ciaa/Ponchos/Osciloscopio/doc/PonchoOsciloscopio_CESE_NicolasDassieuBlanchet.odt

Curso de Diseño de PCBs - CESE

Hoja de presentación de proyecto

Nombre corto del proyecto:

Poncho Osciloscopio para la EDU-CIAA

Autor:

Nicolás Dassieu Blanchet

Licencia:

BSD

Repositorio de trabajo:

https://github.com/brengi/Ponchos.git

Rama de trabajo:

ponchoOsciloscopio

Descripción:

Este circuito implementa un poncho para la EDU-CIAA que le agrega la posibilidad de adquirir un canal de osciloscopio, con escala seleccionable, opción acoplamiento en AC y DC y con cierto nivel de protección sobre las entradas analogicas de la EDU-CIAA.

Requisitos del profesor:

Colocar los requisitos acordados con el profesor. Por ejemplo funciones mínimas, número de capas, tipo de fabricación, tipo de componentes y tecnología de montaje, circuitos de referencia charlados en clase, etc.

Requisitos comunes a todos:

- Utilizar Kicad 4.0.x.
- Consolidar toda la documentación en forma organizada dentro del directorio de proyecto de KiCad.
- Aplicar una licencia o aclarar el Copyright.
- Considerar en cada caso, los aspectos vistos referente a documentación.
- Realizar diseño jerárquico salvo en circuitos muy pequeños.
- Siempre que sea posible, considerar para los diseños componentes que se consigan en el mercado local.
- Se utilizará como proveedor de referencia a Mayer.
- Indicar que tipo/calidad de placa se considera para el diseño, intentando siempre que sea posible, seleccionar la de menor costo.
- Componentes through hole o SMD??? Si se pueden conseguir aca SMD sino Trough Hole
- Dos Layers??? 2
- Dispay??? Serie I2C o SPI
- Boton selección de escala??? Si por serigrafia que diga escala.
- Tamaño Vias, minimas pistas??? Ver especificaiones Mayer

Tareas y Alcance:

Indicar hasta donde se pretende llegar con el diseño y que tareas involucra. Por ejemplo:

- Búsqueda de esquemáticos de referencia. (Obligatorio)
- Adaptaciones de esquemático.
- Ingreso de esquemático a Kicad. (Obligatorio)
- Revisión del esquemático por un tercero. (Obligatorio)
- Cálculo de presupuesto y proveedores de componentes. (Obligatorio)
- Selección de footprints. (Obligatorio)
- Ubicación de componentes.
- Ruteo.
- Generación de Gerbers. (Depende lo acordado)
- Fabricación de prototipo. (Depende lo acordado)
- Validación funcional. (Depende lo acordado)

Enlaces:

Enlace original del que parte la idea de realizar el osciloscopio:

https://github.com/marvin-sinister/small-scope-electronics

Enlaces con circuitos más completos

http://tomeko.net/miniscope_v2b/

http://www.osciprime.com/index.php?p=source

Imágenes:

Colocar imágenes ilustrativas, por ejemplo diseño o estado actual, producto similar o a copiar, etc.
