ciaa/Ponchos/Expansor_puertos/Docs/Revisiones/Revisiones(DB).odt

Segunda Revisión (Revisor: Diego Brengi)

| Orlante Mariano
| mariano.orlante@gmail.com
| Expansor puertos
| https://marianoo2001@gitlab.com/marianoo2001/EduCiaaPE.git
| Segunda 25/7/17
Docente | Diego Brengi
Archivo hoja de proyecto en /doc | OK
Archivos de revisiones en /doc | OK
Revisor designado | OK
Bibliotecas | OK
Rótulo | OK
Jerarquía | OK
Campos KiCost | OK
Prolijidad conexiones | OK
Referencias de tensión | OK
Comentarios
ERC | OK
Configuración bibliotecas huellas | ok
Notas en PCB: Grila pos, ruteo. Pista min, Vía min, aguj. min, capas, terminación superficial. | OK
Rótulo | OK
Encapsulados | OK
Borde del PCB | OK
Ancho de pistas | OK
Tamaño de vía | OK
DRC | OK
Ruteo | Prolijo
| Bien aprovechadas las simetrías de los buses.
Fiduciales | OK
Placement | Muy bien
Serigrafía | Se podrían poner textos adicionales que ayuden a identificar los textos de las borneras, por ejemplo J3.1 J3.2 y así.
Textos en cobre o en serigrafía, logos | Sería bueno agregarle INDUSTRIA ARGENTINA en el cobre.
Dimensiones | OK
Fijación | OK
Belleza/Alineación | OK
Vista 3D | OK
Areas de cobre | Bien. Se podrían delimitar las áreas por fuera del borde para que no se superpongan al borde y entre sí. Es solamente una cuestión visual y de facilidad para el diseñador y el programa de CAD. Ver como ejemplo https://raw.githubusercontent.com/OLIMEX/OLINUXINO/master/HARDWARE/A64-OLinuXino/A64-OLinuXino_Rev_C/A64-OlinuXino_Rev_C.kicad_pcb Y habilitar la visualización de todas las capas para ilustrar el concepto de zonas de relleno por fuera del PCB.

Acciones Correctivas:

| Acción Correctiva
Serigrafía | - Se agregaron textos identificatorios de las borneras. Ademas de las respectivas J1, J2, J3, etc., se identificaron las entradas (INxx) y las salidas (OUTxx) en la capa F. Silk.
Textos en cobre o en serigrafía, logos | - Se agregó en la capa Bottom la leyenda INDUSTRIA ARGENTINA.
Areas de cobre | Se extendieron las areas de cobre por fuera del borde de la placa.

Primera Revision (Revisor: Diego Brengi)

NOMBRE | | Orlante Mariano
EMAIL | | mariano.orlante@gmail.com
PROYECTO | | Expansor puertos
REPO | | https://marianoo2001@gitlab.com/marianoo2001/EduCiaaPE.git
CORRECCION (Fecha) | | Primera 30/06/17
Curso CESE - PCB | Docente | Diego Brengi
Documentación | Archivo hoja de proyecto en /doc | FALTA
| Archivos de revisiones en /doc | Colocar esta revisión en el directorio doc.
| Revisor designado | OK
Esquematico | Bibliotecas | OK
| Rótulo | OK
| Jerarquía | OK
| Campos KiCost | OK
| Prolijidad conexiones | Estan muy prolijas. En las hojas de entrada y salidas se podría quitar las etiquetas locales, ya que unos pocos cruces no molestan a la claridad del circuito. Esta muy bien de todas formas como fue resuelto.
| Referencias | OK
| Comentarios
| ERC | OK
Asociación | Configuración bibliotecas huellas | ok
PCB | Notas en PCB: Grila pos, ruteo. Pista min, Vía min, aguj. min, capas, terminación superficial. | Faltan
| Rótulo | Debe ser similar al del esquemático.
| Encapsulados | OK
| Borde del PCB | OK
| Ancho de pistas
| DRC
| Ruteo
| Fiduciales | Si hay espacio se recomiendan por lo menos 3 fiduciales.
| Placement | Se recomienda trabajar un poco más la ubicación antes de rutear, para evitarse complicaciones luego. Ver la guía para posicionamiento. Se nota que ya hay trabajo hecho.
| Serigrafía
| Textos en cobre o en serigrafía, logos
| Dimensiones
| Fijación
| Belleza/Alineación
| Vista 3D | OK
| Areas de cobre

Acciones Correctivas:

| | Acción Correctiva
Documentación | Archivo hoja de proyecto en /doc | - Se agregó el archivo "ProyectoPCB_CESE_ORLANTE.odt" a la carpeta /Docs del proyecto.
| Archivos de revisiones en /doc | - Se agregó el documento "Revisiones(DB).odt" a la carpeta /Docs del proyecto.
Esquematico | Prolijidad conexiones | En el esquemático de entradas digitales: - Se quitaron las etiquetas locales CLK_INH, S//L, CLK reemplazandolas por cables. En el esquemático de salidas digitales: - Se quitó la etiqueta /CS en el esquematico de salidas digitales. - Se decidió dejar las etiquetas OUTxx y la COMUN porque aportan claridad al esquematico, identificando las borneras.
PCB | Notas en PCB: Grila pos, ruteo. Pista min, Vía min, aguj. min, capas, terminación superficial. | Se agregó esto en el PCB.
| Rótulo | Se cargó el rótulo similar al esquemático.
| Fiduciales | Se agregó un tercer fiducial.
| Placement | Se itero varias veces hasta obtener un posicionamiento que requeria poco uso de vias.
