ciaa/Ponchos/WifiBT_CESE_ESPWROOM32/doc/Primera_Revision_Esquematico.pdf

### Primera Revisión

Revisor: Diego Brengi

Fecha: 30/06/2017

NOMBRE | | Coccé Gastón
EMAIL | | gastoncocce@hotmail.com
PROYECTO | | Poncho Wifi y Bluetooth
REPO | | https://github.com/gcocce/poncho_EDU-CIAA_wifi_blth
CORRECCION
(Fecha)
Curso CESE - PCB | Docente | Diego Brengi

Documentación

Archivo hoja de proyecto en

Archivos de revisiones en

/doc | FALTA
/doc | Colocar esta revisión en el direcotrio doc.
Revisor
| QUITAR TODAS una vez que se han agregado todos los componentes.
designado | Debe figurar en el rótulo.
Esquematico | Bibliotecas
Rótulo | Mencionar la asignatura. Mencionar al revisor.

Jerarquía
Campos
KiCost | OK.

Prolijidad
conexiones

Mejorar. Por ejemplo en el extremo de R6 falta una unión y la conexión esta sobre el pin del componente SW2. La GND de D2/D3 tiene una unión sobre el mismo pin de conexión.

Referencias | OK.
Comentarios | El power flag colocarlo en el conector.
ERC | OK

Asociación

Configuración
bibliotecas
huellas

Quitar la biblioteca Buttons. Dejar solo la que esta dentro del proyecto, que debería contener todos los footpints utilizados. Ver la opción de Archivar footprints en el pcbnew.

PCB

Notas en PCB:
Grila pos,
ruteo. Pista Falta

min, Vía min,
aguj. min,
capas,
terminación
superficial.
Rótulo | Falta. Debe estar similar al de esquemático.

Encapsulados

Los resistores1206 se usan cada vez menos y puede costar conseguirlos. Los 0402 son demasiado pequeños para manejo manual. Se recomienda unificar en 0805 que se usan mucho y se pueden soldar manualmente de ser
necesario. https://es.wikipedia.org/wiki/Tecnolog%C3%ADa_de_montaje_superficial. (https://es.wikipedia.org/wiki/Tecnolog%C3%ADa_de_montaje_superficial) Esto requerirá cambiar los códigos en el esquemático.

Borde del PCB
Ancho de
pistas

DRC

Ruteo

Fiduciales

Placement

Serigrafía

Textos en
cobre o en
serigrafía,
logos

Dimensiones

Fijación
Belleza/Alinea
ción
Vista 3D | OK
Areas de
cobre
