ciaa/Ponchos/Osciloscopio/hdatos/Display info 2.pdf

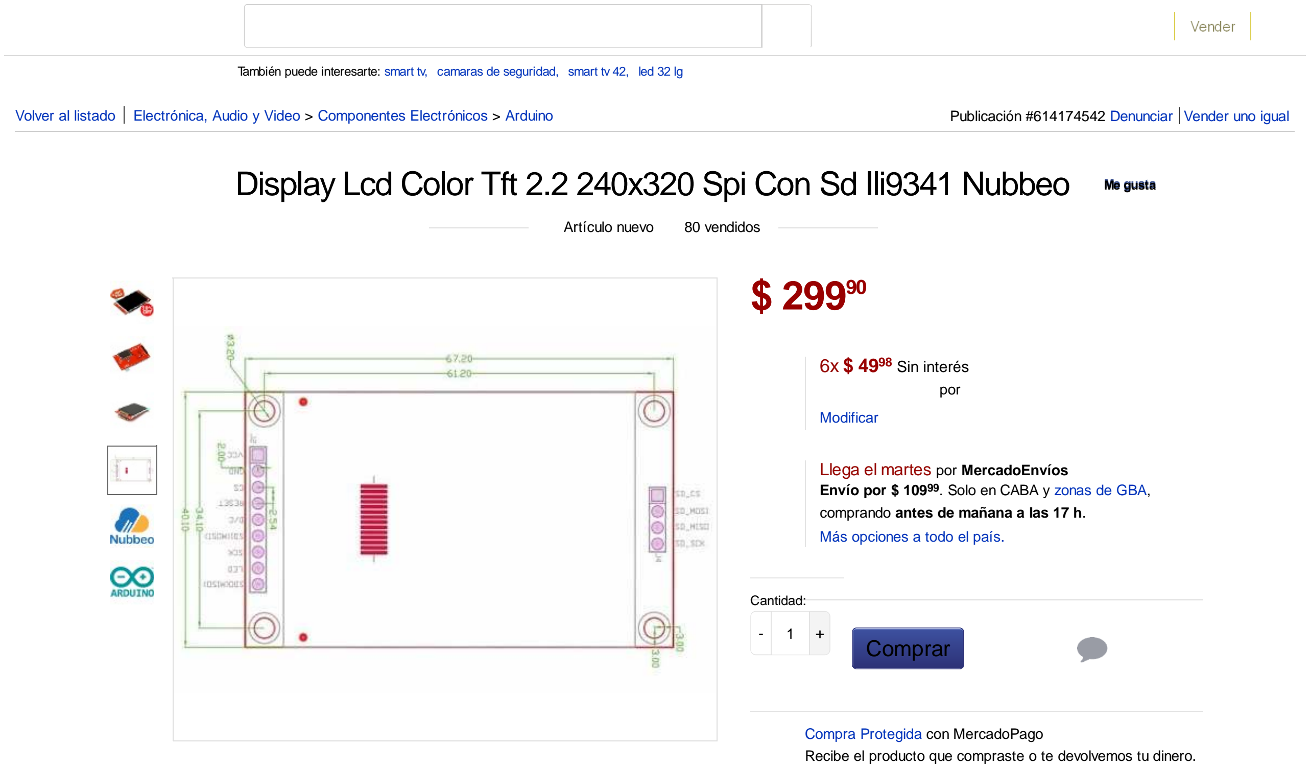
[picture p29: figure]
Cantidad:; Comprar; Compra Protegida con MercadoPago; Me gusta; Artículo nuevo; 80 vendidos; 6x $ 49⁹⁸ Sin interés; por; Modificar; Más opciones a todo el país.; Llega el martes por MercadoEnvíos; comprando antes de mañana a las 17 h.

También puede interesarte: smart tv, camaras de seguridad, smart tv 42, led 32 lg

# Display Lcd Color Tft 2.2 240x320 Spi Con Sd Ili9341 Nubbeo

Recibe el producto que compraste o te devolvemos tu dinero.

# Información sobre el vendedor

## Reputación

100% de sus compradores; lo recomiendan; 34789 ventas; concretadas; Excelente vendedor ¡Es uno de los mejores del sitio!; 3 AÑOS vendiendo en MercadoLibre; Este vendedor es MercadoLíder Platinum

Ver más datos de este vendedor

## Calificaciones 53 compradores lo recomendaron por este producto JMONF... - 08 de julio

MAIANUS201... - 22 de junio

PELIKAN... - 15 de junio

CLA... - 15 de junio

BELWA... - 11 de junio

Ver más calificaciones

# Garantía

Volver al listado | Electrónica, Audio y Video > Componentes Electrónicos > Arduino | Publicación #614174542 Denunciar | Vender uno igual

Envío por $ 109⁹⁹. Solo en CABA y zonas de GBA,

Ubicado en Villa Luro (Capital Federal)

- "Recomendado”
- "Excelente vendedor”
- "Todo perfecto. Recomendable.”
- "Si. Todo bien. Gracias!!!!!”
- "Excelente vendedor! Recomendable”

Tu compra en MercadoLibre, siempre protegida

Display Lcd Color Tft 2.2 240x320 Spi Con Sd Ili9341 Nubbeo - $ 299... http://articulo.mercadolibre.com.ar/MLA-614174542-display-lcd-color-...

1 of 6 | 10/07/2016 10:50 a.m.

## De compra

con MercadoPago

# Descripción de la publicación

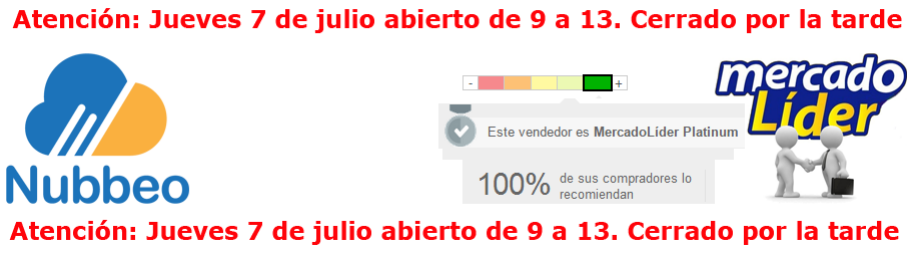
[picture p30: figure]

## Display LCD TFT de 240x320 pixels con interface SPI Incluye slot para memoria SD

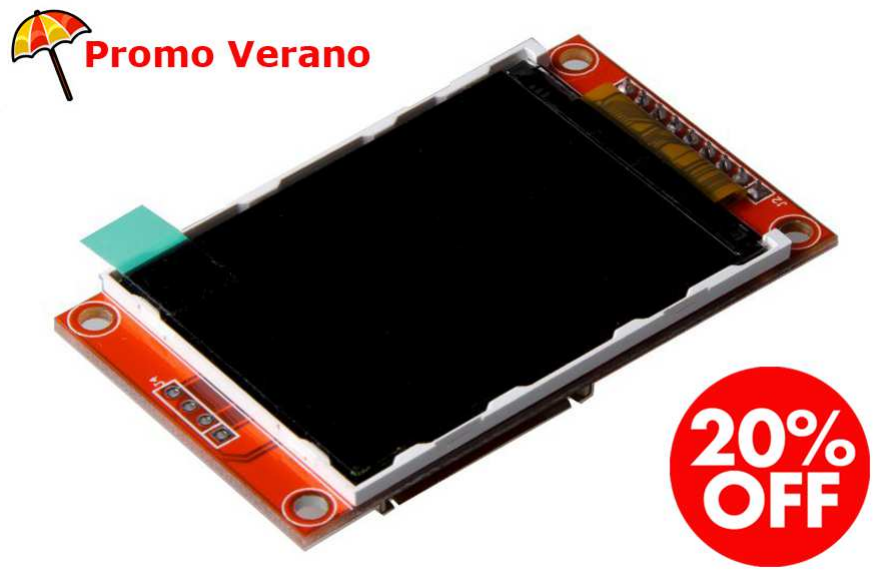
[picture p31: figure]

### Descripción General

Pantalla LCD TFT de 2.2 pulgadas con interface SPI. Excelente calidad de imagen con resolución QVGA (240 x 320 pixels). El controlador ILI9341 junto con la interface SPI (solo 4 pines) hacen que sea muy facil de usar. Adicionalmente dispone de un slot SD (independiente del LCD). Este articulo usa lógica de 3V3

## Características

### - Tamaño: 2,2 pulgadas - Alimentación: 5V - Lógica: 3V3

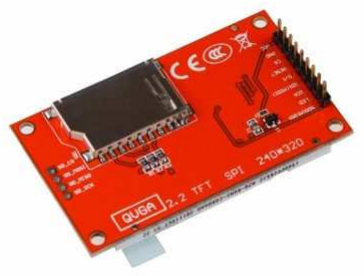
[picture p32: figure]

### - Matriz de puntos: QVGA 240 * 320 puntos - Interfaz de 4 hilos SPI - Profundidad de color: 262K/65K - Tamaño del módulo: 67 mm (longitud) * 40mm (ancho) * 4 mm (grosor)

### Compra Protegida con MercadoPago

Si surge algún problema o no recibes el producto tal como se describe en esta publicación, te devolvemos tu dinero.

Conoce más sobre Compra Protegida

### - Área activa: 47.5mm (longitud) x36.5mm (Ancho) - Driver IC: ILI9341

# Visita nuestro e-shop

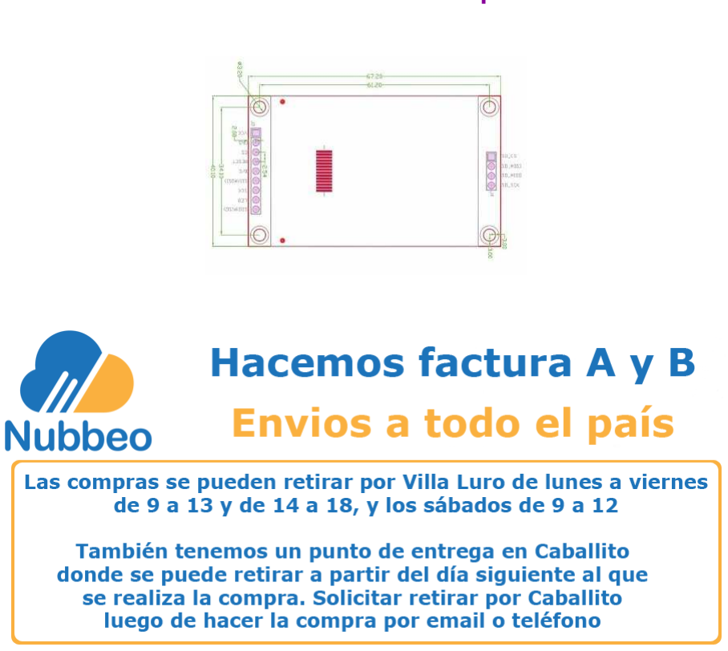
[picture p33: figure]

# Medios de pago

Formas de pago ofrecidas por el vendedor
