ciaa/Ponchos/Expansor_puertos/Docs/Notas de Ingenieria/Calculos y Estimaciones.pdf

Cálculos y estimaciones para las entradas digitales

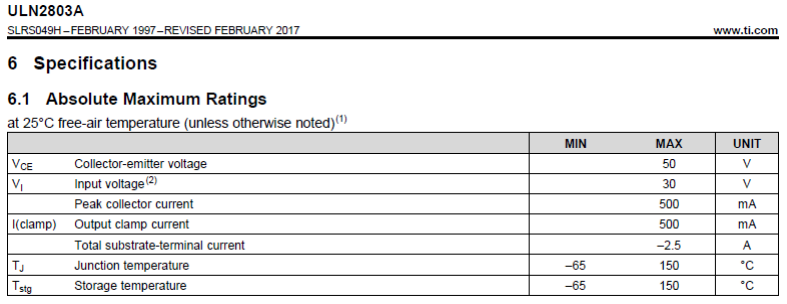
[picture p51: figure]

Según la hoja de datos del ULN2803 la máxima tensión de entrada es 30V.

Aplicando cierto margen de seguridad, se especifica para el producto como máximo una tensión de fuente de 28V DC.

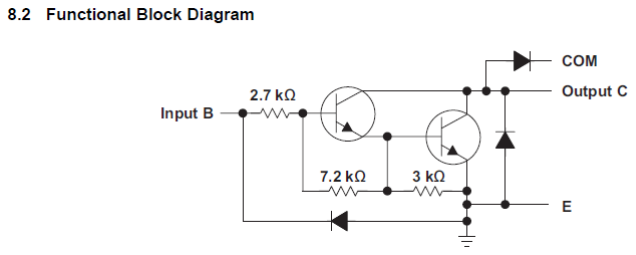
[picture p52: figure]

Ient(max) =

(28V−0.6V−0.6V)
2700Ω

→ Ient(max) ≅ 10mA

Ient(min) =

(3.5V−0.6V−0.6V)
2700Ω

→ Ient(max) ≅ 1mA

ESPECIFICACION ENTRADAS DIGITALES

Tipo de Entradas | NPN Sinking.
Rango de tensión admitida | 3.5 a 28 Volts DC (entrada activada).
Corriente que insume | 1 mA a 10 mA máximo.

Cálculos y estimaciones para las salidas digitales

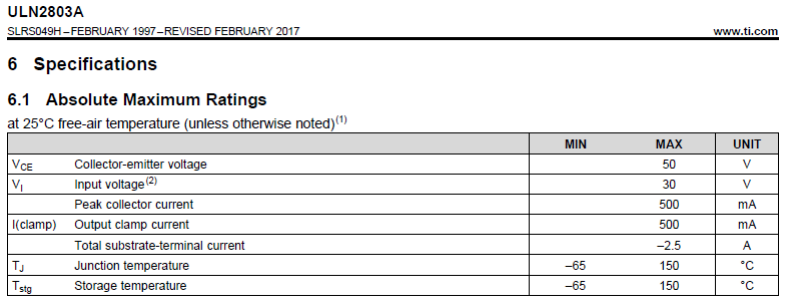
[picture p53: figure]

Según la hoja de datos del ULN2803 la máxima tensión colector-Emisor (VCE) soportada por los transistores es 50V.

Aplicando cierto margen de seguridad, se especifica para el producto como máximo una tensión de fuente externa de 45V DC.

Según la hoja de datos del ULN2803 la corriente de salida de pico máxima de un canal es 500mA. Por otro lado ESPECIFICA la “Total substrate-terminal current” = 2.5 A.

Si se activarán las 8 salidas a la vez, tendríamos:

Isalidaporcanal(max) = 2,5A/8 = 312mA

Aplicando cierto margen de seguridad, se especifica para el producto 150mA por cada salida.

ESPECIFICACION SALIDAS DIGITALES

Tipo de Salidas | NPN Sinking (colector abierto)
Tensión en la Carga | 3 a 45 Volts DC máximo
Corriente drenada | 150 mA máximo por cada salida.
