ciaa/Ponchos/Pico_WiFi/CONSIDERACIONES_INICIALES/AMADORES/Recomendaciones_assisi.pdf

# Entrega de Materiales

Recomendaciones para la entrega de materiales

Sr. Visitante, a continuación lo invitamos a conocer las necesidades de información y las recomendaciones más importantes a tener en cuenta para la conservación y entrega de los materiales.

Una vez recepcionados los mismos, podremos dar inicio al proceso interno de control, y validamiento del kit enviado para la planificación de la Orden de Trabajo.

Al planificar un lote de producción, sugerimos tener en cuenta la cantidad de placas del panelizado, ya que la cantidad del lote debería ser múltiplo de ese número.

Es imprescindible el envío de toda la información necesaria para el correcto armado del producto, la muestra física (en caso de no ser enviada anteriormente para su análisis o presupuesto), debe ser entregada acompañando a los materiales. Se recomienda enviar la demás información en formato digital vía E-mail a nuestra empresa.

- Una muestra de placa a producir armada, actualizada, preferiblemente probada y funcionando.
- Una orden de compra o producción, que indique el nombre de placa a producir, la cantidad y los datos de contacto del cliente.
Home | La Empresa | Servicios | Equipamiento
Assisi S.R.L. Armado y Soldado industrial de pl... | http://www.assisi.com.ar/presupuestos/entrega-...
1 de 5 | 11/11/16 14:01

Assisi S.R.L.
Independencia 4281 C.A.B.A. - Tel: 011-4958-5656 / 011-4983-2510 / 011-3750-1389 E-mail: info@assisi.com.ar - www.assisi.com.ar o acceda a nuestro formulario de contacto haciendo
