ciaa/Ponchos/modelos/Muestrario/doc/LEEME.txt

Autor: Diego Javier Brengi (INTI/UNLaM).

Proyecto simple para colocar todos los símbolos y huellas y visualizarlas
de un solo vistazo.
