ciaa/Ponchos/Audio_amp_mic/doc/AmpAudio.jpg

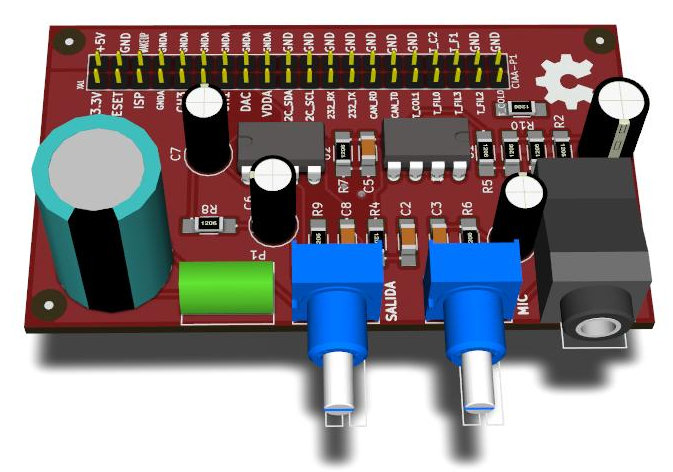
Audio_amp_mic/doc/AmpAudio.jpg
