ciaa/Ponchos/Audio_amp_mic/doc/Poncho EDU CIAA Amp Audio2.jpg

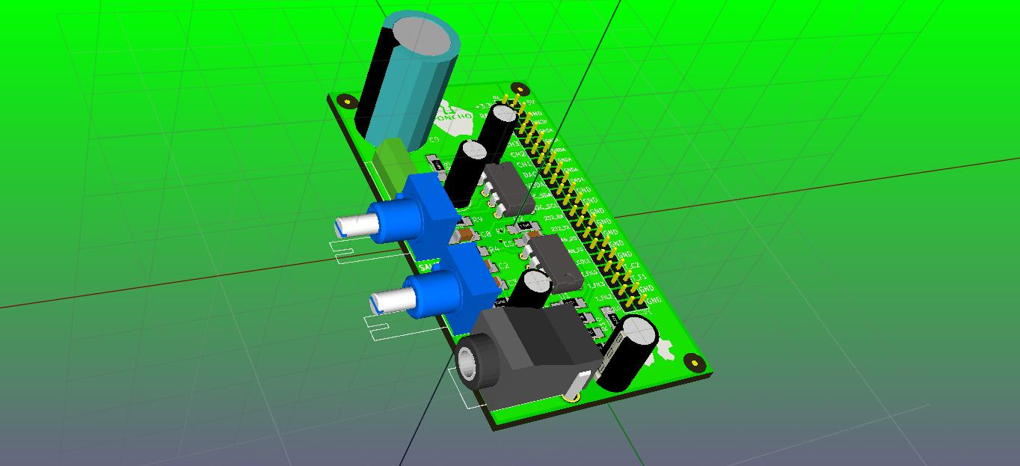
Audio_amp_mic/doc/Poncho EDU CIAA Amp Audio2.jpg
