ciaa/Ponchos/Audio_amp_mic/doc/Poncho EDU CIAA Amp Audio.jpg

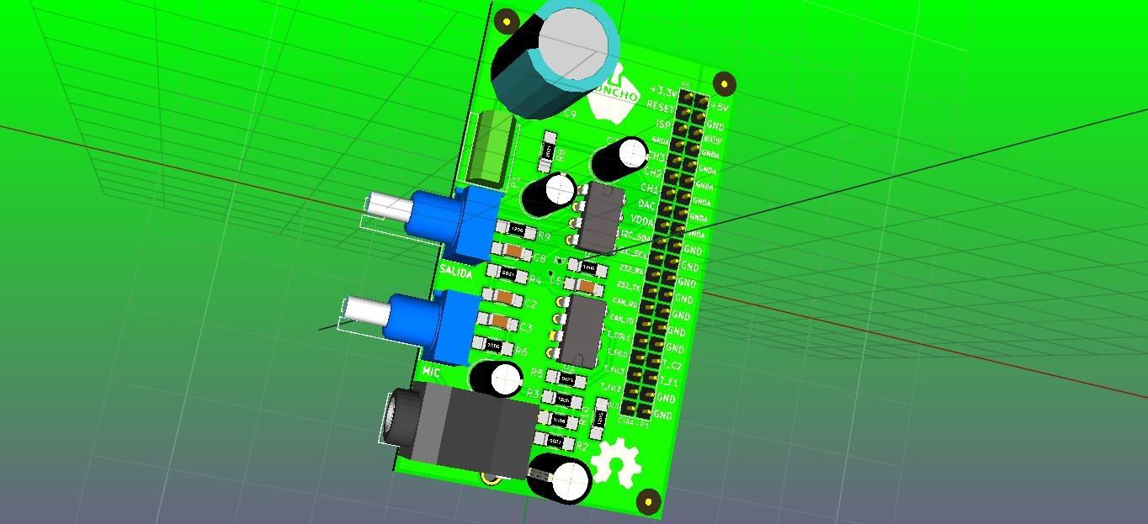
Audio_amp_mic/doc/Poncho EDU CIAA Amp Audio.jpg
