ciaa/Ponchos/Celda_de_carga/doc/poncho_celda.jpg

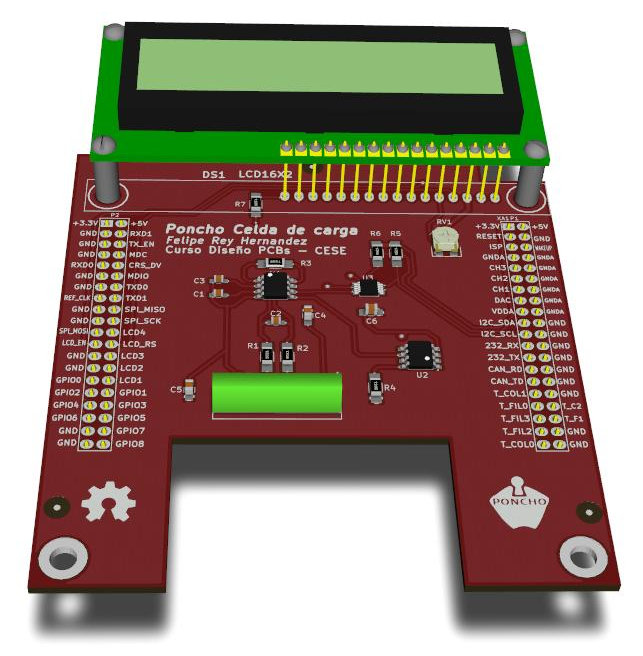
Celda_de_carga/doc/poncho_celda.jpg
