ciaa/Ponchos/Control_Temperatura/Docs/PonchoTermocuplayRele.jpg

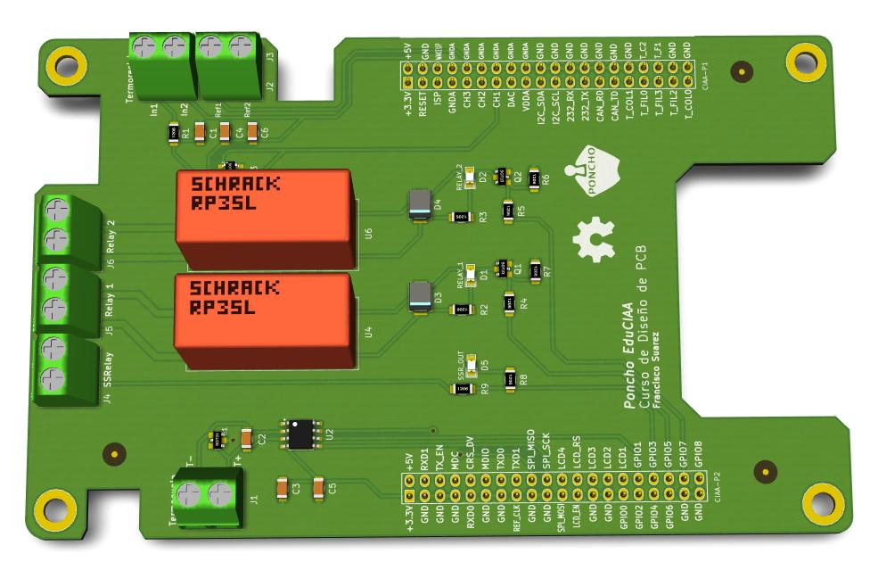
Control_Temperatura/Docs/PonchoTermocuplayRele.jpg
