ciaa/Ponchos/Control_Temperatura/Docs/tempRelayPoncho_BOTTOM.png

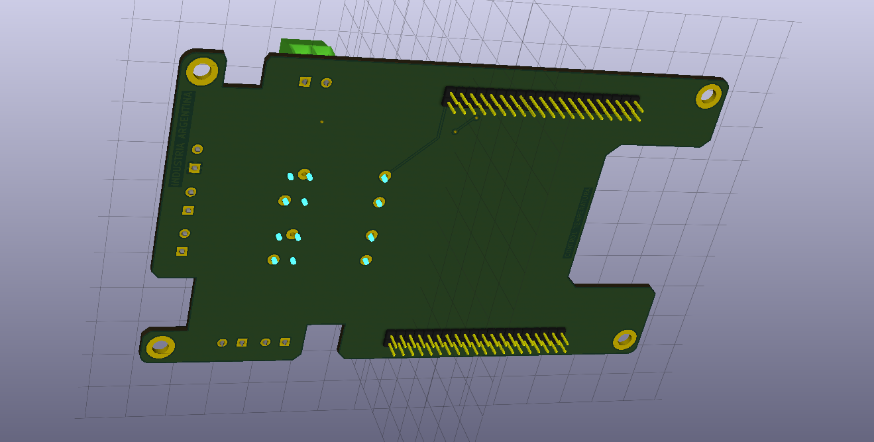
Control_Temperatura/Docs/tempRelayPoncho_BOTTOM.png
