ciaa/Ponchos/Control_Temperatura/Docs/tempRelayPoncho_TOP.png

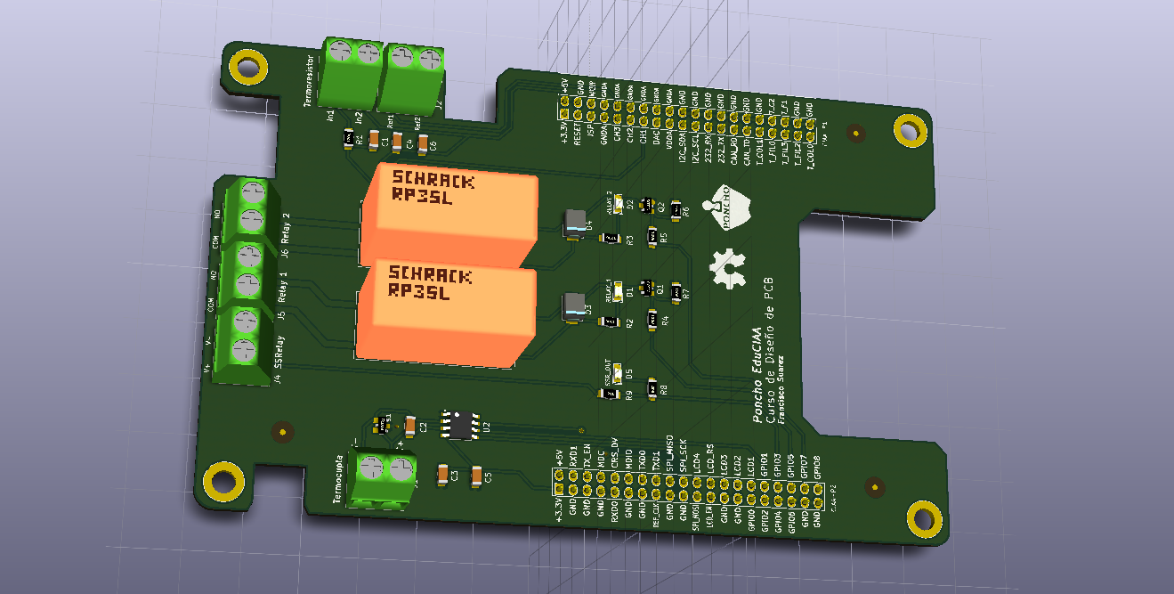
Control_Temperatura/Docs/tempRelayPoncho_TOP.png
