ciaa/Ponchos/Detector_de_caidas/doc/fall_detector.jpg

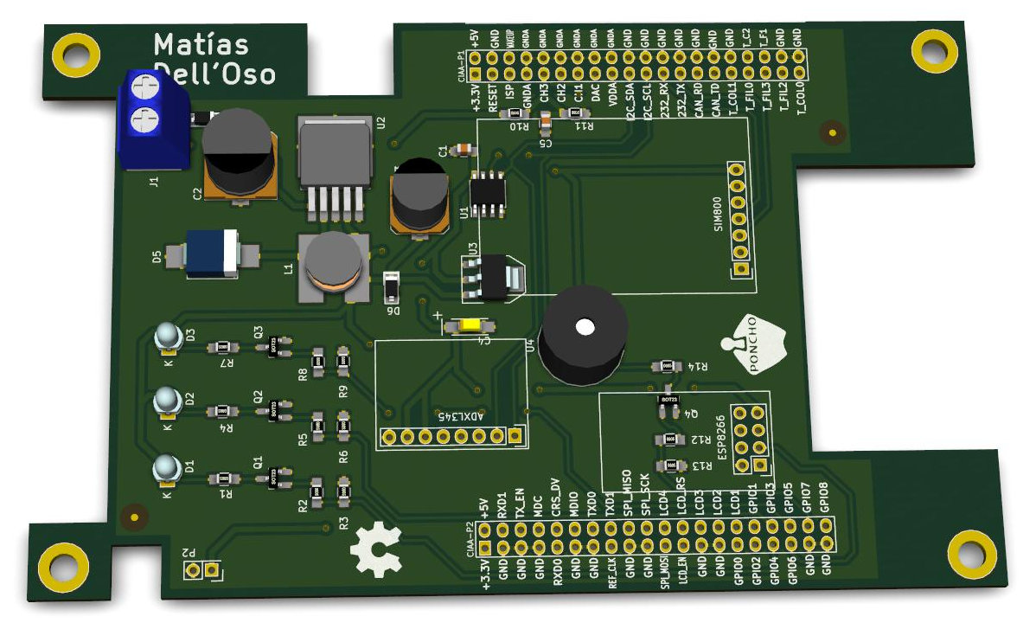
Detector_de_caidas/doc/fall_detector.jpg
