ciaa/Ponchos/doc/collage/collage_800x.jpg

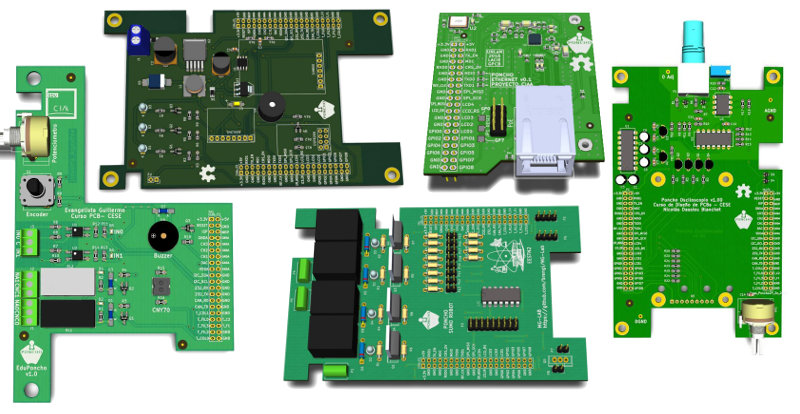
doc/collage/collage_800x.jpg
