ciaa/Ponchos/doc/collage/collageh1000x.jpg

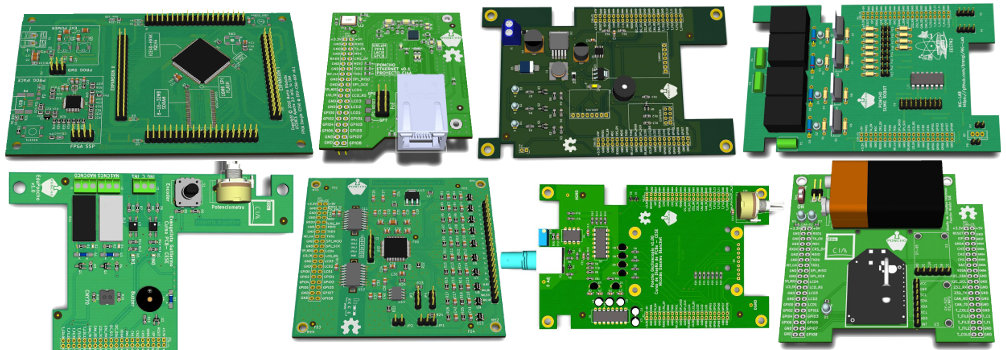
doc/collage/collageh1000x.jpg
