ciaa/Ponchos/ECG/doc/ecg.jpg

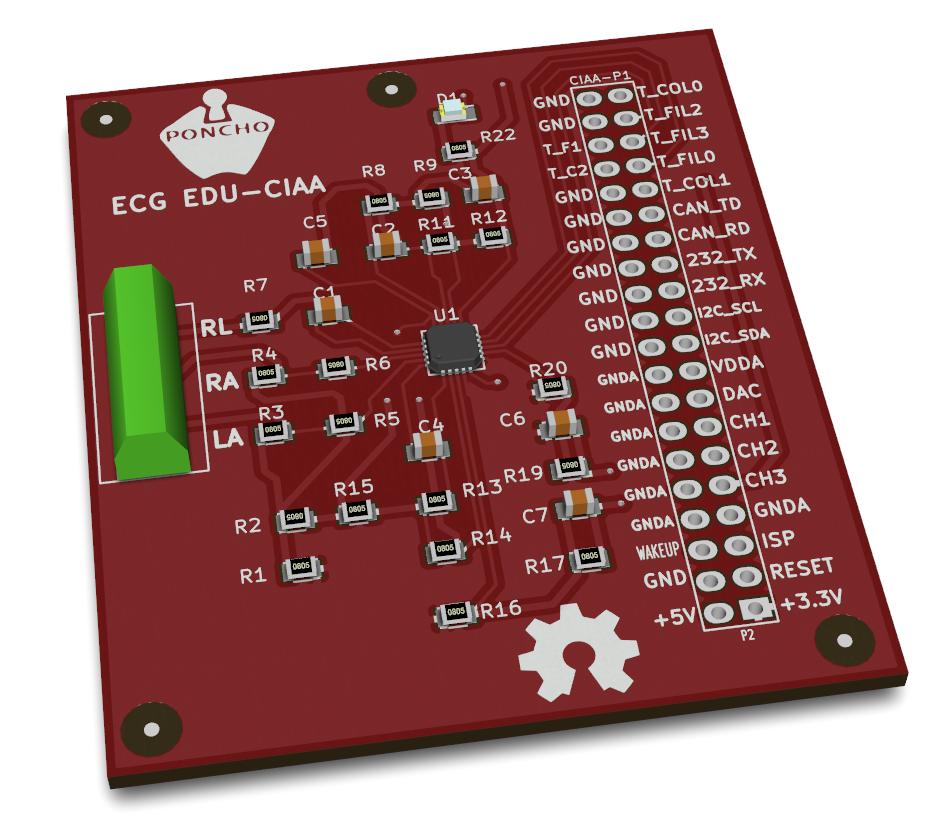
ECG/doc/ecg.jpg
