ciaa/Ponchos/ECG/ECG_CIAA.jpg

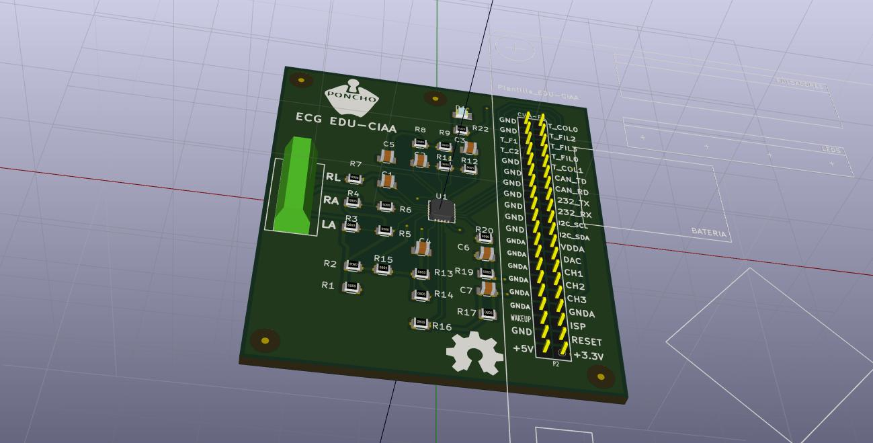
ECG/ECG_CIAA.jpg
