ciaa/Ponchos/Educativo1/doc/ponchoeducativo.jpg

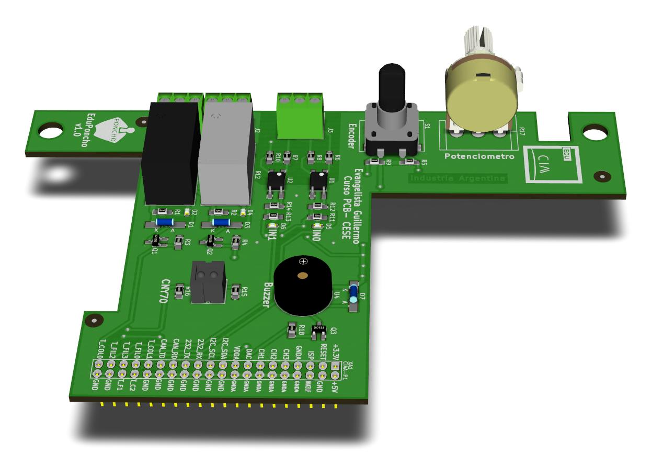
Educativo1/doc/ponchoeducativo.jpg
