ciaa/Ponchos/Educativo1/EduPoncho.png

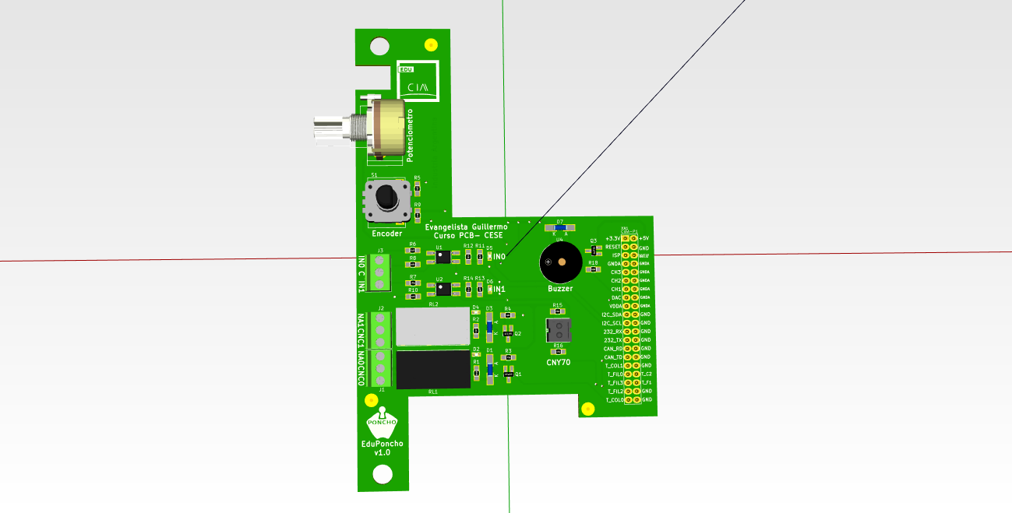
Educativo1/EduPoncho.png
