ciaa/Ponchos/Educativo_UNSJ/doc/EducativoUNSJ.jpg

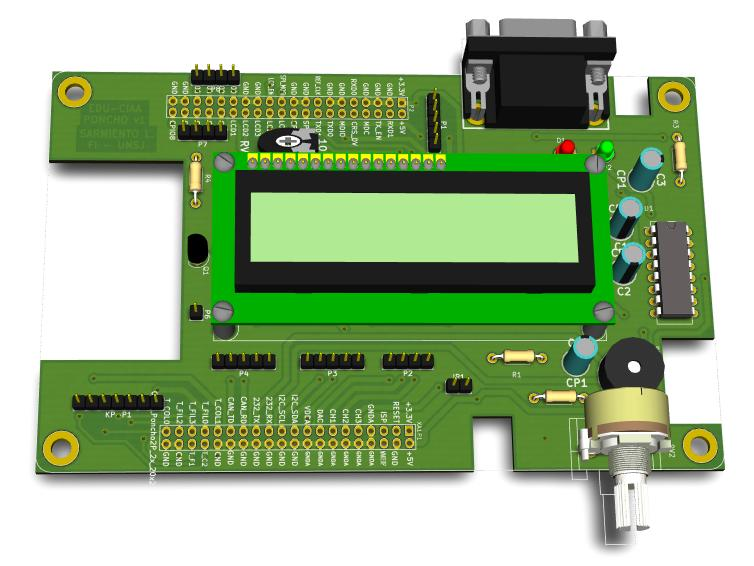
Educativo_UNSJ/doc/EducativoUNSJ.jpg
