ciaa/Ponchos/Educativo_UNSJ/doc/foto_b.jpg

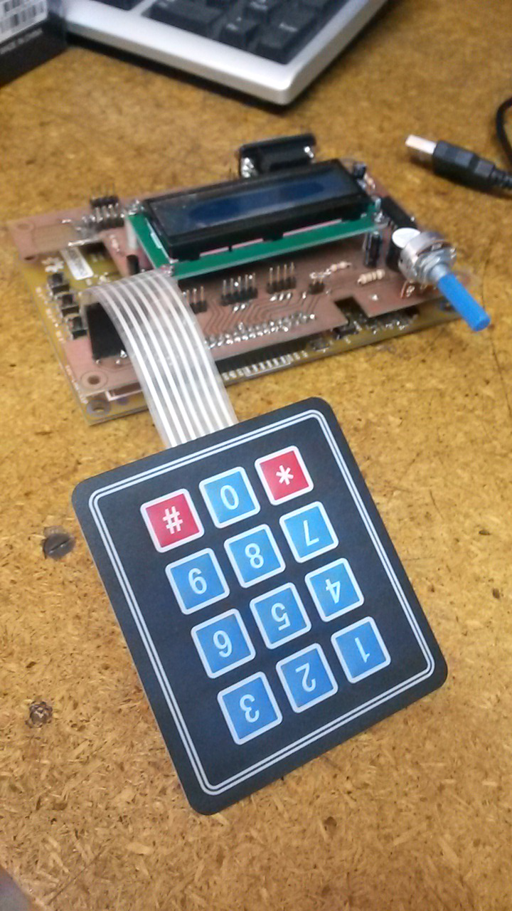
Educativo_UNSJ/doc/foto_b.jpg
