ciaa/Ponchos/ethernet_LAN8720A_v2/doc/CalculoDIF.png

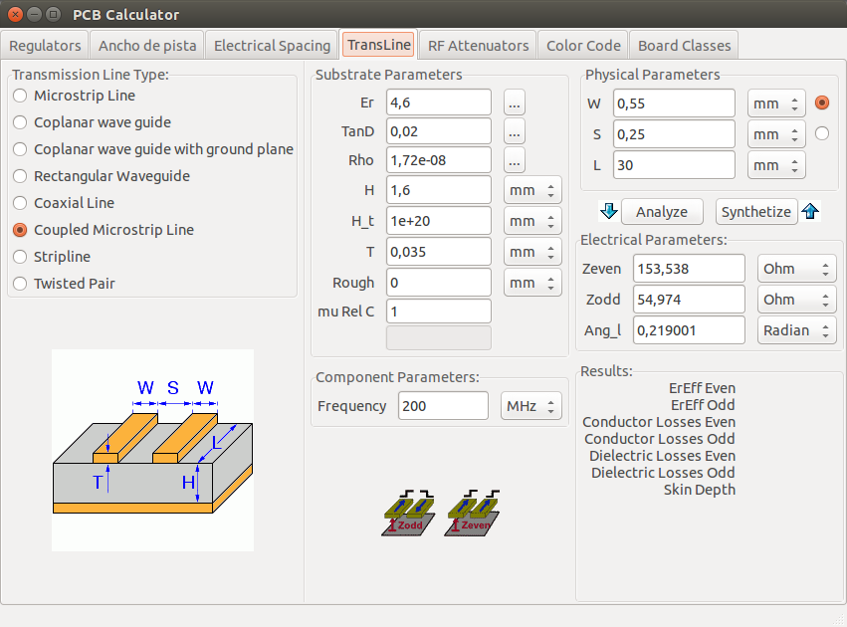
ethernet_LAN8720A_v2/doc/CalculoDIF.png
