ciaa/Ponchos/ethernet_LAN8720A_v2/doc/PonchoEthernet.jpg

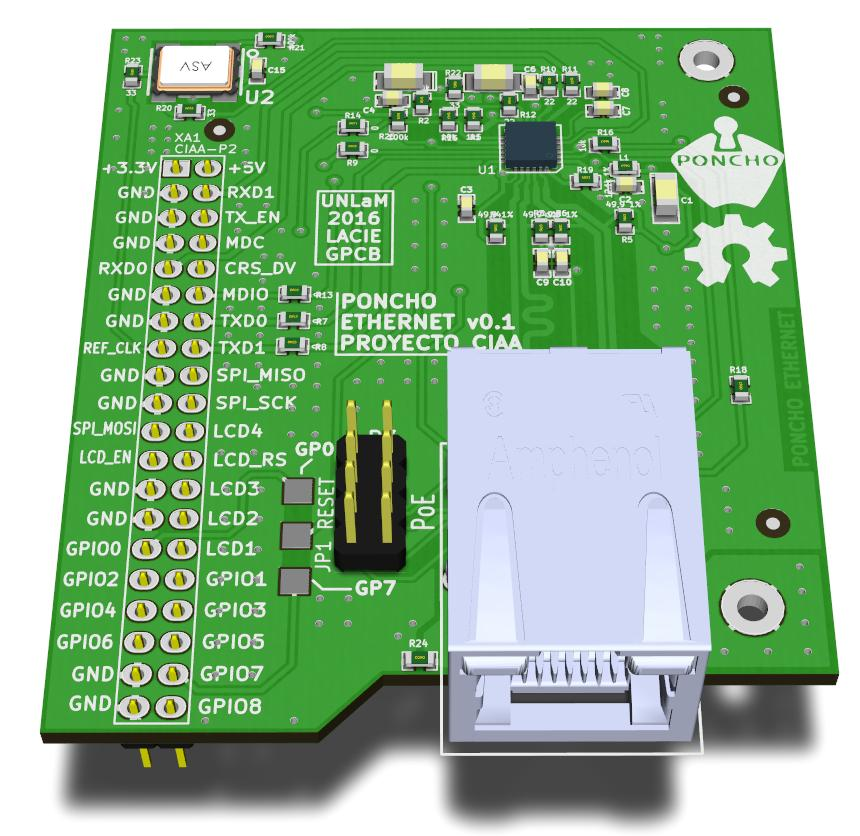
ethernet_LAN8720A_v2/doc/PonchoEthernet.jpg
