ciaa/Ponchos/Expansor_puertos/Docs/PonchoExpansorPuertos.jpg

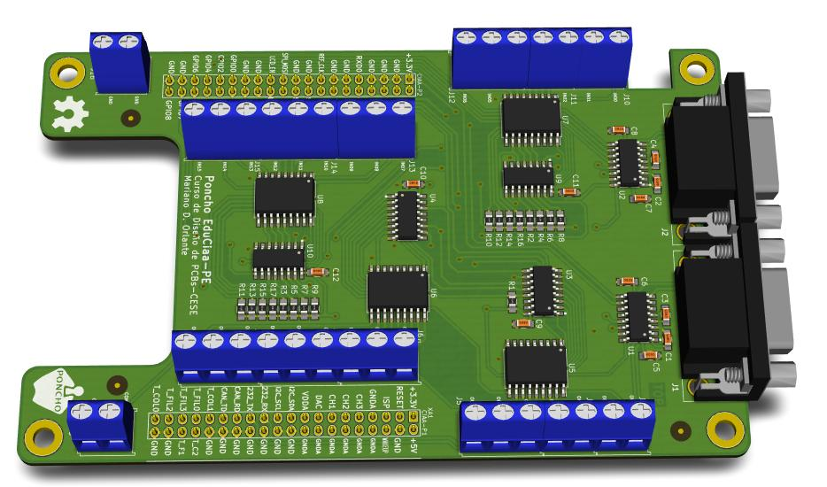
Expansor_puertos/Docs/PonchoExpansorPuertos.jpg
