ciaa/Ponchos/Expansor_puertos/Docs/Vistas 3D/EduCiaa_PE (3D Bottom View).png

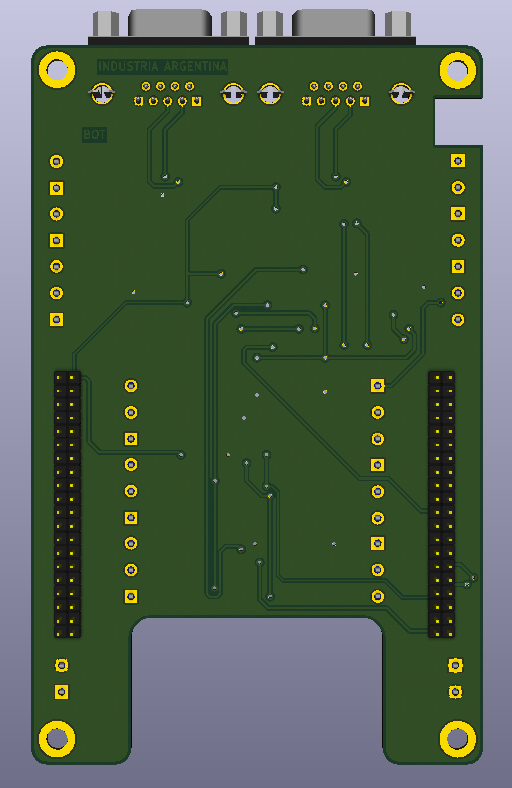
Expansor_puertos/Docs/Vistas 3D/EduCiaa_PE (3D Bottom View).png
