ciaa/Ponchos/expansores_ciaa/3x2.PNG

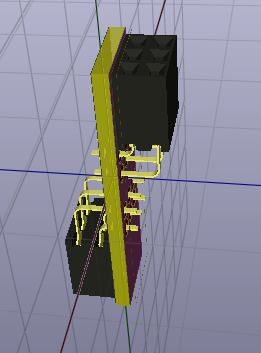
expansores_ciaa/3x2.PNG
