ciaa/Ponchos/expansores_ciaa/3x3_pcb.PNG

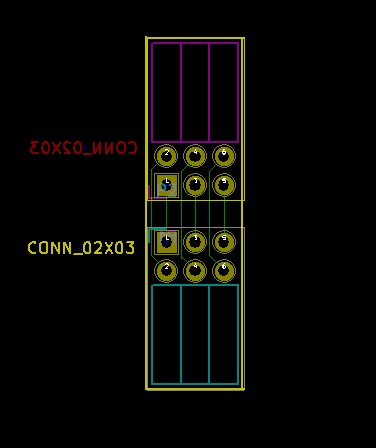
expansores_ciaa/3x3_pcb.PNG
