ciaa/Ponchos/expansores_ciaa/4x2.PNG

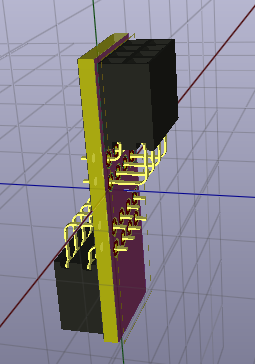
expansores_ciaa/4x2.PNG
