ciaa/Ponchos/expansores_ciaa/10x2.PNG

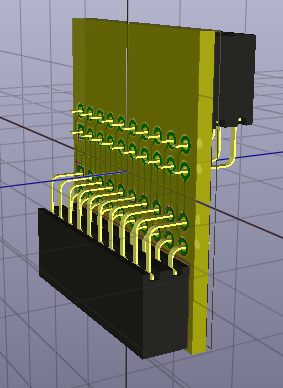
expansores_ciaa/10x2.PNG
