ciaa/Ponchos/expansores_ciaa/10x2_2.PNG

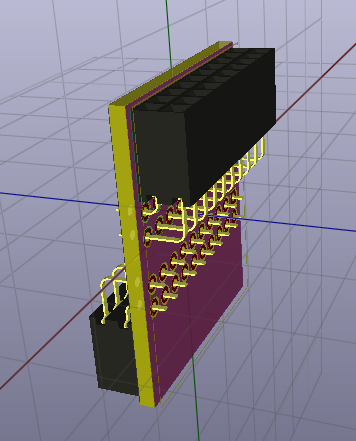
expansores_ciaa/10x2_2.PNG
