ciaa/Ponchos/expansores_ciaa/10x2_pcb.PNG

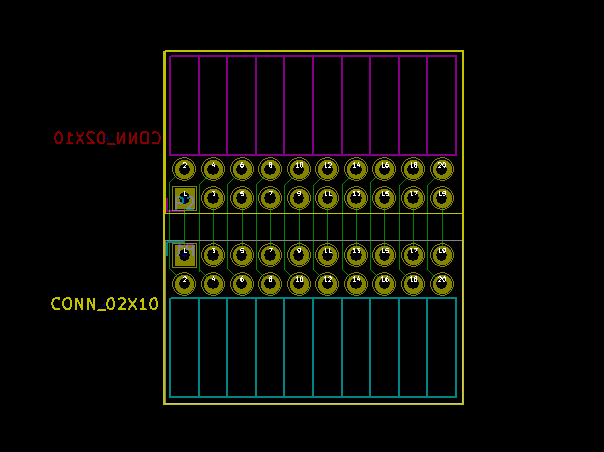
expansores_ciaa/10x2_pcb.PNG
