ciaa/Ponchos/expansores_ciaa/expansores.jpg

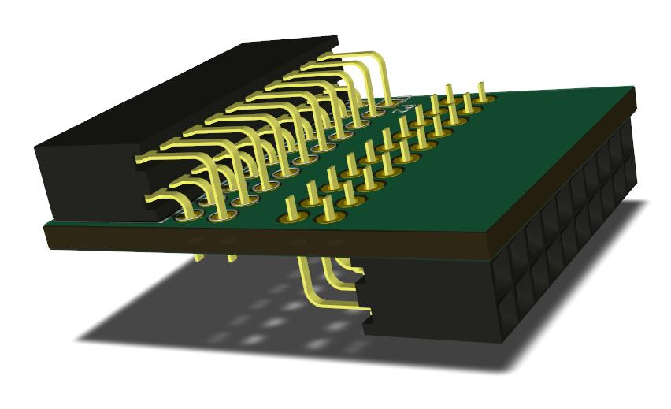
expansores_ciaa/expansores.jpg
