ciaa/Ponchos/GPS_L86/Img/GPSL86.jpg

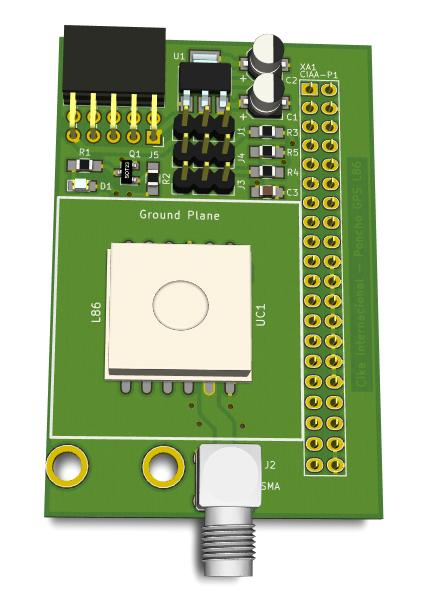
GPS_L86/Img/GPSL86.jpg
