ciaa/Ponchos/GPS_L86/Img/Poncho_L86_3.png

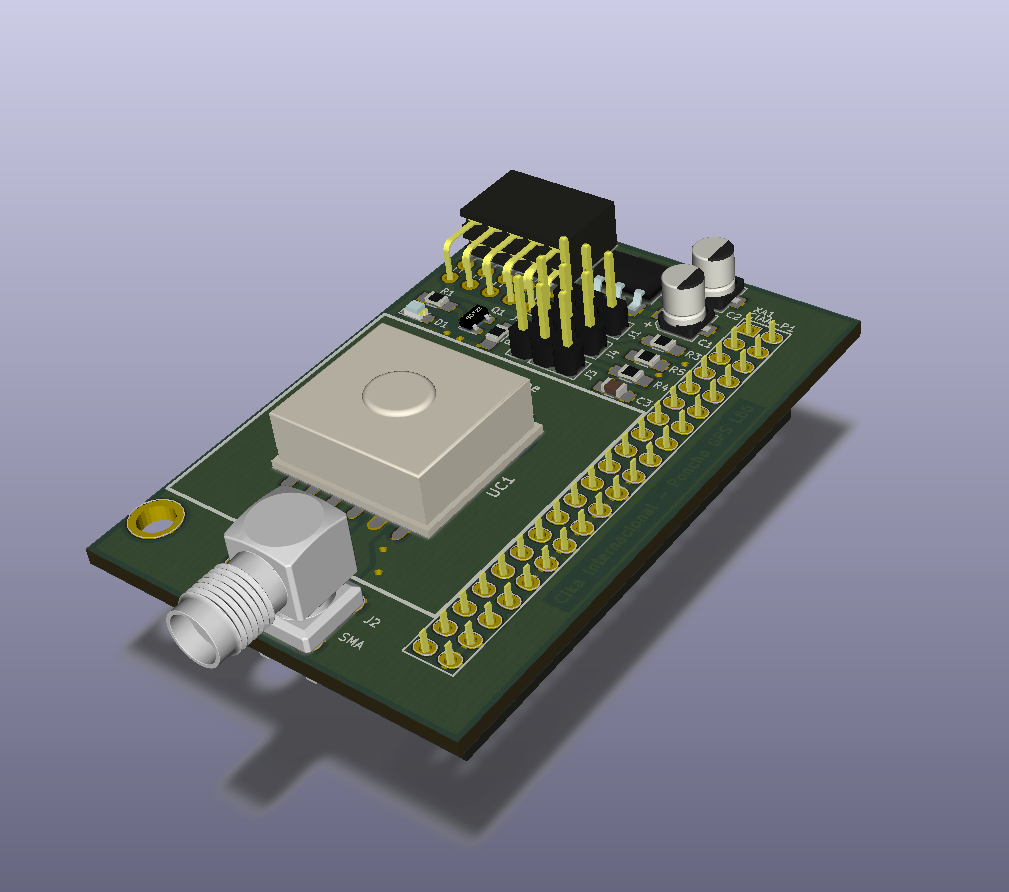
GPS_L86/Img/Poncho_L86_3.png
