ciaa/Ponchos/IoT/doc/Poncho_IoT.jpg

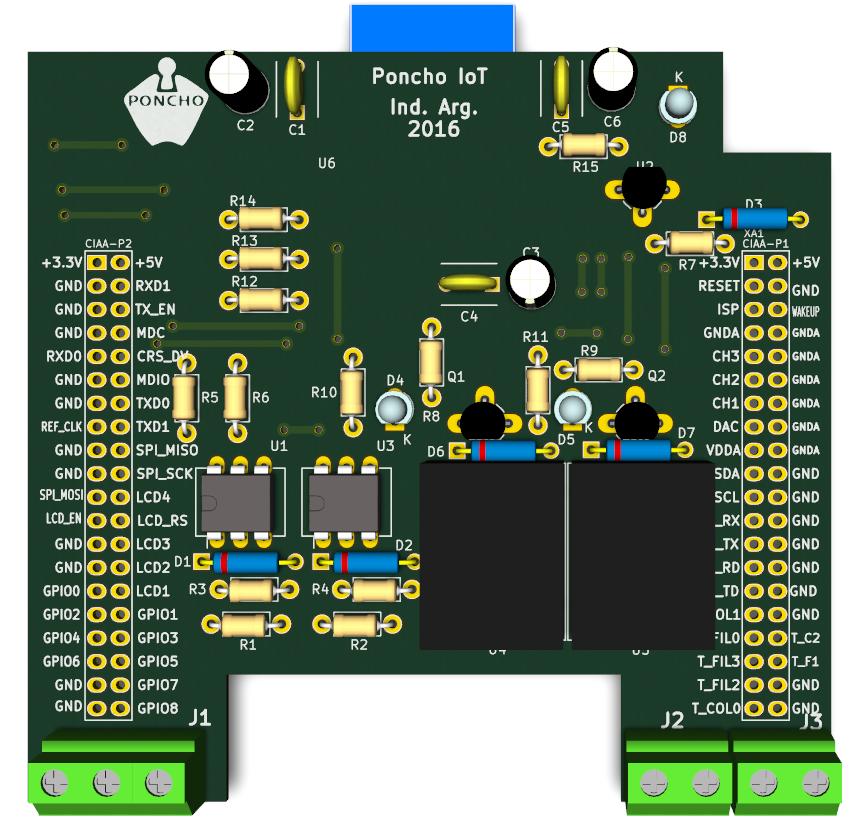
IoT/doc/Poncho_IoT.jpg
