ciaa/Ponchos/IoT/doc/ponchoeduciaaiot.png

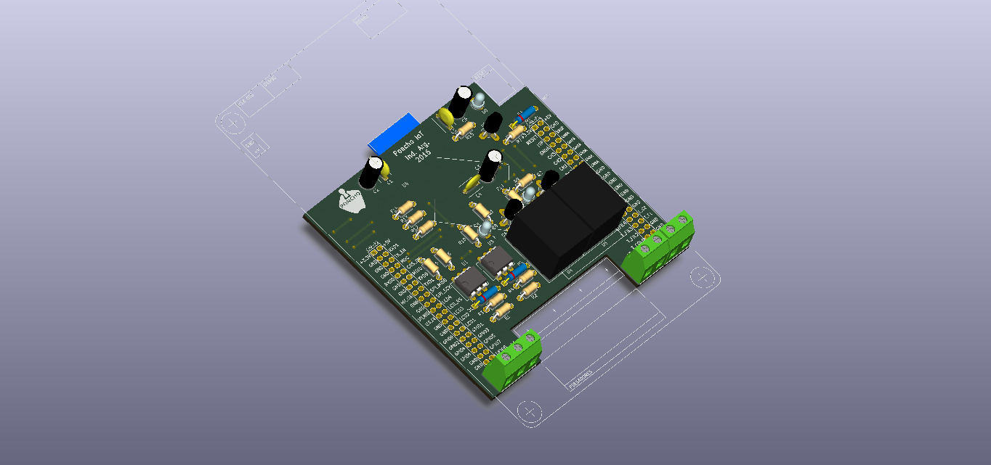
IoT/doc/ponchoeduciaaiot.png
