ciaa/Ponchos/Joystick/doc/Poncho_Joystick_dorso.png

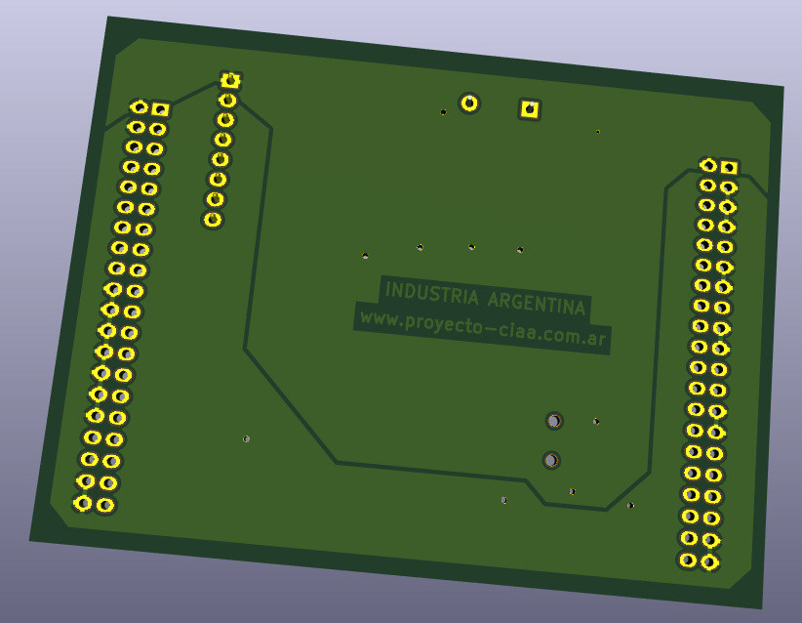
Joystick/doc/Poncho_Joystick_dorso.png
