ciaa/Ponchos/Joystick/doc/Poncho_Joystick_frente.png

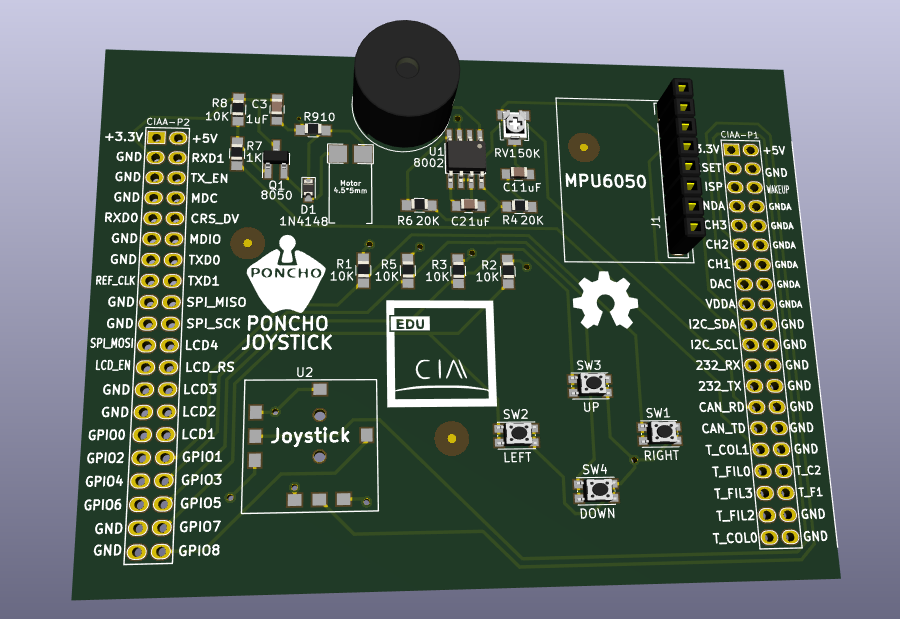
Joystick/doc/Poncho_Joystick_frente.png
