ciaa/Ponchos/Joystick/doc/PonchoJoystick.jpg

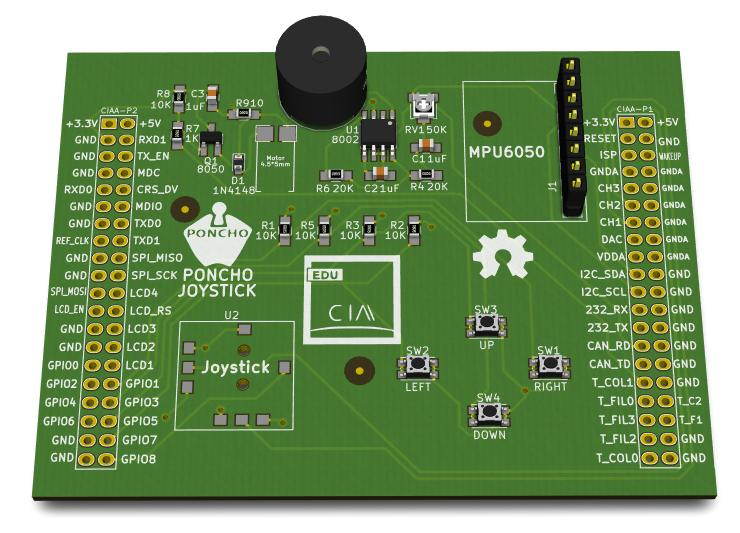
Joystick/doc/PonchoJoystick.jpg
