ciaa/Ponchos/L298/doc/poncho_L298.jpg

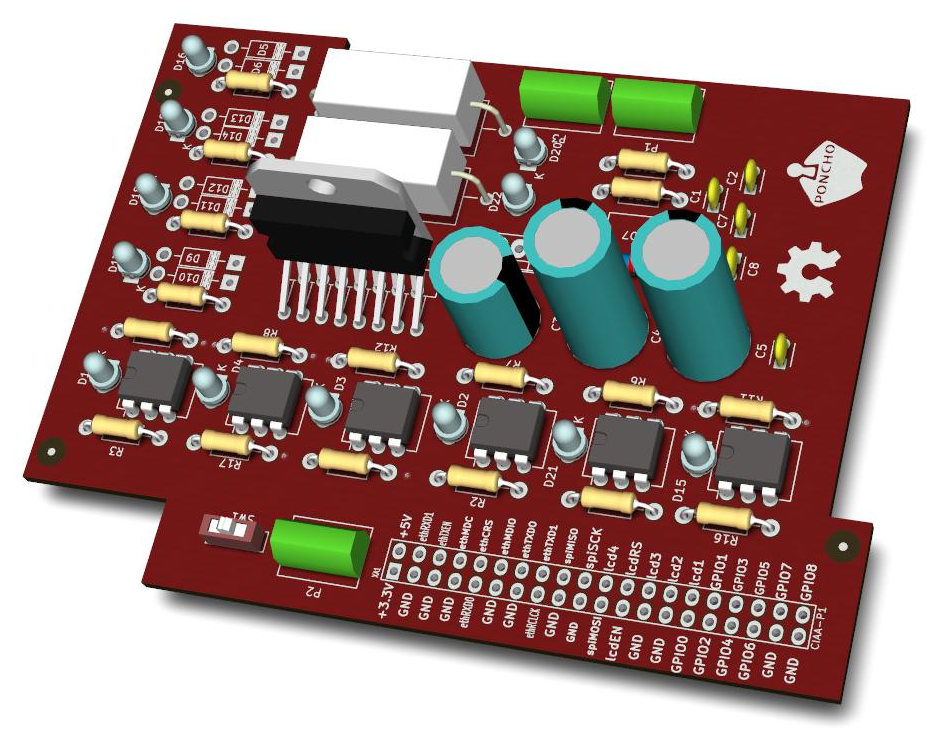
L298/doc/poncho_L298.jpg
