ciaa/Ponchos/L298/info/HTB1WpTHIpXXXXbRXXXXq6xXFXXXs.jpg

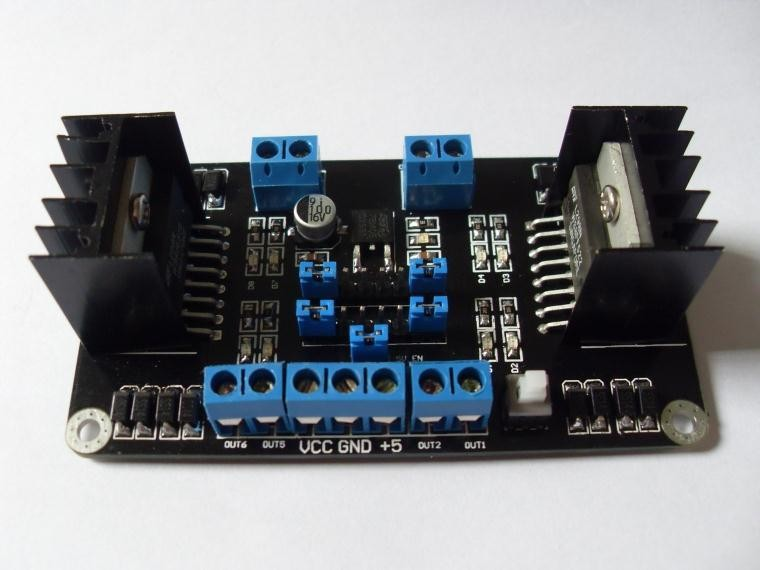
L298/info/HTB1WpTHIpXXXXbRXXXXq6xXFXXXs.jpg
