ciaa/Ponchos/L298/info/L298n-stepper-motor-drive-dc-tarjeta-de-control-del-motor-drive-módulo-de-aislamiento-de-optoacoplador.jpg_640x640.jpg

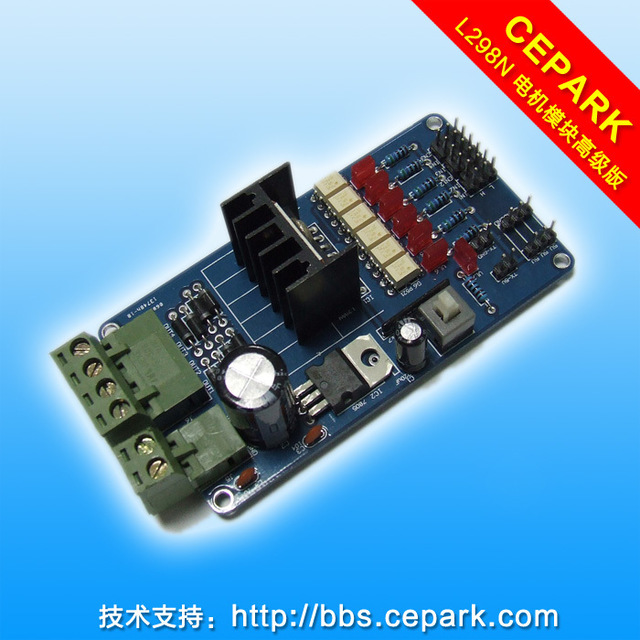
L298/info/L298n-stepper-motor-drive-dc-tarjeta-de-control-del-motor-drive-módulo-de-aislamiento-de-optoacoplador.jpg_640x640.jpg
