ciaa/Ponchos/L298/info/T2ksl.XaJaXXXXXXXX_!!20414607.jpg

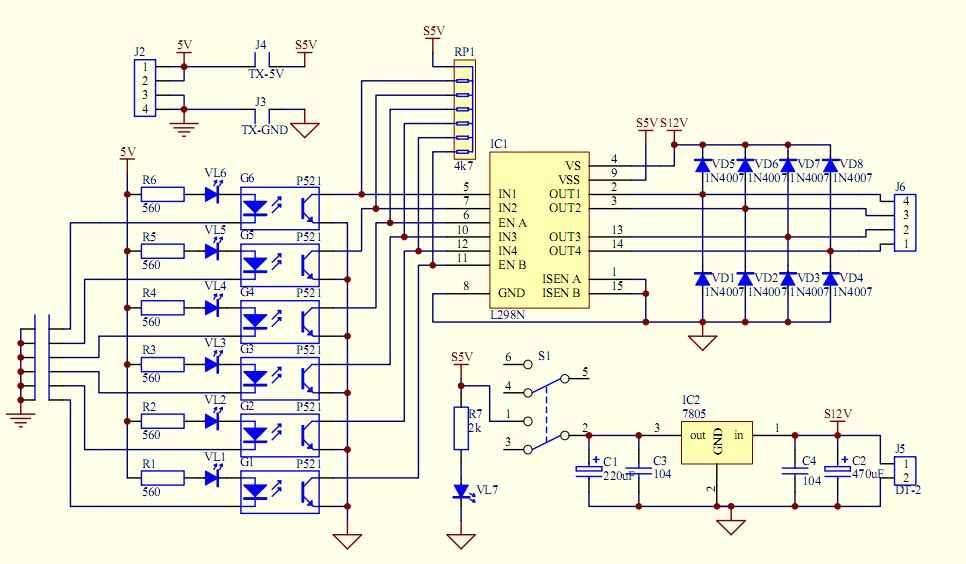
L298/info/T2ksl.XaJaXXXXXXXX_!!20414607.jpg
