ciaa/Ponchos/L298/info/T23b4.XhtaXXXXXXXX_!!20414607.jpg

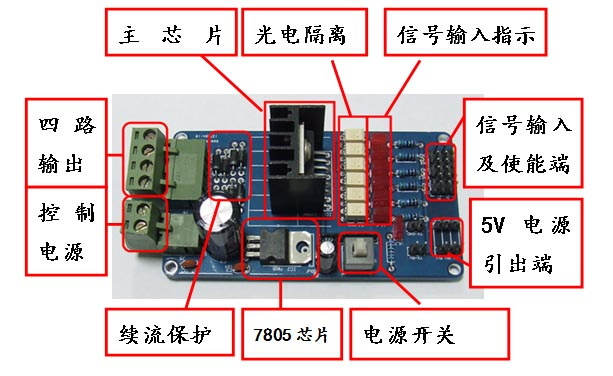
L298/info/T23b4.XhtaXXXXXXXX_!!20414607.jpg
