ciaa/Ponchos/L298/info/thumbnail_99933_3.jpg

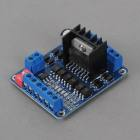
L298/info/thumbnail_99933_3.jpg
