ciaa/Ponchos/MIDI/Doc/Figuras/PonchoMIDI.jpg

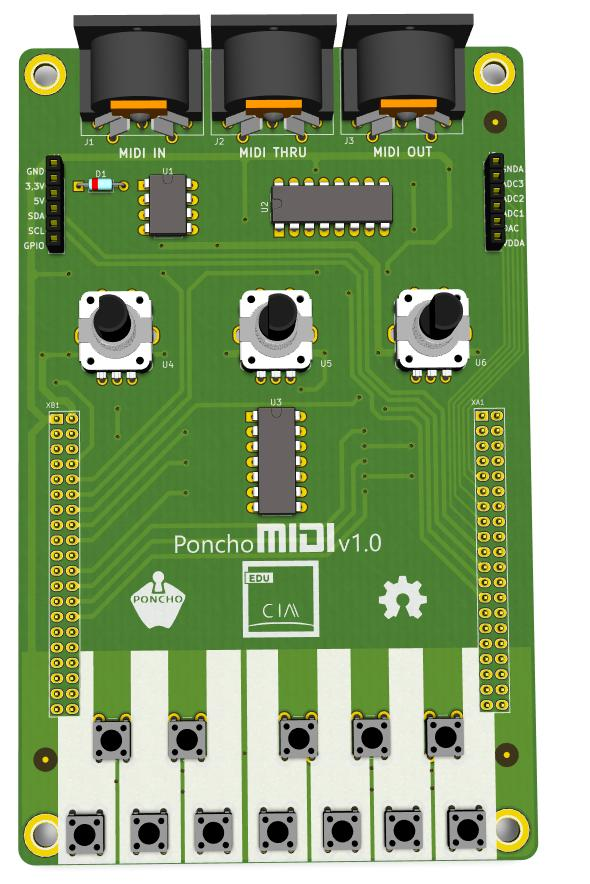
MIDI/Doc/Figuras/PonchoMIDI.jpg
