ciaa/Ponchos/Mision_SAE/doc/BMP085-MOD-2.jpg

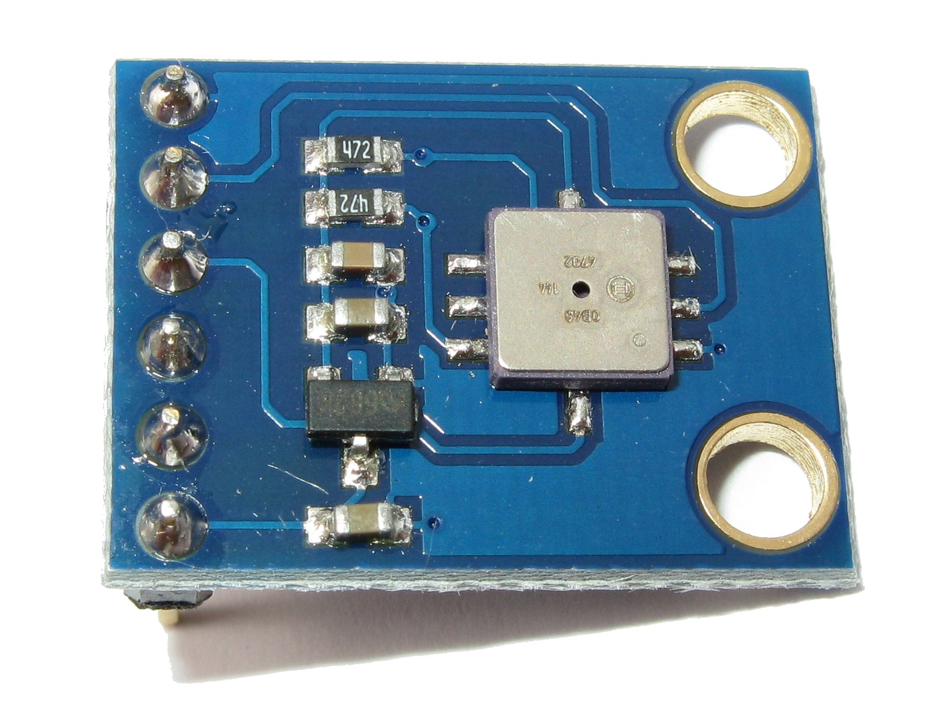
Mision_SAE/doc/BMP085-MOD-2.jpg
