ciaa/Ponchos/Mision_SAE/doc/BMP085-MOD-3.jpg

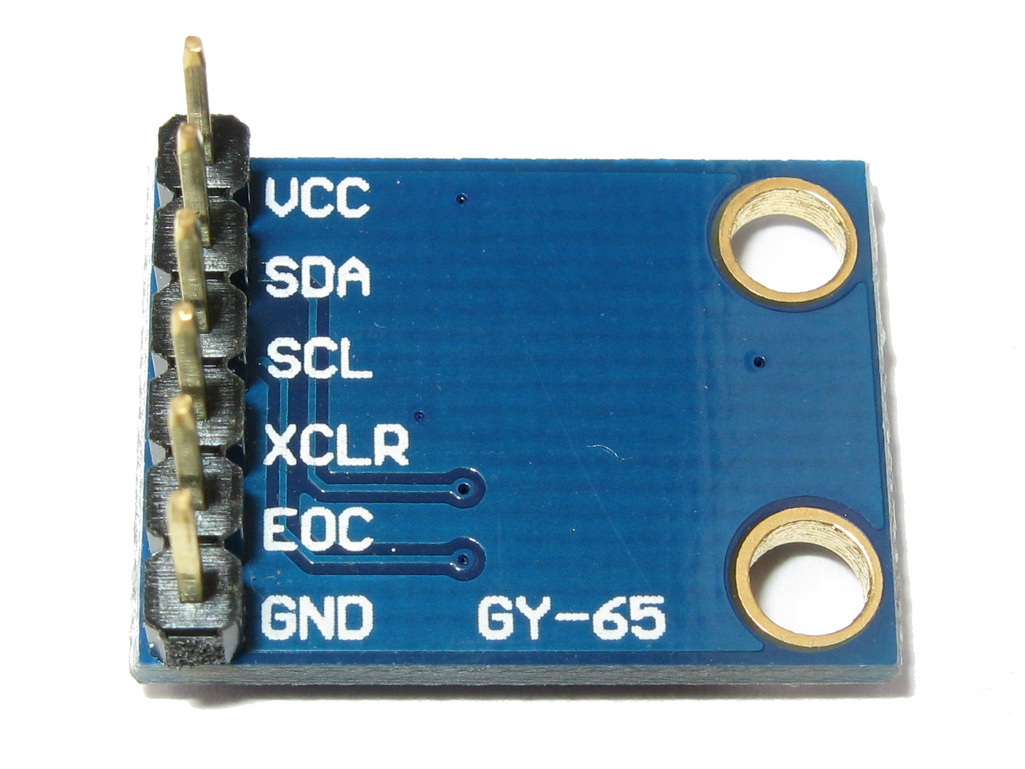
Mision_SAE/doc/BMP085-MOD-3.jpg
