ciaa/Ponchos/Mision_SAE/doc/GY-65-SCH.jpg

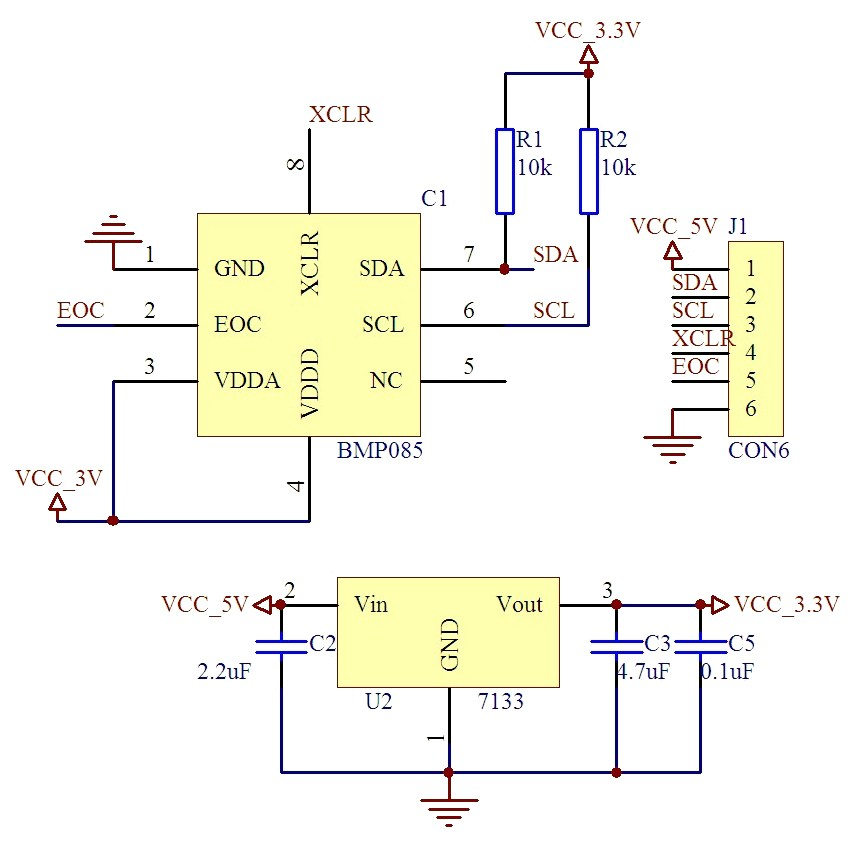
Mision_SAE/doc/GY-65-SCH.jpg
