ciaa/Ponchos/Mision_SAE/doc/GY-521-SCH.jpg

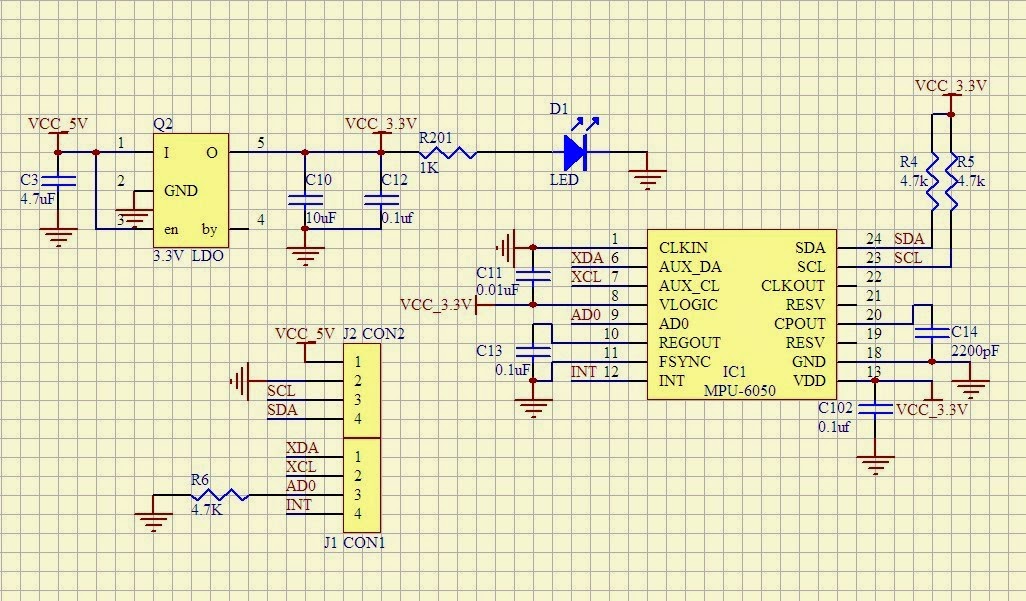
Mision_SAE/doc/GY-521-SCH.jpg
