ciaa/Ponchos/Mision_SAE/doc/GY-521_2.jpg

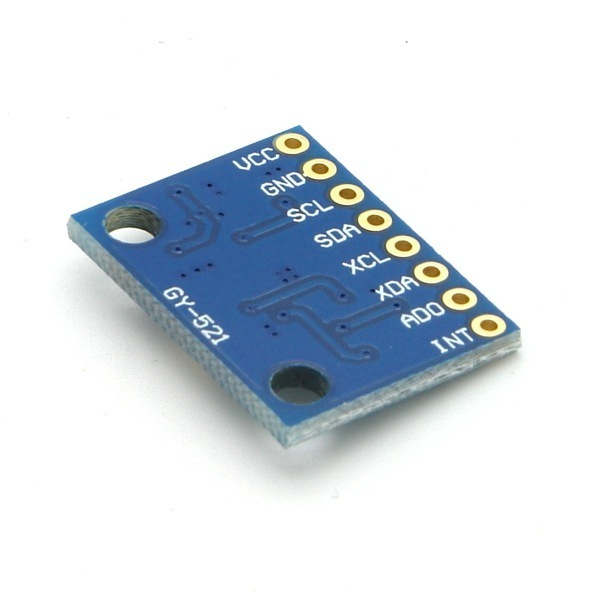
Mision_SAE/doc/GY-521_2.jpg
