ciaa/Ponchos/Mision_SAE/doc/Mision_SAE.png

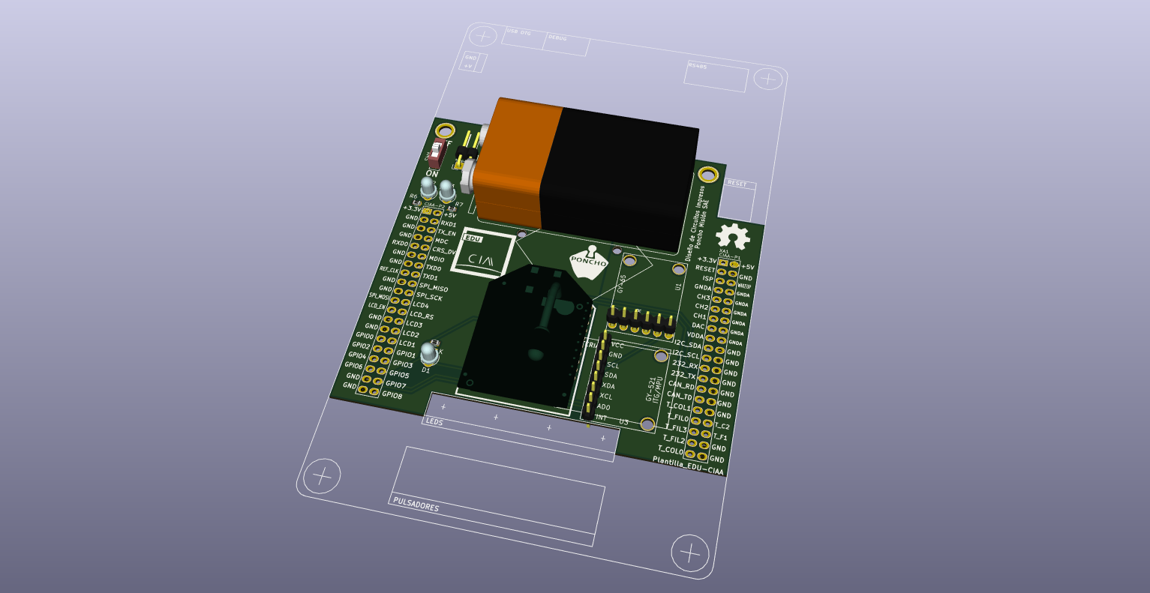
Mision_SAE/doc/Mision_SAE.png
