ciaa/Ponchos/Mision_SAE/doc/modulo-mpu6050-acelerometro-giroscopio-i2c.jpg

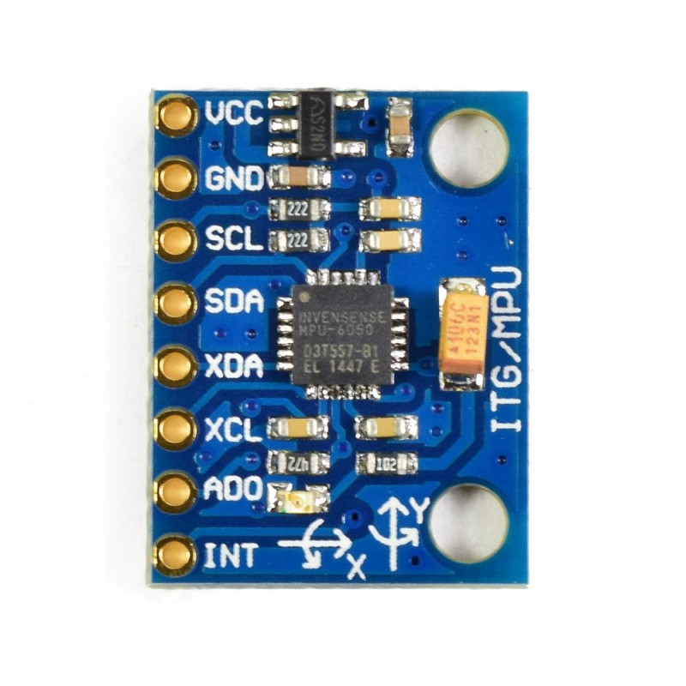
Mision_SAE/doc/modulo-mpu6050-acelerometro-giroscopio-i2c.jpg
