ciaa/Ponchos/Mision_SAE/doc/ponchosae.jpg

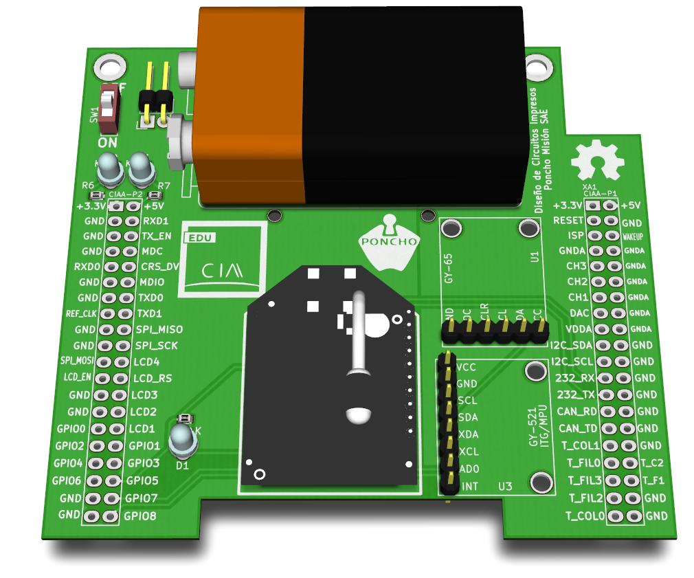
Mision_SAE/doc/ponchosae.jpg
