ciaa/Ponchos/modelos/doc/screen1.jpg

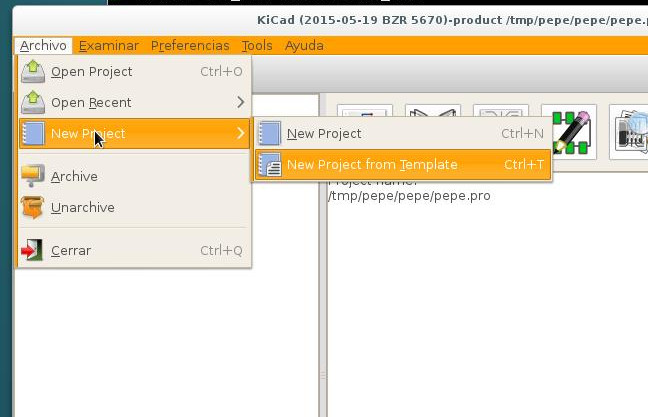
modelos/doc/screen1.jpg
