ciaa/Ponchos/modelos/doc/screen2.jpg

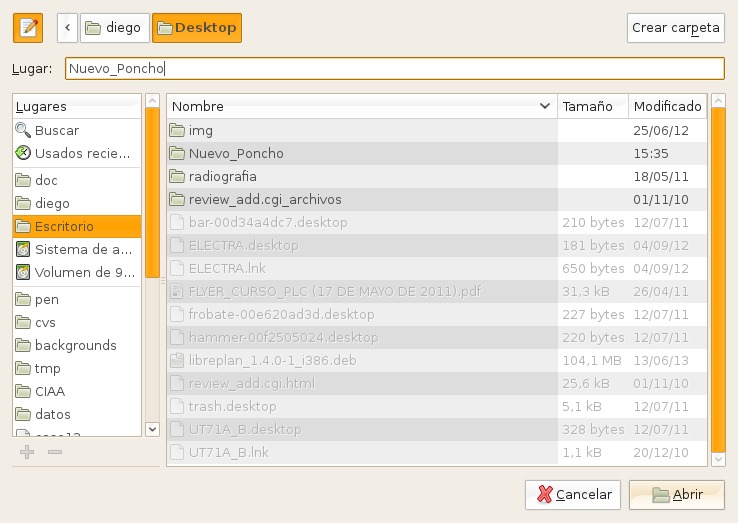
modelos/doc/screen2.jpg
