ciaa/Ponchos/modelos/doc/screen3.jpg

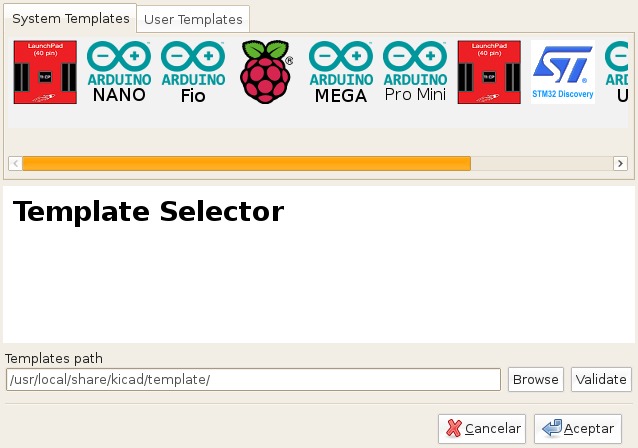
modelos/doc/screen3.jpg
