ciaa/Ponchos/modelos/doc/screen4.jpg

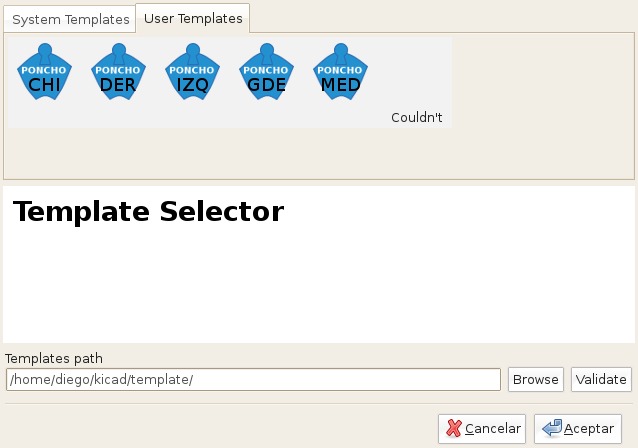
modelos/doc/screen4.jpg
