ciaa/Ponchos/modelos/doc/screen5.jpg

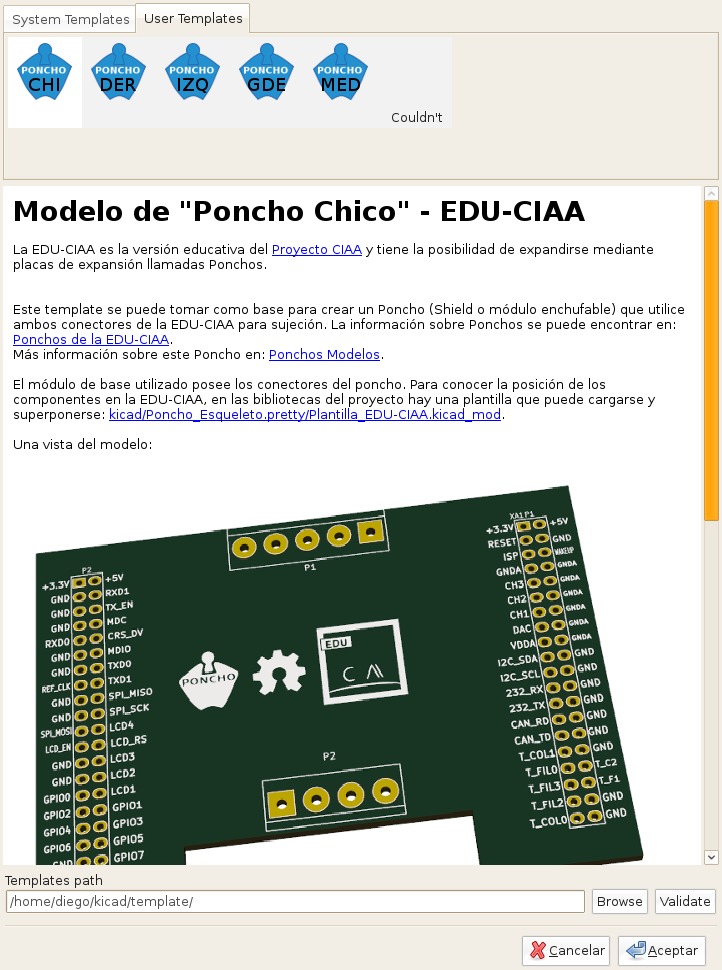
modelos/doc/screen5.jpg
