ciaa/Ponchos/modelos/Poncho_Chico/meta/ponchoB.png

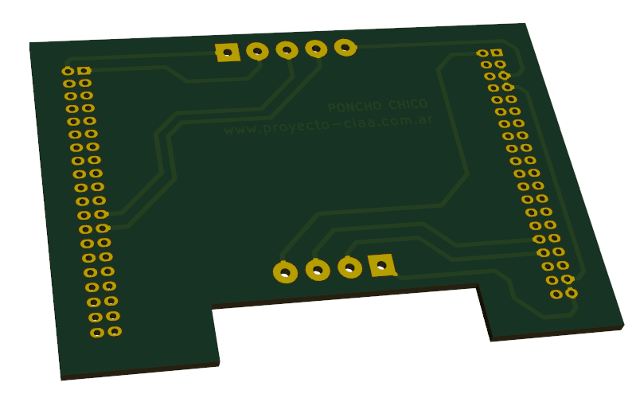
modelos/Poncho_Chico/meta/ponchoB.png
