ciaa/Ponchos/modelos/Poncho_Derecho/meta/ponchoF.png

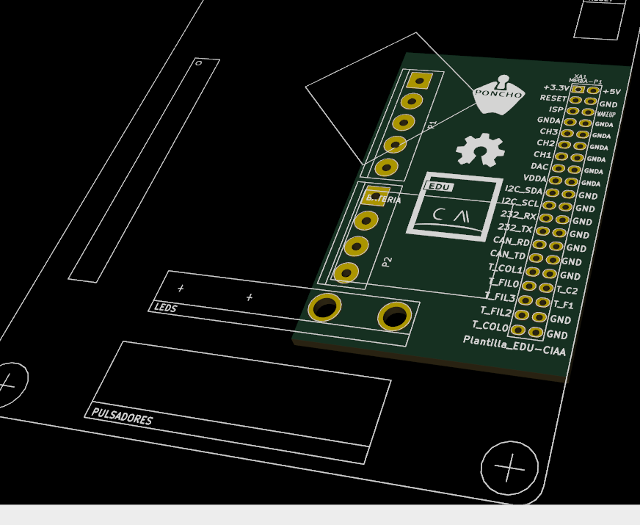
modelos/Poncho_Derecho/meta/ponchoF.png
