ciaa/Ponchos/modelos/Poncho_Derecho/meta/ponchoFb.png

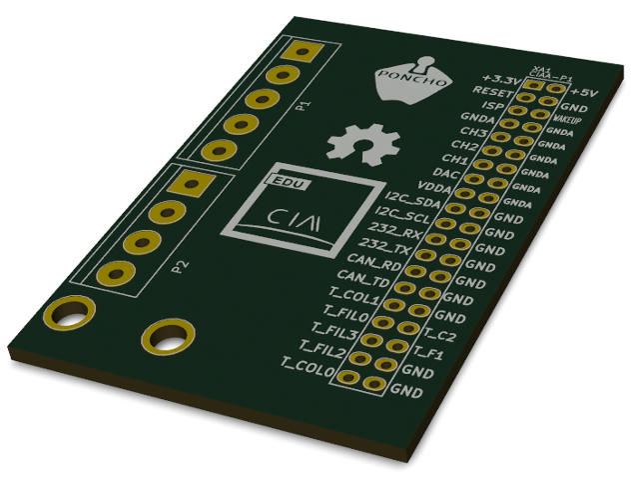
modelos/Poncho_Derecho/meta/ponchoFb.png
