ciaa/Ponchos/modelos/Poncho_Grande/meta/poncho_grande.png

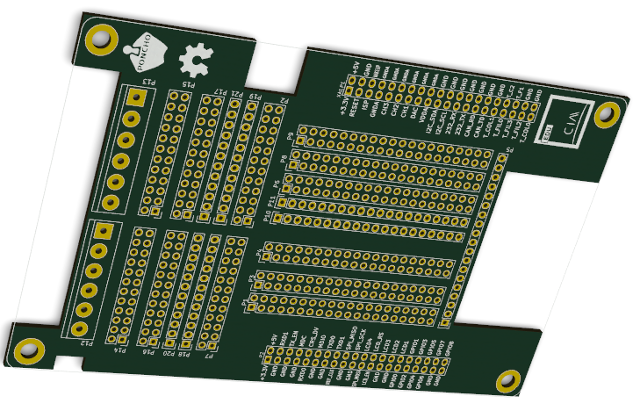
modelos/Poncho_Grande/meta/poncho_grande.png
