ciaa/Ponchos/modelos/Poncho_Izquierdo/meta/ponchoF.png

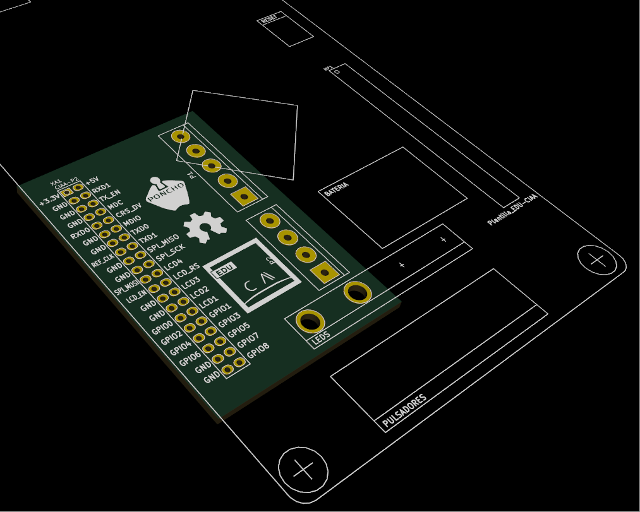
modelos/Poncho_Izquierdo/meta/ponchoF.png
