ciaa/Ponchos/modelos/Poncho_Izquierdo/meta/ponchoFb.png

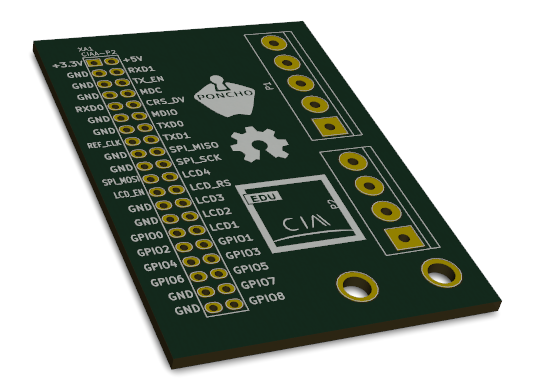
modelos/Poncho_Izquierdo/meta/ponchoFb.png
