ciaa/Ponchos/modelos/Poncho_Mediano/meta/ponchoF.png

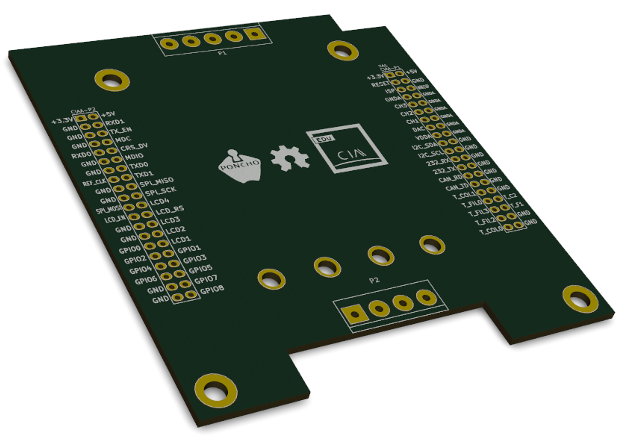
modelos/Poncho_Mediano/meta/ponchoF.png
