ciaa/Ponchos/modelos/Poncho_Superior_PicoCIAA/meta/Template_PicoCIAA.png

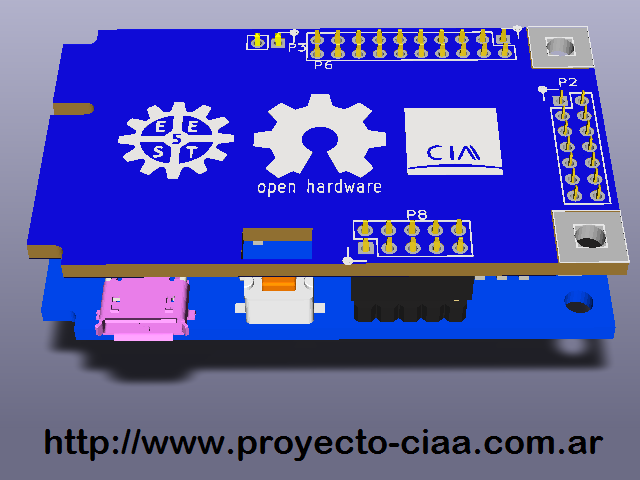
modelos/Poncho_Superior_PicoCIAA/meta/Template_PicoCIAA.png
