ciaa/Ponchos/NivelTanque/doc/fotos/LR_20180206_214929.jpg

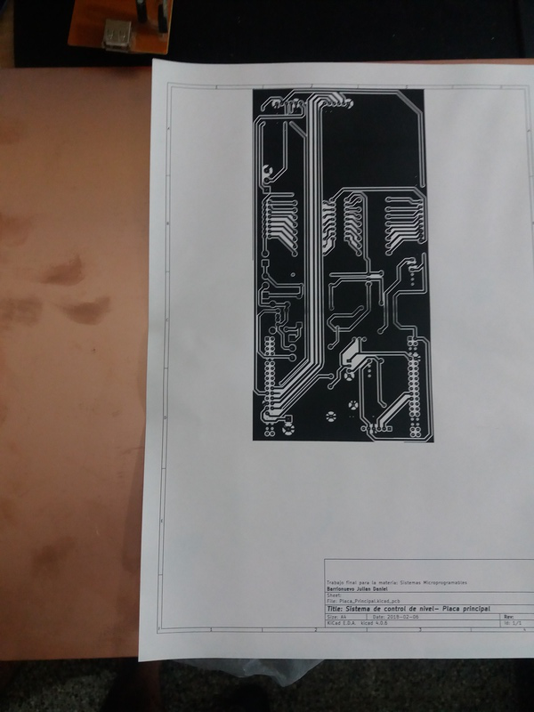
NivelTanque/doc/fotos/LR_20180206_214929.jpg
