ciaa/Ponchos/NivelTanque/doc/fotos/LR_20180206_221056.jpg

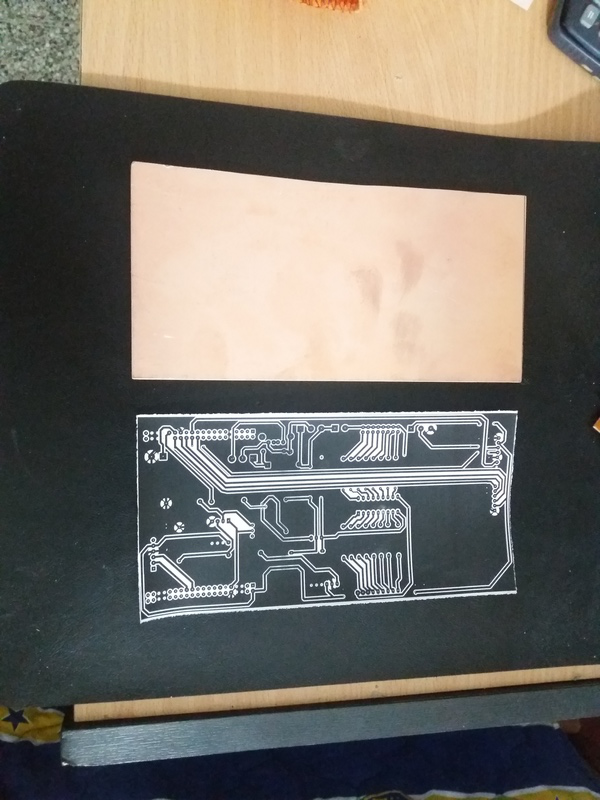
NivelTanque/doc/fotos/LR_20180206_221056.jpg
