ciaa/Ponchos/NivelTanque/doc/fotos/LR_20180206_224821.jpg

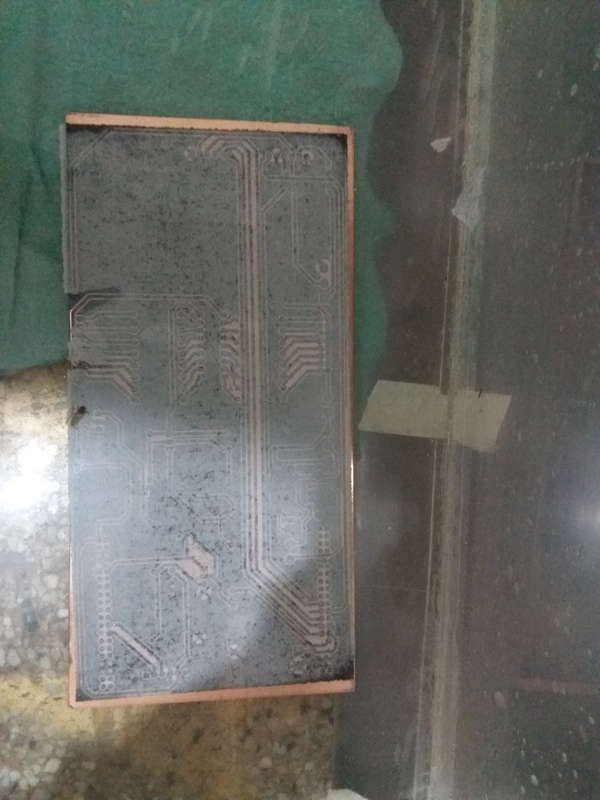
NivelTanque/doc/fotos/LR_20180206_224821.jpg
