ciaa/Ponchos/NivelTanque/doc/fotos/LR_20180207_053223.jpg

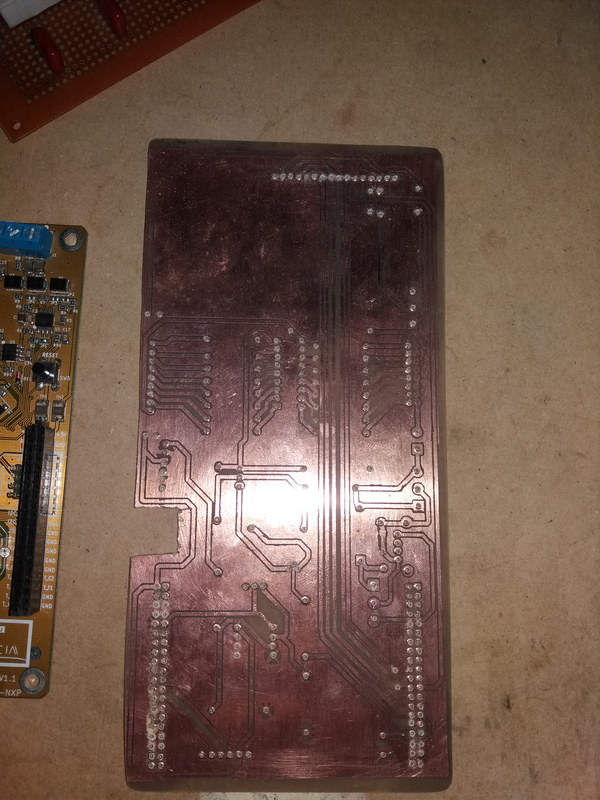
NivelTanque/doc/fotos/LR_20180207_053223.jpg
