ciaa/Ponchos/NivelTanque/doc/fotos/LR_20180208_050006.jpg

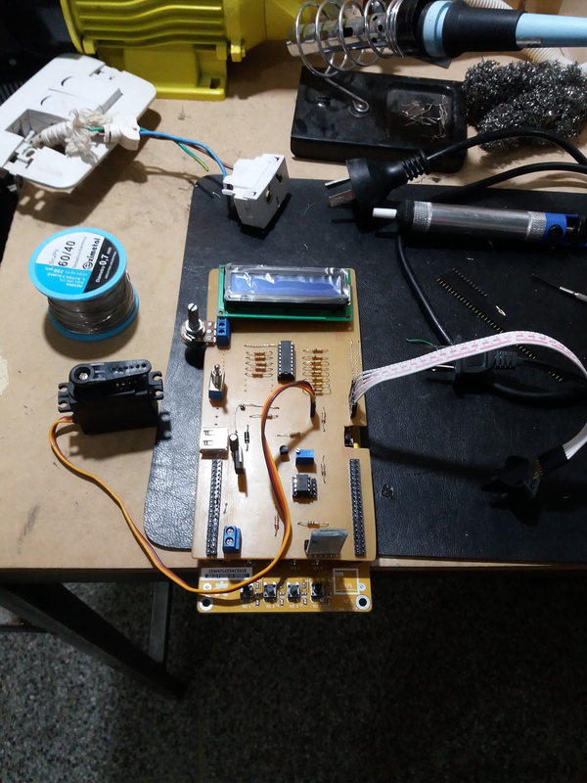
NivelTanque/doc/fotos/LR_20180208_050006.jpg
