ciaa/Ponchos/NivelTanque/doc/fotos/LR_20180213_183755.jpg

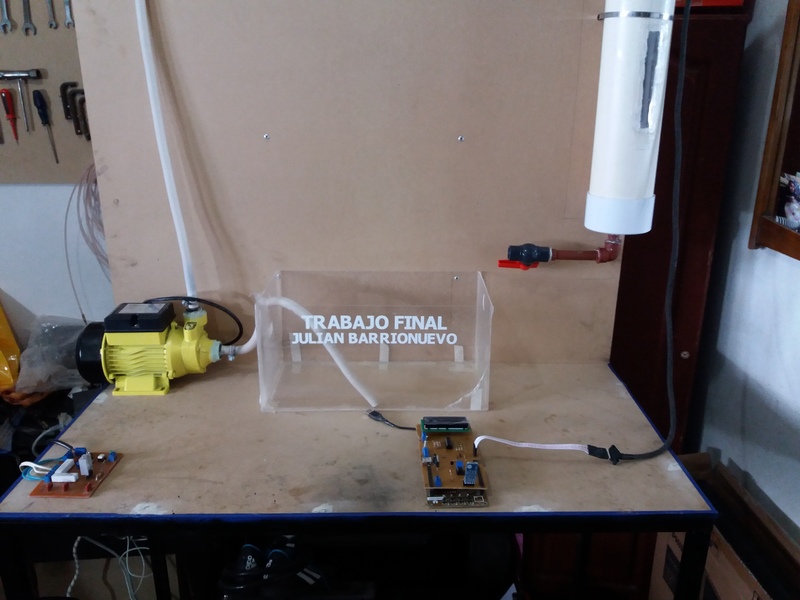
NivelTanque/doc/fotos/LR_20180213_183755.jpg
