ciaa/Ponchos/NivelTanque/doc/fotos/LR_20180213_183830.jpg

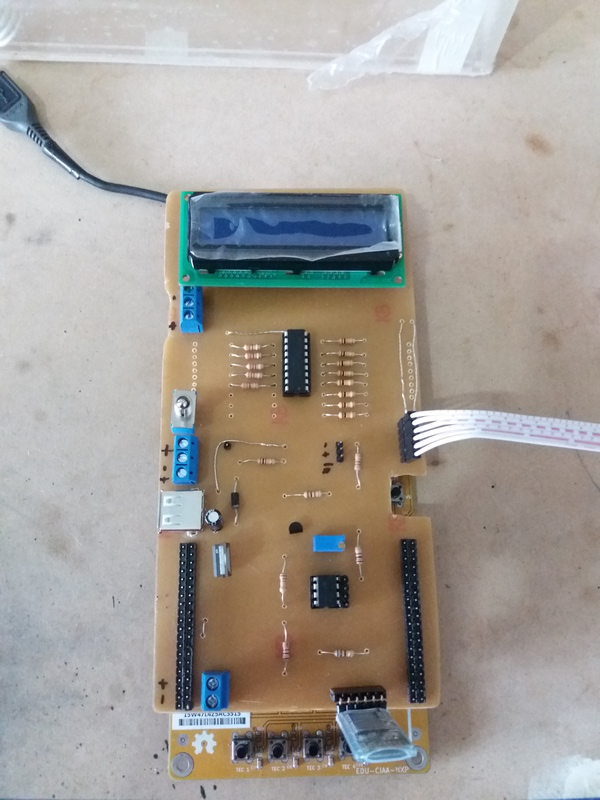
NivelTanque/doc/fotos/LR_20180213_183830.jpg
