ciaa/Ponchos/NivelTanque/doc/fotos/LR_20180225_112121.jpg

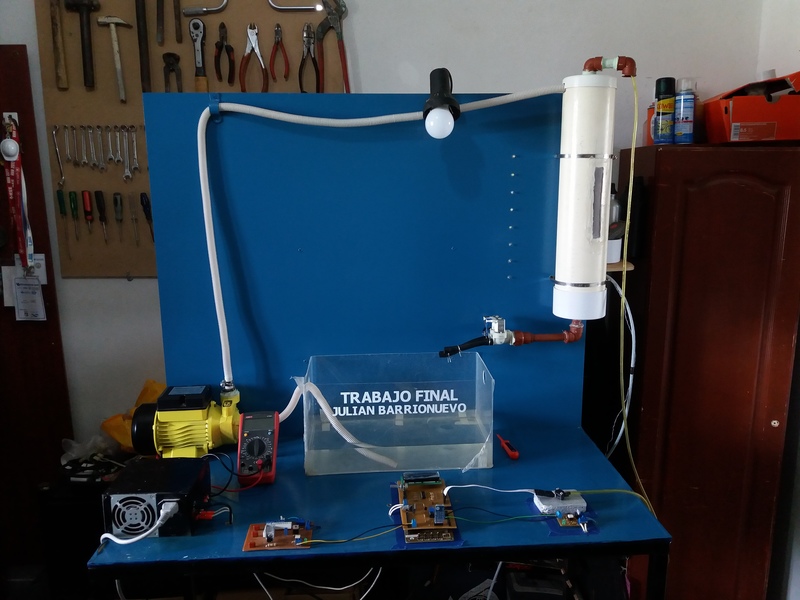
NivelTanque/doc/fotos/LR_20180225_112121.jpg
