ciaa/Ponchos/Osciloscopio/doc/Oscilloscopio.jpg

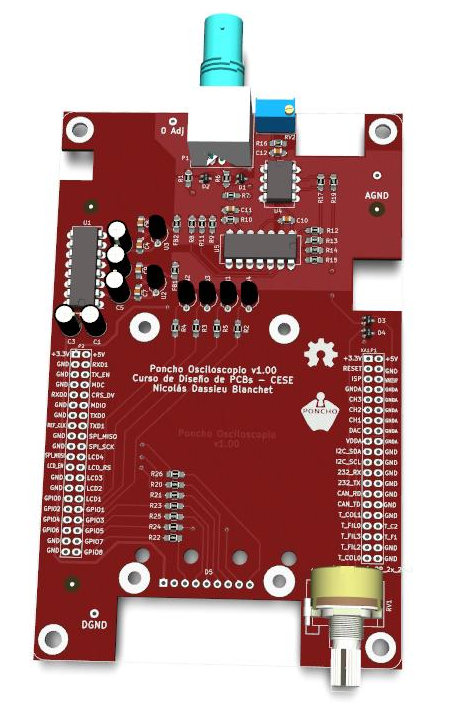
Osciloscopio/doc/Oscilloscopio.jpg
