ciaa/Ponchos/Oximetro/doc/ponchooximetro.jpg

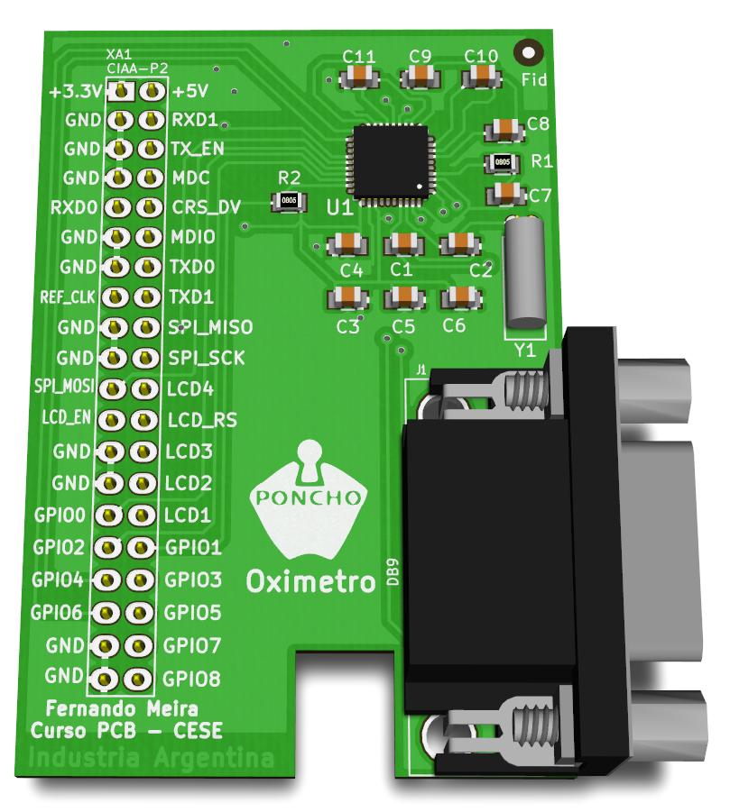
Oximetro/doc/ponchooximetro.jpg
