ciaa/Ponchos/Pico_WiFi/doc/ponchowifi.jpg

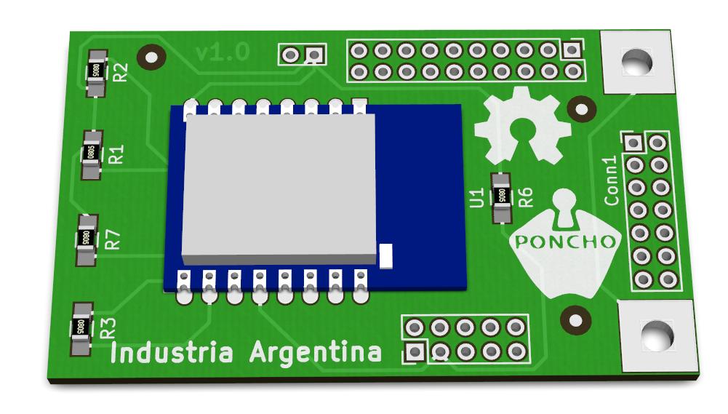
Pico_WiFi/doc/ponchowifi.jpg
