ciaa/Ponchos/Poncho PLC/doc/PCB_Poncho_PLC_Rev1.0.jpeg

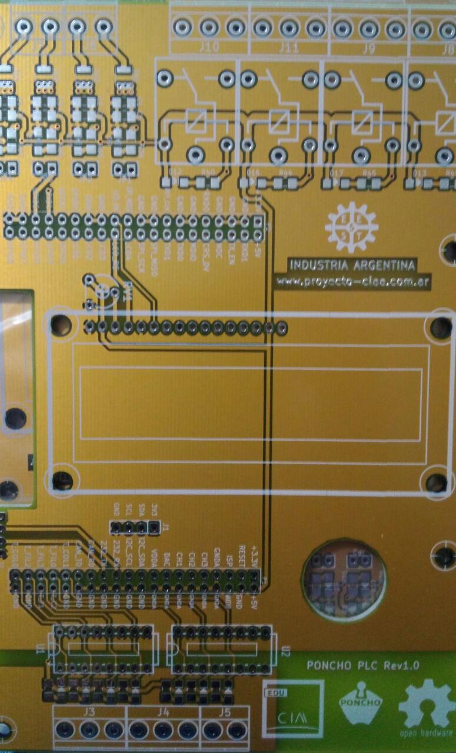
Poncho PLC/doc/PCB_Poncho_PLC_Rev1.0.jpeg
