ciaa/Ponchos/Poncho PLC/doc/plc.jpg

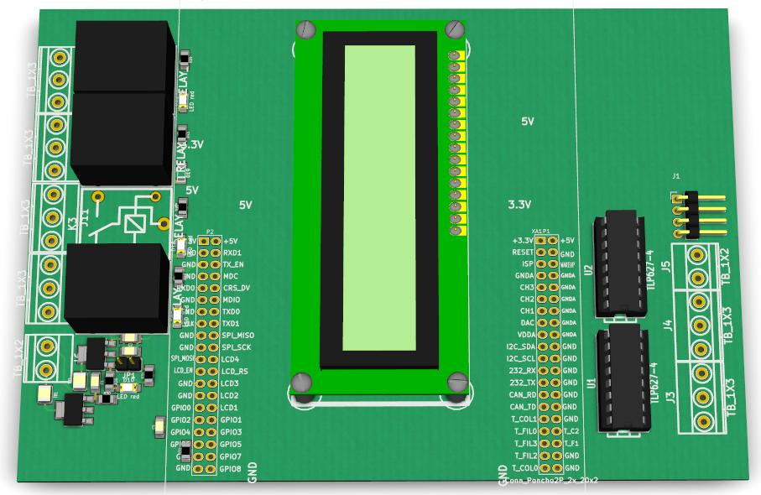
Poncho PLC/doc/plc.jpg
