ciaa/Ponchos/Poncho PLC/doc/Poncho_PLC_3D_View.jpg

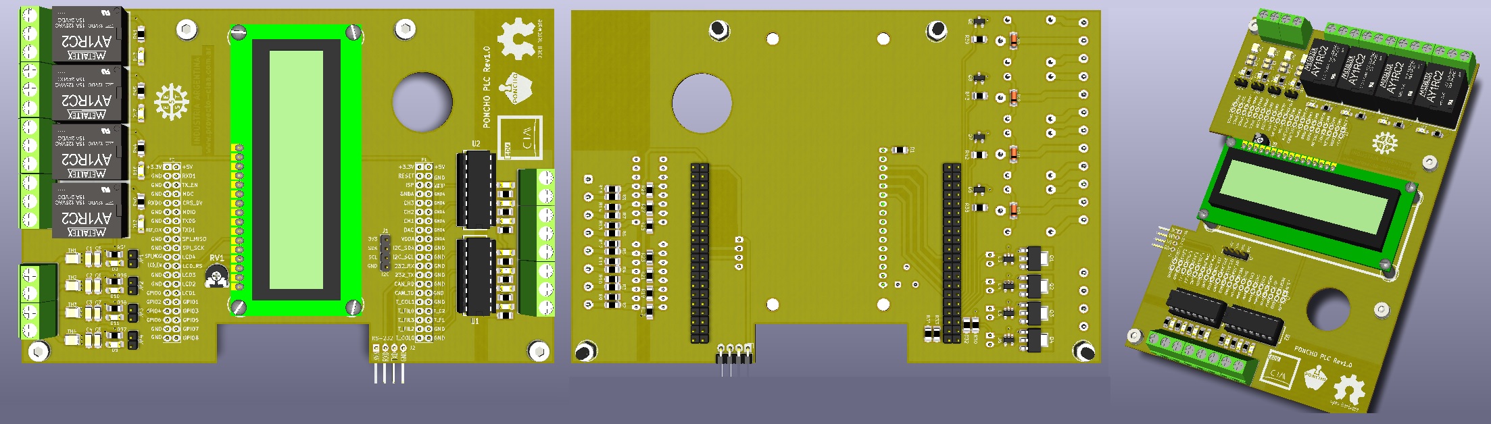
Poncho PLC/doc/Poncho_PLC_3D_View.jpg
