ciaa/Ponchos/Poncho_ESP-WROOM-32/Img/PonchoWifiESPWROOM32.jpg

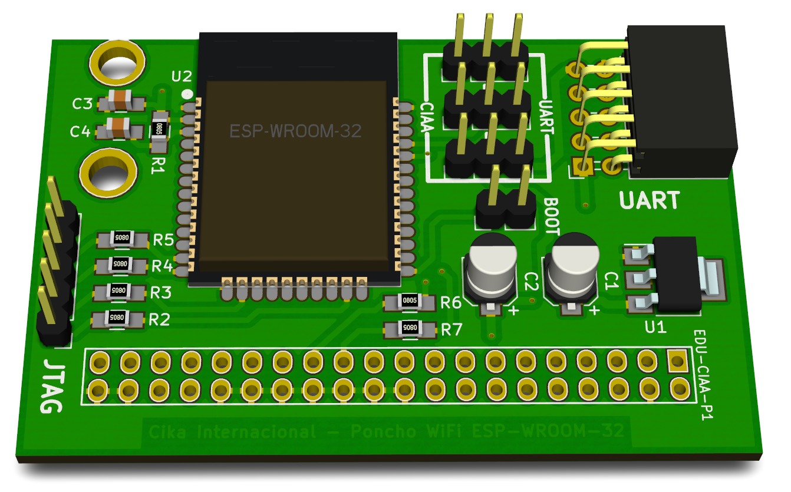
Poncho_ESP-WROOM-32/Img/PonchoWifiESPWROOM32.jpg
