ciaa/Ponchos/PuenteHxI2C/doc/ponchomotores.png

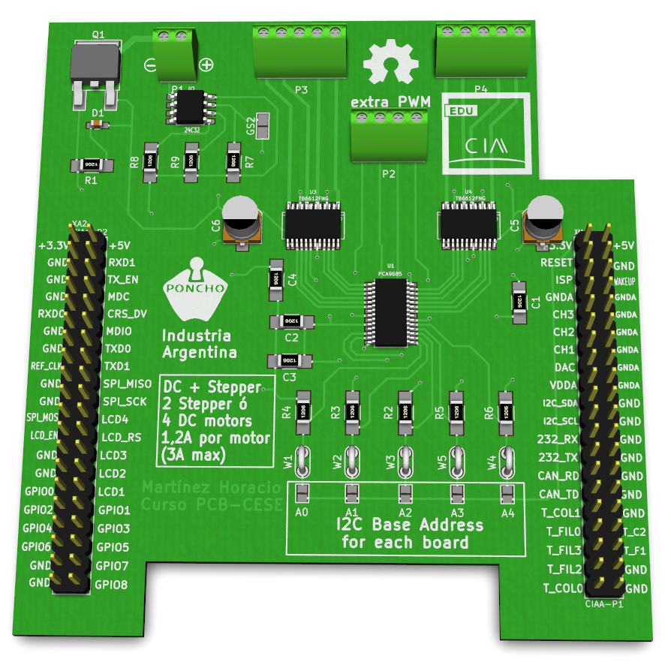
PuenteHxI2C/doc/ponchomotores.png
