ciaa/Ponchos/PuenteHxI2C/driver_motores_EDU_CIAA.png

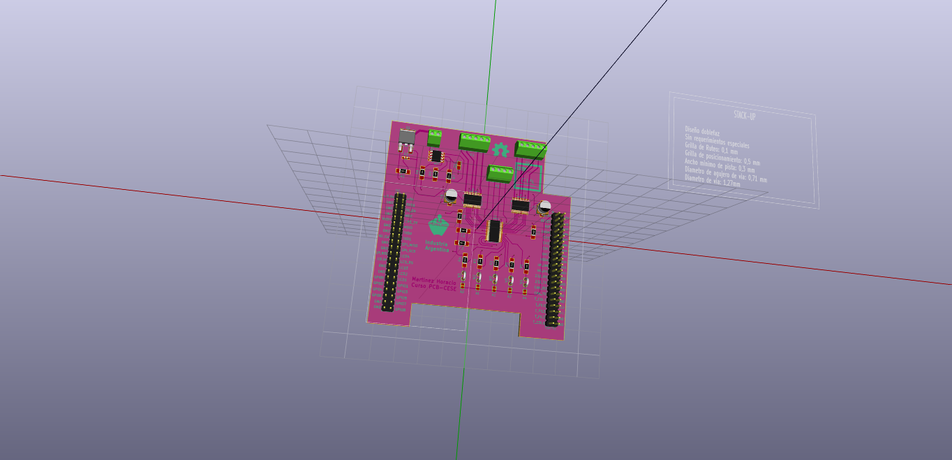
PuenteHxI2C/driver_motores_EDU_CIAA.png
