ciaa/Ponchos/Simon/doc/pcbRoute.png

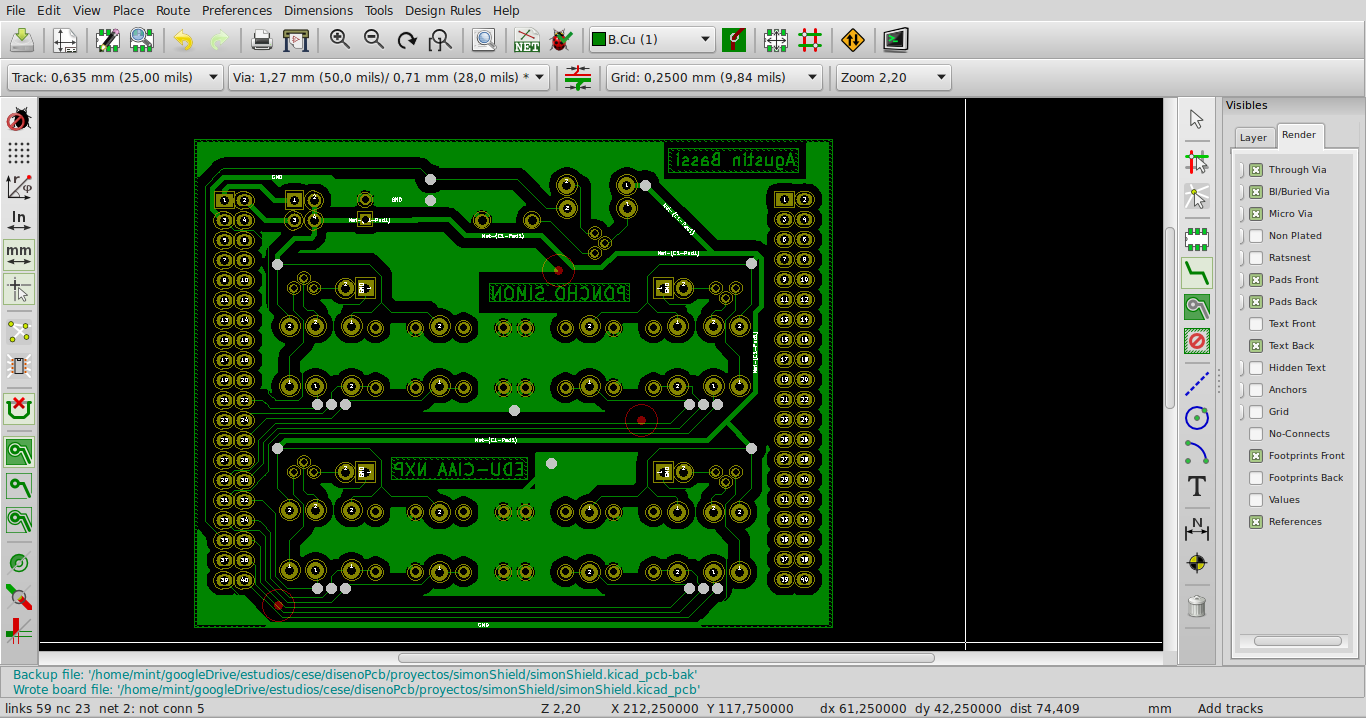
Simon/doc/pcbRoute.png
