ciaa/Ponchos/Simon/doc/simonShield.jpg

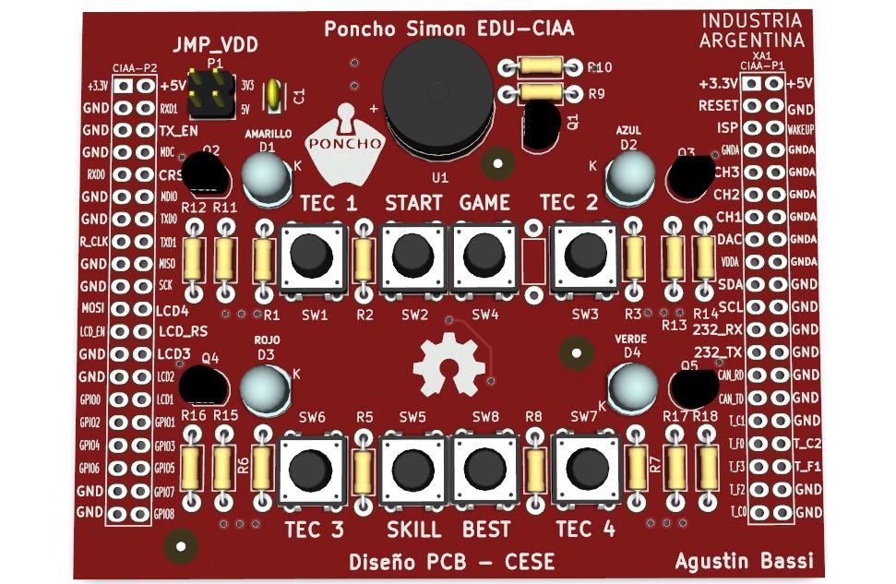
Simon/doc/simonShield.jpg
