ciaa/Ponchos/Simon/doc/simonShieldBottom.png

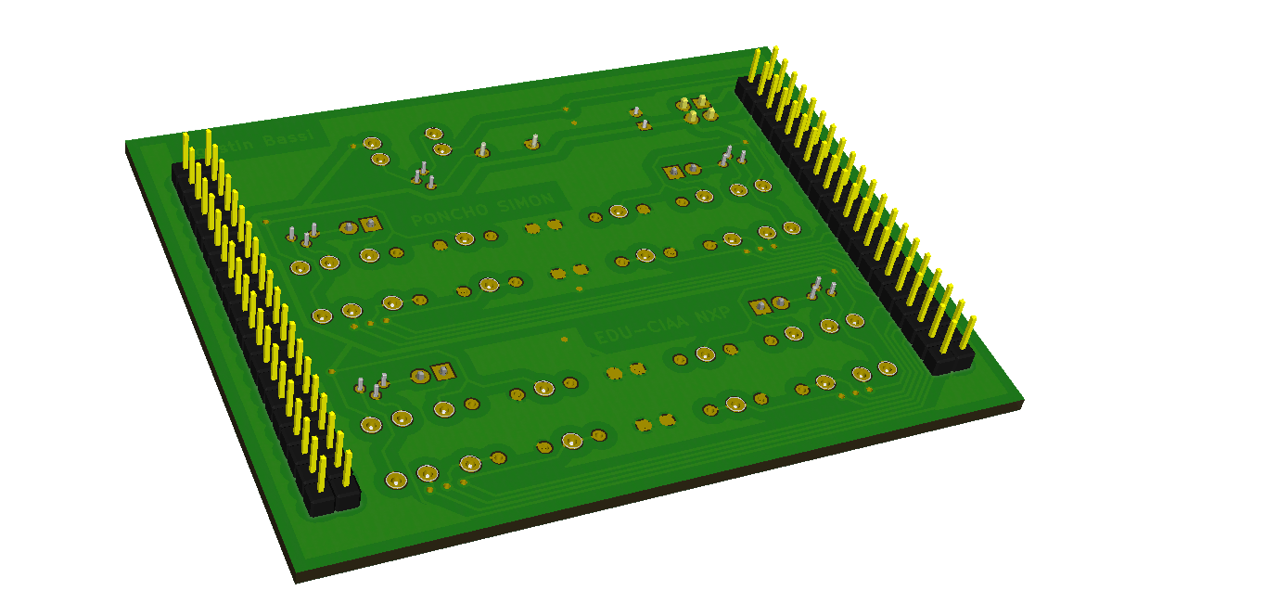
Simon/doc/simonShieldBottom.png
