ciaa/Ponchos/Simon/doc/simonShieldTop.png

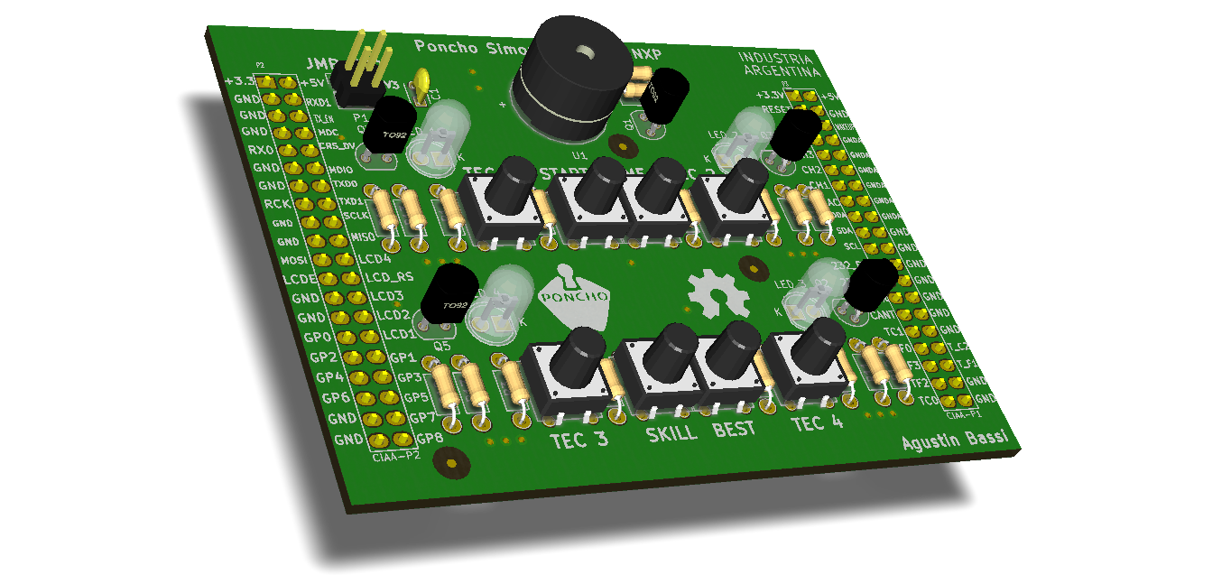
Simon/doc/simonShieldTop.png
