ciaa/Ponchos/Sumo_Robot/doc/fotos/LG_20170701_152622.jpg

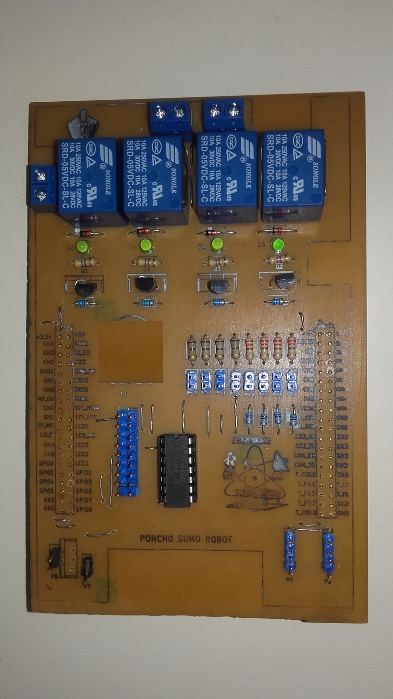
Sumo_Robot/doc/fotos/LG_20170701_152622.jpg
