ciaa/Ponchos/Sumo_Robot/doc/fotos/LG_20170701_152644.jpg

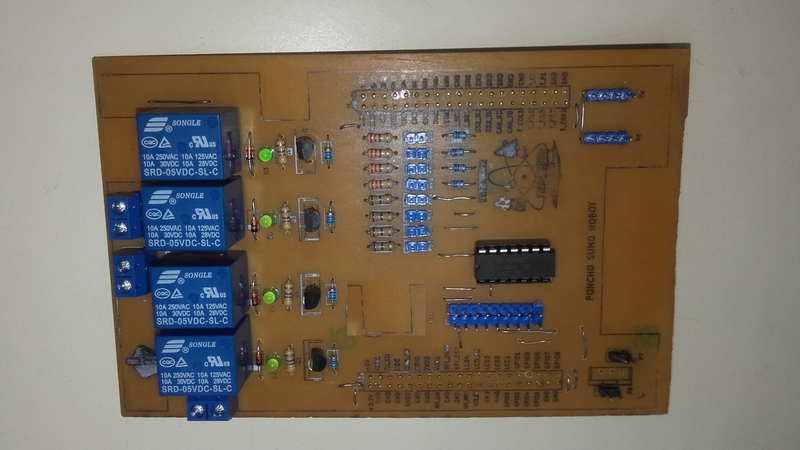
Sumo_Robot/doc/fotos/LG_20170701_152644.jpg
