ciaa/Ponchos/Sumo_Robot/doc/fotos/LG_20170701_154523.jpg

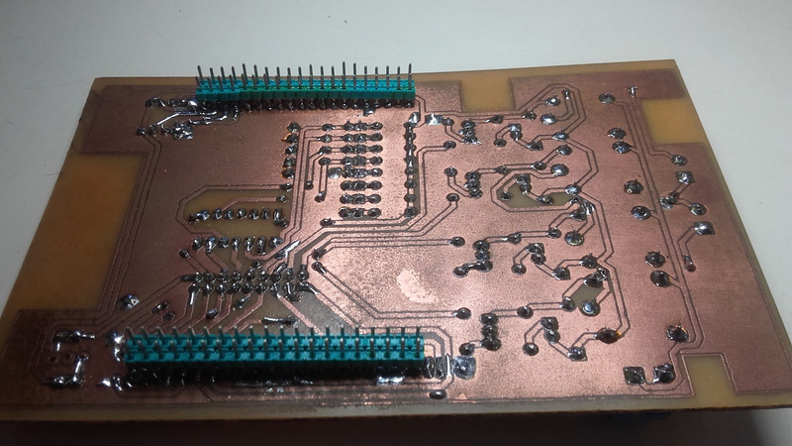
Sumo_Robot/doc/fotos/LG_20170701_154523.jpg
