ciaa/Ponchos/Sumo_Robot/doc/sumorobot.jpg

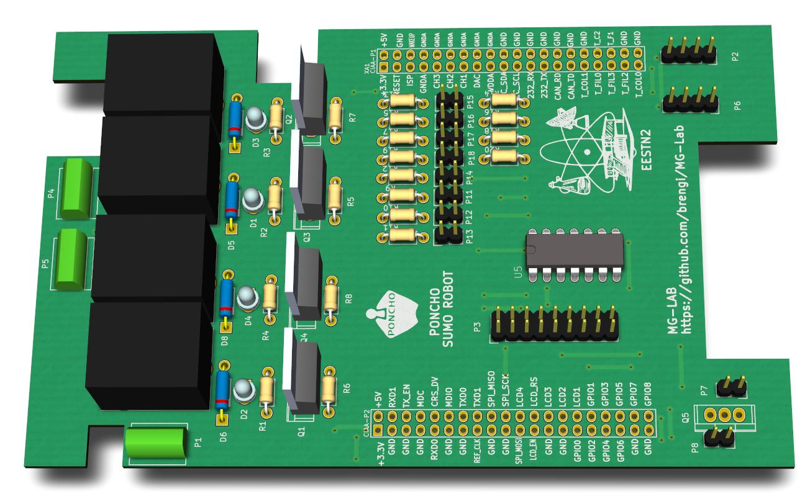
Sumo_Robot/doc/sumorobot.jpg
