ciaa/Ponchos/WifiBT_CESE_ESPWROOM32/doc/PonchoEDUCIAA_WIFI_BLT1.2.png

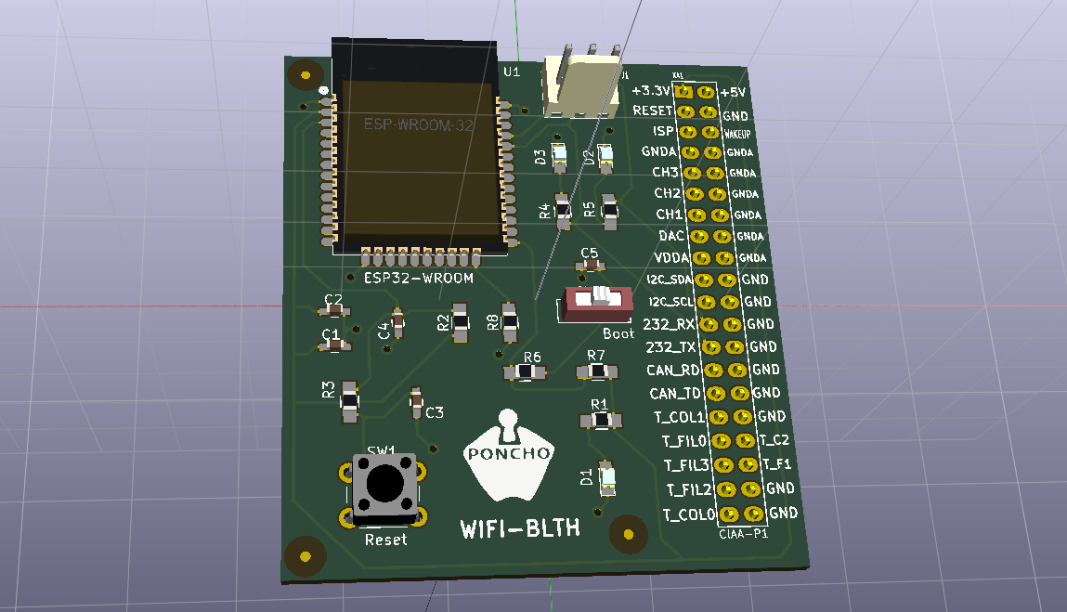
WifiBT_CESE_ESPWROOM32/doc/PonchoEDUCIAA_WIFI_BLT1.2.png
