ciaa/Ponchos/WifiBT_CESE_ESPWROOM32/doc/PonchoEDUCIAA_WIFI_BLT2.png

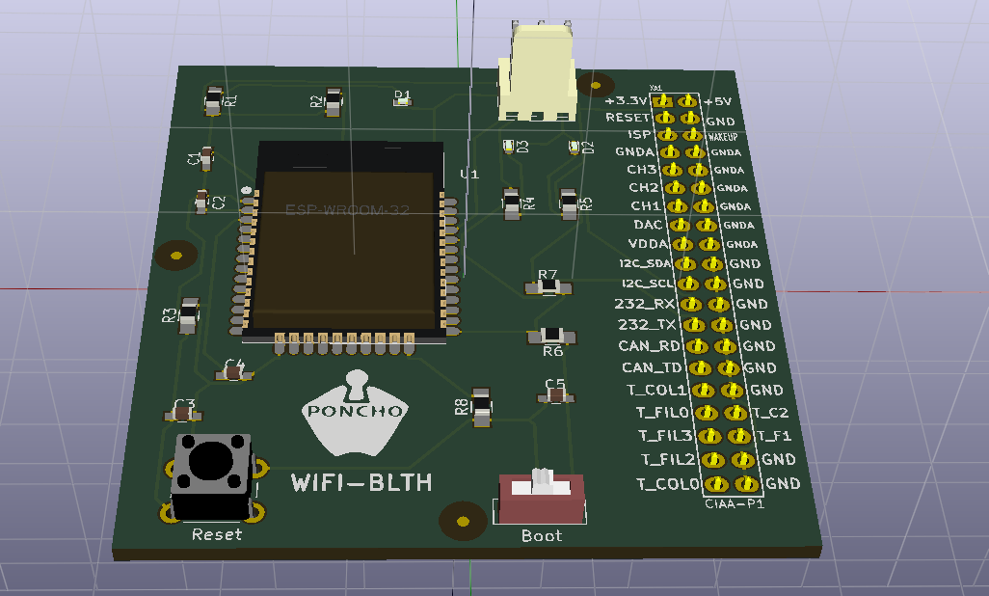
WifiBT_CESE_ESPWROOM32/doc/PonchoEDUCIAA_WIFI_BLT2.png
