ciaa/Ponchos/WifiBT_CESE_ESPWROOM32/doc/PonchoEDUCIAA_WIFI_BLT3.png

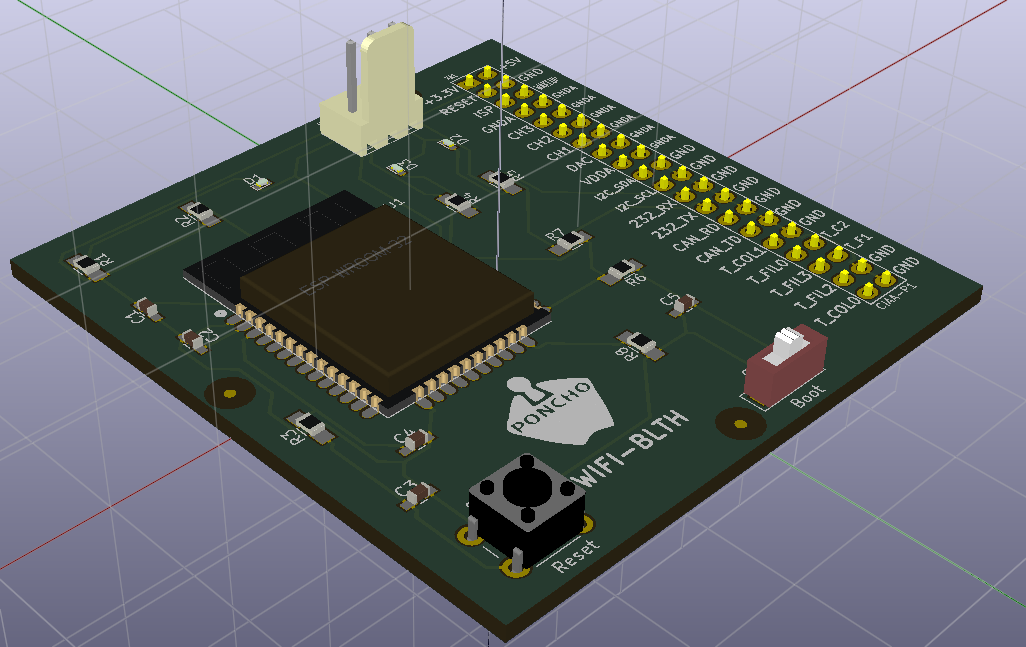
WifiBT_CESE_ESPWROOM32/doc/PonchoEDUCIAA_WIFI_BLT3.png
