ciaa/Ponchos/WifiBT_CESE_ESPWROOM32/doc/PonchoWifi-BLT.jpg

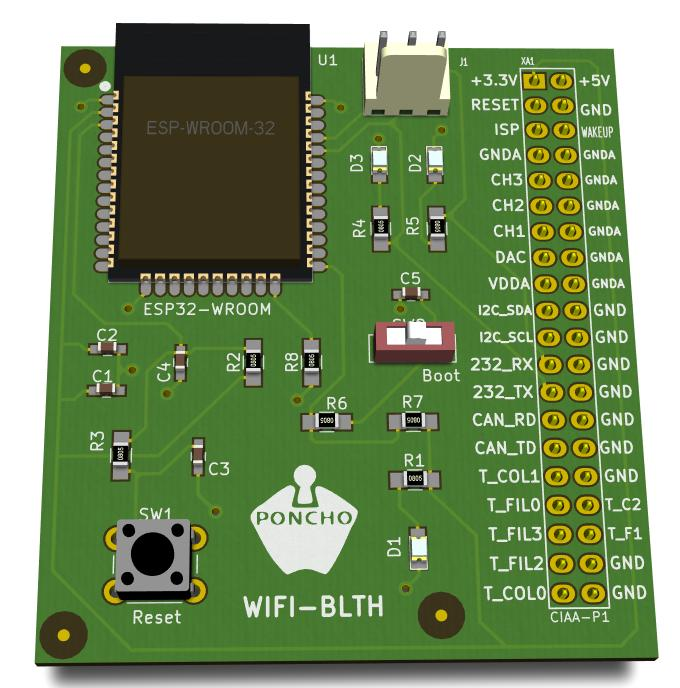
WifiBT_CESE_ESPWROOM32/doc/PonchoWifi-BLT.jpg
