ciaa/Ponchos/Simon/tools/kicost-0.1.25/tests/TestParts.xlsx

 |  |  |  |  |  |  | Board Qty: | 100
 |  |  |  |  |  |  | Total Cost: | $0.00 |  |  |  | $0.00 |  |  |  |  |  | $0.00 |  |  |  |  |  | $0.00
 |  |  |  |  |  |  | Unit Cost: | $0.00
Global Part Info |  |  |  |  |  |  |  |  | Digi-Key |  |  |  |  |  | Mouser |  |  |  |  |  | Newark
Refs | Value | Desc | Footprint | Manf | Manf# | Qty | Unit$ | Ext$ | Avail | Purch | Unit$ | Ext$ | Cat# | Doc | Avail | Purch | Unit$ | Ext$ | Cat# | Doc | Avail | Purch | Unit$ | Ext$ | Cat# | Doc
Y2 | 000005V1RA | CRYSTAL 32.768KHZ 7PF SMD | ABS07 | Abracon | ABS07-32.768KHZ-7-T | 0 | $0.00 | $0.00 | 0 |  | $0.00 | $0.00 | 535-9543-1-ND | Link (http://www.digikey.com/product-detail/en/abracon-llc/ABS07-32.768KHZ-7-T/535-9543-1-ND/1237010) | 688 |  | $0.00 | $0.00 | 815-ABS07-32.768K7T | Link (http://www.mouser.com/Search/Refine.aspx?Keyword=ABS07-32.768KHZ-7-T%20Abracon) | 1220 |  | $0.00 | $0.00 | 14N8750 | Link (http://www.newark.com/abracon/abs07-32-768khz-7-t/crystal-32-768khz-7pf-3-2-x-1/dp/14N8750)
R1,R2 | 000001V1RA | RES SMD 1K OHM 1% 1/20W 0201 | R_0201 | Vishay Dale | CRCW02011K00FKED | 0 | $0.00 | $0.00 | 96315 |  | $0.00 | $0.00 | 541-1.00KAABCT-ND | Link (http://www.digikey.com/product-detail/en/vishay-dale/CRCW02011K00FKED/541-1.00KAABCT-ND/1968163) | 25295 |  | $0.00 | $0.00 | 71-CRCW02011K00FKED | Link (http://www.mouser.com/Search/Refine.aspx?Keyword=CRCW02011K00FKED%20Vishay%20Dale) | 17706 |  | $0.00 | $0.00 | 89M6577 | Link (http://www.newark.com/vishay-dale/crcw02011k00fned/res-thick-film-1k-1-0-05w-0201/dp/89M6577)
C1,C2 | 000004V1RA | CAP CER 27PF 50V NP0 0402 | C_0402 | Kemet | C0402C270J5GACTU | 0 | $0.00 | $0.00 | 187655 |  | $0.00 | $0.00 | 399-1016-1-ND | Link (http://www.digikey.com/product-detail/en/kemet/C0402C270J5GACTU/399-1016-1-ND/411291) | 82571 |  | $0.00 | $0.00 | 80-C0402C270J5G | Link (http://www.mouser.com/Search/../ProductDetail/Kemet/C0402C270J5GACTU/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) | 10980 |  | $0.00 | $0.00 | 01J3306 | Link (http://www.newark.com/kemet/c0402c270j5gactu/ceramic-capacitor-27pf-50v-c0g/dp/01J3306)
Y1 | 000003V1RA | CRYSTAL 8.0000MHZ 20PF SMD | FQ7050 | Fox Electronics | FQ7050B-8.000 | 0 | $0.00 | $0.00 | 5515 |  | $0.00 | $0.00 | 631-1029-1-ND | Link (http://www.digikey.com/product-detail/en/fox-electronics/FQ7050B-8.000/631-1029-1-ND/1024734) |  |  |  |  |  |  | 990 |  | $0.00 | $0.00 | 61T5363 | Link (http://www.newark.com/fox-electronics/fq7050b-8-000/crystal-8mhz-20pf-7-x-5mm/dp/61T5363)
U1 | 000002V1RA | MCU ARM 1024KB FLASH 144LQFP | LQFP_144 | STMicroelectronics | STM32F205ZGT6 | 0 | $0.00 | $0.00 | 339 |  | $0.00 | $0.00 | 497-11166-ND | Link (http://www.digikey.com/product-detail/en/stmicroelectronics/STM32F205ZGT6/497-11166-ND/2640812) | 333 |  | $0.00 | $0.00 | 511-STM32F205ZGT6 | Link (http://www.mouser.com/Search/../ProductDetail/STMicroelectronics/STM32F205ZGT6/) | 28 |  | $0.00 | $0.00 | 82T9688 | Link (http://www.newark.com/stmicroelectronics/stm32f205zgt6/32-bit-microcontroller-advanced/dp/82T9688)
C3,C4 | 000006V1RA | CAP CER 6PF 50V C0G 0402 | C_0402 | TDK Corporation | C1005C0G1H060D050BA | 0 | $0.00 | $0.00 | 294884 |  | $0.00 | $0.00 | 445-4885-1-ND | Link (http://www.digikey.com/product-detail/en/tdk-corporation/C1005C0G1H060D050BA/445-4885-1-ND/2093499) |  |  |  |  |  |  | 12497 |  | $0.00 | $0.00 | 04X3200 | Link (http://www.newark.com/tdk/c1005c0g1h060d050ba/ceramic-capacitor-6pf-50v-c0g/dp/04X3200)
J1 | 000007V1RA | CONN HEADER 20POS DUAL .05" SMD | FTSH-110-01-L-DV | Samtec | FTSH-110-01-L-DV | 0 | $0.00 | $0.00 | 0 |  | $0.00 | $0.00 | SAM1161-10-ND | Link (http://www.digikey.com/product-detail/en/samtec-inc/FTSH-110-01-L-DV/SAM1161-10-ND/1110217)
 |  |  |  |  |  |  |  |  |  | 0 | 0 | 0 |  |  |  | 0 | 0 | 0 |  |  |  | 0 | 0 | 0
 |  |  |  |  |  |  |  |  |  | 0 | 0 | 0 |  |  |  | 0 | 0 | 0 |  |  |  | 0 | 0 | 0
 |  |  |  |  |  |  |  |  |  | 0 | 0 | 0 |  |  |  | 0 | 0 | 0 |  |  |  | 0 | 0 | 0
 |  |  |  |  |  |  |  |  |  | 0 | 0 | 0 |  |  |  | 0 | 0 | 0 |  |  |  | 0 | 0 | 0
 |  |  |  |  |  |  |  |  |  | 0 | 0 | 0 |  |  |  | 0 | 0 | 0 |  |  |  | 0 | 0 | 0
 |  |  |  |  |  |  |  |  |  | 0 | 0 | 0 |  |  |  | 0 | 0 | 0 |  |  |  | 0 | 0 | 0
 |  |  |  |  |  |  |  |  |  | 0 | 0 | 0 |  |  |  | 0 | 0 | 0 |  |  |  | 0 | 0 | 0
