ciaa/Ponchos/ethernet_LAN8720A_v2/fabricacion1/ethernet_LAN8720A_v2.xlsx

 |  |  |  |  |  |  | Board Qty: | 5
 |  |  |  |  |  |  | Total Cost: | $62.37 |  |  |  | $63.32 |  |  |  |  |  | $58.12 |  |  |  |  |  | $0.00
 |  |  |  |  |  |  | Unit Cost: | $12.47
Global Part Info |  |  |  |  |  |  |  |  | Digi-Key |  |  |  |  |  | Mouser |  |  |  |  |  | Newark
Refs | Value | Desc | Footprint | Manf | Manf# | Qty | Unit$ | Ext$ | Avail | Purch | Unit$ | Ext$ | Cat# | Doc | Avail | Purch | Unit$ | Ext$ | Cat# | Doc | Avail | Purch | Unit$ | Ext$ | Cat# | Doc
U2 | 50MHZ | 50MHz HCMOS XO Standard Oscillator SMD 3.3V 30mA En/Dis | eth:Oscillator_7.0x5.0mm | Abracon LLC | ASV-50.000MHZ-E-T | 5 | $1.06 | $5.30 | 0 |  | $1.06 | $5.30 | 535-10087-1-ND | Link (http://www.digikey.com/scripts/DkSearch/dksus.dll?WT.z_header=search_go&lang=en) |  |  |  |  |  |  |  |  |  |  |  | Link (http://www.newark.com/webapp/wcs/stores/servlet/Search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)
P1 | SI-52003-F | RJ45 Magjack Connector TH 10/100 Base-T, AutoMDIX, PoE | eth:RJ45_SI-52003-F_PoE_ETH | Stewart Connector | SI-52003-F | 5 | $5.31 | $26.55 | 0 |  | $5.33 | $26.65 | 380-1119-ND | Link (http://www.digikey.com/scripts/DkSearch/dksus.dll?WT.z_header=search_go&lang=en) | 1336 |  | $5.31 | $26.55 | 530-SI-52003-F | Link (http://www.mouser.com/Search/Refine.aspx?Keyword=SI-52003-F%20Stewart%20Connector)
L1 | FBEAD 22 | FERRITE BEAD 22 OHM 0603 1LN | eth:SM0603 | Taiyo Yuden | BK1608HS220-T | 5 | $0.10 | $0.49 | 0 |  | $0.10 | $0.50 | 587-1869-1-ND | Link (http://www.digikey.com/scripts/DkSearch/dksus.dll?WT.z_header=search_go&lang=en) | 9709 |  | $0.10 | $0.49 | 963-BK1608HS220-T | Link (http://www.mouser.com/ProductDetail/Taiyo-Yuden/BK1608HS220-T/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) |  |  |  |  |  | Link (http://www.newark.com/taiyo-yuden/bk1608hs220-t/ferrite-bead-0-05ohm-1-5a-0603/dp/86H5390)
C4,C9,C10,C15 | 100nF | CAP CER 0,1UF 16V 10% X7R 0603 | eth:c_0603 | Kemet | C0603C104K4RACTU | 20 | $0.01 | $0.22 | 0 |  | $0.02 | $0.44 | 399-1096-1-ND | Link (http://www.digikey.com/scripts/DkSearch/dksus.dll?WT.z_header=search_go&lang=en) | 773538 |  | $0.01 | $0.22 | 80-C0603C104K4R | Link (http://www.mouser.com/ProductDetail/Kemet/C0603C104K4RACTU/) |  |  |  |  |  | Link (http://www.newark.com/kemet/c0603c104k4ractu/ceramic-capacitor-0-1uf-16v-x7r/dp/19C6005)
U1 | LAN8720A-CP | 4/4 Transceiver Full RMII 24-QFN (4x4) | eth:QFN24 | Microchip Technology | LAN8720A-CP-TR | 5 | $1.16 | $5.80 | 0 |  | $1.16 | $5.80 | LAN8720A-CP-DKR-ND | Link (http://www.digikey.com/scripts/DkSearch/dksus.dll?WT.z_header=search_go&lang=en) | 18619 |  | $1.37 | $6.85 | 886-LAN8720A-CP-TR | Link (http://www.mouser.com/ProductDetail/Microchip-Technology/LAN8720A-CP-TR/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)
XA1 | Conn_Poncho2P_2x_20x2 | 40P Header BTB Conn Gold 50mils 1.27mmTHole | eth:Conn_Poncho_Izquierdo | Harwin | M50-3502042 | 5 | $3.30 | $16.50 | 0 |  | $3.82 | $19.10 | 952-1387-ND | Link (http://www.digikey.com/scripts/DkSearch/dksus.dll?WT.z_header=search_go&lang=en) | 224 |  | $3.30 | $16.50 | 855-M50-3502042 | Link (http://www.mouser.com/Search/Refine.aspx?Keyword=M50-3502042%20Harwin) |  |  |  |  |  | Link (http://www.newark.com/webapp/wcs/stores/servlet/Search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)
R10-R12 | 22 | RES 22 OHM 1/10W 5% | eth:SM0603_Resistor | Yageo | RC0603JR-0722RL | 15 | $0.01 | $0.12 | 0 |  | $0.01 | $0.17 | 311-22GRCT-ND | Link (http://www.digikey.com/scripts/DkSearch/dksus.dll?WT.z_header=search_go&lang=en) | 53758 |  | $0.01 | $0.12 | 603-RC0603JR-0722RL | Link (http://www.mouser.com/Search/Refine.aspx?Keyword=RC0603JR-0722RL%20Yageo) |  |  |  |  |  | Link (http://www.newark.com/yageo/rc0603jr-0722rl/res-thick-film-22r-5-0-1w-0603/dp/68R0168)
MH1,MH2 | MOUNTING-HOLE |  | eth:MountingHole_2.2mm_M2_Pad |  |  | 10 | $0.00 | $0.00
C11-C14 | 18pF | CAP CER 18PF 50V 5% NP0 0603 | eth:c_0603 | Kemet | C0603C180J5GACTU | 20 | $0.02 | $0.42 | 0 |  | $0.03 | $0.68 | 399-1052-1-ND | Link (http://www.digikey.com/scripts/DkSearch/dksus.dll?WT.z_header=search_go&lang=en) | 106719 |  | $0.02 | $0.42 | 80-C0603C180J5G | Link (http://www.mouser.com/ProductDetail/Kemet/C0603C180J5GACTU/?qs=sGAEpiMZZMs0AnBnWHyRQJIiGvDVk92VyAyEaQH0tQM%3D) |  |  |  |  |  | Link (http://www.newark.com/kemet/c0603c180j5gactu/ceramic-capacitor-18pf-50v-c0g/dp/64K2845)
R3-R6 | 49,9 1% | RES 49,9 OHM 1/10W 1% 0603 SMD | eth:SM0603_Resistor | Yageo | RC0603FR-0749R9L | 20 | $0.01 | $0.20 | 0 |  | $0.01 | $0.28 | 311-49.9HRCT-ND | Link (http://www.digikey.com/scripts/DkSearch/dksus.dll?WT.z_header=search_go&lang=en) | 441325 |  | $0.01 | $0.20 | 603-RC0603FR-0749R9L | Link (http://www.mouser.com/Search/Refine.aspx?Keyword=RC0603FR-0749R9L%20Yageo) |  |  |  |  |  | Link (http://www.newark.com/yageo/rc0603fr-0749r9l/res-thick-film-49r9-1-0-1w-0603/dp/68R0100)
R7-R9,R13,R14,R24 | 0 | RES SMD 0.0OHM JUMPER 1/10W 0603 | eth:SM0603_Resistor | Bourns | CR0603-J/-000ELF | 30 | $0.02 | $0.48 | 0 |  | $0.02 | $0.62 | CR0603-J/-000ELFCT-ND | Link (http://www.digikey.com/scripts/DkSearch/dksus.dll?WT.z_header=search_go&lang=en) | 28611 |  | $0.02 | $0.48 | 652-CR0603-J/-000ELF | Link (http://www.mouser.com/Search/Refine.aspx?Keyword=CR0603-J%2F-000ELF%20Bourns) |  |  |  |  |  | Link (http://www.newark.com/bourns/cr0603-j-000elf/res-thick-film-0r-5-0-1w-0603/dp/02J2264)
R17,R18 | 270 | RES 270 OHM 1/10W 5% 0603 SMD | eth:SM0603_Resistor | Yageo | RC0603JR-07270RL | 10 | $0.01 | $0.08 | 0 |  | $0.01 | $0.11 | 311-270GRCT-ND | Link (http://www.digikey.com/scripts/DkSearch/dksus.dll?WT.z_header=search_go&lang=en) | 128118 |  | $0.01 | $0.08 | 603-RC0603JR-07270RL | Link (http://www.mouser.com/Search/Refine.aspx?Keyword=RC0603JR-07270RL%20Yageo) |  |  |  |  |  | Link (http://www.newark.com/yageo/rc0603jr-07270rl/res-thick-film-270r-5-0-1w-0603/dp/68R0174)
C2,C3,C6 | 10nF | CAP CER 10000PF 50V 10% X7R 0603 | eth:c_0603 | Kemet | C0603C103K5RACTU | 15 | $0.01 | $0.18 | 0 |  | $0.02 | $0.28 | 399-1091-1-ND | Link (http://www.digikey.com/scripts/DkSearch/dksus.dll?WT.z_header=search_go&lang=en) | 492244 |  | $0.01 | $0.18 | 80-C0603C103K5R | Link (http://www.mouser.com/ProductDetail/Kemet/C0603C103K5RACTU/) |  |  |  |  |  | Link (http://www.newark.com/kemet/c0603c103k5ractu/ceramic-capacitor-0-01uf-50v-x7r/dp/30C5334)
R2,R15,R16 | 10k | RES 10K OHM 1/10W 5% 0603 SMD | eth:SM0603_Resistor | Yageo | RC0603JR-0710KL | 15 | $0.01 | $0.12 | 0 |  | $0.01 | $0.17 | 311-10KGRCT-ND | Link (http://www.digikey.com/scripts/DkSearch/dksus.dll?WT.z_header=search_go&lang=en) | 580450 |  | $0.01 | $0.12 | 603-RC0603JR-0710KL | Link (http://www.mouser.com/Search/Refine.aspx?Keyword=RC0603JR-0710KL%20Yageo) |  |  |  |  |  | Link (http://www.newark.com/yageo/rc0603jr-0710kl/res-thick-film-10k-5-0-1w-0603/dp/68R0144)
FID1-FID3 | FIDUCIAL |  | eth:Fiducial_1mm_Dia_2.54mm_Outer_CopperTop |  |  | 15 | $0.00 | $0.00
R20,R22,R23 | 33 | RES 33 OHM 1/10W 5% 0603 SMD | eth:SM0603_Resistor | Bourns | CR0603-JW-330GLF | 15 | $0.02 | $0.24 | 0 |  | $0.03 | $0.43 | CR0603-JW-330GLFCT-ND | Link (http://www.digikey.com/scripts/DkSearch/dksus.dll?WT.z_header=search_go&lang=en) | 24290 |  | $0.02 | $0.24 | 652-CR0603-JW-330GLF | Link (http://www.mouser.com/Search/Refine.aspx?Keyword=CR0603-JW-330GLF%20Bourns) |  |  |  |  |  | Link (http://www.newark.com/webapp/wcs/stores/servlet/Search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)
C8 | 1uF | CAP CER 1UF 16V 10% X7R 0603 | eth:c_0603 | Kemet | C0603C105K4RACTU | 5 | $0.20 | $0.98 | 0 |  | $0.20 | $1.00 | 399-7847-1-ND | Link (http://www.digikey.com/scripts/DkSearch/dksus.dll?WT.z_header=search_go&lang=en) | 113232 |  | $0.20 | $0.98 | 80-C0603C105K4R | Link (http://www.mouser.com/ProductDetail/Kemet/C0603C105K4RACTU/) |  |  |  |  |  | Link (http://www.newark.com/kemet/c0603c105k4ractu/ceramic-capacitor-1uf-16v-x7r/dp/93K5997)
P3 | PoE | 8 Pin Header Conn Gold 50 mils 1.27mm THole | eth:PIN_ARRAY_4X2 |  |  | 5 | $0.00 | $0.00
C1,C5,C16 | 10uF | CAP TANT 10UF 6.3V 10% 1206 | eth:c_1206_tantalio_1 | Kemet | T491A106K006AT7280 | 15 | $0.20 | $3.03 |  |  |  |  |  |  | 15041 |  | $0.20 | $3.03 | 80-T491A106K0067280 | Link (http://www.mouser.com/Search/Refine.aspx?Keyword=T491A106K006AT7280%20Kemet) |  |  |  |  |  | Link (http://www.newark.com/webapp/wcs/stores/servlet/Search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)
JP1 | JUMPER3 |  | Oddities:NetTie-II_SMD |  |  | 5 | $0.00 | $0.00
R21,R25 | 100k | RES SMD 100K OHM 5% 1/10W 0603 | eth:SM0603_Resistor | Bourns | CR0603-JW-104ELF | 10 | $0.02 | $0.16 | 0 |  | $0.03 | $0.29 | CR0603-JW-104ELFCT-ND | Link (http://www.digikey.com/scripts/DkSearch/dksus.dll?WT.z_header=search_go&lang=en) | 74309 |  | $0.02 | $0.16 | 652-CR0603-JW-104ELF | Link (http://www.mouser.com/Search/Refine.aspx?Keyword=CR0603-JW-104ELF%20Bourns) |  |  |  |  |  | Link (http://www.newark.com/bourns/cr0603-jw-104elf/res-thick-film-100k-5-0-1w-0603/dp/02J2288)
C7 | 470pF | CAP CER 470PF 50V 10% X7R 0603 | eth:c_0603 | Kemet | C0603C471K5RACTU | 5 | $0.10 | $0.49 | 0 |  | $0.10 | $0.50 | 399-1075-1-ND | Link (http://www.digikey.com/scripts/DkSearch/dksus.dll?WT.z_header=search_go&lang=en) | 39756 |  | $0.10 | $0.49 | 80-C0603C471K5R | Link (http://www.mouser.com/ProductDetail/Kemet/C0603C471K5RACTU/) |  |  |  |  |  | Link (http://www.newark.com/kemet/c0603c471k5ractu/ceramic-capacitor-470pf-50v-x7r/dp/30C5318)
R1 | 1k5 | RES 1.5K OHM 1/10W 5% 0603 SMD | eth:SM0603_Resistor | Yageo | RC0603JR-071K5L | 5 | $0.10 | $0.49 | 0 |  | $0.10 | $0.50 | 311-1.5KGRCT-ND | Link (http://www.digikey.com/scripts/DkSearch/dksus.dll?WT.z_header=search_go&lang=en) | 54734 |  | $0.10 | $0.49 | 603-RC0603JR-071K5L | Link (http://www.mouser.com/Search/Refine.aspx?Keyword=RC0603JR-071K5L%20Yageo) |  |  |  |  |  | Link (http://www.newark.com/yageo/rc0603jr-071k5l/res-thick-film-1k5-5-0-1w-0603/dp/68R0139)
R19 | 12.1k 1% | RES SMD 12.1K OHM 1% 1/10W 0603 | eth:SM0603_Resistor | Yageo | RC0603FR-0712K1L | 5 | $0.10 | $0.49 | 0 |  | $0.10 | $0.50 | 311-12.1KHRCT-ND | Link (http://www.digikey.com/scripts/DkSearch/dksus.dll?WT.z_header=search_go&lang=en) | 115896 |  | $0.10 | $0.49 | 603-RC0603FR-0712K1L | Link (http://www.mouser.com/Search/Refine.aspx?Keyword=RC0603FR-0712K1L%20Yageo) |  |  |  |  |  | Link (http://www.newark.com/yageo/rc0603fr-0712k1l/res-thick-film-12k1-1-0-1w-0603/dp/68R0055)
