ciaa/Ponchos/Simon/tools/kicost-0.1.25/tests/Indium_X2.xlsx

 |  |  |  |  |  |  | Board Qty: | 100
 |  |  |  |  |  |  | Total Cost: | $0.00 |  |  |  | $0.00 |  |  |  |  |  | $0.00 |  |  |  |  |  | $0.00
 |  |  |  |  |  |  | Unit Cost: | $0.00
Global Part Info |  |  |  |  |  |  |  |  | Digi-Key |  |  |  |  |  | Mouser |  |  |  |  |  | Newark
Refs | Value | Desc | Footprint | Manf | Manf# | Qty | Unit$ | Ext$ | Avail | Purch | Unit$ | Ext$ | Cat# | Doc | Avail | Purch | Unit$ | Ext$ | Cat# | Doc | Avail | Purch | Unit$ | Ext$ | Cat# | Doc
R1,R26,R60,R61 | 0 |  | Footprints:SM0402_r_YDF | Yageo | RC0402JR-070RL | 0 | $0.00 | $0.00 | 8962 |  | $0.00 | $0.00 | 311-0.0JRCT-ND | Link (http://www.digikey.com/product-detail/en/RC0402JR-070RL/311-0.0JRCT-ND/729353) |  |  |  |  |  |  | 4259 |  | $0.00 | $0.00 | 67R9963 | Link (http://www.newark.com/yageo/rc0402jr-070rl/res-thick-film-0r-0-0625w-0402/dp/67R9963)
J5 | MOLEX_TH_USB |  | Footprints:MOLEX-MINIB-USB-TH | Molex | 500075-1517 | 0 | $0.00 | $0.00 | 5256 |  | $0.00 | $0.00 | WM2072-ND | Link (http://www.digikey.com/scripts/DkSearch/dksus.dll?WT.z_header=search_go&lang=en&keywords=500075-1517) |  |  |  |  |  |  | 673 |  | $0.00 | $0.00 | 93K4120 | Link (http://www.newark.com/webapp/wcs/stores/servlet/Search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)
R2,R25 | 4.7k |  | Footprints:SM0402_r_YDF | Panasonic | ERJ-2RKF4701X | 0 | $0.00 | $0.00 | 3654012 |  | $0.00 | $0.00 | P4.70KLCT-ND | Link (http://www.digikey.com/product-detail/en/ERJ-2RKF4701X/P4.70KLCT-ND/1746692) |  |  |  |  |  |  | 9015 |  | $0.00 | $0.00 | 64R5288 | Link (http://www.newark.com/panasonic-electronic-components/erj-2rkf4701x/res-thick-film-4k7-1-0-1w-0402/dp/64R5288)
R69 | 1M | NO-INSTALL | Footprints:SM0805_YDF_Sunnee |  |  | 0 | $0.00 | $0.00
C35,C37 | 0.1 uF |  | Footprints:SM0402_c_YDF_Sunnee | TDK | C1005X7R1E104K050BB | 0 | $0.00 | $0.00 | 661941 |  | $0.00 | $0.00 | 445-7348-1-ND | Link (http://www.digikey.com/product-detail/en/C1005X7R1E104K050BB/445-7348-1-ND/2733420) |  |  |  |  |  |  | 59214 |  | $0.00 | $0.00 | 04X3227 | Link (http://www.newark.com/tdk/c1005x7r1e104k050bb/ceramic-capacitor-0-1uf-25v-x7r/dp/04X3227)
R27,R53-R55 | 0 | NO-INSTALL | Footprints:SM0402_r_YDF |  |  | 0 | $0.00 | $0.00
R8 | 100k | NO-INSTALL | Footprints:SM0402_r_YDF |  |  | 0 | $0.00 | $0.00
U6 | LP3982IMMX-3.3 |  | Footprints:LP3982-VSSOP8 | TI | LP3982IMM-3.3/NOPB | 0 | $0.00 | $0.00 | 4186 |  | $0.00 | $0.00 | LP3982IMM-3.3/NOPBCT-ND | Link (http://www.digikey.com/product-detail/en/LP3982IMM-3.3%2FNOPB/LP3982IMM-3.3%2FNOPBCT-ND/570192) |  |  |  |  |  |  | 809 |  | $0.00 | $0.00 | 41K7927 | Link (http://www.newark.com/texas-instruments/lp3982imm-3-3-nopb/ldo-voltage-regulator-3-3v-0-3a/dp/41K7927)
C10,C16,C18,C20,C21 | 10 uF |  | Footprints:SM0603_Capa_ydf_sunnee | Samsung | CL10A106MQ8NNNC | 0 | $0.00 | $0.00 | 527190 |  | $0.00 | $0.00 | 1276-1119-1-ND | Link (http://www.digikey.com/product-detail/en/CL10A106MQ8NNNC/1276-1119-1-ND/3889205) |  |  |  |  |  |  | 7294 |  | $0.00 | $0.00 | 30K5476 | Link (http://www.newark.com/taiyo-yuden/jmk107bj106ma-t/ceramic-capacitor-10uf-6-3v-x5r/dp/30K5476)
R22,R70 | 1M |  | Footprints:SM0805_YDF_Sunnee |  |  | 0 | $0.00 | $0.00
R28 | 330 |  | Footprints:SM0402_r_YDF | Yageo | RC0402FR-07330RL | 0 | $0.00 | $0.00 | 584902 |  | $0.00 | $0.00 | 311-330LRCT-ND | Link (http://www.digikey.com/product-detail/en/RC0402FR-07330RL/311-330LRCT-ND/729541) |  |  |  |  |  |  | 18162 |  | $0.00 | $0.00 | 67R9927 | Link (http://www.newark.com/yageo/rc0402fr-07330rl/res-thick-film-330r-1-0-0625w/dp/67R9927)
R3 | 0.05 |  | Footprints:SM0805_YDF_Sunnee | Vishay Dale | CRCW08050000Z0EAHP | 0 | $0.00 | $0.00 | 131833 |  | $0.00 | $0.00 | 541-0.0TBCT-ND | Link (http://www.digikey.com/product-detail/en/CRCW08050000Z0EAHP/541-0.0TBCT-ND/2222831) |  |  |  |  |  |  | 4271 |  | $0.00 | $0.00 | 68R2993 | Link (http://www.newark.com/vishay-dale/crcw08050000z0eahp/res-thick-film-0r-0-33w-0805/dp/68R2993)
C13 | 0.1 uF |  | Footprints:SM0603_Capa_ydf_sunnee | Taiyo-Yuden | TMK107BJ104KA-T | 0 | $0.00 | $0.00 | 552319 |  | $0.00 | $0.00 | 587-1245-1-ND | Link (http://www.digikey.com/product-detail/en/TMK107BJ104KA-T/587-1245-1-ND/931022) |  |  |  |  |  |  | 2283 |  | $0.00 | $0.00 | 86H5300 | Link (http://www.newark.com/taiyo-yuden/tmk107bj104ka-t/ceramic-capacitor-0-1uf-25v-x5r/dp/86H5300)
J6 | CONN_4 |  | Footprints:HIROSE_FH19C_YDF_Sunnee | Hirose | FH19C-4S-0.5SH(05) | 0 | $0.00 | $0.00 | 18103 |  | $0.00 | $0.00 | HFN404CT-ND | Link (http://www.digikey.com/product-detail/en/FH19C-4S-0.5SH(05)/HFN404CT-ND/1124164) |  |  |  |  |  |  | 740 |  | $0.00 | $0.00 | 68X2657 | Link (http://www.newark.com/webapp/wcs/stores/servlet/Search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)
R6,R9,R21 | 100k |  | Footprints:SM0402_r_YDF | Yageo | RC0402FR-07100KL | 0 | $0.00 | $0.00 | 2726770 |  | $0.00 | $0.00 | 311-100KLRCT-ND | Link (http://www.digikey.com/product-detail/en/RC0402FR-07100KL/311-100KLRCT-ND/729473) |  |  |  |  |  |  | 8084 |  | $0.00 | $0.00 | 67R9887 | Link (http://www.newark.com/yageo/rc0402fr-07100kl/res-thick-film-100k-1-0-0625w/dp/67R9887)
R62,R64 | 330 | NO-INSTALL | Footprints:SM0402_r_YDF |  |  | 0 | $0.00 | $0.00
U7 | MCP98243-BE/ST |  | Footprints:SOIC8_MICROCHIP_YDF | Microchip | MCP98243-BE/ST | 0 | $0.00 | $0.00 | 5454 |  | $0.00 | $0.00 | MCP98243-BE/ST-ND | Link (http://www.digikey.com/scripts/DkSearch/dksus.dll?WT.z_header=search_go&lang=en) |  |  |  |  |  |  | 0 |  | $0.00 | $0.00 | 14R8886 | Link (http://www.newark.com/webapp/wcs/stores/servlet/Search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)
C12 | 22 pF |  | Footprints:SM0402_c_YDF_Sunnee | Yaego | CC0402JRNPO9BN220 | 0 | $0.00 | $0.00 | 1195324 |  | $0.00 | $0.00 | 311-1018-1-ND | Link (http://www.digikey.com/product-detail/en/CC0402JRNPO9BN220/311-1018-1-ND/302935) |  |  |  |  |  |  | 27677 |  | $0.00 | $0.00 | 68R4606 | Link (http://www.newark.com/yageo/cc0402jrnpo9bn220/ceramic-capacitor-22pf-50v-c0g/dp/68R4606)
D2 | RED |  | Footprints:LED-0603_YDF_Sunnee | Lumex Opto | SML-LX0603SRW-TR | 0 | $0.00 | $0.00 | 116455 |  | $0.00 | $0.00 | 67-1551-1-ND | Link (http://www.digikey.com/product-detail/en/SML-LX0603SRW-TR/67-1551-1-ND/304364) |  |  |  |  |  |  | 2218 |  | $0.00 | $0.00 | 09J9551 | Link (http://www.newark.com/lumex/sml-lx0603srw-tr/led-red-0-8mm-x-1mm-45mcd-660nm/dp/09J9551)
R30,R32,R52 | 10k | NO-INSTALL | Footprints:SM0402_r_YDF |  |  | 0 | $0.00 | $0.00
C19 | 0.033 uF |  | Footprints:SM0402_c_YDF_Sunnee | Kemet | C0402C333K4RACTU | 0 | $0.00 | $0.00 | 8812 |  | $0.00 | $0.00 | 399-4891-1-ND | Link (http://www.digikey.com/product-detail/en/C0402C333K4RACTU/399-4891-1-ND/1090886) |  |  |  |  |  |  | 8529 |  | $0.00 | $0.00 | 53M7167 | Link (http://www.newark.com/webapp/wcs/stores/servlet/Search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)
U9 | 24AA128ISN |  | Footprints:SO8_YDF | Microchip | 24AA128ISN | 0 | $0.00 | $0.00 | 2132 |  | $0.00 | $0.00 | 24AA128-I/SN-ND | Link (http://www.digikey.com/product-detail/en/24AA128-I%2FSN/24AA128-I%2FSN-ND/442845) |  |  |  |  |  |  | 0 |  | $0.00 | $0.00 | 92C6842 | Link (http://www.newark.com/webapp/wcs/stores/servlet/Search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)
C5,C7 | 8 pF |  | Footprints:SM0402_c_YDF_Sunnee | TDK | C1005C0G1H040B050BA | 0 | $0.00 | $0.00 | 32770 |  | $0.00 | $0.00 | 445-4876-1-ND | Link (http://www.digikey.com/product-detail/en/C1005C0G1H040B050BA/445-4876-1-ND/2093490) |  |  |  |  |  |  | 8538 |  | $0.00 | $0.00 | 91R0018 | Link (http://www.newark.com/webapp/wcs/stores/servlet/Search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)
R23,R24,R31,R33,R47 | 10k |  | Footprints:SM0402_r_YDF | Yageo | RC0402FR-0710KL | 0 | $0.00 | $0.00 | 4805602 |  | $0.00 | $0.00 | 311-10.0KLRCT-ND | Link (http://www.digikey.com/product-detail/en/RC0402FR-0710KL/311-10.0KLRCT-ND/729470) |  |  |  |  |  |  | 3711 |  | $0.00 | $0.00 | 67R9884 | Link (http://www.newark.com/yageo/rc0402fr-0710kl/res-thick-film-10k-1-0-0625w-0402/dp/67R9884)
DH1-DH4 | YDF_TAU_HOLE | NO-INSTALL | Footprints:YDF_TAU_HOLE |  |  | 0 | $0.00 | $0.00
R20 | 1M |  | Footprints:SM0402_r_YDF | Yageo | RC0402FR-071ML | 0 | $0.00 | $0.00 | 2977544 |  | $0.00 | $0.00 | 311-1.00MLRCT-ND | Link (http://www.digikey.com/product-detail/en/RC0402FR-071ML/311-1.00MLRCT-ND/729462) |  |  |  |  |  |  | 4241 |  | $0.00 | $0.00 | 67R9882 | Link (http://www.newark.com/yageo/rc0402fr-071ml/res-thick-film-1m-1-0-0625w-0402/dp/67R9882)
C4,C6,C14,C15,C26-C29,C32 | 0.1 uF |  | Footprints:SM0402_c_YDF_Sunnee | Taiyo-Yuden | LMK105BJ104KV-F | 0 | $0.00 | $0.00 | 31891785 |  | $0.00 | $0.00 | 587-1227-1-ND | Link (http://www.digikey.com/product-detail/en/LMK105BJ104KV-F/587-1227-1-ND/931004) |  |  |  |  |  |  | 10870 |  | $0.00 | $0.00 | 86H5618 | Link (http://www.newark.com/taiyo-yuden/lmk105bj104kv-f/ceramic-capacitor-0-1uf-10v-x5r/dp/86H5618)
C17 | 4700 pF |  | Footprints:SM1812 | Murata | GA343DR7GD472KW01L | 0 | $0.00 | $0.00 | 17748 |  | $0.00 | $0.00 | 490-3493-1-ND | Link (http://www.digikey.com/product-detail/en/GA343DR7GD472KW01L/490-3493-1-ND/789327) |  |  |  |  |  |  | 2198 |  | $0.00 | $0.00 | 31Y1700 | Link (http://www.newark.com/webapp/wcs/stores/servlet/Search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)
TP3,TP4 | TESTPOINT | NO-INSTALL | Footprints:TESTPOINT2 |  |  | 0 | $0.00 | $0.00
C1,C30,C31 | 2.2 uF |  | Footprints:SM0603_Capa_ydf_sunnee | Taiyo-Yuden | JMK107BJ225KA-T | 0 | $0.00 | $0.00 | 104518 |  | $0.00 | $0.00 | 587-1254-1-ND | Link (http://www.digikey.com/product-detail/en/JMK107BJ225KA-T/587-1254-1-ND/931031) |  |  |  |  |  |  | 2448 |  | $0.00 | $0.00 | 86H5268 | Link (http://www.newark.com/taiyo-yuden/jmk107bj225ka-t/ceramic-capacitor-2-2uf-6-3v-x5r/dp/86H5268)
 |  |  |  |  |  |  |  |  |  | 0 | 0 | 0 |  |  |  | 0 | 0 | 0 |  |  |  | 0 | 0 | 0
 |  |  |  |  |  |  |  |  |  | 0 | 0 | 0 |  |  |  | 0 | 0 | 0 |  |  |  | 0 | 0 | 0
 |  |  |  |  |  |  |  |  |  | 0 | 0 | 0 |  |  |  | 0 | 0 | 0 |  |  |  | 0 | 0 | 0
 |  |  |  |  |  |  |  |  |  | 0 | 0 | 0 |  |  |  | 0 | 0 | 0 |  |  |  | 0 | 0 | 0
 |  |  |  |  |  |  |  |  |  | 0 | 0 | 0 |  |  |  | 0 | 0 | 0 |  |  |  | 0 | 0 | 0
 |  |  |  |  |  |  |  |  |  | 0 | 0 | 0 |  |  |  | 0 | 0 | 0 |  |  |  | 0 | 0 | 0
 |  |  |  |  |  |  |  |  |  | 0 | 0 | 0 |  |  |  | 0 | 0 | 0 |  |  |  | 0 | 0 | 0
 |  |  |  |  |  |  |  |  |  | 0 | 0 | 0 |  |  |  | 0 | 0 | 0 |  |  |  | 0 | 0 | 0
 |  |  |  |  |  |  |  |  |  | 0 | 0 | 0 |  |  |  | 0 | 0 | 0 |  |  |  | 0 | 0 | 0
 |  |  |  |  |  |  |  |  |  | 0 | 0 | 0 |  |  |  | 0 | 0 | 0 |  |  |  | 0 | 0 | 0
 |  |  |  |  |  |  |  |  |  | 0 | 0 | 0 |  |  |  | 0 | 0 | 0 |  |  |  | 0 | 0 | 0
 |  |  |  |  |  |  |  |  |  | 0 | 0 | 0 |  |  |  | 0 | 0 | 0 |  |  |  | 0 | 0 | 0
 |  |  |  |  |  |  |  |  |  | 0 | 0 | 0 |  |  |  | 0 | 0 | 0 |  |  |  | 0 | 0 | 0
 |  |  |  |  |  |  |  |  |  | 0 | 0 | 0 |  |  |  | 0 | 0 | 0 |  |  |  | 0 | 0 | 0
 |  |  |  |  |  |  |  |  |  | 0 | 0 | 0 |  |  |  | 0 | 0 | 0 |  |  |  | 0 | 0 | 0
 |  |  |  |  |  |  |  |  |  | 0 | 0 | 0 |  |  |  | 0 | 0 | 0 |  |  |  | 0 | 0 | 0
 |  |  |  |  |  |  |  |  |  | 0 | 0 | 0 |  |  |  | 0 | 0 | 0 |  |  |  | 0 | 0 | 0
 |  |  |  |  |  |  |  |  |  | 0 | 0 | 0 |  |  |  | 0 | 0 | 0 |  |  |  | 0 | 0 | 0
 |  |  |  |  |  |  |  |  |  | 0 | 0 | 0 |  |  |  | 0 | 0 | 0 |  |  |  | 0 | 0 | 0
 |  |  |  |  |  |  |  |  |  | 0 | 0 | 0 |  |  |  | 0 | 0 | 0 |  |  |  | 0 | 0 | 0
 |  |  |  |  |  |  |  |  |  | 0 | 0 | 0 |  |  |  | 0 | 0 | 0 |  |  |  | 0 | 0 | 0
 |  |  |  |  |  |  |  |  |  | 0 | 0 | 0 |  |  |  | 0 | 0 | 0 |  |  |  | 0 | 0 | 0
 |  |  |  |  |  |  |  |  |  | 0 | 0 | 0 |  |  |  | 0 | 0 | 0 |  |  |  | 0 | 0 | 0
 |  |  |  |  |  |  |  |  |  | 0 | 0 | 0 |  |  |  | 0 | 0 | 0 |  |  |  | 0 | 0 | 0
 |  |  |  |  |  |  |  |  |  | 0 | 0 | 0 |  |  |  | 0 | 0 | 0 |  |  |  | 0 | 0 | 0
 |  |  |  |  |  |  |  |  |  | 0 | 0 | 0 |  |  |  | 0 | 0 | 0 |  |  |  | 0 | 0 | 0
 |  |  |  |  |  |  |  |  |  | 0 | 0 | 0 |  |  |  | 0 | 0 | 0 |  |  |  | 0 | 0 | 0
 |  |  |  |  |  |  |  |  |  | 0 | 0 | 0 |  |  |  | 0 | 0 | 0 |  |  |  | 0 | 0 | 0
 |  |  |  |  |  |  |  |  |  | 0 | 0 | 0 |  |  |  | 0 | 0 | 0 |  |  |  | 0 | 0 | 0
 |  |  |  |  |  |  |  |  |  | 0 | 0 | 0 |  |  |  | 0 | 0 | 0 |  |  |  | 0 | 0 | 0
