ciaa/Ponchos/WifiBT_CESE_ESPWROOM32/PonchoEDUCIAA_WIFI_BLT.xlsx

 |  |  |  |  |  |  | Board Qty: | 100
 |  |  |  |  |  |  | Total Cost: | $0.00 |  |  |  | $0.00 |  |  |  |  |  | $0.00 |  |  |  |  |  | $0.00 |  |  |  |  |  | $0.00 |  |  |  |  |  | $0.00
 |  |  |  |  |  |  | Unit Cost: | $0.00
Global Part Info |  |  |  |  |  |  |  |  | Digi-Key |  |  |  |  |  | Farnell |  |  |  |  |  | Mouser |  |  |  |  |  | Newark |  |  |  |  |  | Rs Components
Refs | Value | Desc | Footprint | Manf | Manf# | Qty | Unit$ | Ext$ | Avail | Purch | Unit$ | Ext$ | Cat# | Doc | Avail | Purch | Unit$ | Ext$ | Cat# | Doc | Avail | Purch | Unit$ | Ext$ | Cat# | Doc | Avail | Purch | Unit$ | Ext$ | Cat# | Doc | Avail | Purch | Unit$ | Ext$ | Cat# | Doc
U1 | ESP32-WROOM | TXRX MOD BLE WIFI ESP-WROOM-32 | PonchoEDUCIAA_WIFI_BLTH:ESP32-WROOM | Adafruit Industries LLC | 3320 | 0 | $0.00 | $0.00 | 5 |  | $0.00 | $0.00 | 1528-1801-ND | Link (http://www.digikey.com/scripts/DkSearch/dksus.dll?WT.z_header=search_go&lang=en) |  |  | $0.00 | $0.00 | 1654363 | Link (http://it.farnell.com/capital-advanced/33205/adattatore-ic-sot23-5-sc59-5/dp/1654363) | 39 |  | $0.00 | $0.00 | 485-3320 | Link (http://www.mouser.com/Search/Refine.aspx?Keyword=485-3320%20) |  |  |  |  | 92N3664 | Link (http://www.newark.com/aven/3320/scissor-kevlar-5in/dp/92N3664) | 60 |  |  |  | 463-151 | Link (http://it.rs-online.com/web/p/amplificatori-operazionali/0463151/)
XA1 | Conn_Poncho2P_2x_20x2 | CONN HDR 1.27MM VERT AU 20POS | PonchoEDUCIAA_WIFI_BLTH:Conn_Poncho_Derecha | Harwin Inc. | M50-3501042 | 0 | $0.00 | $0.00 | 2297 |  | $0.00 | $0.00 | 952-1386-ND | Link (http://www.digikey.com/scripts/DkSearch/dksus.dll?WT.z_header=search_go&lang=en) |  |  | $0.00 | $0.00 | 1022306 | Link (http://it.farnell.com/webapp/wcs/stores/servlet/Search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.) | 3483 |  | $0.00 | $0.00 | 855-M50-3501042 | Link (http://www.mouser.com/Search/Refine.aspx?Keyword=855-M50-3501042%20Harwin%20Inc.) |  |  | $0.00 | $0.00 | 74K2300 | Link (http://www.newark.com/webapp/wcs/stores/servlet/Search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.) | 57 |  | $0.00 | $0.00 | 681-1193 | Link (http://it.rs-online.com/web/p/file-di-contatti-da-pcb/6811193/)
R1,R4,R5 | 402 | RES SMD 402 OHM 1% 1/8W 0805 | Resistors_SMD:R_0805_HandSoldering | Yageo | RC0805FR-07402RL | 0 | $0.00 | $0.00 | 161830 |  | $0.00 | $0.00 | 311-402CRCT-ND | Link (http://www.digikey.com/scripts/DkSearch/dksus.dll?WT.z_header=search_go&lang=en) |  |  |  |  |  |  | 47264 |  | $0.00 | $0.00 | 603-RC0805FR-07402RL | Link (http://www.mouser.com/Search/Refine.aspx?Keyword=603-RC0805FR-07402RL%20) |  |  | $0.00 | $0.00 | 66R3296 | Link (http://www.newark.com/webapp/wcs/stores/servlet/Search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)
D2 | LED_Verde | LED GREEN DIFFUSED 0805 SMD | LEDs:LED_0805 | OSRAM Opto Semiconductors Inc. | LG R971-KN-1 | 0 | $0.00 | $0.00 | 561662 |  | $0.00 | $0.00 | 475-1410-1-ND | Link (http://www.digikey.com/scripts/DkSearch/dksus.dll?WT.z_header=search_go&lang=en) |  |  |  |  |  |  | 330836 |  | $0.00 | $0.00 | 720-LGR971-KN-1 | Link (http://www.mouser.com/Search/../ProductDetail/OSRAM-Opto-Semiconductors/LG-R971-KN-1/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) |  |  |  |  |  |  | 26300 |  | $0.00 | $0.00 | 418-044 | Link (http://it.rs-online.com/web/c/?searchTerm=LG%20R971-KN-1%20OSRAM%20Opto%20Semiconductors%20Inc.)
D3 | LED_Amarillo | LED YELLOW DIFFUSED 0805 SMD | LEDs:LED_0805 | OSRAM Opto Semiconductors Inc. | LY R976-PS-36 | 0 | $0.00 | $0.00 | 245886 |  | $0.00 | $0.00 | 475-2560-1-ND | Link (http://www.digikey.com/scripts/DkSearch/dksus.dll?WT.z_header=search_go&lang=en) |  |  |  |  |  |  | 66042 |  | $0.00 | $0.00 | 720-LYR976-PS-36 | Link (http://www.mouser.com/Search/Refine.aspx?Keyword=720-LYR976-PS-36%20)
D1 | LED_Rojo | LED RED DIFFUSED 0805 SMD | LEDs:LED_0805 | OSRAM Opto Semiconductors Inc. | LS R976-NR-1 | 0 | $0.00 | $0.00 | 283564 |  | $0.00 | $0.00 | 475-1278-1-ND | Link (http://www.digikey.com/scripts/DkSearch/dksus.dll?WT.z_header=search_go&lang=en) |  |  |  |  |  |  | 295516 |  | $0.00 | $0.00 | 720-LSR976-NR-1 | Link (http://www.mouser.com/Search/Refine.aspx?Keyword=720-LSR976-NR-1%20)
J1 | UART | CONN HEADER 3POS .100 VERT TIN | PonchoEDUCIAA_WIFI_BLTH:CON_PALETA_3 | Molex, LLC | 0022272031 | 0 | $0.00 | $0.00 | 42438 |  | $0.00 | $0.00 | WM4112-ND | Link (http://www.digikey.com/scripts/DkSearch/dksus.dll?WT.z_header=search_go&lang=en) |  |  | $0.00 | $0.00 | 9731156 | Link (http://it.farnell.com/webapp/wcs/stores/servlet/Search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) | 23619 |  | $0.00 | $0.00 | 538-22-27-2031 | Link (http://www.mouser.com/Search/Refine.aspx?Keyword=538-22-27-2031%20) |  |  | $0.00 | $0.00 | 13T6895 | Link (http://www.newark.com/webapp/wcs/stores/servlet/Search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)
C3 | 1nF | 100pF Â±5% 50V Ceramic Capacitor C0G, NP0 0402 (1005 Metric) | Capacitors_SMD:C_0603_HandSoldering | Murata Electronics North America | GRM1555C1H101JA01D | 0 | $0.00 | $0.00 | 3103986 |  | $0.00 | $0.00 | 490-5922-1-ND | Link (http://www.digikey.com/scripts/DkSearch/dksus.dll?WT.z_header=search_go&lang=en) |  |  | $0.00 | $0.00 | 2218836 | Link (http://it.farnell.com/murata/grm1555c1h101ja01d/conden-mlcc-c0g-np0-100pf-50v/dp/2218836) | 680207 |  | $0.00 | $0.00 | 81-GRM1555C1H101JA1D | Link (http://www.mouser.com/Search/../ProductDetail/Murata-Electronics/GRM1555C1H101JA01D/) |  |  | $0.00 | $0.00 | 48W5738 | Link (http://www.newark.com/murata/grm1555c1h101ja01d/cap-mlcc-c0g-np0-100pf-50v-0402/dp/48W5738) | 600 |  | $0.00 | $0.00 | 723-5363 | Link (http://it.rs-online.com/web/c/?searchTerm=GRM1555C1H101JA01D%20)
C2 | 10uF | 10ÂµF Â±10% 6.3V Ceramic Capacitor X5R 0805 (2012 Metric) | Capacitors_SMD:C_0603_HandSoldering | Murata Electronics North America | GRM219R60J106KE19D | 0 | $0.00 | $0.00 | 493075 |  | $0.00 | $0.00 | 490-3340-1-ND | Link (http://www.digikey.com/scripts/DkSearch/dksus.dll?WT.z_header=search_go&lang=en) |  |  | $0.00 | $0.00 | 1845738 | Link (http://it.farnell.com/murata/grm219r60j106ke19d/condensatore-mlcc-x5r-10uf-6-3v/dp/1845738) | 47930 |  | $0.00 | $0.00 | 81-GRM219R60J106KE9D | Link (http://www.mouser.com/Search/Refine.aspx?Keyword=81-GRM219R60J106KE9D%20) |  |  | $0.00 | $0.00 | 13T1205 | Link (http://www.newark.com/murata/grm219r60j106ke19d/multilayer-ceramic-capacitor-grm/dp/13T1205) | 275 |  | $0.00 | $0.00 | 723-6363 | Link (http://it.rs-online.com/web/c/?searchTerm=GRM219R60J106KE19D%20)
C1 | 0,1uF | 0.1ÂµF Â±10% 6.3V Ceramic Capacitor X5R 0201 (0603 Metric) | Capacitors_SMD:C_0603_HandSoldering | AVX Corporation | 02016D104KAT2A | 0 | $0.00 | $0.00 |  |  | $0.00 | $0.00 | 478-5266-1-ND | Link (http://www.digikey.com/scripts/DkSearch/dksus.dll?WT.z_header=search_go&lang=en) |  |  | $0.00 | $0.00 | 1657913 | Link (http://it.farnell.com/avx/02016d104kat2a/condens-mlcc-x5r-100nf-6-3v-0201/dp/1657913) | 724180 |  | $0.00 | $0.00 | 581-02016D104KAT2A | Link (http://www.mouser.com/Search/../ProductDetail/AVX/02016D104KAT2A/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) |  |  | $0.00 | $0.00 | 85K9474 | Link (http://www.newark.com/avx/02016d104kat2a/ceramic-capacitor-0-1uf-6-3v-x5r/dp/85K9474) | 26500 |  | $0.00 | $0.00 | 698-2995 | Link (http://it.rs-online.com/web/p/condensatori-ceramici-multistrato/6982995/)
R3,R6 | 470 | RES SMD 470 OHM 1% 1/8W 0805 | Resistors_SMD:R_0805_HandSoldering | Yageo | RC0805FR-07470RL | 0 | $0.00 | $0.00 | 1082937 |  | $0.00 | $0.00 | 311-470CRCT-ND | Link (http://www.digikey.com/scripts/DkSearch/dksus.dll?WT.z_header=search_go&lang=en) |  |  | $0.00 | $0.00 | 9237445 | Link (http://it.farnell.com/yageo-phycomp/rc0805fr-07470rl/res-film-spesso-470r-1-0-125w/dp/9237445) | 197970 |  | $0.00 | $0.00 | 603-RC0805FR-07470RL | Link (http://www.mouser.com/Search/Refine.aspx?Keyword=603-RC0805FR-07470RL%20) |  |  | $0.00 | $0.00 | 68X3202 | Link (http://www.newark.com/yageo-phycomp/rc0805fr-07470rl/surface-mount-thick-film-resistor/dp/68X3202) | 1 |  | $0.00 | $0.00 | 618-2546 | Link (http://it.rs-online.com/web/c/?searchTerm=RC0805FR-07470RL%20)
R2 | 10k | RES SMD 10K OHM 0.1% 1/8W 0805 | Resistors_SMD:R_0805_HandSoldering | Panasonic Electronic Components | ERA-6AEB103V | 0 | $0.00 | $0.00 | 461074 |  | $0.00 | $0.00 | P10KDACT-ND | Link (http://www.digikey.com/scripts/DkSearch/dksus.dll?WT.z_header=search_go&lang=en) |  |  | $0.00 | $0.00 | 1577673 | Link (http://it.farnell.com/panasonic-electronic-components/era6aeb103v/res-film-sott-10k-0-1-0-125w-0805/dp/1577673) | 62955 |  | $0.00 | $0.00 | 667-ERA-6AEB103V | Link (http://www.mouser.com/Search/Refine.aspx?Keyword=667-ERA-6AEB103V%20) |  |  | $0.00 | $0.00 | 08N2142 | Link (http://www.newark.com/panasonic-electronic-components/era-6aeb103v/res-thin-film-10k-0-1-0-125w-0805/dp/08N2142) | 740 |  | $0.00 | $0.00 | 565-948 | Link (http://it.rs-online.com/web/p/resistori-smd/0565948/)
C4 | 0,1nF | 10pF Â±5% 50V Ceramic Capacitor C0G, NP0 0402 (1005 Metric) | Capacitors_SMD:C_0603_HandSoldering | Murata Electronics North America | GRM1555C1H100JA01D | 0 | $0.00 | $0.00 | 26542 |  | $0.00 | $0.00 | 490-5921-1-ND | Link (http://www.digikey.com/scripts/DkSearch/dksus.dll?WT.z_header=search_go&lang=en) |  |  | $0.00 | $0.00 | 2218834 | Link (http://it.farnell.com/murata/grm1555c1h100ja01d/condens-mlcc-c0g-np0-10pf-50v/dp/2218834) | 368890 |  | $0.00 | $0.00 | 81-GRM1555C1H100JA1D | Link (http://www.mouser.com/Search/../ProductDetail/Murata-Electronics/GRM1555C1H100JA01D/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) |  |  | $0.00 | $0.00 | 48W5737 | Link (http://www.newark.com/murata/grm1555c1h100ja01d/cap-mlcc-c0g-np0-10pf-50v-0402/dp/48W5737) |  |  | $0.00 | $0.00 | 776-9194 | Link (http://it.rs-online.com/web/c/?searchTerm=GRM1555C1H100JA01D%20)
C5 | 1nF | 100pF Â±5% 10V Ceramic Capacitor C0G, NP0 0201 (0603 Metric) | Capacitors_SMD:C_0603_HandSoldering | AVX Corporation | 0201ZA101JAT2A | 0 | $0.00 | $0.00 | 25477 |  | $0.00 | $0.00 | 478-1026-1-ND | Link (http://www.digikey.com/scripts/DkSearch/dksus.dll?WT.z_header=search_go&lang=en) |  |  |  |  |  |  | 25053 |  | $0.00 | $0.00 | 581-0201ZA101JAT2A | Link (http://www.mouser.com/Search/Refine.aspx?Keyword=581-0201ZA101JAT2A%20) |  |  | $0.00 | $0.00 | 55J0850 | Link (http://www.newark.com/avx/0201za101jat2a/ceramic-capacitor-100pf-10v-c0g/dp/55J0850) |  |  |  |  | 136-4985 | Link (http://it.rs-online.com/web/c/?searchTerm=0201ZA101JAT2A%20)
R7,R8 | 5k | RES SMD 5K OHM 1% 1/8W 0805 | Resistors_SMD:R_0805_HandSoldering | Vishay Dale | CRCW08055K00FKTA | 0 | $0.00 | $0.00 |  |  | $0.00 | $0.00 | CRCW08055K00FKTA-ND | Link (http://www.digikey.com/scripts/DkSearch/dksus.dll?WT.z_header=search_go&lang=en) |  |  | $0.00 | $0.00 | 2616759 | Link (http://it.farnell.com/vishay/crcw08055k00fkta/res-aec-q200-pell-spessa-5k-0805/dp/2616759) | 48671 |  | $0.00 | $0.00 | 71-CRCW08055K60JNEB | Link (http://www.mouser.com/Search/../ProductDetail/Vishay/CRCW08055K60JNEB/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) |  |  | $0.00 | $0.00 | 49H8224 | Link (http://www.newark.com/vishay/crcw08055k00fkta/res-thick-film-5k-1-0-125w-0805/dp/49H8224)
SW1 | Reset | SWITCH PUSH SPST-NO 0.1A 32V | Buttons_Switches_THT:SW_PUSH_6mm | C&K | D6C90 F1 LFS | 0 | $0.00 | $0.00 | 6499 |  | $0.00 | $0.00 | 401-1969-ND | Link (http://www.digikey.com/scripts/DkSearch/dksus.dll?WT.z_header=search_go&lang=en) |  |  | $0.00 | $0.00 | 1201381 | Link (http://it.farnell.com/webapp/wcs/stores/servlet/Search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) | 4336 |  | $0.00 | $0.00 | 611-D6C90F1LFS | Link (http://www.mouser.com/Search/Refine.aspx?Keyword=611-D6C90F1LFS%20C%26K) |  |  | $0.00 | $0.00 | 99R3435 | Link (http://www.newark.com/webapp/wcs/stores/servlet/Search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) | 10 |  | $0.00 | $0.00 | 102-327 | Link (http://it.rs-online.com/web/c/?searchTerm=D6C90%20F1%20LFS%20C%26K)
SW2 | Boot | SWITCH SLIDE DPDT 300MA 6V | Buttons_Switches_THT:SW_Micro_SPST | C&K | JS202011CQN | 0 | $0.00 | $0.00 | 24934 |  | $0.00 | $0.00 | 401-2001-ND | Link (http://www.digikey.com/scripts/DkSearch/dksus.dll?WT.z_header=search_go&lang=en) |  |  | $0.00 | $0.00 | 2320018 | Link (http://it.farnell.com/webapp/wcs/stores/servlet/Search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) | 16619 |  | $0.00 | $0.00 | 611-JS202011CQN | Link (http://www.mouser.com/Search/Refine.aspx?Keyword=611-JS202011CQN%20) |  |  | $0.00 | $0.00 | 95W3255 | Link (http://www.newark.com/webapp/wcs/stores/servlet/Search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)
F1-F3 | FIDUCIAL |  | PonchoEDUCIAA_WIFI_BLTH:Fiducial_1mm |  |  | 0 | $0.00 | $0.00
 |  |  |  |  |  |  |  |  |  | 0 | 0 | 0 |  |  |  | 0 | 0 | 0 |  |  |  | 0 | 0 | 0 |  |  |  | 0 | 0 | 0 |  |  |  | 0 | 0 | 0
 |  |  |  |  |  |  |  |  |  | 0 | 0 | 0 |  |  |  | 0 | 0 | 0 |  |  |  | 0 | 0 | 0 |  |  |  | 0 | 0 | 0 |  |  |  | 0 | 0 | 0
 |  |  |  |  |  |  |  |  |  | 0 | 0 | 0 |  |  |  | 0 | 0 | 0 |  |  |  | 0 | 0 | 0 |  |  |  | 0 | 0 | 0 |  |  |  | 0 | 0 | 0
 |  |  |  |  |  |  |  |  |  | 0 | 0 | 0 |  |  |  | 0 | 0 | 0 |  |  |  | 0 | 0 | 0 |  |  |  | 0 | 0 | 0 |  |  |  | 0 | 0 | 0
 |  |  |  |  |  |  |  |  |  | 0 | 0 | 0 |  |  |  | 0 | 0 | 0 |  |  |  | 0 | 0 | 0 |  |  |  | 0 | 0 | 0 |  |  |  | 0 | 0 | 0
 |  |  |  |  |  |  |  |  |  | 0 | 0 | 0 |  |  |  | 0 | 0 | 0 |  |  |  | 0 | 0 | 0 |  |  |  | 0 | 0 | 0 |  |  |  | 0 | 0 | 0
 |  |  |  |  |  |  |  |  |  | 0 | 0 | 0 |  |  |  | 0 | 0 | 0 |  |  |  | 0 | 0 | 0 |  |  |  | 0 | 0 | 0 |  |  |  | 0 | 0 | 0
 |  |  |  |  |  |  |  |  |  | 0 | 0 | 0 |  |  |  | 0 | 0 | 0 |  |  |  | 0 | 0 | 0 |  |  |  | 0 | 0 | 0 |  |  |  | 0 | 0 | 0
 |  |  |  |  |  |  |  |  |  | 0 | 0 | 0 |  |  |  | 0 | 0 | 0 |  |  |  | 0 | 0 | 0 |  |  |  | 0 | 0 | 0 |  |  |  | 0 | 0 | 0
 |  |  |  |  |  |  |  |  |  | 0 | 0 | 0 |  |  |  | 0 | 0 | 0 |  |  |  | 0 | 0 | 0 |  |  |  | 0 | 0 | 0 |  |  |  | 0 | 0 | 0
 |  |  |  |  |  |  |  |  |  | 0 | 0 | 0 |  |  |  | 0 | 0 | 0 |  |  |  | 0 | 0 | 0 |  |  |  | 0 | 0 | 0 |  |  |  | 0 | 0 | 0
 |  |  |  |  |  |  |  |  |  | 0 | 0 | 0 |  |  |  | 0 | 0 | 0 |  |  |  | 0 | 0 | 0 |  |  |  | 0 | 0 | 0 |  |  |  | 0 | 0 | 0
 |  |  |  |  |  |  |  |  |  | 0 | 0 | 0 |  |  |  | 0 | 0 | 0 |  |  |  | 0 | 0 | 0 |  |  |  | 0 | 0 | 0 |  |  |  | 0 | 0 | 0
 |  |  |  |  |  |  |  |  |  | 0 | 0 | 0 |  |  |  | 0 | 0 | 0 |  |  |  | 0 | 0 | 0 |  |  |  | 0 | 0 | 0 |  |  |  | 0 | 0 | 0
 |  |  |  |  |  |  |  |  |  | 0 | 0 | 0 |  |  |  | 0 | 0 | 0 |  |  |  | 0 | 0 | 0 |  |  |  | 0 | 0 | 0 |  |  |  | 0 | 0 | 0
 |  |  |  |  |  |  |  |  |  | 0 | 0 | 0 |  |  |  | 0 | 0 | 0 |  |  |  | 0 | 0 | 0 |  |  |  | 0 | 0 | 0 |  |  |  | 0 | 0 | 0
 |  |  |  |  |  |  |  |  |  | 0 | 0 | 0 |  |  |  | 0 | 0 | 0 |  |  |  | 0 | 0 | 0 |  |  |  | 0 | 0 | 0 |  |  |  | 0 | 0 | 0
 |  |  |  |  |  |  |  |  |  | 0 | 0 | 0 |  |  |  | 0 | 0 | 0 |  |  |  | 0 | 0 | 0 |  |  |  | 0 | 0 | 0 |  |  |  | 0 | 0 | 0
