ciaa/Ponchos/Mision_SAE/doc/rev.ods

NOMBRE |  | Iglesias Julian | Status
EMAIL |  | julianmiglesias@gmail.com
PROYECTO |  | Módulo basado en SAE
REPO |  | https://gitlab.com/julianmiglesias/MisionSAE
CORRECCION (Fecha) |  | 01/12/16
Documentación | Archivo hoja de proyecto en /doc | Faltante | Si
 | Archivos de revisiones en /doc | Si.
 | Revisor designado | ??? | Matías
Esquematico | Bibliotecas | Quitar todas | Si
 | Rótulo | Falta mención al autor inicial. Falta licencia. Título descriptivo de cada hoja. | Si
 | Jerarquía | Ok.
 | Campos KiCost | NO. | x
 | Prolijidad conexiones | Prolijas
 | Referencias | OK.
 | Comentarios | Colocar detalles del módulo Xbee. | Si
 | ERC | NO. Editar uno de los dos conectores de Poncho para evitar el error de ERC. | Si
Asociación | Configuración bibliotecas | OK. Asociar solo componentes dentro de la biblioteca local de footprints. | Si
PCB | Notas en PCB: Grila pos, ruteo. Pista min, Vía min, aguj. min, capas, terminación superficial. | Faltante | Si
 | Rótulo | Vacío | Si
 | Encapsulados | Dibujar en forma más precisa el contorno de la batería de 9V. Colocar en el footprint 4 agujeros de sujeción para pasar dos precintos y sujetar la batería. | Si
 | Borde del PCB | OK
 | Ancho de pistas | Falta | Si
 | DRC | Falta | Si
 | Ruteo | Falta | Si
 | Fiduciales | Faltan pero no son necesarios.
 | Placement | Dejar libre el botón de reset. Los resistores SMD irían del lado cobre inferior. | Si
 | Serigrafía | Falta acomodar para dejar referencias visibles luego de soldar. D3, BT1 . Intentar dejar libre serigrafía del conector de Poncho. | Si
 | Dimensiones | OK
 | Fijación | Colocar uno o dos agujeros auxiliares en la parte superior de la placa (la más alejada a los conectores de Poncho). | Si
 | Belleza/Alineación | OK.
 | Vista 3D | Parcial. Faltan ajustes | Si
 | Areas de cobre | Falta | Si
