ciaa/Ponchos/Osciloscopio/doc/Revisiones/Poncho_osc_rev1_DJB.ods

 | NOMBRE | Nicolás Dassieu Blanchet
 | PROYECTO | Poncho osciloscopio.
 | REPO | https://github.com/ciaa/Ponchos
 | CORRECCION PRELIMINAR | Diego Brengi
Campo | Rubro | Descripción de la mejora o correción | Acción Tomada | Comentarios
Esquematico | Bicliotecas | Cuando lo arranco me pide convertir RV1. Dejar solo una biblioteca (copiar xx-cache.lib) o ninguna en la implementación final | Realizado
 | Rótulo | Colocar que se hizo para el curso de Diseño de PCB del la CESE. | Agregado
 | Jerarquía | A lo último si queda tiempo y no se rompe nada, probar quitar la hoja 2 y que su contenido quede en la hoja uno. Operaciones de guardar bloque y pegar bloque. | Realizado
 | Campos KiCost | Ok. Buscar código de pines de XA1. | Agregado | Se lo agrego pero al ser una pieza multiparte que necesita 2 conectores por equipo en el BOM va a figurar 1 solo. Se debería colocar además una segundo objeto solo en BOM con el mismo numero de parte que AX1. Dado que no se puede hacer esto en Kicad se deja una nota al respecto en esquematico.
 | Prolijidad conexiones | Ok. Creo que es mejor borrar las señales que no se usan del Poncho, el conector, entre jerarquías, etc. | Realizado
 | Referencias | OK.
 | Cometarios | Sería buenísmimo agregar en GPIO4 un transistor y un buzzer como tiene el proyecto del que se copió. | No hacerlo | No dispongo del tiempo suficiente para agregarlo
 |  | Dice que R8 debe ajustarse. No es R16? No conviene poner una R fija y un preset multivuelta del tipo 490-2874-ND | Se Quita la nota, se agrega el preset multivuelta 50Kohm y set cambia R16 por 150Kohm | La nota tenía sentido en el circuito original donde la tension de entrada era selecionable. Se agrega el preset para ajuste de cero del circuito.
 | ERC | OK.
Asociación | Configuración bibliotecas | Colocar todos los footprints del circuito en osc.pretty. (se exportan desde el pcbnew) y después se vuelve a hacer la asignación. | Realizado
PCB | Rótulo | Colocar que se hizo para el curso de Diseño de PCB del la CESE. | Agregado
 | Encapsulados
 | Borde del PCB | Si no complica liberar el botón de reset. | Se modificó la forma
 | Ancho de pistas
 | DRC
 | Ruteo
 | Fiduciales | No estan, pero creo que no hacen falta. | Se agregaron
 | Placement | OK. Se podría mejorar la "belleza", mejor alineados R16/C12 ; R17/19; C8/FB2; R7/R10/C11 por ejemplo. | Realizado
 | Serigrafía | Logo Open hardware. Nombre Autor. CESE - Diseño de PCBs. También pponer algo en cobre si hay lugar. | Realizado
 | Dimensiones | Usar esta plantilla. Si no complica colocar agujeros para ver los leds en caso que no se use el display. https://raw.githubusercontent.com/ciaa/Ponchos/ponchoOsciloscopio/kicad/Poncho_Esqueleto.pretty/Plantilla_EDU-CIAA.kicad_mod | Se agregaron los agujeros
 | Vista 3D | No funciona. | Funcionando | Salvo display sin modelo 3D disponible
