ciaa/Ponchos/Osciloscopio/fabricacion1/BOM.xlsx

 |  |  |  |  |  |  | Board Qty: | 100
 |  |  |  |  |  |  | Total Cost: | $0.00 |  |  |  | $0.00 |  |  |  |  |  | $0.00 |  |  |  |  |  | $0.00
 |  |  |  |  |  |  | Unit Cost: | $0.00
Global Part Info |  |  |  |  |  |  |  |  | Digi-Key |  |  |  |  |  | Mouser |  |  |  |  |  | Newark
Refs | Value | Desc | Footprint | Manf | Manf# | Qty | Unit$ | Ext$ | Avail | Purch | Unit$ | Ext$ | Cat# | Doc | Avail | Purch | Unit$ | Ext$ | Cat# | Doc | Avail | Purch | Unit$ | Ext$ | Cat# | Doc
Q1-Q4 | BC557 |  | osc:TO-92_Inline_Wide | Fairchild Semiconductor | BC557BTA | 0 | $0.00 | $0.00 | 5925 |  | $0.00 | $0.00 | BC557BTACT-ND | Link (http://www.digikey.com/scripts/DkSearch/dksus.dll?WT.z_header=search_go&lang=en) | 7163 |  | $0.00 | $0.00 | 512-BC557BTA | Link (http://www.mouser.com/Search/../ProductDetail/Fairchild-Semiconductor/BC557BTA/) | 2048 |  | $0.00 | $0.00 | 31Y0494 | Link (http://www.newark.com/webapp/wcs/stores/servlet/Search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)
F1-F3 | FIDUCIAL |  | osc:Fiducial_1mm |  |  | 0 | $0.00 | $0.00
D5 | Display |  | osc:Display | Sullins Connector Solutions | PPPC091LFBN-RC | 0 | $0.00 | $0.00 | 553 |  | $0.00 | $0.00 | S7042-ND | Link (http://www.digikey.com/scripts/DkSearch/dksus.dll?WT.z_header=search_go&lang=en) | 404 |  | $0.00 | $0.00 | 895-USB-RS485-PCBA | Link (http://www.mouser.com/Search/../ProductDetail/FTDI/USB-RS485-PCBA/?qs=sGAEpiMZZMsgSGrx0WqTbNPfcYRyEW%252bV) |  |  |  |  |  | Link (http://www.newark.com/webapp/wcs/stores/servlet/Search?catalogId=15003&langId=-1&storeId=10194&gs=true)
R16 | 150k |  | osc:R_0805_HandSoldering | Stackpole Electronics Inc. | RMCF0805JT150K | 0 | $0.00 | $0.00 | 19365 |  | $0.00 | $0.00 | RMCF0805JT150KCT-ND | Link (http://www.digikey.com/scripts/DkSearch/dksus.dll?WT.z_header=search_go&lang=en) | 3859 |  | $0.00 | $0.00 | 757-TPW1R005PLL1Q | Link (http://www.mouser.com/Search/../ProductDetail/Toshiba/TPW1R005PLL1Q/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)
D1,D2 | BAT54 |  | osc:SOT-323 | NXP Semiconductors | BAT54W,135 | 0 | $0.00 | $0.00 | 40480 |  | $0.00 | $0.00 | 568-11592-1-ND | Link (http://www.digikey.com/scripts/DkSearch/dksus.dll?WT.z_header=search_go&lang=en) | 4747 |  | $0.00 | $0.00 | 771-BAT54W135 | Link (http://www.mouser.com/Search/../ProductDetail/NXP-Semiconductors/BAT54W135/)
D3 | BAT54 |  | osc:SOT-323 | NXP Semiconductors | BAT54W,135 | 0 | $0.00 | $0.00 | 40480 |  | $0.00 | $0.00 | 568-11592-1-ND | Link (http://www.digikey.com/scripts/DkSearch/dksus.dll?WT.z_header=search_go&lang=en) | 4747 |  | $0.00 | $0.00 | 771-BAT54W135 | Link (http://www.mouser.com/Search/../ProductDetail/NXP-Semiconductors/BAT54W135/)
R2-R5,R7 | 100k |  | osc:R_0805_HandSoldering | Stackpole Electronics Inc. | RMCF0805JT100K | 0 | $0.00 | $0.00 | 397880 |  | $0.00 | $0.00 | RMCF0805JT100KCT-ND | Link (http://www.digikey.com/scripts/DkSearch/dksus.dll?WT.z_header=search_go&lang=en) | 3859 |  | $0.00 | $0.00 | 757-TPW1R005PLL1Q | Link (http://www.mouser.com/Search/../ProductDetail/Toshiba/TPW1R005PLL1Q/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)
FB2 | HZ0805E601R-10 |  | osc:R_0805_HandSoldering | Laird-Signal Integrity Products | HZ0805E601R-10 | 0 | $0.00 | $0.00 | 1125651 |  | $0.00 | $0.00 | 240-2399-1-ND | Link (http://www.digikey.com/scripts/DkSearch/dksus.dll?WT.z_header=search_go&lang=en) | 39 |  | $0.00 | $0.00 | 972-89HP0604SZBNRG | Link (http://www.mouser.com/Search/../ProductDetail/IDT/89HP0604SZBNRG/?qs=sGAEpiMZZMvocn3OtlEZq1GdqiHYrh28)
FB1 | HZ0805E601R-10 |  | osc:R_0805_HandSoldering | Laird-Signal Integrity Products | HZ0805E601R-10 | 0 | $0.00 | $0.00 | 1125651 |  | $0.00 | $0.00 | 240-2399-1-ND | Link (http://www.digikey.com/scripts/DkSearch/dksus.dll?WT.z_header=search_go&lang=en) | 39 |  | $0.00 | $0.00 | 972-89HP0604SZBNRG | Link (http://www.mouser.com/Search/../ProductDetail/IDT/89HP0604SZBNRG/?qs=sGAEpiMZZMvocn3OtlEZq1GdqiHYrh28)
R6 | 910k |  | osc:R_0805_HandSoldering | Stackpole Electronics Inc. | RMCF0805JT910K | 0 | $0.00 | $0.00 | 6940 |  | $0.00 | $0.00 | RMCF0805JT910KCT-ND | Link (http://www.digikey.com/scripts/DkSearch/dksus.dll?WT.z_header=search_go&lang=en) | 3859 |  | $0.00 | $0.00 | 757-TPW1R005PLL1Q | Link (http://www.mouser.com/Search/../ProductDetail/Toshiba/TPW1R005PLL1Q/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)
U5 | CD4066 |  | osc:DIP-14_W7.62mm_LongPads | Texas Instruments | CD4066BE | 0 | $0.00 | $0.00 | 7748 |  | $0.00 | $0.00 | 296-2061-5-ND | Link (http://www.digikey.com/scripts/DkSearch/dksus.dll?WT.z_header=search_go&lang=en) | 3511 |  | $0.00 | $0.00 | 595-CD4066BE | Link (http://www.mouser.com/Search/../ProductDetail/Texas-Instruments/CD4066BE/) | 3142 |  | $0.00 | $0.00 | 60K5124 | Link (http://www.newark.com/texas-instruments/cd4066be/analog-switch-quad-spst-dip-14/dp/60K5124)
U2 | 78L05 |  | osc:TO-92_Inline_Wide | Texas Instruments | UA78L05ACLPR | 0 | $0.00 | $0.00 | 7515 |  | $0.00 | $0.00 | 296-1365-1-ND | Link (http://www.digikey.com/scripts/DkSearch/dksus.dll?WT.z_header=search_go&lang=en) | 2747 |  | $0.00 | $0.00 | 595-UA78L05ACLPR | Link (http://www.mouser.com/Search/../ProductDetail/Texas-Instruments/UA78L05ACLPR/) | 670 |  | $0.00 | $0.00 | 52K5955 | Link (http://www.newark.com/texas-instruments/ua78l05aclpre3/linear-voltage-regulator-5v-to/dp/52K5955)
C6-C12,C14 | 100nF |  | osc:C_0805_HandSoldering | Samsung Electro-Mechanics America, Inc. | CL21B104KBFNNNG | 0 | $0.00 | $0.00 | 127822 |  | $0.00 | $0.00 | 1276-6468-1-ND | Link (http://www.digikey.com/scripts/DkSearch/dksus.dll?WT.z_header=search_go&lang=en)
R1 | 10k |  | osc:R_0805_HandSoldering | Stackpole Electronics Inc. | RMCF0805JG10K0 | 0 | $0.00 | $0.00 | 15000 |  | $0.00 | $0.00 | RMCF0805JG10K0CT-ND | Link (http://www.digikey.com/scripts/DkSearch/dksus.dll?WT.z_header=search_go&lang=en) | 3859 |  | $0.00 | $0.00 | 757-TPW1R005PLL1Q | Link (http://www.mouser.com/Search/../ProductDetail/Toshiba/TPW1R005PLL1Q/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)
R12,R17,R19 | 56k |  | osc:R_0805_HandSoldering | Stackpole Electronics Inc. | RMCF0805JT56K0 | 0 | $0.00 | $0.00 | 68510 |  | $0.00 | $0.00 | RMCF0805JT56K0CT-ND | Link (http://www.digikey.com/scripts/DkSearch/dksus.dll?WT.z_header=search_go&lang=en) | 3859 |  | $0.00 | $0.00 | 757-TPW1R005PLL1Q | Link (http://www.mouser.com/Search/../ProductDetail/Toshiba/TPW1R005PLL1Q/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)
P1 | BNC |  | osc:BNC_Socket_TYCO-AMP_LargePads | TE Connectivity AMP Connectors | 5227161-1 | 0 | $0.00 | $0.00 | 3604 |  | $0.00 | $0.00 | A32244-ND | Link (http://www.digikey.com/scripts/DkSearch/dksus.dll?WT.z_header=search_go&lang=en) | 4870 |  | $0.00 | $0.00 | 571-2213362-1 | Link (http://www.mouser.com/Search/../ProductDetail/TE-Connectivity-AMP/2213362-1/) | 3962 |  | $0.00 | $0.00 | 42K8695 | Link (http://www.newark.com/webapp/wcs/stores/servlet/Search?catalogId=15003&langId=-1&storeId=10194&gs=true)
R20-R26 | 33 |  | osc:R_0805_HandSoldering | Stackpole Electronics Inc. | RMCF0805JT33R0 | 0 | $0.00 | $0.00 | 15487 |  | $0.00 | $0.00 | RMCF0805JT33R0CT-ND | Link (http://www.digikey.com/scripts/DkSearch/dksus.dll?WT.z_header=search_go&lang=en) | 1995 |  | $0.00 | $0.00 | 757-TC35667FTG005EL | Link (http://www.mouser.com/Search/../ProductDetail/Toshiba/TC35667FTG-005EL/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)
RV2 | 150k |  | osc:Potentiometer_Bourns_3296W_3-8Zoll_Inline_ScrewUp | Bourns Inc. | PV36W503C01B00 | 0 | $0.00 | $0.00 | 8052 |  | $0.00 | $0.00 | 490-2889-ND | Link (http://www.digikey.com/scripts/DkSearch/dksus.dll?WT.z_header=search_go&lang=en)
R15 | 1k8 |  | osc:R_0805_HandSoldering | Stackpole Electronics Inc. | RMCF0805JT1K80 | 0 | $0.00 | $0.00 | 22023 |  | $0.00 | $0.00 | RMCF0805JT1K80CT-ND | Link (http://www.digikey.com/scripts/DkSearch/dksus.dll?WT.z_header=search_go&lang=en) | 3859 |  | $0.00 | $0.00 | 757-TPW1R005PLL1Q | Link (http://www.mouser.com/Search/../ProductDetail/Toshiba/TPW1R005PLL1Q/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)
XA1 | Conn_Poncho2P_2x_20x2 |  | osc:poncho_grande | Sullins Connector Solutions | PEC20DAAN | 0 | $0.00 | $0.00 | 637 |  | $0.00 | $0.00 | S2012E-20-ND | Link (http://www.digikey.com/scripts/DkSearch/dksus.dll?WT.z_header=search_go&lang=en) | 67 |  | $0.00 | $0.00 | 989-PL-ETH2-BLASTER | Link (http://www.mouser.com/Search/../ProductDetail/Altera/PL-ETH2-BLASTER/?qs=sGAEpiMZZMs24GWi4QakP59quv%2f1LikQ) |  |  |  |  |  | Link (http://www.newark.com/webapp/wcs/stores/servlet/Search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)
U3 | 79L05 |  | osc:TO-92_Inline_Wide | Texas Instruments | MC79L05ACLPR | 0 | $0.00 | $0.00 | 5636 |  | $0.00 | $0.00 | 296-31456-1-ND | Link (http://www.digikey.com/scripts/DkSearch/dksus.dll?WT.z_header=search_go&lang=en) | 2773 |  | $0.00 | $0.00 | 595-MC79L05ACLPR | Link (http://www.mouser.com/Search/../ProductDetail/Texas-Instruments/MC79L05ACLPR/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)
R8-R11 | 47k |  | osc:R_0805_HandSoldering | Stackpole Electronics Inc. | RMCF0805JT47K0 | 0 | $0.00 | $0.00 | 278158 |  | $0.00 | $0.00 | RMCF0805JT47K0CT-ND | Link (http://www.digikey.com/scripts/DkSearch/dksus.dll?WT.z_header=search_go&lang=en) | 1995 |  | $0.00 | $0.00 | 757-TC35667FTG005EL | Link (http://www.mouser.com/Search/../ProductDetail/Toshiba/TC35667FTG-005EL/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)
R13 | 18k |  | osc:R_0805_HandSoldering | Stackpole Electronics Inc. | RMCF0805JT18K0 | 0 | $0.00 | $0.00 | 41288 |  | $0.00 | $0.00 | RMCF0805JT18K0CT-ND | Link (http://www.digikey.com/scripts/DkSearch/dksus.dll?WT.z_header=search_go&lang=en) | 3859 |  | $0.00 | $0.00 | 757-TPW1R005PLL1Q | Link (http://www.mouser.com/Search/../ProductDetail/Toshiba/TPW1R005PLL1Q/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)
R14 | 5k6 |  | osc:R_0805_HandSoldering | Stackpole Electronics Inc. | RMCF0805JT5K60 | 0 | $0.00 | $0.00 | 130728 |  | $0.00 | $0.00 | RMCF0805JT5K60CT-ND | Link (http://www.digikey.com/scripts/DkSearch/dksus.dll?WT.z_header=search_go&lang=en) | 1995 |  | $0.00 | $0.00 | 757-TC35667FTG005EL | Link (http://www.mouser.com/Search/../ProductDetail/Toshiba/TC35667FTG-005EL/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)
D4 | BAT54 |  | osc:SOT-323 | NXP Semiconductors | BAT54W,135 | 0 | $0.00 | $0.00 | 40480 |  | $0.00 | $0.00 | 568-11592-1-ND | Link (http://www.digikey.com/scripts/DkSearch/dksus.dll?WT.z_header=search_go&lang=en) | 4747 |  | $0.00 | $0.00 | 771-BAT54W135 | Link (http://www.mouser.com/Search/../ProductDetail/NXP-Semiconductors/BAT54W135/)
C1-C5 | 1uF |  | osc:C_Radial_D5_L11_P2 | Wurth Electronics Inc | 860020672005 | 0 | $0.00 | $0.00 | 2327 |  | $0.00 | $0.00 | 732-8851-1-ND | Link (http://www.digikey.com/scripts/DkSearch/dksus.dll?WT.z_header=search_go&lang=en) | 7136 |  | $0.00 | $0.00 | 710-82400102 | Link (http://www.mouser.com/Search/../ProductDetail/Wurth-Electronics/82400102/)
U4 | TL082 |  | osc:DIP-8_W7.62mm_LongPads | Texas Instruments | TL082IP | 0 | $0.00 | $0.00 | 2304 |  | $0.00 | $0.00 | 296-1781-5-ND | Link (http://www.digikey.com/scripts/DkSearch/dksus.dll?WT.z_header=search_go&lang=en) | 0 |  | $0.00 | $0.00 | 595-TL082IP | Link (http://www.mouser.com/Search/../ProductDetail/Texas-Instruments/TL082IP/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) | 1083 |  | $0.00 | $0.00 | 60K6992 | Link (http://www.newark.com/texas-instruments/tl082ip/op-amp-3mhz-13v-us-dip-8/dp/60K6992)
U1 | MAX232 |  | osc:DIP-16_W7.62mm_LongPads | Texas Instruments | MAX232N | 0 | $0.00 | $0.00 | 11536 |  | $0.00 | $0.00 | 296-1402-5-ND | Link (http://www.digikey.com/scripts/DkSearch/dksus.dll?WT.z_header=search_go&lang=en) | 2767 |  | $0.00 | $0.00 | 595-MAX232N | Link (http://www.mouser.com/Search/../ProductDetail/Texas-Instruments/MAX232N/) | 3062 |  | $0.00 | $0.00 | 59K8220 | Link (http://www.newark.com/texas-instruments/max232n/driver-receiver-rs232-120kbps/dp/59K8220)
RV1 | 10k |  | osc:Potentiometer_Alps-RK16-single | ALPS | RK1631110TBK | 0 | $0.00 | $0.00 |  |  |  |  |  |  | 465 |  | $0.00 | $0.00 | 688-RK1631110TBK | Link (http://www.mouser.com/Search/Refine.aspx?Keyword=688-RK1631110TBK%20ALPS)
 |  |  |  |  |  |  |  |  |  | 0 | 0 | 0 |  |  |  | 0 | 0 | 0 |  |  |  | 0 | 0 | 0
 |  |  |  |  |  |  |  |  |  | 0 | 0 | 0 |  |  |  | 0 | 0 | 0 |  |  |  | 0 | 0 | 0
 |  |  |  |  |  |  |  |  |  | 0 | 0 | 0 |  |  |  | 0 | 0 | 0 |  |  |  | 0 | 0 | 0
 |  |  |  |  |  |  |  |  |  | 0 | 0 | 0 |  |  |  | 0 | 0 | 0 |  |  |  | 0 | 0 | 0
 |  |  |  |  |  |  |  |  |  | 0 | 0 | 0 |  |  |  | 0 | 0 | 0 |  |  |  | 0 | 0 | 0
 |  |  |  |  |  |  |  |  |  | 0 | 0 | 0 |  |  |  | 0 | 0 | 0 |  |  |  | 0 | 0 | 0
 |  |  |  |  |  |  |  |  |  | 0 | 0 | 0 |  |  |  | 0 | 0 | 0 |  |  |  | 0 | 0 | 0
 |  |  |  |  |  |  |  |  |  | 0 | 0 | 0 |  |  |  | 0 | 0 | 0 |  |  |  | 0 | 0 | 0
 |  |  |  |  |  |  |  |  |  | 0 | 0 | 0 |  |  |  | 0 | 0 | 0 |  |  |  | 0 | 0 | 0
 |  |  |  |  |  |  |  |  |  | 0 | 0 | 0 |  |  |  | 0 | 0 | 0 |  |  |  | 0 | 0 | 0
 |  |  |  |  |  |  |  |  |  | 0 | 0 | 0 |  |  |  | 0 | 0 | 0 |  |  |  | 0 | 0 | 0
 |  |  |  |  |  |  |  |  |  | 0 | 0 | 0 |  |  |  | 0 | 0 | 0 |  |  |  | 0 | 0 | 0
 |  |  |  |  |  |  |  |  |  | 0 | 0 | 0 |  |  |  | 0 | 0 | 0 |  |  |  | 0 | 0 | 0
 |  |  |  |  |  |  |  |  |  | 0 | 0 | 0 |  |  |  | 0 | 0 | 0 |  |  |  | 0 | 0 | 0
 |  |  |  |  |  |  |  |  |  | 0 | 0 | 0 |  |  |  | 0 | 0 | 0 |  |  |  | 0 | 0 | 0
 |  |  |  |  |  |  |  |  |  | 0 | 0 | 0 |  |  |  | 0 | 0 | 0 |  |  |  | 0 | 0 | 0
 |  |  |  |  |  |  |  |  |  | 0 | 0 | 0 |  |  |  | 0 | 0 | 0 |  |  |  | 0 | 0 | 0
 |  |  |  |  |  |  |  |  |  | 0 | 0 | 0 |  |  |  | 0 | 0 | 0 |  |  |  | 0 | 0 | 0
 |  |  |  |  |  |  |  |  |  | 0 | 0 | 0 |  |  |  | 0 | 0 | 0 |  |  |  | 0 | 0 | 0
 |  |  |  |  |  |  |  |  |  | 0 | 0 | 0 |  |  |  | 0 | 0 | 0 |  |  |  | 0 | 0 | 0
 |  |  |  |  |  |  |  |  |  | 0 | 0 | 0 |  |  |  | 0 | 0 | 0 |  |  |  | 0 | 0 | 0
 |  |  |  |  |  |  |  |  |  | 0 | 0 | 0 |  |  |  | 0 | 0 | 0 |  |  |  | 0 | 0 | 0
 |  |  |  |  |  |  |  |  |  | 0 | 0 | 0 |  |  |  | 0 | 0 | 0 |  |  |  | 0 | 0 | 0
 |  |  |  |  |  |  |  |  |  | 0 | 0 | 0 |  |  |  | 0 | 0 | 0 |  |  |  | 0 | 0 | 0
 |  |  |  |  |  |  |  |  |  | 0 | 0 | 0 |  |  |  | 0 | 0 | 0 |  |  |  | 0 | 0 | 0
 |  |  |  |  |  |  |  |  |  | 0 | 0 | 0 |  |  |  | 0 | 0 | 0 |  |  |  | 0 | 0 | 0
 |  |  |  |  |  |  |  |  |  | 0 | 0 | 0 |  |  |  | 0 | 0 | 0 |  |  |  | 0 | 0 | 0
 |  |  |  |  |  |  |  |  |  | 0 | 0 | 0 |  |  |  | 0 | 0 | 0 |  |  |  | 0 | 0 | 0
 |  |  |  |  |  |  |  |  |  | 0 | 0 | 0 |  |  |  | 0 | 0 | 0 |  |  |  | 0 | 0 | 0
