ciaa/Ponchos/MIDI/Doc/BOM/MIDI_KiCost.xlsx

 |  |  |  |  |  |  | Board Qty: | 1
 |  |  |  |  |  |  | Total Cost: | $18.73 |  |  |  | $24.10 |  |  |  |  |  | $21.22 |  |  |  |  |  | $22.93 |  |  |  |  |  | $20.67 |  |  |  |  |  | $1990.19
 |  |  |  |  |  |  | Unit Cost: | $18.73
Global Part Info |  |  |  |  |  |  |  |  | Digi-Key |  |  |  |  |  | Farnell |  |  |  |  |  | Mouser |  |  |  |  |  | Newark |  |  |  |  |  | Rs Components
Refs | Value | Desc | Footprint | Manf | Manf# | Qty | Unit$ | Ext$ | Avail | Purch | Unit$ | Ext$ | Cat# | Doc | Avail | Purch | Unit$ | Ext$ | Cat# | Doc | Avail | Purch | Unit$ | Ext$ | Cat# | Doc | Avail | Purch | Unit$ | Ext$ | Cat# | Doc | Avail | Purch | Unit$ | Ext$ | Cat# | Doc
C1-C4,C7,C8,C11,C12,C15-C28 | 100nF | CAP CER 0.1UF 50V X7R 0804 | MIDI:C_0805_HandSoldering | Yageo | CC0805KRX7R9BB104 | 22 | $0.02 | $0.54 | 1221123 |  | $0.06 | $1.28 | 311-1140-1-ND | Link (http://www.digikey.com/scripts/DkSearch/dksus.dll?WT.z_header=search_go&lang=en) |  |  | $0.02 | $0.54 | 3019949 | Link (http://it.farnell.com/yageo-phycomp/cc0805krx7r9bb104/condensatore-mlcc-x7r-100nf-50v/dp/3019949) | 437909 |  | $0.04 | $0.81 | 603-CC805KRX7R9BB104 | Link (http://www.mouser.com/Search/Refine.aspx?Keyword=603-CC805KRX7R9BB104%20Yageo) |  |  | $0.05 | $1.12 | 68R4910 | Link (http://www.newark.com/yageo/cc0805krx7r9bb104/ceramic-capacitor-0-1uf-50v-x7r/dp/68R4910) | 2 |  | $39.42 | $867.15 | 669-8842 | Link (http://it.rs-online.com/web/c/?searchTerm=CC0805KRX7R9BB104%20Yageo)
C5,C6,C9,C10,C13,C14 | 10nF | CAP CER 10000PF 50V X7R 0804 | MIDI:C_0805_HandSoldering | Yageo | CC0805KRX7R9BB103 | 6 | $0.05 | $0.31 | 845900 |  | $0.10 | $0.60 | 311-1136-1-ND | Link (http://www.digikey.com/scripts/DkSearch/dksus.dll?WT.z_header=search_go&lang=en) |  |  | $0.05 | $0.31 | 3019937 | Link (http://it.farnell.com/yageo-phycomp/cc0805krx7r9bb103/condensatore-mlcc-x7r-10nf-50v/dp/3019937) | 200458 |  | $0.10 | $0.61 | 603-CC805KRX7R9BB103 | Link (http://www.mouser.com/Search/Refine.aspx?Keyword=603-CC805KRX7R9BB103%20Yageo) |  |  | $0.07 | $0.44 | 68R4909 | Link (http://www.newark.com/yageo/cc0805krx7r9bb103/ceramic-capacitor-0-01uf-50v-x7r/dp/68R4909) | 2 |  | $39.42 | $236.50 | 669-8842 | Link (http://it.rs-online.com/web/c/?searchTerm=CC0805KRX7R9BB103%20Yageo)
D1 | 1N4148 | DIODE GEN PURP 100V 200MA DO34 | MIDI:D_DO-35_SOD27_P7.62mm_Horizontal | Fairchild/ON Semiconductor | 1N4148 | 1 | $0.10 | $0.10 | 920000 |  | $0.10 | $0.10 | 1N4148FS-ND | Link (http://www.digikey.com/scripts/DkSearch/dksus.dll?WT.z_header=search_go&lang=en) |  |  | $0.15 | $0.15 | 1612346 | Link (http://it.farnell.com/vishay/1n4148/diodo-piccolo-segnale-100v-do/dp/1612346) | 471528 |  | $0.10 | $0.10 | 512-1N4148 | Link (http://www.mouser.com/ProductDetail/ON-Semiconductor-Fairchild/1N4148/?qs=sGAEpiMZZMudZehw8RjeZWbu6z6oTQTL) |  |  | $0.10 | $0.10 | 58K9570 | Link (http://www.newark.com/fairchild-semiconductor/1n4148/small-signal-diode-100v-200ma/dp/58K9570) | 3000 |  | $0.13 | $0.13 | 652-7343 | Link (http://it.rs-online.com/web/p/diodi-switching/6527343/)
FB1-FB6 | 1k @100MHz | FERRITE BEAD 1 KOHM 0805 1LN | MIDI:FB_0805_HandSoldering | Taiyo Yuden | BK2125HS102-T | 6 | $0.06 | $0.35 | 608932 |  | $0.10 | $0.60 | 587-1904-1-ND | Link (http://www.digikey.com/scripts/DkSearch/dksus.dll?WT.z_header=search_go&lang=en) |  |  | $0.06 | $0.35 | 1463452 | Link (http://it.farnell.com/taiyo-yuden/bk2125hs102-t/grano-chip-0-4ohm-300ma-0805/dp/1463452) | 79235 |  | $0.10 | $0.61 | 963-BK2125HS102-T | Link (http://www.mouser.com/Search/Refine.aspx?Keyword=963-BK2125HS102-T%20) |  |  | $0.17 | $0.99 | 86H5425 | Link (http://www.newark.com/taiyo-yuden/bk2125hs102-t/ferrite-bead-0-4ohm-300ma-0805/dp/86H5425)
J1-J3 | DIN_5 | CONN DIN 5POS FEMALE SHIELDED | MIDI:DIN5_180 | CUI Inc. | SDF-50J | 3 | $1.15 | $3.45 |  |  | $1.15 | $3.45 | CP-7050-ND | Link (http://www.digikey.com/scripts/DkSearch/dksus.dll?WT.z_header=search_go&lang=en) |  |  |  |  |  |  | 1272 |  | $1.16 | $3.48 | 490-SDF-50J | Link (http://www.mouser.com/Search/Refine.aspx?Keyword=490-SDF-50J%20)
J4,J5 | CONN_01X06 | CONN RCPT 6POS .100" SGL PCB | MIDI:Pin_Header_Straight_1x06_Pitch2.54mm | Amphenol FCI | 75915-306LF | 2 | $0.86 | $1.73 | 3448 |  | $0.90 | $1.80 | 609-3558-ND | Link (http://www.digikey.com/scripts/DkSearch/dksus.dll?WT.z_header=search_go&lang=en) |  |  | $0.87 | $1.75 | 1278226 | Link (http://it.farnell.com/webapp/wcs/stores/servlet/Search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) | 1033 |  | $0.89 | $1.79 | 649-75915-306LF | Link (http://www.mouser.com/Search/Refine.aspx?Keyword=649-75915-306LF%20) |  |  | $0.86 | $1.73 | 62K8174 | Link (http://www.newark.com/webapp/wcs/stores/servlet/Search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) |  |  | $17.62 | $35.25 | 863-3257 | Link (http://it.rs-online.com/web/c/?searchTerm=75915-306LF%20)
R1 | 1K | RES SMD 1K OHM 1% 1/2W 0804 | MIDI:R_0805_HandSoldering | Panasonic Electronic Components | ERJ-P6WF1001V | 1 | $0.09 | $0.09 | 15662 |  | $0.61 | $0.61 | P16885CT-ND | Link (http://www.digikey.com/scripts/DkSearch/dksus.dll?WT.z_header=search_go&lang=en) |  |  | $0.25 | $0.25 | 2253910 | Link (http://it.farnell.com/panasonic-electronic-components/erjp6wf1001v/res-film-spesso-1k-1-0-5w-0805/dp/2253910) | 6644 |  | $0.59 | $0.59 | 667-ERJ-P6WF1001V | Link (http://www.mouser.com/Search/Refine.aspx?Keyword=667-ERJ-P6WF1001V%20) |  |  | $0.09 | $0.09 | 31X1858 | Link (http://www.newark.com/webapp/wcs/stores/servlet/Search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) | 2300 |  | $0.12 | $0.12 | 770-8540 | Link (http://it.rs-online.com/web/p/resistori-smd/7708540/)
R10,R20,R30 | 10K | RES SMD 10K OHM 5% 1/8W 0804 | MIDI:R_0805_HandSoldering | Yageo | RC0805JR-0710KL | 3 | $0.01 | $0.03 | 2539734 |  | $0.10 | $0.30 | 311-10KARCT-ND | Link (http://www.digikey.com/scripts/DkSearch/dksus.dll?WT.z_header=search_go&lang=en) |  |  | $0.01 | $0.03 | 9234136 | Link (http://it.farnell.com/yageo-phycomp/rc0805jr-0710kl/res-film-spesso-10k-5-0-125w-0805/dp/9234136) | 426702 |  | $0.10 | $0.30 | 603-RC0805JR-0710KL | Link (http://www.mouser.com/Search/Refine.aspx?Keyword=603-RC0805JR-0710KL%20Yageo) |  |  | $0.10 | $0.30 | 68R0258 | Link (http://www.newark.com/yageo/rc0805jr-0710kl/res-thick-film-10k-5-0-125w-0805/dp/68R0258) | 8 |  | $23.36 | $70.09 | 618-5163 | Link (http://it.rs-online.com/web/c/?searchTerm=RC0805JR-0710KL%20)
R11,R16,R21,R26,R31,R36 | 18k | RES SMD 18K OHM 5% 1/8W 0804 | MIDI:R_0805_HandSoldering | Yageo | RC0805JR-0718KL | 6 | $0.01 | $0.07 | 43813 |  | $0.10 | $0.60 | 311-18KARCT-ND | Link (http://www.digikey.com/scripts/DkSearch/dksus.dll?WT.z_header=search_go&lang=en) |  |  | $0.01 | $0.07 | 9234160 | Link (http://it.farnell.com/yageo-phycomp/rc0805jr-0718kl/res-film-spesso-18k-5-0-125w-0805/dp/9234160) | 79191 |  | $0.10 | $0.61 | 603-RC0805JR-0718KL | Link (http://www.mouser.com/Search/Refine.aspx?Keyword=603-RC0805JR-0718KL%20Yageo) |  |  | $0.02 | $0.10 | 98K7741 | Link (http://www.newark.com/webapp/wcs/stores/servlet/Search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)
R13,R17,R23,R27,R33,R37 | 33k | RES SMD 33K OHM 1% 1/8W 0804 | MIDI:R_0805_HandSoldering | Yageo | RC0805FR-0733KL | 6 | $0.01 | $0.08 | 449769 |  | $0.10 | $0.60 | 311-33.0KCRCT-ND | Link (http://www.digikey.com/scripts/DkSearch/dksus.dll?WT.z_header=search_go&lang=en) |  |  | $0.01 | $0.08 | 9237810 | Link (http://it.farnell.com/yageo-phycomp/rc0805fr-0733kl/res-film-spesso-33k-1-0-125w-0805/dp/9237810) | 105236 |  | $0.10 | $0.61 | 603-RC0805FR-0733KL | Link (http://www.mouser.com/Search/Refine.aspx?Keyword=603-RC0805FR-0733KL%20Yageo) |  |  | $0.09 | $0.56 | 68R0242 | Link (http://www.newark.com/yageo/rc0805fr-0733kl/res-thick-film-33k-1-0-125w-0805/dp/68R0242)
R14,R24,R34,R42-R45,R50-R53,R58-R61 | 1k | RES SMD 1K OHM 5% 1/8W 0804 | MIDI:R_0805_HandSoldering | Yageo | RC0805JR-071KL | 15 | $0.01 | $0.15 | 3131454 |  | $0.02 | $0.28 | 311-1.0KARCT-ND | Link (http://www.digikey.com/scripts/DkSearch/dksus.dll?WT.z_header=search_go&lang=en) |  |  | $0.01 | $0.15 | 9234004 | Link (http://it.farnell.com/yageo-phycomp/rc0805jr-071kl/res-film-spesso-1k-5-0-125w-0805/dp/9234004) | 160861 |  | $0.01 | $0.20 | 603-RC0805JR-071KL | Link (http://www.mouser.com/Search/Refine.aspx?Keyword=603-RC0805JR-071KL%20Yageo) |  |  | $0.02 | $0.27 | 68R0253 | Link (http://www.newark.com/yageo/rc0805jr-071kl/res-thick-film-1k-5-0-125w-0805/dp/68R0253) | 19 |  | $19.29 | $289.40 | 618-3583 | Link (http://it.rs-online.com/web/c/?searchTerm=RC0805JR-071KL%20)
R2,R6 | 33R 0,5W | RES SMD 33 OHM 5% 1/2W 0804 | MIDI:R_0805_HandSoldering | Panasonic Electronic Components | ERJ-P06J330V | 2 | $0.01 | $0.03 | 34337 |  | $0.12 | $0.24 | P33ADCT-ND | Link (http://www.digikey.com/scripts/DkSearch/dksus.dll?WT.z_header=search_go&lang=en) |  |  |  |  |  |  | 12597 |  | $0.12 | $0.24 | 667-ERJ-P06J330V | Link (http://www.mouser.com/Search/Refine.aspx?Keyword=667-ERJ-P06J330V%20) |  |  | $0.01 | $0.03 | 50W4670 | Link (http://www.newark.com/webapp/wcs/stores/servlet/Search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)
R3 | 220R | RES SMD 220 OHM 5% 1/2W 0804 | MIDI:R_0805_HandSoldering | Panasonic Electronic Components | ERJ-P06J221V | 1 | $0.02 | $0.02 | 500931 |  | $0.12 | $0.12 | P220ADCT-ND | Link (http://www.digikey.com/scripts/DkSearch/dksus.dll?WT.z_header=search_go&lang=en) |  |  | $0.11 | $0.11 | 2281428 | Link (http://it.farnell.com/webapp/wcs/stores/servlet/Search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) | 3632 |  | $0.12 | $0.12 | 667-ERJ-P06J221V | Link (http://www.mouser.com/Search/Refine.aspx?Keyword=667-ERJ-P06J221V%20) |  |  | $0.12 | $0.12 | 53W3982 | Link (http://www.newark.com/panasonic-electronic-components/erj-p06j221v/res-thick-film-220r-5-0-5w-0805/dp/53W3982) | 2800 |  | $0.02 | $0.02 | 895-2577 | Link (http://it.rs-online.com/web/p/resistori-smd/8952577P/)
R4 | 4K7 | RES SMD 4.7K OHM 5% 1/2W 0804 | MIDI:R_0805_HandSoldering | Panasonic Electronic Components | ERJ-P06J472V | 1 | $0.11 | $0.11 | 4669 |  | $0.12 | $0.12 | P4.7KADCT-ND | Link (http://www.digikey.com/scripts/DkSearch/dksus.dll?WT.z_header=search_go&lang=en) |  |  | $0.11 | $0.11 | 2281435 | Link (http://it.farnell.com/webapp/wcs/stores/servlet/Search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) | 12286 |  | $0.12 | $0.12 | 667-ERJ-P06J472V | Link (http://www.mouser.com/Search/Refine.aspx?Keyword=667-ERJ-P06J472V%20) |  |  | $0.12 | $0.12 | 53W3987 | Link (http://www.newark.com/panasonic-electronic-components/erj-p06j472v/res-thick-film-4k7-5-0-5w-0805/dp/53W3987) | 4 |  |  |  | 919-0587 | Link (http://it.rs-online.com/web/p/resistori-smd/9190587/)
R5,R7 | 10R | RES SMD 1K OHM 1% 1/4W 0804 | MIDI:R_0805_HandSoldering | Bourns Inc. | CRS0805-FX-1001ELF | 2 | $0.08 | $0.16 | 10595 |  | $0.35 | $0.70 | CRS0805-FX-1001ELFCT-ND | Link (http://www.digikey.com/scripts/DkSearch/dksus.dll?WT.z_header=search_go&lang=en) |  |  | $0.09 | $0.17 | 2470951 | Link (http://it.farnell.com/bourns/crs0805-fx-1001elf/res-film-spesso-1k-1-0-25w-0805/dp/2470951) | 11475 |  | $0.28 | $0.56 | 652-CRS0805FX1001ELF | Link (http://www.mouser.com/Search/Refine.aspx?Keyword=652-CRS0805FX1001ELF%20) |  |  | $0.28 | $0.56 | 42Y0189 | Link (http://www.newark.com/webapp/wcs/stores/servlet/Search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) | 1850 |  | $0.08 | $0.16 | 867-2925 | Link (http://it.rs-online.com/web/c/?searchTerm=CRS0805-FX-1001ELF%20)
R8,R9,R12,R15,R18,R19,R22,R25,R28,R29,R32,R35,R38-R41,R46-R49,R54-R57 | 10k | RES SMD 10K OHM 5% 1/8W 0804 | MIDI:R_0805_HandSoldering | Yageo | RC0805JR-0710KL | 24 | $0.01 | $0.27 | 2539734 |  | $0.02 | $0.46 | 311-10KARCT-ND | Link (http://www.digikey.com/scripts/DkSearch/dksus.dll?WT.z_header=search_go&lang=en) |  |  | $0.01 | $0.27 | 9234136 | Link (http://it.farnell.com/yageo-phycomp/rc0805jr-0710kl/res-film-spesso-10k-5-0-125w-0805/dp/9234136) | 426702 |  | $0.01 | $0.31 | 603-RC0805JR-0710KL | Link (http://www.mouser.com/Search/Refine.aspx?Keyword=603-RC0805JR-0710KL%20Yageo) |  |  | $0.02 | $0.43 | 68R0258 | Link (http://www.newark.com/yageo/rc0805jr-0710kl/res-thick-film-10k-5-0-125w-0805/dp/68R0258) | 8 |  | $19.29 | $463.04 | 618-5163 | Link (http://it.rs-online.com/web/c/?searchTerm=RC0805JR-0710KL%20)
SW1-SW12 | SW_PUSH | SWITCH TACTILE SPST-NO 0.05A 24V | MIDI:SW_PUSH_6mm | TE Connectivity ALCOSWITCH Switches | 1825910-6 | 12 | $0.09 | $1.06 | 108564 |  | $0.09 | $1.06 | 450-1650-ND | Link (http://www.digikey.com/scripts/DkSearch/dksus.dll?WT.z_header=search_go&lang=en) |  |  | $0.20 | $2.42 | 2456210 | Link (http://it.farnell.com/alcoswitch-te-connectivity/1825910-6/tact-switch-spst-0-05a-24vdc-solder/dp/2456210) | 40876 |  | $0.10 | $1.21 | 506-FSM4JH | Link (http://www.mouser.com/ProductDetail/TE-Connectivity-Alcoswitch/FSM4JH/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) |  |  | $0.20 | $2.40 | 60M5365 | Link (http://www.newark.com/webapp/wcs/stores/servlet/Search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)
U1 | 6N138 | OPTOISO 5KV DARL W/BASE 8DIP | MIDI:DIP-8_W7.62mm_LongPads | Lite-On Inc. | 6N138 | 1 | $0.49 | $0.49 | 1945 |  | $0.81 | $0.81 | 160-1795-ND | Link (http://www.digikey.com/scripts/DkSearch/dksus.dll?WT.z_header=search_go&lang=en) |  |  | $1.89 | $1.89 | 1225822 | Link (http://it.farnell.com/toshiba/6n138/optocoupler-darlington-o-p/dp/1225822) | 1865 |  | $0.49 | $0.49 | 859-6N138 | Link (http://www.mouser.com/ProductDetail/Lite-On/6N138/?qs=sGAEpiMZZMs6akeJfFiy2u%252bGITOuAtJh) |  |  | $1.63 | $1.63 | 35K5294 | Link (http://www.newark.com/vishay/6n138/optocoupler-darlington-5300vrms/dp/35K5294) | 20 |  | $0.81 | $0.81 | 691-2328 | Link (http://it.rs-online.com/web/c/?searchTerm=6N138%20Lite-On%20Inc.)
U2 | 4050 | IC BUFF/CONVERTER HEX 16DIP | MIDI:DIP-16_W7.62mm_LongPads | Texas Instruments | CD4050BE | 1 | $0.51 | $0.51 | 6063 |  | $0.52 | $0.52 | 296-2056-5-ND | Link (http://www.digikey.com/scripts/DkSearch/dksus.dll?WT.z_header=search_go&lang=en) |  |  | $0.57 | $0.57 | 1106108 | Link (http://it.farnell.com/texas-instruments/cd4050be/ic-buffer-non-inv-6ch-16dip/dp/1106108) | 2597 |  | $0.51 | $0.51 | 595-CD4050BE | Link (http://www.mouser.com/ProductDetail/Texas-Instruments/CD4050BE/) |  |  | $0.51 | $0.51 | 60K5118 | Link (http://www.newark.com/texas-instruments/cd4050be/non-inverting-buffer-converter/dp/60K5118) | 7 |  | $10.15 | $10.15 | 526-543 | Link (http://it.rs-online.com/web/c/?searchTerm=CD4050BE%20)
U3 | 40106 | IC INVERTER GATE HEX 14DIP | MIDI:DIP-14_W7.62mm_LongPads | Texas Instruments | CD40106BE | 1 | $0.47 | $0.47 | 37663 |  | $0.48 | $0.48 | 296-3503-5-ND | Link (http://www.digikey.com/scripts/DkSearch/dksus.dll?WT.z_header=search_go&lang=en) |  |  | $0.53 | $0.53 | 1106097 | Link (http://it.farnell.com/texas-instruments/cd40106be/ic-hex-inverter-4000-cmos-14dip/dp/1106097) | 8093 |  | $0.47 | $0.47 | 595-CD40106BE | Link (http://www.mouser.com/ProductDetail/Texas-Instruments/CD40106BE/) |  |  | $0.48 | $0.48 | 60K5093 | Link (http://www.newark.com/texas-instruments/cd40106be/hex-inverter-schmitt-trigger-1i/dp/60K5093) | 36 |  | $9.44 | $9.44 | 526-533 | Link (http://it.rs-online.com/web/c/?searchTerm=CD40106BE%20)
U4-U6 | ENCODER_w_SWITCH | ENCODER LO PROFILE 11MM W/SWITCH | MIDI:ENC_w_SW | Bourns Inc. | PEC11L-4220F-S0015 | 3 | $2.00 | $6.00 | 2086 |  | $2.06 | $6.18 | PEC11L-4220F-S0015-ND | Link (http://www.digikey.com/scripts/DkSearch/dksus.dll?WT.z_header=search_go&lang=en) |  |  | $2.01 | $6.03 | 1857556 | Link (http://it.farnell.com/webapp/wcs/stores/servlet/Search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) | 1467 |  | $2.00 | $6.00 | 652-PEC11L4220FS0015 | Link (http://www.mouser.com/Search/Refine.aspx?Keyword=652-PEC11L4220FS0015%20) |  |  | $2.00 | $6.00 | 20T1492 | Link (http://www.newark.com/webapp/wcs/stores/servlet/Search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)
XA1 | Conn_Poncho2P_20x2_A | BERGSTIK II 0.100" DUAL ST | MIDI:PIN_ARRAY_20X2 | Amphenol FCI | 68602-140HLF | 1 | $1.35 | $1.35 | 1773 |  | $1.60 | $1.60 | 609-4724-ND | Link (http://www.digikey.com/scripts/DkSearch/dksus.dll?WT.z_header=search_go&lang=en) |  |  | $2.71 | $2.71 | 2396214 | Link (http://it.farnell.com/webapp/wcs/stores/servlet/Search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) | 354 |  | $1.60 | $1.60 | 649-68602-140HLF | Link (http://www.mouser.com/Search/Refine.aspx?Keyword=649-68602-140HLF%20) |  |  | $1.35 | $1.35 | 20M2844 | Link (http://www.newark.com/webapp/wcs/stores/servlet/Search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) |  |  | $3.95 | $3.95 | 863-3052 | Link (http://it.rs-online.com/web/c/?searchTerm=68602-140HLF%20)
XB1 | Conn_Poncho2P_20x2_B | BERGSTIK II 0.100" DUAL ST | MIDI:PIN_ARRAY_20X2 | Amphenol FCI | 68602-140HLF | 1 | $1.35 | $1.35 | 1773 |  | $1.60 | $1.60 | 609-4724-ND | Link (http://www.digikey.com/scripts/DkSearch/dksus.dll?WT.z_header=search_go&lang=en) |  |  | $2.71 | $2.71 | 2396214 | Link (http://it.farnell.com/webapp/wcs/stores/servlet/Search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) | 354 |  | $1.60 | $1.60 | 649-68602-140HLF | Link (http://www.mouser.com/Search/Refine.aspx?Keyword=649-68602-140HLF%20) |  |  | $1.35 | $1.35 | 20M2844 | Link (http://www.newark.com/webapp/wcs/stores/servlet/Search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) |  |  | $3.95 | $3.95 | 863-3052 | Link (http://it.rs-online.com/web/c/?searchTerm=68602-140HLF%20)
