ciaa/Ponchos/Simon/tools/kicost-0.1.25/tests/BoulderCreekMotherBoard.xlsx

 |  |  |  |  |  |  | Board Qty: | 100
 |  |  |  |  |  |  | Total Cost: | $0.00 |  |  |  | $0.00 |  |  |  |  |  | $0.00 |  |  |  |  |  | $0.00
 |  |  |  |  |  |  | Unit Cost: | $0.00
Global Part Info |  |  |  |  |  |  |  |  | Digi-Key |  |  |  |  |  | Mouser |  |  |  |  |  | Newark
Refs | Value | Desc | Footprint | Manf | Manf# | Qty | Unit$ | Ext$ | Avail | Purch | Unit$ | Ext$ | Cat# | Doc | Avail | Purch | Unit$ | Ext$ | Cat# | Doc | Avail | Purch | Unit$ | Ext$ | Cat# | Doc
R111,R119 | 10M |  | MISC:SM0805 |  |  | 0 | $0.00 | $0.00
TP1-TP23 | TP-TH |  | MISC:TP_TH |  |  | 0 | $0.00 | $0.00
P4-P9 | PHX_2PIN |  | Connectors_TH:Phx_2pin |  |  | 0 | $0.00 | $0.00
R102 | 240 |  | MISC:R0402 |  |  | 0 | $0.00 | $0.00
K1,K10-K14,K16-K18,K23-K28 | ALQ305 |  | MISC:ALQ305 |  |  | 0 | $0.00 | $0.00
U17 | TEMPLATE-FTSH-120-02-F-DV-ES_40PIN_MALE |  | Connectors:TEMPLATE-FTSH-120-02-F-DV-ES_40PIN_MALE |  |  | 0 | $0.00 | $0.00
U14 | LM337 |  | MISC:LM337KC |  |  | 0 | $0.00 | $0.00
P2,P3 | DC_JACK |  | MISC:DC_JACK_3P_LOCAL |  |  | 0 | $0.00 | $0.00
Q5 | N-MOS(T2N7002AK) |  | MISC:2N7002_SOT-23 |  |  | 0 | $0.00 | $0.00
R1 | NC |  | MISC:R0402 |  |  | 0 | $0.00 | $0.00
R105,R108 | 350 |  | MISC:R0402 |  |  | 0 | $0.00 | $0.00
TP24,TP25 | TP-SMD |  | MISC:TP_SMD |  |  | 0 | $0.00 | $0.00
Q7 | P-MOS(DMP3056L) |  | MISC:DMP3056L-SOT23AB |  |  | 0 | $0.00 | $0.00
R106,R109 | 100 |  | MISC:R0402 |  |  | 0 | $0.00 | $0.00
U15,U16 | THS4041 |  | Analog:THS4041ID |  |  | 0 | $0.00 | $0.00
C53 | 1uF |  | MISC:CASEC_6032 |  |  | 0 | $0.00 | $0.00
J1 | NANOGraBIT |  | Connectors:NANO-GrabIT_DB_96P |  |  | 0 | $0.00 | $0.00
R110,R118 | 191M |  | MISC:SM0805 |  |  | 0 | $0.00 | $0.00
C54,C56,C58,C60,C66 | 10uF |  | MISC:SM0805 |  |  | 0 | $0.00 | $0.00
U10,U11 | 74LVCH8T245PW118 |  | Digital:74LVCH8T245PW118 |  |  | 0 | $0.00 | $0.00
U1 | OPA277UA-ND |  | Analog:OPA277UA-ND_8P_SOIC |  |  | 0 | $0.00 | $0.00
J2,J3,J6,J11,J12 | 3P_JMP_TH |  | Connectors_TH:3PINJUMP_TH |  |  | 0 | $0.00 | $0.00
U2-U5 | 74HC595 |  | Digital:74HC595_SO-16 |  |  | 0 | $0.00 | $0.00
R99,R101 | 27k |  | MISC:R0402 |  |  | 0 | $0.00 | $0.00
C18,C19 | 2.2uF |  | MISC:SM0805 |  |  | 0 | $0.00 | $0.00
R149 | 250 |  | MISC:R0603 |  |  | 0 | $0.00 | $0.00
R47-R63,R65-R67,R136-R139 | 100E |  | MISC:R0402 |  |  | 0 | $0.00 | $0.00
C2,C4,C6-C17,C20-C24,C26,C31-C34,C41,C42,C45,C46,C51,C52,C55,C57,C59,C61-C65 | 0.1uF |  | MISC:C0402 |  |  | 0 | $0.00 | $0.00
Q1-Q4 | IRF530A |  | MISC:IRF530 |  |  | 0 | $0.00 | $0.00
R98,R100,R124 | 45k |  | MISC:R0402 |  |  | 0 | $0.00 | $0.00
R7-R46,R68-R71,R73,R74,R82-R86,R88,R89,R97,R148 | 10k |  | MISC:R0402 |  |  | 0 | $0.00 | $0.00
J7-J10,J13 | 2P_JMP_TH |  | Connectors_TH:2PINJUMP_TH |  |  | 0 | $0.00 | $0.00
C5 | NC |  | MISC:SM0805 |  |  | 0 | $0.00 | $0.00
K19-K22 | RTE24005F |  | MISC:RTE24005F |  |  | 0 | $0.00 | $0.00
R103 | 750 |  | MISC:R0402 |  |  | 0 | $0.00 | $0.00
R116,R117 | 0E |  | MISC:SM0805 |  |  | 0 | $0.00 | $0.00
P12 | QSE-014-01-L-D-DP-A |  | Connectors:QSE-014-01-L-D-DP-A |  |  | 0 | $0.00 | $0.00
K2-K9,K15,K29-K32 | IMO3TS |  | MISC:IM03TS |  |  | 0 | $0.00 | $0.00
C67 | NC (1210) |  | MISC:SM1210 |  |  | 0 | $0.00 | $0.00
U12,U13 | TPS79601DGQG4 |  | MISC:TPS79601DCQG4 |  |  | 0 | $0.00 | $0.00
C1,C3,C43,C44 | 1uF |  | MISC:SM0805 |  |  | 0 | $0.00 | $0.00
R150 | 2.5k |  | MISC:R0402 |  |  | 0 | $0.00 | $0.00
P1 | PHX_3PIN |  | Connectors_TH:Phx_3pin |  |  | 0 | $0.00 | $0.00
C37,C38 | 33pF |  | MISC:C0402 |  |  | 0 | $0.00 | $0.00
R2-R6,R72,R75-R81,R87,R90-R96,R112-R114,R120-R123,R125-R135,R140-R147 | 0E |  | MISC:R0402 |  |  | 0 | $0.00 | $0.00
J4,J5 | SMA_TH |  | Connectors_TH:SMA_TH |  |  | 0 | $0.00 | $0.00
D1-D6 | LED |  | MISC:LED_0805 |  |  | 0 | $0.00 | $0.00
R104,R107 | 1k |  | MISC:R0402 |  |  | 0 | $0.00 | $0.00
U6-U9 | ULN2803A |  | MISC:ULN2803A_SOIC_18P_WIDE |  |  | 0 | $0.00 | $0.00
R115 | 0.1E_2.5W |  | MISC:R_2.5W_Local |  |  | 0 | $0.00 | $0.00
 |  |  |  |  |  |  |  |  |  | 0 | 0 | 0 |  |  |  | 0 | 0 | 0 |  |  |  | 0 | 0 | 0
 |  |  |  |  |  |  |  |  |  | 0 | 0 | 0 |  |  |  | 0 | 0 | 0 |  |  |  | 0 | 0 | 0
 |  |  |  |  |  |  |  |  |  | 0 | 0 | 0 |  |  |  | 0 | 0 | 0 |  |  |  | 0 | 0 | 0
 |  |  |  |  |  |  |  |  |  | 0 | 0 | 0 |  |  |  | 0 | 0 | 0 |  |  |  | 0 | 0 | 0
 |  |  |  |  |  |  |  |  |  | 0 | 0 | 0 |  |  |  | 0 | 0 | 0 |  |  |  | 0 | 0 | 0
 |  |  |  |  |  |  |  |  |  | 0 | 0 | 0 |  |  |  | 0 | 0 | 0 |  |  |  | 0 | 0 | 0
 |  |  |  |  |  |  |  |  |  | 0 | 0 | 0 |  |  |  | 0 | 0 | 0 |  |  |  | 0 | 0 | 0
 |  |  |  |  |  |  |  |  |  | 0 | 0 | 0 |  |  |  | 0 | 0 | 0 |  |  |  | 0 | 0 | 0
 |  |  |  |  |  |  |  |  |  | 0 | 0 | 0 |  |  |  | 0 | 0 | 0 |  |  |  | 0 | 0 | 0
 |  |  |  |  |  |  |  |  |  | 0 | 0 | 0 |  |  |  | 0 | 0 | 0 |  |  |  | 0 | 0 | 0
 |  |  |  |  |  |  |  |  |  | 0 | 0 | 0 |  |  |  | 0 | 0 | 0 |  |  |  | 0 | 0 | 0
 |  |  |  |  |  |  |  |  |  | 0 | 0 | 0 |  |  |  | 0 | 0 | 0 |  |  |  | 0 | 0 | 0
 |  |  |  |  |  |  |  |  |  | 0 | 0 | 0 |  |  |  | 0 | 0 | 0 |  |  |  | 0 | 0 | 0
 |  |  |  |  |  |  |  |  |  | 0 | 0 | 0 |  |  |  | 0 | 0 | 0 |  |  |  | 0 | 0 | 0
 |  |  |  |  |  |  |  |  |  | 0 | 0 | 0 |  |  |  | 0 | 0 | 0 |  |  |  | 0 | 0 | 0
 |  |  |  |  |  |  |  |  |  | 0 | 0 | 0 |  |  |  | 0 | 0 | 0 |  |  |  | 0 | 0 | 0
 |  |  |  |  |  |  |  |  |  | 0 | 0 | 0 |  |  |  | 0 | 0 | 0 |  |  |  | 0 | 0 | 0
 |  |  |  |  |  |  |  |  |  | 0 | 0 | 0 |  |  |  | 0 | 0 | 0 |  |  |  | 0 | 0 | 0
 |  |  |  |  |  |  |  |  |  | 0 | 0 | 0 |  |  |  | 0 | 0 | 0 |  |  |  | 0 | 0 | 0
 |  |  |  |  |  |  |  |  |  | 0 | 0 | 0 |  |  |  | 0 | 0 | 0 |  |  |  | 0 | 0 | 0
 |  |  |  |  |  |  |  |  |  | 0 | 0 | 0 |  |  |  | 0 | 0 | 0 |  |  |  | 0 | 0 | 0
 |  |  |  |  |  |  |  |  |  | 0 | 0 | 0 |  |  |  | 0 | 0 | 0 |  |  |  | 0 | 0 | 0
 |  |  |  |  |  |  |  |  |  | 0 | 0 | 0 |  |  |  | 0 | 0 | 0 |  |  |  | 0 | 0 | 0
 |  |  |  |  |  |  |  |  |  | 0 | 0 | 0 |  |  |  | 0 | 0 | 0 |  |  |  | 0 | 0 | 0
 |  |  |  |  |  |  |  |  |  | 0 | 0 | 0 |  |  |  | 0 | 0 | 0 |  |  |  | 0 | 0 | 0
 |  |  |  |  |  |  |  |  |  | 0 | 0 | 0 |  |  |  | 0 | 0 | 0 |  |  |  | 0 | 0 | 0
 |  |  |  |  |  |  |  |  |  | 0 | 0 | 0 |  |  |  | 0 | 0 | 0 |  |  |  | 0 | 0 | 0
 |  |  |  |  |  |  |  |  |  | 0 | 0 | 0 |  |  |  | 0 | 0 | 0 |  |  |  | 0 | 0 | 0
 |  |  |  |  |  |  |  |  |  | 0 | 0 | 0 |  |  |  | 0 | 0 | 0 |  |  |  | 0 | 0 | 0
 |  |  |  |  |  |  |  |  |  | 0 | 0 | 0 |  |  |  | 0 | 0 | 0 |  |  |  | 0 | 0 | 0
 |  |  |  |  |  |  |  |  |  | 0 | 0 | 0 |  |  |  | 0 | 0 | 0 |  |  |  | 0 | 0 | 0
 |  |  |  |  |  |  |  |  |  | 0 | 0 | 0 |  |  |  | 0 | 0 | 0 |  |  |  | 0 | 0 | 0
 |  |  |  |  |  |  |  |  |  | 0 | 0 | 0 |  |  |  | 0 | 0 | 0 |  |  |  | 0 | 0 | 0
 |  |  |  |  |  |  |  |  |  | 0 | 0 | 0 |  |  |  | 0 | 0 | 0 |  |  |  | 0 | 0 | 0
 |  |  |  |  |  |  |  |  |  | 0 | 0 | 0 |  |  |  | 0 | 0 | 0 |  |  |  | 0 | 0 | 0
 |  |  |  |  |  |  |  |  |  | 0 | 0 | 0 |  |  |  | 0 | 0 | 0 |  |  |  | 0 | 0 | 0
 |  |  |  |  |  |  |  |  |  | 0 | 0 | 0 |  |  |  | 0 | 0 | 0 |  |  |  | 0 | 0 | 0
 |  |  |  |  |  |  |  |  |  | 0 | 0 | 0 |  |  |  | 0 | 0 | 0 |  |  |  | 0 | 0 | 0
 |  |  |  |  |  |  |  |  |  | 0 | 0 | 0 |  |  |  | 0 | 0 | 0 |  |  |  | 0 | 0 | 0
 |  |  |  |  |  |  |  |  |  | 0 | 0 | 0 |  |  |  | 0 | 0 | 0 |  |  |  | 0 | 0 | 0
 |  |  |  |  |  |  |  |  |  | 0 | 0 | 0 |  |  |  | 0 | 0 | 0 |  |  |  | 0 | 0 | 0
 |  |  |  |  |  |  |  |  |  | 0 | 0 | 0 |  |  |  | 0 | 0 | 0 |  |  |  | 0 | 0 | 0
 |  |  |  |  |  |  |  |  |  | 0 | 0 | 0 |  |  |  | 0 | 0 | 0 |  |  |  | 0 | 0 | 0
 |  |  |  |  |  |  |  |  |  | 0 | 0 | 0 |  |  |  | 0 | 0 | 0 |  |  |  | 0 | 0 | 0
 |  |  |  |  |  |  |  |  |  | 0 | 0 | 0 |  |  |  | 0 | 0 | 0 |  |  |  | 0 | 0 | 0
 |  |  |  |  |  |  |  |  |  | 0 | 0 | 0 |  |  |  | 0 | 0 | 0 |  |  |  | 0 | 0 | 0
 |  |  |  |  |  |  |  |  |  | 0 | 0 | 0 |  |  |  | 0 | 0 | 0 |  |  |  | 0 | 0 | 0
 |  |  |  |  |  |  |  |  |  | 0 | 0 | 0 |  |  |  | 0 | 0 | 0 |  |  |  | 0 | 0 | 0
 |  |  |  |  |  |  |  |  |  | 0 | 0 | 0 |  |  |  | 0 | 0 | 0 |  |  |  | 0 | 0 | 0
 |  |  |  |  |  |  |  |  |  | 0 | 0 | 0 |  |  |  | 0 | 0 | 0 |  |  |  | 0 | 0 | 0
