ciaa/Ponchos/Simon/tools/kicost-0.1.25/tests/fitting_test.xlsx

 |  |  |  |  |  |  | Board Qty: | 100
 |  |  |  |  |  |  | Total Cost: | $0.00 |  |  |  | $0.00 |  |  |  |  |  | $0.00 |  |  |  |  |  | $0.00 |  |  |  |  |  | $0.00 |  |  |  |  |  | $0.00
 |  |  |  |  |  |  | Unit Cost: | $0.00
Global Part Info |  |  |  |  |  |  |  |  | Digi-Key |  |  |  |  |  | Mouser |  |  |  |  |  | Newark |  |  |  |  |  | Beyondcomponents |  |  |  |  |  | Local
Refs | Value | Desc | Footprint | Manf | Manf# | Qty | Unit$ | Ext$ | Avail | Purch | Unit$ | Ext$ | Cat# | Doc | Avail | Purch | Unit$ | Ext$ | Cat# | Doc | Avail | Purch | Unit$ | Ext$ | Cat# | Doc | Avail | Purch | Unit$ | Ext$ | Cat# | Doc | Avail | Purch | Unit$ | Ext$ | Cat# | Doc
SW1 | SW_PUSH |  | XESS:RS-282G05A3-SM_RT |  |  | 0 | $0.00 | $0.00
JP4-JP10,TP1 | JUMPER |  | XESS:HDR_1x2 |  |  | 0 | $0.00 | $0.00 |  |  |  |  |  |  |  |  |  |  |  |  |  |  |  |  |  |  |  |  |  |  |  |  |  |  | $0.00 | $0.00 | #324EA3AD
PM1,PM2 | PMOD_SCKT-12 |  | XESS:PMOD_SCKT-12 |  | 2553-2x6G | 0 | $0.00 | $0.00 |  |  |  |  |  |  |  |  |  |  |  |  |  |  |  |  |  |  |  |  | $0.00 | $0.00 | 2553-2x6G | Link (http:///www.beyondcomponents.com)
CON1 | BARREL_JACK |  | Connect:BARREL_JACK |  |  | 0 | $0.00 | $0.00
U2 | CAT24C32 |  | SMD_Packages:SOIC-8-N |  | CAT24C32WI-GT3 | 0 | $0.00 | $0.00 | 5768 |  | $0.00 | $0.00 | CAT24C32WI-GT3CT-ND | Link (http://www.digikey.com/product-detail/en/CAT24C32WI-GT3/CAT24C32WI-GT3CT-ND/1631159) |  |  |  |  |  |  | 5827 |  | $0.00 | $0.00 | 08R5414 | Link (http://www.newark.com/on-semiconductor/cat24c32wi-gt3/serial-eeprom-32kbit-400khz-soic/dp/08R5414)
GR1-GR3 | Grove |  | XESS:GROVE_MALE |  |  | 0 | $0.00 | $0.00
U1 | AZ1117EH-3.3 |  | XESS:SOT-223 |  | AZ1117EH-3.3TRG1 | 0 | $0.00 | $0.00 | 7671 |  | $0.00 | $0.00 | AZ1117EH-3.3TRG1DICT-ND | Link (http://www.digikey.com/product-detail/en/AZ1117EH-3.3TRG1/AZ1117EH-3.3TRG1DICT-ND/5001336) | 13883 |  | $0.00 | $0.00 | 621-AZ1117EH-3.3TRG1 | Link (http://www.mouser.com/Search/Refine.aspx?Keyword=AZ1117EH-3.3TRG1)
JP1-JP3 | JUMPER3 |  | XESS:HDR_1x3 |  |  | 0 | $0.00 | $0.00 |  |  |  |  |  |  |  |  |  |  |  |  |  |  |  |  |  |  |  |  |  |  |  |  |  |  | $0.00 | $0.00 | #66792985
R1 | 1K |  | Resistors_SMD:R_0805_HandSoldering |  | RC0805JR-071KL | 0 | $0.00 | $0.00 | 1026057 |  | $0.00 | $0.00 | 311-1.0KARCT-ND | Link (http://www.digikey.com/product-detail/en/RC0805JR-071KL/311-1.0KARCT-ND/731165) | 64938 |  | $0.00 | $0.00 | 603-RC0805JR-071KL | Link (http://www.mouser.com/Search/Refine.aspx?Keyword=RC0805JR-071KL) | 2950 |  | $0.00 | $0.00 | 68R0253 | Link (http://www.newark.com/yageo/rc0805jr-071kl/res-thick-film-1k-5-0-125w-0805/dp/68R0253)
C2,C4 | 4.7uF |  | Resistors_SMD:R_0805_HandSoldering |  | LMK212BJ475KD-T | 0 | $0.00 | $0.00 | 86066 |  | $0.00 | $0.00 | 587-1297-1-ND | Link (http://www.digikey.com/product-detail/en/LMK212BJ475KD-T/587-1297-1-ND/931074) |  |  |  |  |  |  | 1322 |  | $0.00 | $0.00 | 18J2726 | Link (http://www.newark.com/taiyo-yuden/lmk212bj475kd-t/ceramic-capacitor-4-7uf-10v-x5r/dp/18J2726)
RN1 | 3.9K |  | XESS:CTS_742C043 |  | 742C083392JP | 0 | $0.00 | $0.00 | 31931 |  | $0.00 | $0.00 | 742C083392JPCT-ND | Link (http://www.digikey.com/product-detail/en/742C083392JP/742C083392JPCT-ND/1124537)
C5 | 0.1uF |  | Resistors_SMD:R_0805_HandSoldering |  | 08055C104KAT2A | 0 | $0.00 | $0.00 | 10189790 |  | $0.00 | $0.00 | 478-1395-1-ND | Link (http://www.digikey.com/product-detail/en/08055C104KAT2A/478-1395-1-ND/564427) | 2475229 |  | $0.00 | $0.00 | 581-08055C104K | Link (http://www.mouser.com/Search/Refine.aspx?Keyword=08055C104KAT2A)
C1,C3 | 22uF |  | Capacitors_SMD:c_elec_5x5.3 |  | UWX1C220MCL1GB | 0 | $0.00 | $0.00 | 9573 |  | $0.00 | $0.00 | 493-2101-1-ND | Link (http://www.digikey.com/product-detail/en/UWX1C220MCL1GB/493-2101-1-ND/590076) |  |  |  |  |  |  | 2302 |  | $0.00 | $0.00 | 58R3621 | Link (http://www.newark.com/nichicon/uwx1c220mcl1gb/aluminum-electrolytic-capacitor/dp/58R3621)
PM3 | PMOD_SCKT-12 |  | XESS:PMOD_SCKT-12 |  |  | 0 | $0.00 | $0.00
J3-J5 | JSHORTNORMAL |  | XESS:xess-JSHORT |  |  | 0 | $0.00 | $0.00
GPIO1 | RPi_GPIO |  | RPi_Hat:Pin_Header_Straight_2x20 |  |  | 0 | $0.00 | $0.00
J1 | XuLA_IO_HDR |  | XESS:XuLA_IO_Hdr |  |  | 0 | $0.00 | $0.00
 |  |  |  |  |  |  |  |  |  | 0 | 0 | 0 |  |  |  | 0 | 0 | 0 |  |  |  | 0 | 0 | 0 |  |  |  | 0 | 0 | 0 |  |  |  | 0 | 0 | 0
 |  |  |  |  |  |  |  |  |  | 0 | 0 | 0 |  |  |  | 0 | 0 | 0 |  |  |  | 0 | 0 | 0 |  |  |  | 0 | 0 | 0 |  |  |  | 0 | 0 | 0
 |  |  |  |  |  |  |  |  |  | 0 | 0 | 0 |  |  |  | 0 | 0 | 0 |  |  |  | 0 | 0 | 0 |  |  |  | 0 | 0 | 0 |  |  |  | 0 | 0 | 0
 |  |  |  |  |  |  |  |  |  | 0 | 0 | 0 |  |  |  | 0 | 0 | 0 |  |  |  | 0 | 0 | 0 |  |  |  | 0 | 0 | 0 |  |  |  | 0 | 0 | 0
 |  |  |  |  |  |  |  |  |  | 0 | 0 | 0 |  |  |  | 0 | 0 | 0 |  |  |  | 0 | 0 | 0 |  |  |  | 0 | 0 | 0 |  |  |  | 0 | 0 | 0
 |  |  |  |  |  |  |  |  |  | 0 | 0 | 0 |  |  |  | 0 | 0 | 0 |  |  |  | 0 | 0 | 0 |  |  |  | 0 | 0 | 0 |  |  |  | 0 | 0 | 0
 |  |  |  |  |  |  |  |  |  | 0 | 0 | 0 |  |  |  | 0 | 0 | 0 |  |  |  | 0 | 0 | 0 |  |  |  | 0 | 0 | 0 |  |  |  | 0 | 0 | 0
 |  |  |  |  |  |  |  |  |  | 0 | 0 | 0 |  |  |  | 0 | 0 | 0 |  |  |  | 0 | 0 | 0 |  |  |  | 0 | 0 | 0 |  |  |  | 0 | 0 | 0
 |  |  |  |  |  |  |  |  |  | 0 | 0 | 0 |  |  |  | 0 | 0 | 0 |  |  |  | 0 | 0 | 0 |  |  |  | 0 | 0 | 0 |  |  |  | 0 | 0 | 0
 |  |  |  |  |  |  |  |  |  | 0 | 0 | 0 |  |  |  | 0 | 0 | 0 |  |  |  | 0 | 0 | 0 |  |  |  | 0 | 0 | 0 |  |  |  | 0 | 0 | 0
 |  |  |  |  |  |  |  |  |  | 0 | 0 | 0 |  |  |  | 0 | 0 | 0 |  |  |  | 0 | 0 | 0 |  |  |  | 0 | 0 | 0 |  |  |  | 0 | 0 | 0
 |  |  |  |  |  |  |  |  |  | 0 | 0 | 0 |  |  |  | 0 | 0 | 0 |  |  |  | 0 | 0 | 0 |  |  |  | 0 | 0 | 0 |  |  |  | 0 | 0 | 0
 |  |  |  |  |  |  |  |  |  | 0 | 0 | 0 |  |  |  | 0 | 0 | 0 |  |  |  | 0 | 0 | 0 |  |  |  | 0 | 0 | 0 |  |  |  | 0 | 0 | 0
 |  |  |  |  |  |  |  |  |  | 0 | 0 | 0 |  |  |  | 0 | 0 | 0 |  |  |  | 0 | 0 | 0 |  |  |  | 0 | 0 | 0 |  |  |  | 0 | 0 | 0
 |  |  |  |  |  |  |  |  |  | 0 | 0 | 0 |  |  |  | 0 | 0 | 0 |  |  |  | 0 | 0 | 0 |  |  |  | 0 | 0 | 0 |  |  |  | 0 | 0 | 0
 |  |  |  |  |  |  |  |  |  | 0 | 0 | 0 |  |  |  | 0 | 0 | 0 |  |  |  | 0 | 0 | 0 |  |  |  | 0 | 0 | 0 |  |  |  | 0 | 0 | 0
 |  |  |  |  |  |  |  |  |  | 0 | 0 | 0 |  |  |  | 0 | 0 | 0 |  |  |  | 0 | 0 | 0 |  |  |  | 0 | 0 | 0 |  |  |  | 0 | 0 | 0
