ciaa/Ponchos/Simon/tools/kicost-0.1.25/tests/StickIt-Hat.xlsx

 |  |  |  |  |  |  | Board Qty: | 100
 |  |  |  |  |  |  | Total Cost: | $0.00 |  |  |  | $0.00 |  |  |  |  |  | $0.00 |  |  |  |  |  | $0.00 |  |  |  |  |  | $0.00 |  |  |  |  |  | $0.00
 |  |  |  |  |  |  | Unit Cost: | $0.00
Global Part Info |  |  |  |  |  |  |  |  | Digi-Key |  |  |  |  |  | Mouser |  |  |  |  |  | Newark |  |  |  |  |  | Beyondcomponents |  |  |  |  |  | Local
Refs | Value | Desc | Footprint | Manf | Manf# | Qty | Unit$ | Ext$ | Avail | Purch | Unit$ | Ext$ | Cat# | Doc | Avail | Purch | Unit$ | Ext$ | Cat# | Doc | Avail | Purch | Unit$ | Ext$ | Cat# | Doc | Avail | Purch | Unit$ | Ext$ | Cat# | Doc | Avail | Purch | Unit$ | Ext$ | Cat# | Doc
JP5,JP6 | JUMPER |  | XESS:HDR_1x2 |  |  | 0 | $0.00 | $0.00
SW1 | SW_PUSH |  | XESS:RS-282G05A3-SM_RT |  | RS-282G05A3-SM RT | 0 | $0.00 | $0.00 | 6666 |  | $0.00 | $0.00 | CKN10384CT-ND | Link (http://www.digikey.com/product-detail/en/c-k-components/RS-282G05A3-SM-RT/CKN10384CT-ND/2747203) | 11941 |  | $0.00 | $0.00 | 611-RS-282G05A3-SMRT | Link (http://www.mouser.com/Search/../ProductDetail/CK-Components/RS-282G05A3-SM-RT/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)
JP4,JP7-JP10,TP1 | JUMPER |  | XESS:HDR_1x2 |  |  | 0 | $0.00 | $0.00 |  |  |  |  |  |  |  |  |  |  |  |  |  |  |  |  |  |  |  |  |  |  |  |  | 0 |  | $0.00 | $0.00 | #09A4CCBF
GPIO1 | RPi_GPIO |  | RPi_Hat:Pin_Header_Straight_2x20 |  |  | 0 | $0.00 | $0.00
J3-J5 | JSHORTNORMAL |  | XESS:xess-JSHORT |  |  | 0 | $0.00 | $0.00
U1 | AZ1117EH-3.3 |  | XESS:SOT-223 |  | AZ1117EH-3.3TRG1 | 0 | $0.00 | $0.00 | 9366 |  | $0.00 | $0.00 | AZ1117EH-3.3TRG1DICT-ND | Link (http://www.digikey.com/product-detail/en/diodes-incorporated/AZ1117EH-3.3TRG1/AZ1117EH-3.3TRG1DICT-ND/5001336) | 490 |  | $0.00 | $0.00 | 621-AZ1117EH-3.3TRG1 | Link (http://www.mouser.com/Search/Refine.aspx?Keyword=AZ1117EH-3.3TRG1%20)
C5 | 0.1uF |  | Resistors_SMD:R_0805_HandSoldering |  | 08055C104KAT2A | 0 | $0.00 | $0.00 | 6637140 |  | $0.00 | $0.00 | 478-1395-1-ND | Link (http://www.digikey.com/product-detail/en/avx-corporation/08055C104KAT2A/478-1395-1-ND/564427) | 1820740 |  | $0.00 | $0.00 | 581-08055C104K | Link (http://www.mouser.com/Search/Refine.aspx?Keyword=08055C104KAT2A%20)
C1,C3 | 22uF |  | Capacitors_SMD:c_elec_5x5.3 |  | UWX1C220MCL1GB | 0 | $0.00 | $0.00 | 12169 |  | $0.00 | $0.00 | 493-2101-1-ND | Link (http://www.digikey.com/product-detail/en/nichicon/UWX1C220MCL1GB/493-2101-1-ND/590076) | 6105 |  | $0.00 | $0.00 | 647-UWX1C220MCL1 | Link (http://www.mouser.com/Search/Refine.aspx?Keyword=UWX1C220MCL1GB%20) | 1302 |  | $0.00 | $0.00 | 58R3621 | Link (http://www.newark.com/nichicon/uwx1c220mcl1gb/aluminum-electrolytic-capacitor/dp/58R3621)
CON1 | BARREL_JACK |  | Connect:BARREL_JACK |  | PJ-002A | 0 | $0.00 | $0.00 | 71053 |  | $0.00 | $0.00 | CP-002A-ND | Link (http://www.digikey.com/product-detail/en/cui-inc/PJ-002A/CP-002A-ND/96962) | 11899 |  | $0.00 | $0.00 | 490-PJ-002A | Link (http://www.mouser.com/Search/../ProductDetail/CUI/PJ-002A/) |  |  |  |  |  | Link (http://www.newark.com/webapp/wcs/stores/servlet/Search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)
J1 | XuLA_IO_HDR |  | XESS:XuLA_IO_Hdr |  |  | 0 | $0.00 | $0.00
C2,C4 | 4.7uF |  | Resistors_SMD:R_0805_HandSoldering |  | LMK212BJ475KD-T | 0 | $0.00 | $0.00 | 131532 |  | $0.00 | $0.00 | 587-1297-1-ND | Link (http://www.digikey.com/product-detail/en/taiyo-yuden/LMK212BJ475KD-T/587-1297-1-ND/931074) | 12638 |  | $0.00 | $0.00 | 963-LMK212BJ475KD-T | Link (http://www.mouser.com/Search/Refine.aspx?Keyword=LMK212BJ475KD-T%20) | 427 |  | $0.00 | $0.00 | 18J2726 | Link (http://www.newark.com/webapp/wcs/stores/servlet/Search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)
U2 | CAT24C32 |  | SMD_Packages:SOIC-8-N |  | CAT24C32WI-GT3 | 0 | $0.00 | $0.00 | 2993 |  | $0.00 | $0.00 | CAT24C32WI-GT3CT-ND | Link (http://www.digikey.com/product-detail/en/on-semiconductor/CAT24C32WI-GT3/CAT24C32WI-GT3CT-ND/1631159) | 11027 |  | $0.00 | $0.00 | 698-CAT24C32WI-GT3 | Link (http://www.mouser.com/Search/../ProductDetail/ON-Semiconductor/CAT24C32WI-GT3/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) | 5272 |  | $0.00 | $0.00 | 08R5414 | Link (http://www.newark.com/on-semiconductor/cat24c32wi-gt3/serial-eeprom-32kbit-400khz-soic/dp/08R5414)
JP1-JP3 | JUMPER3 |  | XESS:HDR_1x3 |  |  | 0 | $0.00 | $0.00 |  |  |  |  |  |  |  |  |  |  |  |  |  |  |  |  |  |  |  |  |  |  |  |  | 0 |  | $0.00 | $0.00 | #3697ECFD
GR1-GR3 | Grove |  | XESS:GROVE_MALE |  |  | 0 | $0.00 | $0.00
R1 | 1K |  | Resistors_SMD:R_0805_HandSoldering |  | RC0805JR-071KL | 0 | $0.00 | $0.00 | 1519791 |  | $0.00 | $0.00 | 311-1.0KARCT-ND | Link (http://www.digikey.com/product-detail/en/yageo/RC0805JR-071KL/311-1.0KARCT-ND/731165) | 83998 |  | $0.00 | $0.00 | 603-RC0805JR-071KL | Link (http://www.mouser.com/Search/Refine.aspx?Keyword=RC0805JR-071KL%20) | 6592 |  | $0.00 | $0.00 | 98K7729 | Link (http://www.newark.com/yageo-phycomp/rc0805jr-071kl/surface-mount-thick-film-resistor/dp/98K7729)
RN1 | 3.9K |  | XESS:CTS_742C043 |  | 742C083392JP | 0 | $0.00 | $0.00 | 26778 |  | $0.00 | $0.00 | 742C083392JPCT-ND | Link (http://www.digikey.com/product-detail/en/cts-resistor-products/742C083392JP/742C083392JPCT-ND/1124537) | 16631 |  | $0.00 | $0.00 | 774-742C083392JP | Link (http://www.mouser.com/Search/Refine.aspx?Keyword=742C083392JP%20)
PM1-PM3 | PMOD_SCKT-12 |  | XESS:PMOD_SCKT-12 | Ho Chien | 2553-2x6G | 0 | $0.00 | $0.00 |  |  |  |  |  |  |  |  |  |  |  |  |  |  |  |  |  |  | 0 |  | $0.00 | $0.00 | 2553-2x6G | Link (http:///www.beyondcomponents.com)
 |  |  |  |  |  |  |  |  |  | 0 | 0 | 0 |  |  |  | 0 | 0 | 0 |  |  |  | 0 | 0 | 0 |  |  |  | 0 | 0 | 0 |  |  |  | 0 | 0 | 0
 |  |  |  |  |  |  |  |  |  | 0 | 0 | 0 |  |  |  | 0 | 0 | 0 |  |  |  | 0 | 0 | 0 |  |  |  | 0 | 0 | 0 |  |  |  | 0 | 0 | 0
 |  |  |  |  |  |  |  |  |  | 0 | 0 | 0 |  |  |  | 0 | 0 | 0 |  |  |  | 0 | 0 | 0 |  |  |  | 0 | 0 | 0 |  |  |  | 0 | 0 | 0
 |  |  |  |  |  |  |  |  |  | 0 | 0 | 0 |  |  |  | 0 | 0 | 0 |  |  |  | 0 | 0 | 0 |  |  |  | 0 | 0 | 0 |  |  |  | 0 | 0 | 0
 |  |  |  |  |  |  |  |  |  | 0 | 0 | 0 |  |  |  | 0 | 0 | 0 |  |  |  | 0 | 0 | 0 |  |  |  | 0 | 0 | 0 |  |  |  | 0 | 0 | 0
 |  |  |  |  |  |  |  |  |  | 0 | 0 | 0 |  |  |  | 0 | 0 | 0 |  |  |  | 0 | 0 | 0 |  |  |  | 0 | 0 | 0 |  |  |  | 0 | 0 | 0
 |  |  |  |  |  |  |  |  |  | 0 | 0 | 0 |  |  |  | 0 | 0 | 0 |  |  |  | 0 | 0 | 0 |  |  |  | 0 | 0 | 0 |  |  |  | 0 | 0 | 0
 |  |  |  |  |  |  |  |  |  | 0 | 0 | 0 |  |  |  | 0 | 0 | 0 |  |  |  | 0 | 0 | 0 |  |  |  | 0 | 0 | 0 |  |  |  | 0 | 0 | 0
 |  |  |  |  |  |  |  |  |  | 0 | 0 | 0 |  |  |  | 0 | 0 | 0 |  |  |  | 0 | 0 | 0 |  |  |  | 0 | 0 | 0 |  |  |  | 0 | 0 | 0
 |  |  |  |  |  |  |  |  |  | 0 | 0 | 0 |  |  |  | 0 | 0 | 0 |  |  |  | 0 | 0 | 0 |  |  |  | 0 | 0 | 0 |  |  |  | 0 | 0 | 0
 |  |  |  |  |  |  |  |  |  | 0 | 0 | 0 |  |  |  | 0 | 0 | 0 |  |  |  | 0 | 0 | 0 |  |  |  | 0 | 0 | 0 |  |  |  | 0 | 0 | 0
 |  |  |  |  |  |  |  |  |  | 0 | 0 | 0 |  |  |  | 0 | 0 | 0 |  |  |  | 0 | 0 | 0 |  |  |  | 0 | 0 | 0 |  |  |  | 0 | 0 | 0
 |  |  |  |  |  |  |  |  |  | 0 | 0 | 0 |  |  |  | 0 | 0 | 0 |  |  |  | 0 | 0 | 0 |  |  |  | 0 | 0 | 0 |  |  |  | 0 | 0 | 0
 |  |  |  |  |  |  |  |  |  | 0 | 0 | 0 |  |  |  | 0 | 0 | 0 |  |  |  | 0 | 0 | 0 |  |  |  | 0 | 0 | 0 |  |  |  | 0 | 0 | 0
 |  |  |  |  |  |  |  |  |  | 0 | 0 | 0 |  |  |  | 0 | 0 | 0 |  |  |  | 0 | 0 | 0 |  |  |  | 0 | 0 | 0 |  |  |  | 0 | 0 | 0
 |  |  |  |  |  |  |  |  |  | 0 | 0 | 0 |  |  |  | 0 | 0 | 0 |  |  |  | 0 | 0 | 0 |  |  |  | 0 | 0 | 0 |  |  |  | 0 | 0 | 0
 |  |  |  |  |  |  |  |  |  | 0 | 0 | 0 |  |  |  | 0 | 0 | 0 |  |  |  | 0 | 0 | 0 |  |  |  | 0 | 0 | 0 |  |  |  | 0 | 0 | 0
