ciaa/Ponchos/Simon/tools/kicost-0.1.25/tests/StickIt-QuadDAC.xlsx

 |  |  |  |  |  |  | Board Qty: | 100
 |  |  |  |  |  |  | Total Cost: | $0.00 |  |  |  | $0.00 |  |  |  |  |  | $0.00 |  |  |  |  |  | $0.00 |  |  |  |  |  | $0.00
 |  |  |  |  |  |  | Unit Cost: | $0.00
Global Part Info |  |  |  |  |  |  |  |  | Digi-Key |  |  |  |  |  | Mouser |  |  |  |  |  | Newark |  |  |  |  |  | Local
Refs | Value | Desc | Footprint | Manf | Manf# | Qty | Unit$ | Ext$ | Avail | Purch | Unit$ | Ext$ | Cat# | Doc | Avail | Purch | Unit$ | Ext$ | Cat# | Doc | Avail | Purch | Unit$ | Ext$ | Cat# | Doc | Avail | Purch | Unit$ | Ext$ | Cat# | Doc
JP1-JP10 | JUMPER |  | XESS:HDR_1x2 |  |  | 0 | $0.00 | $0.00 |  |  |  |  |  |  |  |  |  |  |  |  |  |  |  |  |  |  | 0 |  | $0.00 | $0.00 | #1EFCF00A
STK1 | STICKIT2_HDR |  | XESS:STICKIT2_HDR |  |  | 0 | $0.00 | $0.00 |  |  |  |  |  |  |  |  |  |  |  |  |  |  |  |  |  |  | 0 |  | $0.00 | $0.00 | #6AD83D72
RN1 | 4K7 |  | XESS:CTS_742C043 |  | 742c043472 | 0 | $0.00 | $0.00 | 24405 |  | $0.00 | $0.00 | 742C043472JPCT-ND | Link (http://www.digikey.com/product-detail/en/cts-resistor-products/742C043472JP/742C043472JPCT-ND/1124577) | 0 |  | $0.00 | $0.00 | 774-742C043472JP | Link (http://www.mouser.com/Search/Refine.aspx?Keyword=742c043472%20)
U2 | MCP48X2 |  | XESS:xess-MICROCHIP-8_MSOP | Microchip | MCP4802-E/MS | 0 | $0.00 | $0.00 | 0 |  | $0.00 | $0.00 | MCP4802-E/MS-ND | Link (http://www.digikey.com/scripts/DkSearch/dksus.dll?WT.z_header=search_go&lang=en) | 402 |  | $0.00 | $0.00 | 579-MCP4802-E/MS | Link (http://www.mouser.com/Search/../ProductDetail/Microchip-Technology/MCP4802-E-MS/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) |  |  |  |  |  | Link (http://www.newark.com/webapp/wcs/stores/servlet/Search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)
VoA2 | COAX_CONN |  | XESS:SMA_EDGE_AMP_132322 | amphenol | 132322 | 0 | $0.00 | $0.00 | 2903 |  | $0.00 | $0.00 | ACX1652-ND | Link (http://www.digikey.com/scripts/DkSearch/dksus.dll?WT.z_header=search_go&lang=en) | 637 |  | $0.00 | $0.00 | 523-132322 | Link (http://www.mouser.com/Search/Refine.aspx?Keyword=132322%20amphenol) | 112 |  | $0.00 | $0.00 | 99H5141 | Link (http://www.newark.com/webapp/wcs/stores/servlet/Search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) | 0 |  | $0.00 | $0.00 | 132322 | Link (http://www.aliexpress.com/item/10pcs-SMA-Female-Jack-Solder-Edge-PCB-Mount-Straight-RF-Connector/32429747943.html)
PM1 | PMOD_SCKT-12 |  | XESS:PMOD_SCKT-12 | Ho Chien | 2553-2x6G | 0 | $0.00 | $0.00 |  |  |  |  |  |  |  |  |  |  |  |  |  |  |  |  |  |  | 0 |  | $0.00 | $0.00 | 2553-2x6G | Link (http:///www.beyondcomponents.com)
C1-C7 | 1.0uF |  | Capacitors_SMD:C_0603_HandSoldering | Yageo | CC0201KRX5R7BB103 | 0 | $0.00 | $0.00 | 73962 |  | $0.00 | $0.00 | 311-1596-1-ND | Link (http://www.digikey.com/product-detail/en/yageo/CC0201KRX5R7BB103/311-1596-1-ND/5195498) | 28840 |  | $0.00 | $0.00 | 603-CC201KRX5R7BB103 | Link (http://www.mouser.com/Search/Refine.aspx?Keyword=CC0201KRX5R7BB103%20Yageo) |  |  |  |  |  | Link (http://www.newark.com/webapp/wcs/stores/servlet/Search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)
U3 | MCP43X1 | digital pot A | XESS:xess-MICROCHIP-20_TSSOP | Microchip | MCP4361-503E/ST | 0 | $0.00 | $0.00 | 955 |  | $0.00 | $0.00 | MCP4361-503E/ST-ND | Link (http://www.digikey.com/scripts/DkSearch/dksus.dll?WT.z_header=search_go&lang=en) |  |  |  |  |  | Link (http://www.mouser.com/Search/../ProductDetail/Microchip-Technology/MCP4361-503E-ST/) | 54 |  | $0.00 | $0.00 | 53R0046 | Link (http://www.newark.com/webapp/wcs/stores/servlet/Search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)
U1 | MCP48X2 | Dual DAC | XESS:xess-MICROCHIP-8_MSOP | Microchip | MCP4802-E/MS | 0 | $0.00 | $0.00 | 0 |  | $0.00 | $0.00 | MCP4802-E/MS-ND | Link (http://www.digikey.com/scripts/DkSearch/dksus.dll?WT.z_header=search_go&lang=en) | 402 |  | $0.00 | $0.00 | 579-MCP4802-E/MS | Link (http://www.mouser.com/Search/../ProductDetail/Microchip-Technology/MCP4802-E-MS/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) |  |  |  |  |  | Link (http://www.newark.com/webapp/wcs/stores/servlet/Search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)
PCB1 | PCB |  |  |  |  | 0 | $0.00 | $0.00 |  |  |  |  |  |  |  |  |  |  |  |  |  |  |  |  |  |  | 0 |  | $0.00 | $0.00 | #619B7DFC
 |  |  |  |  |  |  |  |  |  | 0 | 0 | 0 |  |  |  | 0 | 0 | 0 |  |  |  | 0 | 0 | 0 |  |  |  | 0 | 0 | 0
 |  |  |  |  |  |  |  |  |  | 0 | 0 | 0 |  |  |  | 0 | 0 | 0 |  |  |  | 0 | 0 | 0 |  |  |  | 0 | 0 | 0
 |  |  |  |  |  |  |  |  |  | 0 | 0 | 0 |  |  |  | 0 | 0 | 0 |  |  |  | 0 | 0 | 0 |  |  |  | 0 | 0 | 0
 |  |  |  |  |  |  |  |  |  | 0 | 0 | 0 |  |  |  | 0 | 0 | 0 |  |  |  | 0 | 0 | 0 |  |  |  | 0 | 0 | 0
 |  |  |  |  |  |  |  |  |  | 0 | 0 | 0 |  |  |  | 0 | 0 | 0 |  |  |  | 0 | 0 | 0 |  |  |  | 0 | 0 | 0
 |  |  |  |  |  |  |  |  |  | 0 | 0 | 0 |  |  |  | 0 | 0 | 0 |  |  |  | 0 | 0 | 0 |  |  |  | 0 | 0 | 0
 |  |  |  |  |  |  |  |  |  | 0 | 0 | 0 |  |  |  | 0 | 0 | 0 |  |  |  | 0 | 0 | 0 |  |  |  | 0 | 0 | 0
 |  |  |  |  |  |  |  |  |  | 0 | 0 | 0 |  |  |  | 0 | 0 | 0 |  |  |  | 0 | 0 | 0 |  |  |  | 0 | 0 | 0
 |  |  |  |  |  |  |  |  |  | 0 | 0 | 0 |  |  |  | 0 | 0 | 0 |  |  |  | 0 | 0 | 0 |  |  |  | 0 | 0 | 0
 |  |  |  |  |  |  |  |  |  | 0 | 0 | 0 |  |  |  | 0 | 0 | 0 |  |  |  | 0 | 0 | 0 |  |  |  | 0 | 0 | 0
