ciaa/Ponchos/Simon/tools/kicost-0.1.25/tests/test.xlsx

 |  |  |  |  |  |  | Board Qty: | 100
 |  |  |  |  |  |  | Total Cost: | $0.00 |  |  |  | $0.00 |  |  |  |  |  | $0.00 |  |  |  |  |  | $0.00 |  |  |  |  |  | $0.00 |  |  |  |  |  | $0.00
 |  |  |  |  |  |  | Unit Cost: | $0.00
Global Part Info |  |  |  |  |  |  |  |  | Digi-Key |  |  |  |  |  | Mouser |  |  |  |  |  | Newark |  |  |  |  |  | Local |  |  |  |  |  | Mine
Refs | Value | Desc | Footprint | Manf | Manf# | Qty | Unit$ | Ext$ | Avail | Purch | Unit$ | Ext$ | Cat# | Doc | Avail | Purch | Unit$ | Ext$ | Cat# | Doc | Avail | Purch | Unit$ | Ext$ | Cat# | Doc | Avail | Purch | Unit$ | Ext$ | Cat# | Doc | Avail | Purch | Unit$ | Ext$ | Cat# | Doc
SW1 | SW_PUSH |  | XESS:RS-282G05A3-SM_RT |  | RS-282G05A3-SM RT | 0 | $0.00 | $0.00 | 14379 |  | $0.00 | $0.00 | CKN10384CT-ND | Link (http://www.digikey.com/product-detail/en/c-k-components/RS-282G05A3-SM%20RT/CKN10384CT-ND/2747203) | 15967 |  | $0.00 | $0.00 | 611-RS-282G05A3-SMRT | Link (http://www.mouser.com/Search/../ProductDetail/CK-Components/RS-282G05A3-SM-RT/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) |  |  |  |  |  |  | 0 |  | $0.00 | $0.00 | RS-282G05A3-SM RT | Link (http://www.xess.com)
Q7 | Crystal |  | XESS:PMOD_SCKT-12 | Keystone Electronics | 5010 | 0 | $0.00 | $0.00 | 113759 |  | $0.00 | $0.00 | 36-5010-ND | Link (http://www.digikey.com/scripts/DkSearch/dksus.dll?WT.z_header=search_go&lang=en) | 4980 |  | $0.00 | $0.00 | 534-5010 | Link (http://www.mouser.com/Search/Refine.aspx?Keyword=5010%20Keystone%20Electronics)
RN1 | 3.9K |  | XESS:CTS_742C043 |  | 742C083392JP | 0 | $0.00 | $0.00 | 31821 |  | $0.00 | $0.00 | 742C083392JPCT-ND | Link (http://www.digikey.com/product-detail/en/cts-resistor-products/742C083392JP/742C083392JPCT-ND/1124537) | 16731 |  | $0.00 | $0.00 | 774-742C083392JP | Link (http://www.mouser.com/Search/Refine.aspx?Keyword=742C083392JP%20)
TP1,JP4-JP10 | JUMPER |  | XESS:HDR_1x2 |  |  | 0 | $0.00 | $0.00
PM2,PM3 | PMOD_SCKT-12 |  | XESS:PMOD_SCKT-12 |  |  | 0 | $0.00 | $0.00
GPIO1 | RPi_GPIO |  | RPi_Hat:Pin_Header_Straight_2x20 |  |  | 0 | $0.00 | $0.00 |  |  |  |  |  |  |  |  |  |  |  |  |  |  |  |  |  |  |  |  |  |  |  |  | 0 |  | $0.00 | $0.00 | MMM001
J3-J5 | JSHORTNORMAL |  | XESS:xess-JSHORT |  |  | 0 | $0.00 | $0.00
JP1-JP3 | JUMPER3 |  | XESS:HDR_1x3 |  |  | 0 | $0.00 | $0.00 |  |  |  |  |  |  |  |  |  |  |  |  |  |  |  |  |  |  | 0 |  | $0.00 | $0.00 | #7CC3F5E2 | Link (http://www.xess.com)
C5 | 0.1uF |  | Resistors_SMD:R_0805_HandSoldering |  | 08055C104KAT2A | 0 | $0.00 | $0.00 | 9009901 |  | $0.00 | $0.00 | 478-1395-1-ND | Link (http://www.digikey.com/product-detail/en/avx-corporation/08055C104KAT2A/478-1395-1-ND/564427) | 2230652 |  | $0.00 | $0.00 | 581-08055C104K | Link (http://www.mouser.com/Search/Refine.aspx?Keyword=08055C104KAT2A%20)
GR1-GR3 | Grove |  | XESS:GROVE_MALE |  |  | 0 | $0.00 | $0.00
U1 | NCV1117 |  | XESS:SOT-223 |  | NCP1117ST33T3G | 0 | $0.00 | $0.00 | 18260 |  | $0.00 | $0.00 | NCP1117ST33T3GOSCT-ND | Link (http://www.digikey.com/product-detail/en/on-semiconductor/NCP1117ST33T3G/NCP1117ST33T3GOSCT-ND/660708) | 0 |  | $0.00 | $0.00 | 863-NCP1117ST33T3G | Link (http://www.mouser.com/Search/Refine.aspx?Keyword=NCP1117ST33T3G%20) | 798 |  | $0.00 | $0.00 | 67H7013 | Link (http://www.newark.com/on-semiconductor/ncp1117st33t3g/ldo-voltage-regulator-3-3v-1a/dp/67H7013)
U2 | CAT24C32 |  | SMD_Packages:SOIC-8-N |  | CAT24C32WI-GT3 | 0 | $0.00 | $0.00 | 15729 |  | $0.00 | $0.00 | CAT24C32WI-GT3CT-ND | Link (http://www.digikey.com/product-detail/en/on-semiconductor/CAT24C32WI-GT3/CAT24C32WI-GT3CT-ND/1631159) | 3629 |  | $0.00 | $0.00 | 698-CAT24C32WI-GT3 | Link (http://www.mouser.com/Search/../ProductDetail/ON-Semiconductor/CAT24C32WI-GT3/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) | 5222 |  | $0.00 | $0.00 | 08R5414 | Link (http://www.newark.com/on-semiconductor/cat24c32wi-gt3/serial-eeprom-32kbit-400khz-soic/dp/08R5414)
R1 | 1K |  | Resistors_SMD:R_0805_HandSoldering |  | RC0603FR-0743K2L | 0 | $0.00 | $0.00 | 72607 |  | $0.00 | $0.00 | 311-43.2KHRCT-ND | Link (http://www.digikey.com/product-detail/en/yageo/RC0603FR-0743K2L/311-43.2KHRCT-ND/730182) | 53152 |  | $0.00 | $0.00 | 603-RC0603FR-0743K2L | Link (http://www.mouser.com/Search/Refine.aspx?Keyword=RC0603FR-0743K2L%20) |  |  |  |  |  | Link (http://www.newark.com/webapp/wcs/stores/servlet/Search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)
J1 | XuLA_IO_HDR |  | XESS:XuLA_IO_Hdr |  |  | 0 | $0.00 | $0.00
C2,C4 | 4.7uF |  | Resistors_SMD:R_0805_HandSoldering |  | LMK212BJ475KD-T | 0 | $0.00 | $0.00 | 53834 |  | $0.00 | $0.00 | 587-1297-1-ND | Link (http://www.digikey.com/product-detail/en/taiyo-yuden/LMK212BJ475KD-T/587-1297-1-ND/931074) | 13894 |  | $0.00 | $0.00 | 963-LMK212BJ475KD-T | Link (http://www.mouser.com/Search/Refine.aspx?Keyword=LMK212BJ475KD-T%20) | 747 |  | $0.00 | $0.00 | 18J2726 | Link (http://www.newark.com/taiyo-yuden/lmk212bj475kd-t/ceramic-capacitor-4-7uf-10v-x5r/dp/18J2726)
CON1 | BARREL_JACK |  | Connect:BARREL_JACK |  | PJ-002A | 0 | $0.00 | $0.00 | 71877 |  | $0.00 | $0.00 | CP-002A-ND | Link (http://www.digikey.com/product-detail/en/cui-inc/PJ-002A/CP-002A-ND/96962) | 10241 |  | $0.00 | $0.00 | 490-PJ-002A | Link (http://www.mouser.com/Search/../ProductDetail/CUI/PJ-002A/) | 0 |  | $0.00 | $0.00 | 41Y7845 | Link (http://www.newark.com/webapp/wcs/stores/servlet/Search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)
C1,C3 | 22uF |  | Capacitors_SMD:c_elec_5x5.3 |  | UWX1C220MCL1GB | 0 | $0.00 | $0.00 | 7032 |  | $0.00 | $0.00 | 493-2101-1-ND | Link (http://www.digikey.com/product-detail/en/nichicon/UWX1C220MCL1GB/493-2101-1-ND/590076) | 14735 |  | $0.00 | $0.00 | 647-UWX1C220MCL1 | Link (http://www.mouser.com/Search/Refine.aspx?Keyword=UWX1C220MCL1GB%20) | 1302 |  | $0.00 | $0.00 | 58R3621 | Link (http://www.newark.com/nichicon/uwx1c220mcl1gb/aluminum-electrolytic-capacitor/dp/58R3621)
 |  |  |  |  |  |  |  |  |  | 0 | 0 | 0 |  |  |  | 0 | 0 | 0 |  |  |  | 0 | 0 | 0 |  |  |  | 0 | 0 | 0 |  |  |  | 0 | 0 | 0
 |  |  |  |  |  |  |  |  |  | 0 | 0 | 0 |  |  |  | 0 | 0 | 0 |  |  |  | 0 | 0 | 0 |  |  |  | 0 | 0 | 0 |  |  |  | 0 | 0 | 0
 |  |  |  |  |  |  |  |  |  | 0 | 0 | 0 |  |  |  | 0 | 0 | 0 |  |  |  | 0 | 0 | 0 |  |  |  | 0 | 0 | 0 |  |  |  | 0 | 0 | 0
 |  |  |  |  |  |  |  |  |  | 0 | 0 | 0 |  |  |  | 0 | 0 | 0 |  |  |  | 0 | 0 | 0 |  |  |  | 0 | 0 | 0 |  |  |  | 0 | 0 | 0
 |  |  |  |  |  |  |  |  |  | 0 | 0 | 0 |  |  |  | 0 | 0 | 0 |  |  |  | 0 | 0 | 0 |  |  |  | 0 | 0 | 0 |  |  |  | 0 | 0 | 0
 |  |  |  |  |  |  |  |  |  | 0 | 0 | 0 |  |  |  | 0 | 0 | 0 |  |  |  | 0 | 0 | 0 |  |  |  | 0 | 0 | 0 |  |  |  | 0 | 0 | 0
 |  |  |  |  |  |  |  |  |  | 0 | 0 | 0 |  |  |  | 0 | 0 | 0 |  |  |  | 0 | 0 | 0 |  |  |  | 0 | 0 | 0 |  |  |  | 0 | 0 | 0
 |  |  |  |  |  |  |  |  |  | 0 | 0 | 0 |  |  |  | 0 | 0 | 0 |  |  |  | 0 | 0 | 0 |  |  |  | 0 | 0 | 0 |  |  |  | 0 | 0 | 0
 |  |  |  |  |  |  |  |  |  | 0 | 0 | 0 |  |  |  | 0 | 0 | 0 |  |  |  | 0 | 0 | 0 |  |  |  | 0 | 0 | 0 |  |  |  | 0 | 0 | 0
 |  |  |  |  |  |  |  |  |  | 0 | 0 | 0 |  |  |  | 0 | 0 | 0 |  |  |  | 0 | 0 | 0 |  |  |  | 0 | 0 | 0 |  |  |  | 0 | 0 | 0
 |  |  |  |  |  |  |  |  |  | 0 | 0 | 0 |  |  |  | 0 | 0 | 0 |  |  |  | 0 | 0 | 0 |  |  |  | 0 | 0 | 0 |  |  |  | 0 | 0 | 0
 |  |  |  |  |  |  |  |  |  | 0 | 0 | 0 |  |  |  | 0 | 0 | 0 |  |  |  | 0 | 0 | 0 |  |  |  | 0 | 0 | 0 |  |  |  | 0 | 0 | 0
 |  |  |  |  |  |  |  |  |  | 0 | 0 | 0 |  |  |  | 0 | 0 | 0 |  |  |  | 0 | 0 | 0 |  |  |  | 0 | 0 | 0 |  |  |  | 0 | 0 | 0
 |  |  |  |  |  |  |  |  |  | 0 | 0 | 0 |  |  |  | 0 | 0 | 0 |  |  |  | 0 | 0 | 0 |  |  |  | 0 | 0 | 0 |  |  |  | 0 | 0 | 0
 |  |  |  |  |  |  |  |  |  | 0 | 0 | 0 |  |  |  | 0 | 0 | 0 |  |  |  | 0 | 0 | 0 |  |  |  | 0 | 0 | 0 |  |  |  | 0 | 0 | 0
 |  |  |  |  |  |  |  |  |  | 0 | 0 | 0 |  |  |  | 0 | 0 | 0 |  |  |  | 0 | 0 | 0 |  |  |  | 0 | 0 | 0 |  |  |  | 0 | 0 | 0
 |  |  |  |  |  |  |  |  |  | 0 | 0 | 0 |  |  |  | 0 | 0 | 0 |  |  |  | 0 | 0 | 0 |  |  |  | 0 | 0 | 0 |  |  |  | 0 | 0 | 0
