ciaa/Ponchos/ethernet_LAN8720A_v2/ethernet_LAN8720A_v2.xlsx

 |  |  |  |  |  |  | Board Qty: | 100
 |  |  |  |  |  |  | Total Cost: | $0.00 |  |  |  | $0.00 |  |  |  |  |  | $0.00 |  |  |  |  |  | $0.00 |  |  |  |  |  | $0.00 |  |  |  |  |  | $0.00
 |  |  |  |  |  |  | Unit Cost: | $0.00
Global Part Info |  |  |  |  |  |  |  |  | Digi-Key |  |  |  |  |  | Farnell |  |  |  |  |  | Mouser |  |  |  |  |  | Newark |  |  |  |  |  | Rs Components
Refs | Value | Desc | Footprint | Manf | Manf# | Qty | Unit$ | Ext$ | Avail | Purch | Unit$ | Ext$ | Cat# | Doc | Avail | Purch | Unit$ | Ext$ | Cat# | Doc | Avail | Purch | Unit$ | Ext$ | Cat# | Doc | Avail | Purch | Unit$ | Ext$ | Cat# | Doc | Avail | Purch | Unit$ | Ext$ | Cat# | Doc
U2 | 50MHZ | 50MHz HCMOS XO Standard Oscillator SMD 3.3V 30mA En/Dis | eth:Oscillator_7.0x5.0mm | Abracon LLC | ASV-50.000MHZ-E-T | 0 | $0.00 | $0.00 |  |  | $0.00 | $0.00 | 535-10087-1-ND | Link (http://www.digikey.com/scripts/DkSearch/dksus.dll?WT.z_header=search_go&lang=en) |  |  |  |  |  |  |  |  | $0.00 | $0.00 | 815-ASV-50.000M-E-T | Link (http://www.mouser.com/Search/Refine.aspx?Keyword=ASV-50.000MHZ-E-T%20) |  |  | $0.00 | $0.00 | 25R1720 | Link (http://www.newark.com/webapp/wcs/stores/servlet/Search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)
C2,C3,C6 | 10nF | CAP CER 10000PF 50V 10% X7R 0603 | eth:c_0603v2 | Kemet | C0603C103K5RACTU | 0 | $0.00 | $0.00 | 3398790 |  | $0.00 | $0.00 | 399-1091-1-ND | Link (http://www.digikey.com/scripts/DkSearch/dksus.dll?WT.z_header=search_go&lang=en) |  |  | $0.00 | $0.00 | 1414609 | Link (http://it.farnell.com/kemet/c0603c103k5ractu/condensatore-mlcc-x7r-10nf-50v/dp/1414609) | 735633 |  | $0.00 | $0.00 | 80-C0603C103K5R | Link (http://www.mouser.com/Search/../ProductDetail/KEMET/C0603C103K5RACTU/) |  |  | $0.00 | $0.00 | 30C5334 | Link (http://www.newark.com/kemet/c0603c103k5ractu/ceramic-capacitor-0-01uf-50v-x7r/dp/30C5334) | 2275 |  | $0.00 | $0.00 | 264-4595 | Link (http://it.rs-online.com/web/c/?searchTerm=C0603C103K5RACTU%20)
P1 | SI-52003-F | RJ45 Magjack Connector TH 10/100 Base-T, AutoMDIX, PoE | eth:RJ45_SI-52003-F_PoE_ETH | Stewart Connector | SI-52003-F | 0 | $0.00 | $0.00 | 12493 |  | $0.00 | $0.00 | 380-1119-ND | Link (http://www.digikey.com/scripts/DkSearch/dksus.dll?WT.z_header=search_go&lang=en) |  |  | $0.00 | $0.00 | 2676004 | Link (http://it.farnell.com/webapp/wcs/stores/servlet/Search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) |  |  | $0.00 | $0.00 | 530-SI-52003-F | Link (http://www.mouser.com/Search/Refine.aspx?Keyword=SI-52003-F%20Stewart%20Connector) |  |  | $0.00 | $0.00 | 03AC3548 | Link (http://www.newark.com/webapp/wcs/stores/servlet/Search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) |  |  | $0.00 | $0.00 | 741-8587 | Link (http://it.rs-online.com/web/c/?searchTerm=SI-52003-F%20)
L1 | FBEAD 22 | FERRITE BEAD 22 OHM 0603 1LN | eth:SM0603 | Taiyo Yuden | BK1608HS220-T | 0 | $0.00 | $0.00 | 37301 |  | $0.00 | $0.00 | 587-1869-1-ND | Link (http://www.digikey.com/scripts/DkSearch/dksus.dll?WT.z_header=search_go&lang=en) |  |  |  |  |  |  |  |  |  |  |  |  |  |  | $0.00 | $0.00 | 86H5390 | Link (http://www.newark.com/taiyo-yuden/bk1608hs220-t/ferrite-bead-0-05ohm-1-5a-0603/dp/86H5390)
U1 | LAN8720A-CP | 4/4 Transceiver Full RMII 24-QFN (4x4) | eth:QFN24 | Microchip Technology | LAN8720A-CP-TR | 0 | $0.00 | $0.00 | 26420 |  | $0.00 | $0.00 | LAN8720A-CP-CT-ND | Link (http://www.digikey.com/product-detail/en/microchip-technology/LAN8720A-CP-TR/LAN8720A-CP-CT-ND/4307900) |  |  | $0.00 | $0.00 | 2810132 | Link (http://it.farnell.com/webapp/wcs/stores/servlet/Search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) |  |  |  |  |  |  |  |  | $0.00 | $0.00 | 69W9463 | Link (http://www.newark.com/microchip/lan8720a-cp-tr/24-vqfn-4x4x0-9mm-t-r-small-footprint/dp/69W9463)
XA1 | Conn_Poncho2P_2x_20x2 | 40P Header BTB Conn Gold 50mils 1.27mmTHole | eth:Conn_Poncho_Izquierdo | Harwin | M50-3502042 | 0 | $0.00 | $0.00 | 969 |  | $0.00 | $0.00 | 952-1387-ND | Link (http://www.digikey.com/scripts/DkSearch/dksus.dll?WT.z_header=search_go&lang=en) |  |  | $0.00 | $0.00 | 1022307 | Link (http://it.farnell.com/webapp/wcs/stores/servlet/Search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) | 732 |  | $0.00 | $0.00 | 855-M50-3502042 | Link (http://www.mouser.com/Search/Refine.aspx?Keyword=M50-3502042%20) |  |  | $0.00 | $0.00 | 03M4128 | Link (http://www.newark.com/webapp/wcs/stores/servlet/Search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) | 24 |  | $0.00 | $0.00 | 681-1196 | Link (http://it.rs-online.com/web/c/?searchTerm=M50-3502042%20)
R10-R12 | 22 | RES 22 OHM 1/10W 5% | eth:SM0603_Resistor | Yageo | RC0603JR-0722RL | 0 | $0.00 | $0.00 | 599658 |  | $0.00 | $0.00 | 311-22GRCT-ND | Link (http://www.digikey.com/scripts/DkSearch/dksus.dll?WT.z_header=search_go&lang=en) |  |  | $0.00 | $0.00 | 9233172 | Link (http://it.farnell.com/yageo-phycomp/rc0603jr-0722rl/res-film-spesso-22r-5-0-1w-0603/dp/9233172) | 108144 |  | $0.00 | $0.00 | 603-RC0603JR-0722RL | Link (http://www.mouser.com/Search/Refine.aspx?Keyword=RC0603JR-0722RL%20Yageo) |  |  | $0.00 | $0.00 | 68R0168 | Link (http://www.newark.com/yageo/rc0603jr-0722rl/res-thick-film-22r-5-0-1w-0603/dp/68R0168)
MH1,MH2 | MOUNTING-HOLE |  | eth:MountingHole_2.2mm_M2_Pad |  |  | 0 | $0.00 | $0.00
C4,C9,C10,C15 | 100nF | CAP CER 0,1UF 16V 10% X7R 0603 | eth:c_0603v2 | Kemet | C0603C104K4RACTU | 0 | $0.00 | $0.00 | 2752330 |  | $0.00 | $0.00 | 399-1096-1-ND | Link (http://www.digikey.com/scripts/DkSearch/dksus.dll?WT.z_header=search_go&lang=en) |  |  | $0.00 | $0.00 | 1414610 | Link (http://it.farnell.com/kemet/c0603c104k4ractu/condensatore-mlcc-x7r-100nf-16v/dp/1414610) | 343362 |  | $0.00 | $0.00 | 80-C0603C104K4R | Link (http://www.mouser.com/Search/../ProductDetail/KEMET/C0603C104K4RACTU/) |  |  | $0.00 | $0.00 | 77R3551 | Link (http://www.newark.com/kemet/c0603c104k4ractu/ceramic-capacitor-0-1uf-16v-x7r/dp/77R3551) | 2100 |  | $0.00 | $0.00 | 264-4630 | Link (http://it.rs-online.com/web/c/?searchTerm=C0603C104K4RACTU%20)
C8 | 1uF | CAP CER 1UF 16V 10% X7R 0603 | eth:c_0603v2 | Kemet | C0603C105K4RACTU | 0 | $0.00 | $0.00 | 366947 |  | $0.00 | $0.00 | 399-7847-1-ND | Link (http://www.digikey.com/scripts/DkSearch/dksus.dll?WT.z_header=search_go&lang=en) |  |  | $0.00 | $0.00 | 1650837 | Link (http://it.farnell.com/kemet/c0603c105k4ractu/condensatore-mlcc-x7r-1uf-16v/dp/1650837) | 86052 |  | $0.00 | $0.00 | 80-C0603C105K4R | Link (http://www.mouser.com/Search/../ProductDetail/KEMET/C0603C105K4RACTU/) |  |  | $0.00 | $0.00 | 93K5997 | Link (http://www.newark.com/kemet/c0603c105k4ractu/ceramic-capacitor-1uf-16v-x7r/dp/93K5997) | 1500 |  | $0.00 | $0.00 | 801-5221 | Link (http://it.rs-online.com/web/p/condensatori-ceramici-multistrato/8015221/)
R3-R6 | 49,9 1% | RES 49,9 OHM 1/10W 1% 0603 SMD | eth:SM0603_Resistor | Yageo | RC0603FR-0749R9L | 0 | $0.00 | $0.00 | 4202054 |  | $0.00 | $0.00 | 311-49.9HRCT-ND | Link (http://www.digikey.com/scripts/DkSearch/dksus.dll?WT.z_header=search_go&lang=en) |  |  | $0.00 | $0.00 | 2363480 | Link (http://it.farnell.com/yageo/rc0603fr-0749r9l/res-thick-film-49r9-1-0-1w-0603/dp/2363480) | 85390 |  | $0.00 | $0.00 | 603-RC0603FR-0749R9L | Link (http://www.mouser.com/Search/Refine.aspx?Keyword=RC0603FR-0749R9L%20Yageo) |  |  | $0.00 | $0.00 | 68R0100 | Link (http://www.newark.com/yageo/rc0603fr-0749r9l/res-thick-film-49r9-1-0-1w-0603/dp/68R0100)
R7-R9,R13,R14,R24 | 0 | RES SMD 0.0OHM JUMPER 1/10W 0603 | eth:SM0603_Resistor | Bourns | CR0603-J/-000ELF | 0 | $0.00 | $0.00 | 131374 |  | $0.00 | $0.00 | CR0603-J/-000ELFCT-ND | Link (http://www.digikey.com/scripts/DkSearch/dksus.dll?WT.z_header=search_go&lang=en) |  |  | $0.00 | $0.00 | 2008343 | Link (http://it.farnell.com/bourns/cr0603-j-000elf/res-film-spesso-0r-5-0-1w-0603/dp/2008343) |  |  |  |  |  |  |  |  | $0.00 | $0.00 | 02J2264 | Link (http://www.newark.com/bourns/cr0603-j-000elf/res-thick-film-0r-5-0-1w-0603/dp/02J2264) | 5600 |  | $0.00 | $0.00 | 740-8870 | Link (http://it.rs-online.com/web/c/?searchTerm=CR0603-J%2F-000ELF%20)
R17,R18 | 270 | RES 270 OHM 1/10W 5% 0603 SMD | eth:SM0603_Resistor | Yageo | RC0603JR-07270RL | 0 | $0.00 | $0.00 | 528717 |  | $0.00 | $0.00 | 311-270GRCT-ND | Link (http://www.digikey.com/scripts/DkSearch/dksus.dll?WT.z_header=search_go&lang=en) |  |  | $0.00 | $0.00 | 9233300 | Link (http://it.farnell.com/yageo-phycomp/rc0603jr-07270rl/res-film-spesso-270r-5-0-1w-0603/dp/9233300) | 111020 |  | $0.00 | $0.00 | 603-RC0603JR-07270RL | Link (http://www.mouser.com/Search/../ProductDetail/Yageo/RC0603JR-07270RL/) |  |  | $0.00 | $0.00 | 68R0174 | Link (http://www.newark.com/yageo/rc0603jr-07270rl/res-thick-film-270r-5-0-1w-0603/dp/68R0174)
R2,R15,R16 | 10k | RES 10K OHM 1/10W 5% 0603 SMD | eth:SM0603_Resistor | Yageo | RC0603JR-0710KL | 0 | $0.00 | $0.00 | 13034890 |  | $0.00 | $0.00 | 311-10KGRCT-ND | Link (http://www.digikey.com/scripts/DkSearch/dksus.dll?WT.z_header=search_go&lang=en) |  |  | $0.00 | $0.00 | 9233504 | Link (http://it.farnell.com/yageo-phycomp/rc0603jr-0710kl/res-film-spesso-10k-5-0-1w-0603/dp/9233504) | 252455 |  | $0.00 | $0.00 | 603-RC0603JR-0710KL | Link (http://www.mouser.com/Search/Refine.aspx?Keyword=RC0603JR-0710KL%20Yageo) |  |  | $0.00 | $0.00 | 68R0144 | Link (http://www.newark.com/yageo/rc0603jr-0710kl/res-thick-film-10k-5-0-1w-0603/dp/68R0144)
FID1-FID3 | FIDUCIAL |  | eth:Fiducial_1mm_Dia_2.54mm_Outer_CopperTop |  |  | 0 | $0.00 | $0.00
C7 | 470pF | CAP CER 470PF 50V 10% X7R 0603 | eth:c_0603v2 | Kemet | C0603C471K5RACTU | 0 | $0.00 | $0.00 | 110147 |  | $0.00 | $0.00 | 399-1075-1-ND | Link (http://www.digikey.com/scripts/DkSearch/dksus.dll?WT.z_header=search_go&lang=en) |  |  | $0.00 | $0.00 | 1650849 | Link (http://it.farnell.com/kemet/c0603c471k5ractu/condensatore-mlcc-x7r-470pf-50v/dp/1650849) |  |  |  |  |  |  |  |  | $0.00 | $0.00 | 30C5318 | Link (http://www.newark.com/kemet/c0603c471k5ractu/ceramic-capacitor-470pf-50v-x7r/dp/30C5318) |  |  |  |  | 298-9343 | Link (http://it.rs-online.com/web/p/condensatori-ceramici-multistrato/2989343P/)
C11-C14 | 18pF | CAP CER 18PF 50V 5% NP0 0603 | eth:c_0603v2 | Kemet | C0603C180J5GACTU | 0 | $0.00 | $0.00 | 167595 |  | $0.00 | $0.00 | 399-1052-1-ND | Link (http://www.digikey.com/scripts/DkSearch/dksus.dll?WT.z_header=search_go&lang=en) |  |  | $0.00 | $0.00 | 1414620 | Link (http://it.farnell.com/kemet/c0603c180j5gactu/condens-mlcc-c0g-np0-18pf-50v/dp/1414620) | 109301 |  | $0.00 | $0.00 | 80-C0603C180J5G | Link (http://www.mouser.com/Search/../ProductDetail/KEMET/C0603C180J5GACTU/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) |  |  | $0.00 | $0.00 | 64K2845 | Link (http://www.newark.com/kemet/c0603c180j5gactu/ceramic-capacitor-18pf-50v-c0g/dp/64K2845) | 4800 |  | $0.00 | $0.00 | 147-415 | Link (http://it.rs-online.com/web/p/condensatori-ceramici-multistrato/0147415/)
R20,R22,R23 | 33 | RES 33 OHM 1/10W 5% 0603 SMD | eth:SM0603_Resistor | Bourns | CR0603-JW-330GLF | 0 | $0.00 | $0.00 | 43730 |  | $0.00 | $0.00 | CR0603-JW-330GLFCT-ND | Link (http://www.digikey.com/scripts/DkSearch/dksus.dll?WT.z_header=search_go&lang=en) |  |  | $0.00 | $0.00 | 2008346 | Link (http://it.farnell.com/bourns/cr0603-jw-330glf/res-film-spesso-33r-5-0-1w-0603/dp/2008346) | 22309 |  | $0.00 | $0.00 | 652-CR0603-JW-330GLF | Link (http://www.mouser.com/Search/Refine.aspx?Keyword=CR0603-JW-330GLF%20) |  |  | $0.00 | $0.00 | 65T8182 | Link (http://www.newark.com/bourns/cr0603-jw-330glf/res-thick-film-33r-5-0-1w-0603/dp/65T8182) |  |  |  |  | 740-8937 | Link (http://it.rs-online.com/web/p/resistori-smd/7408937/)
P3 | PoE | 8 Pin Header Conn Gold 50 mils 1.27mm THole | eth:PIN_ARRAY_4X2 |  |  | 0 | $0.00 | $0.00
JP1 | JUMPER3 |  | Oddities:NetTie-II_SMD |  |  | 0 | $0.00 | $0.00
R21,R25 | 100k | RES SMD 100K OHM 5% 1/10W 0603 | eth:SM0603_Resistor | Bourns | CR0603-JW-104ELF | 0 | $0.00 | $0.00 | 45257 |  | $0.00 | $0.00 | CR0603-JW-104ELFCT-ND | Link (http://www.digikey.com/scripts/DkSearch/dksus.dll?WT.z_header=search_go&lang=en) |  |  | $0.00 | $0.00 | 2333579 | Link (http://it.farnell.com/bourns/cr0603-jw-104elf/res-film-spesso-100k-5-0-1w-0603/dp/2333579) |  |  |  |  |  |  |  |  | $0.00 | $0.00 | 02J2288 | Link (http://www.newark.com/bourns/cr0603-jw-104elf/res-thick-film-100k-5-0-1w-0603/dp/02J2288) |  |  | $0.00 | $0.00 | 905-2779 | Link (http://it.rs-online.com/web/c/?searchTerm=CR0603-JW-104ELF%20)
C1,C5,C16 | 10uF | CAP TANT 10UF 6.3V 10% 1206 | eth:c_1206_tantalio_2 | Kemet | T491A106K006AT7280 | 0 | $0.00 | $0.00 |  |  |  |  |  |  |  |  |  |  |  |  | 15173 |  | $0.00 | $0.00 | 80-T491A106K0067280 | Link (http://www.mouser.com/Search/Refine.aspx?Keyword=T491A106K006AT7280%20) |  |  | $0.00 | $0.00 | 95W5212 | Link (http://www.newark.com/webapp/wcs/stores/servlet/Search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)
R1 | 1k5 | RES 1.5K OHM 1/10W 5% 0603 SMD | eth:SM0603_Resistor | Yageo | RC0603JR-071K5L | 0 | $0.00 | $0.00 | 573516 |  | $0.00 | $0.00 | 311-1.5KGRCT-ND | Link (http://www.digikey.com/scripts/DkSearch/dksus.dll?WT.z_header=search_go&lang=en) |  |  | $0.00 | $0.00 | 9233407 | Link (http://it.farnell.com/yageo-phycomp/rc0603jr-071k5l/res-film-spesso-1k5-5-0-1w-0603/dp/9233407) | 144396 |  | $0.00 | $0.00 | 603-RC0603JR-071K5L | Link (http://www.mouser.com/Search/Refine.aspx?Keyword=RC0603JR-071K5L%20Yageo) |  |  | $0.00 | $0.00 | 68R0139 | Link (http://www.newark.com/yageo/rc0603jr-071k5l/res-thick-film-1k5-5-0-1w-0603/dp/68R0139)
R19 | 12.1k 1% | RES SMD 12.1K OHM 1% 1/10W 0603 | eth:SM0603_Resistor | Yageo | RC0603FR-0712K1L | 0 | $0.00 | $0.00 | 535818 |  | $0.00 | $0.00 | 311-12.1KHRCT-ND | Link (http://www.digikey.com/scripts/DkSearch/dksus.dll?WT.z_header=search_go&lang=en) |  |  | $0.00 | $0.00 | 2413673 | Link (http://it.farnell.com/yageo/rc0603fr-0712k1l/res-thick-film-12k1-1-0-1w-0603/dp/2413673) | 115304 |  | $0.00 | $0.00 | 603-RC0603FR-0712K1L | Link (http://www.mouser.com/Search/Refine.aspx?Keyword=RC0603FR-0712K1L%20Yageo) |  |  | $0.00 | $0.00 | 68R0055 | Link (http://www.newark.com/yageo/rc0603fr-0712k1l/res-thick-film-12k1-1-0-1w-0603/dp/68R0055)
 |  |  |  |  |  |  |  |  |  | 0 | 0 | 0 |  |  |  | 0 | 0 | 0 |  |  |  | 0 | 0 | 0 |  |  |  | 0 | 0 | 0 |  |  |  | 0 | 0 | 0
 |  |  |  |  |  |  |  |  |  | 0 | 0 | 0 |  |  |  | 0 | 0 | 0 |  |  |  | 0 | 0 | 0 |  |  |  | 0 | 0 | 0 |  |  |  | 0 | 0 | 0
 |  |  |  |  |  |  |  |  |  | 0 | 0 | 0 |  |  |  | 0 | 0 | 0 |  |  |  | 0 | 0 | 0 |  |  |  | 0 | 0 | 0 |  |  |  | 0 | 0 | 0
 |  |  |  |  |  |  |  |  |  | 0 | 0 | 0 |  |  |  | 0 | 0 | 0 |  |  |  | 0 | 0 | 0 |  |  |  | 0 | 0 | 0 |  |  |  | 0 | 0 | 0
 |  |  |  |  |  |  |  |  |  | 0 | 0 | 0 |  |  |  | 0 | 0 | 0 |  |  |  | 0 | 0 | 0 |  |  |  | 0 | 0 | 0 |  |  |  | 0 | 0 | 0
 |  |  |  |  |  |  |  |  |  | 0 | 0 | 0 |  |  |  | 0 | 0 | 0 |  |  |  | 0 | 0 | 0 |  |  |  | 0 | 0 | 0 |  |  |  | 0 | 0 | 0
 |  |  |  |  |  |  |  |  |  | 0 | 0 | 0 |  |  |  | 0 | 0 | 0 |  |  |  | 0 | 0 | 0 |  |  |  | 0 | 0 | 0 |  |  |  | 0 | 0 | 0
 |  |  |  |  |  |  |  |  |  | 0 | 0 | 0 |  |  |  | 0 | 0 | 0 |  |  |  | 0 | 0 | 0 |  |  |  | 0 | 0 | 0 |  |  |  | 0 | 0 | 0
 |  |  |  |  |  |  |  |  |  | 0 | 0 | 0 |  |  |  | 0 | 0 | 0 |  |  |  | 0 | 0 | 0 |  |  |  | 0 | 0 | 0 |  |  |  | 0 | 0 | 0
 |  |  |  |  |  |  |  |  |  | 0 | 0 | 0 |  |  |  | 0 | 0 | 0 |  |  |  | 0 | 0 | 0 |  |  |  | 0 | 0 | 0 |  |  |  | 0 | 0 | 0
 |  |  |  |  |  |  |  |  |  | 0 | 0 | 0 |  |  |  | 0 | 0 | 0 |  |  |  | 0 | 0 | 0 |  |  |  | 0 | 0 | 0 |  |  |  | 0 | 0 | 0
 |  |  |  |  |  |  |  |  |  | 0 | 0 | 0 |  |  |  | 0 | 0 | 0 |  |  |  | 0 | 0 | 0 |  |  |  | 0 | 0 | 0 |  |  |  | 0 | 0 | 0
 |  |  |  |  |  |  |  |  |  | 0 | 0 | 0 |  |  |  | 0 | 0 | 0 |  |  |  | 0 | 0 | 0 |  |  |  | 0 | 0 | 0 |  |  |  | 0 | 0 | 0
 |  |  |  |  |  |  |  |  |  | 0 | 0 | 0 |  |  |  | 0 | 0 | 0 |  |  |  | 0 | 0 | 0 |  |  |  | 0 | 0 | 0 |  |  |  | 0 | 0 | 0
 |  |  |  |  |  |  |  |  |  | 0 | 0 | 0 |  |  |  | 0 | 0 | 0 |  |  |  | 0 | 0 | 0 |  |  |  | 0 | 0 | 0 |  |  |  | 0 | 0 | 0
 |  |  |  |  |  |  |  |  |  | 0 | 0 | 0 |  |  |  | 0 | 0 | 0 |  |  |  | 0 | 0 | 0 |  |  |  | 0 | 0 | 0 |  |  |  | 0 | 0 | 0
 |  |  |  |  |  |  |  |  |  | 0 | 0 | 0 |  |  |  | 0 | 0 | 0 |  |  |  | 0 | 0 | 0 |  |  |  | 0 | 0 | 0 |  |  |  | 0 | 0 | 0
 |  |  |  |  |  |  |  |  |  | 0 | 0 | 0 |  |  |  | 0 | 0 | 0 |  |  |  | 0 | 0 | 0 |  |  |  | 0 | 0 | 0 |  |  |  | 0 | 0 | 0
 |  |  |  |  |  |  |  |  |  | 0 | 0 | 0 |  |  |  | 0 | 0 | 0 |  |  |  | 0 | 0 | 0 |  |  |  | 0 | 0 | 0 |  |  |  | 0 | 0 | 0
 |  |  |  |  |  |  |  |  |  | 0 | 0 | 0 |  |  |  | 0 | 0 | 0 |  |  |  | 0 | 0 | 0 |  |  |  | 0 | 0 | 0 |  |  |  | 0 | 0 | 0
 |  |  |  |  |  |  |  |  |  | 0 | 0 | 0 |  |  |  | 0 | 0 | 0 |  |  |  | 0 | 0 | 0 |  |  |  | 0 | 0 | 0 |  |  |  | 0 | 0 | 0
 |  |  |  |  |  |  |  |  |  | 0 | 0 | 0 |  |  |  | 0 | 0 | 0 |  |  |  | 0 | 0 | 0 |  |  |  | 0 | 0 | 0 |  |  |  | 0 | 0 | 0
 |  |  |  |  |  |  |  |  |  | 0 | 0 | 0 |  |  |  | 0 | 0 | 0 |  |  |  | 0 | 0 | 0 |  |  |  | 0 | 0 | 0 |  |  |  | 0 | 0 | 0
 |  |  |  |  |  |  |  |  |  | 0 | 0 | 0 |  |  |  | 0 | 0 | 0 |  |  |  | 0 | 0 | 0 |  |  |  | 0 | 0 | 0 |  |  |  | 0 | 0 | 0
