ciaa/Ponchos/WifiBT_CESE_ESPWROOM32/doc/PonchoEDUCIAA_WIFI_BLT.pdf

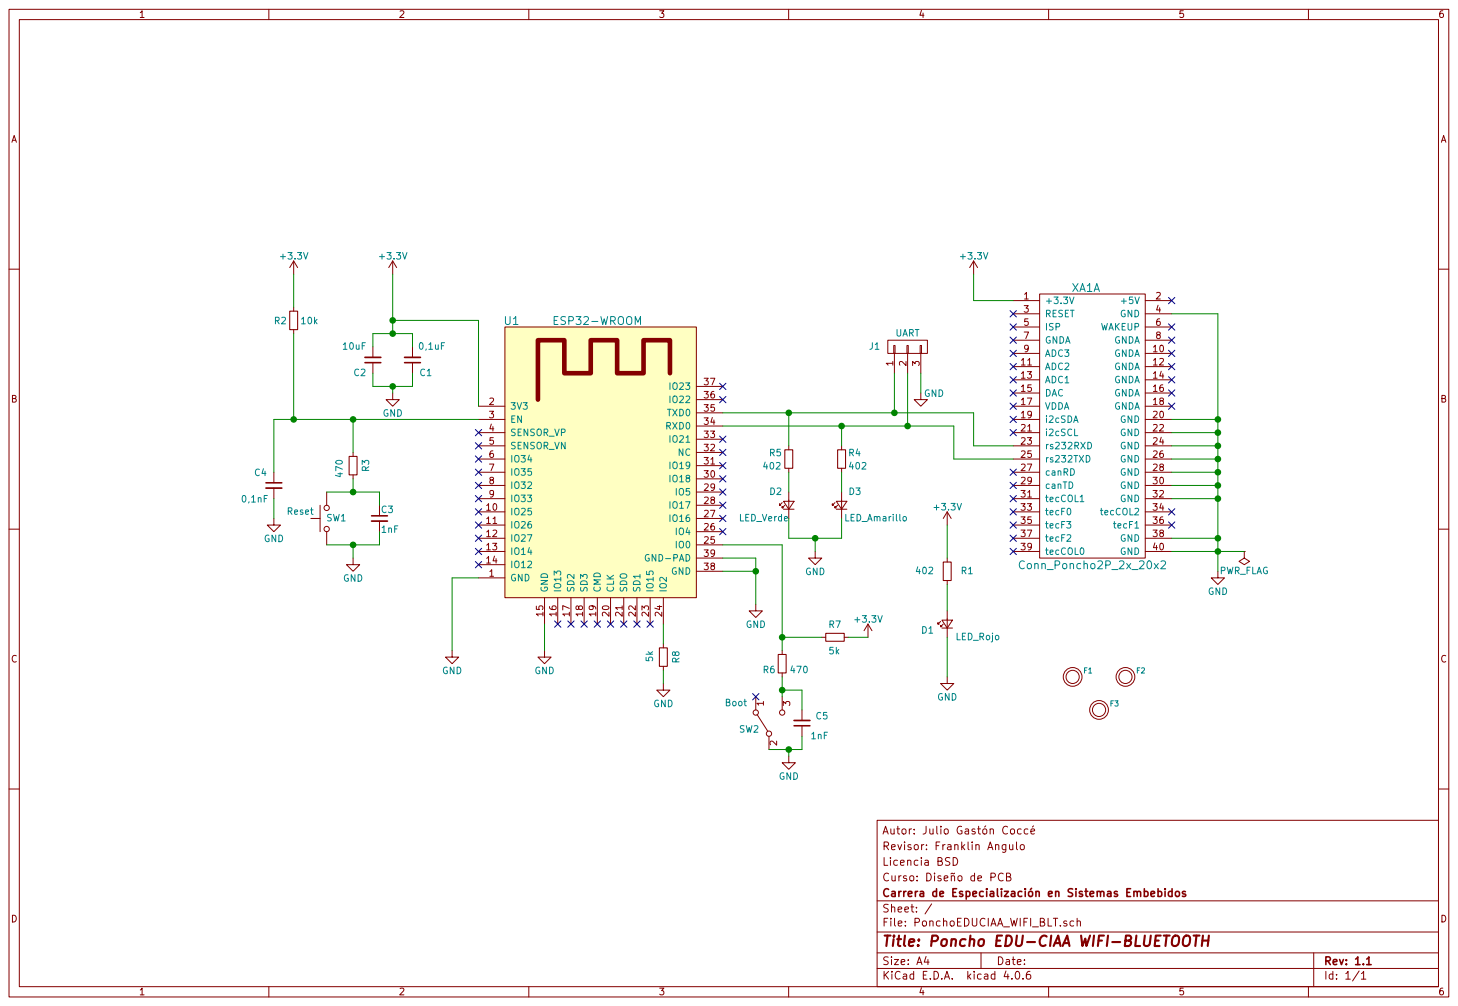
[picture p171: page 1]

Revisor: Franklin Angulo Autor: Julio Gastón Coccé GND 1

Licencia BSD
File: PonchoEDUCIAA_WIFI_BLT.sch Sheet: / Carrera de Especialización en Sistemas Embebidos Curso: Diseño de PCB

Id: 1/1 Title: Poncho EDU-CIAA WIFI-BLUETOOTH
