ciaa/Ponchos/MIDI/Doc/Esquemático.pdf

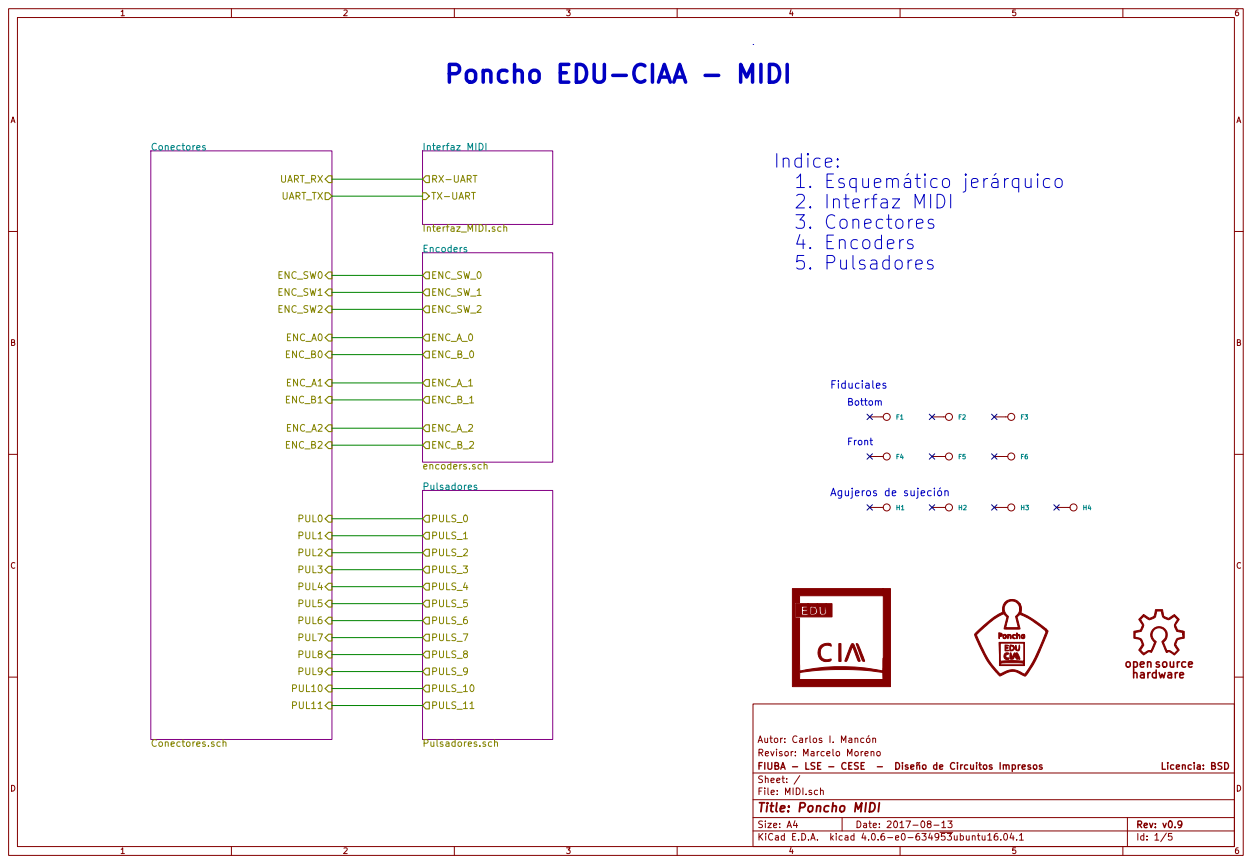
[picture p172: page 1]

Poncho EDU-CIAA - MIDI

Front Agujeros de sujeción

Revisor: Marcelo Moreno Autor: Carlos I. Mancón

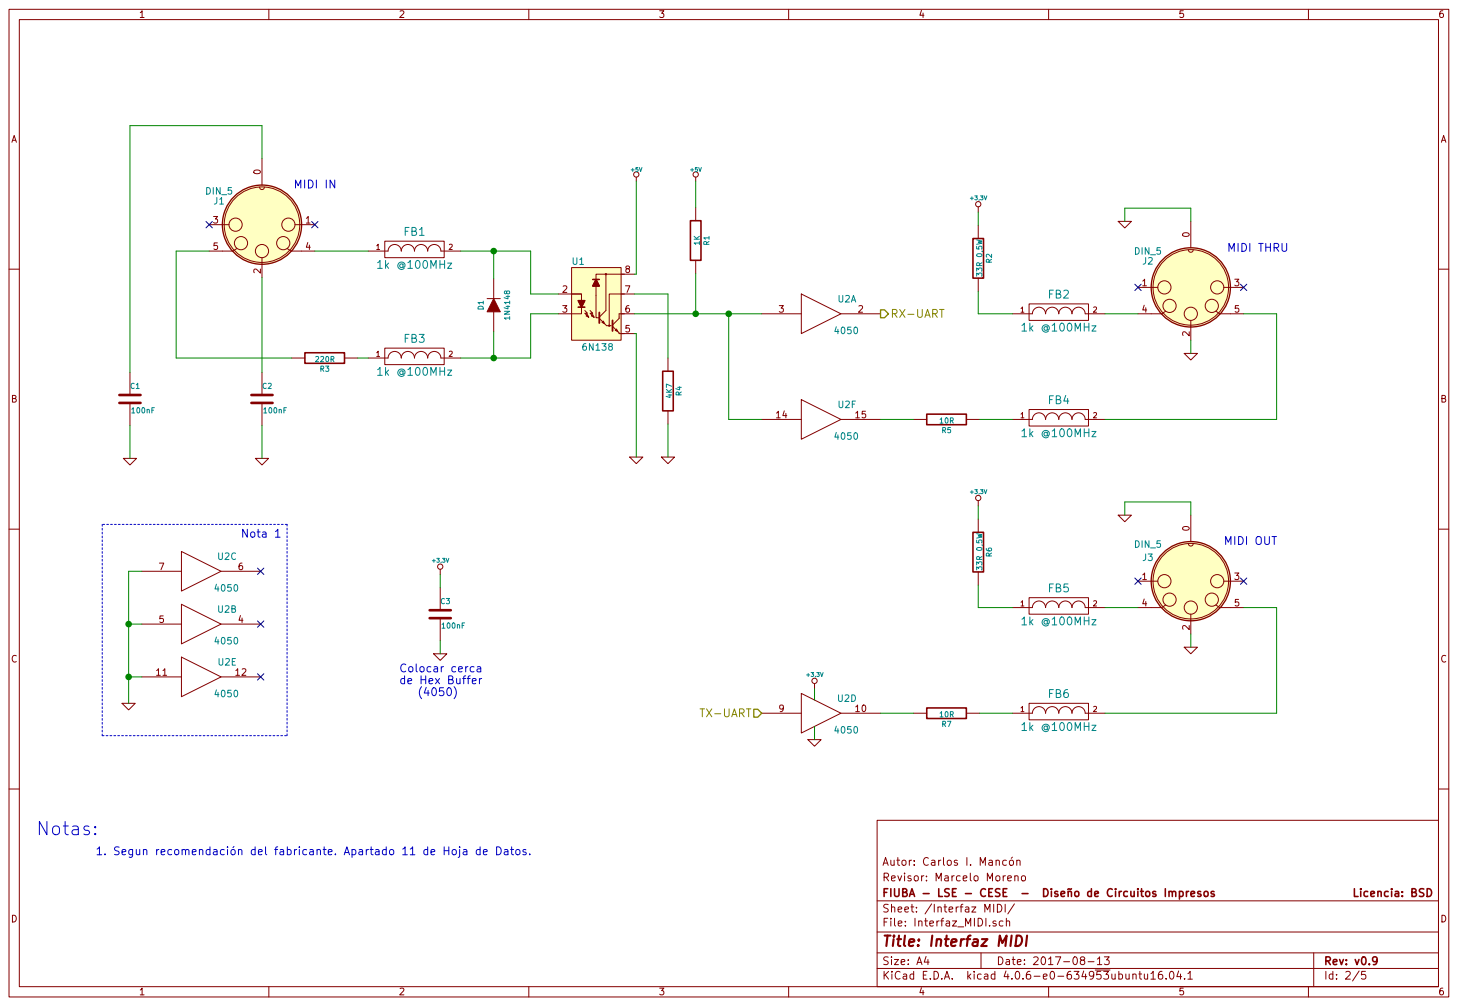
[picture p173: page 2]

1. Segun recomendación del fabricante. Apartado 11 de Hoja de Datos.

Revisor: Marcelo Moreno Autor: Carlos I. Mancón

Id: 2/5 Title: Interfaz MIDI

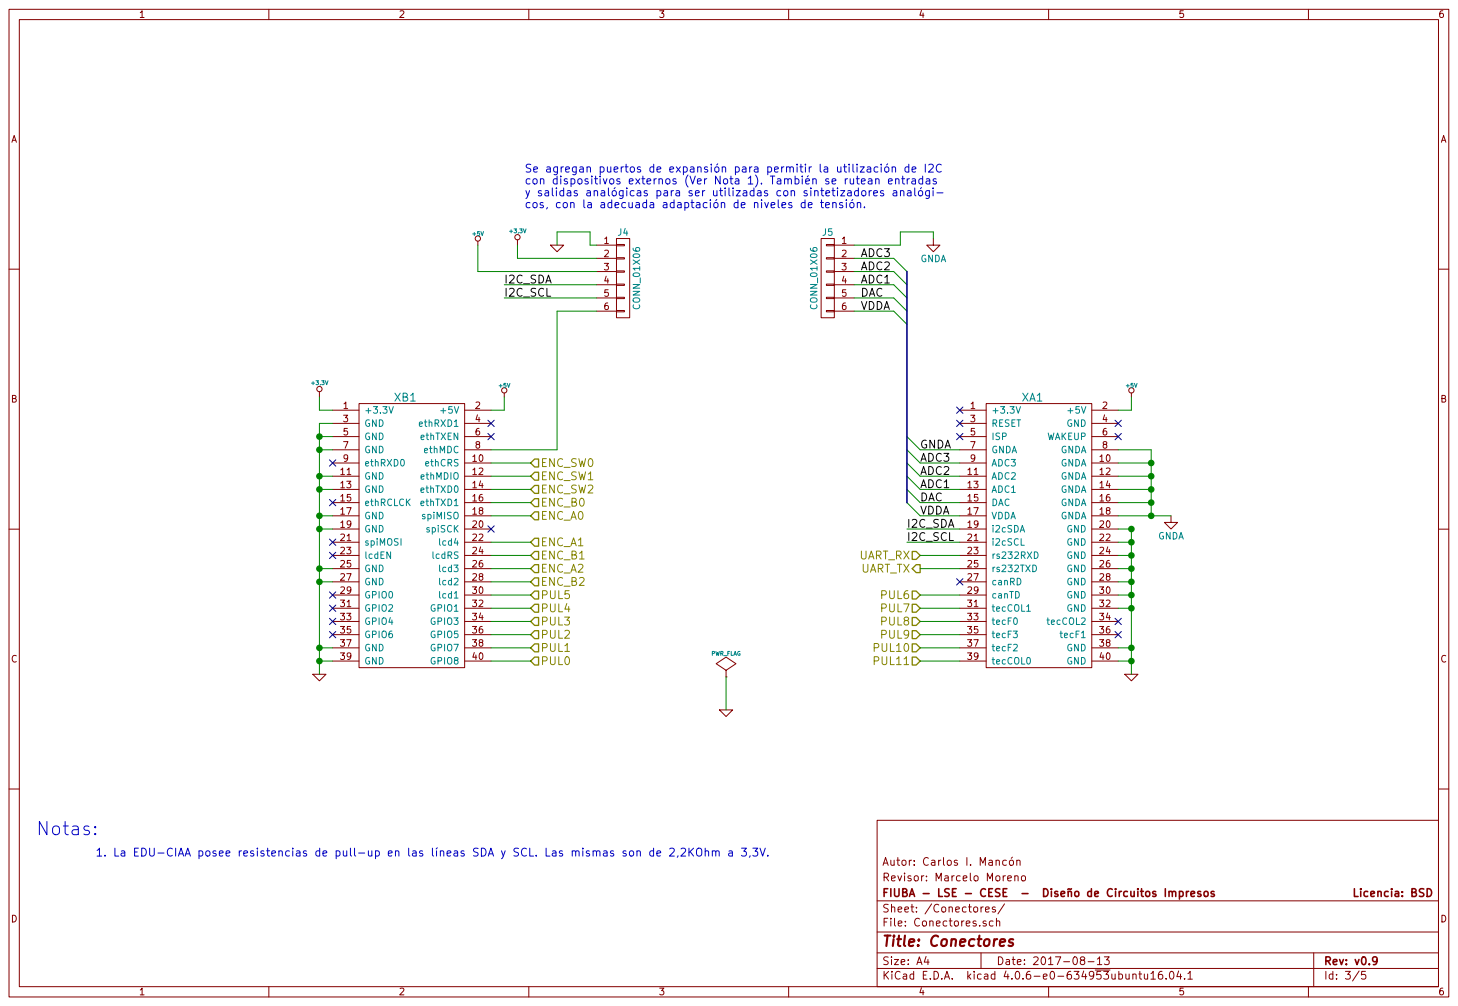
[picture p174: page 3]

Se agregan puertos de expansión para permitir la utilización de I2C
con dispositivos externos (Ver Nota 1). También se rutean entradas
y salidas analógicas para ser utilizadas con sintetizadores analógi-
cos, con la adecuada adaptación de niveles de tensión.
ADC2
ADC1
DAC

1. La EDU-CIAA posee resistencias de pull-up en las líneas SDA y SCL. Las mismas son de 2,2KOhm a 3,3V.

Revisor: Marcelo Moreno Autor: Carlos I. Mancón

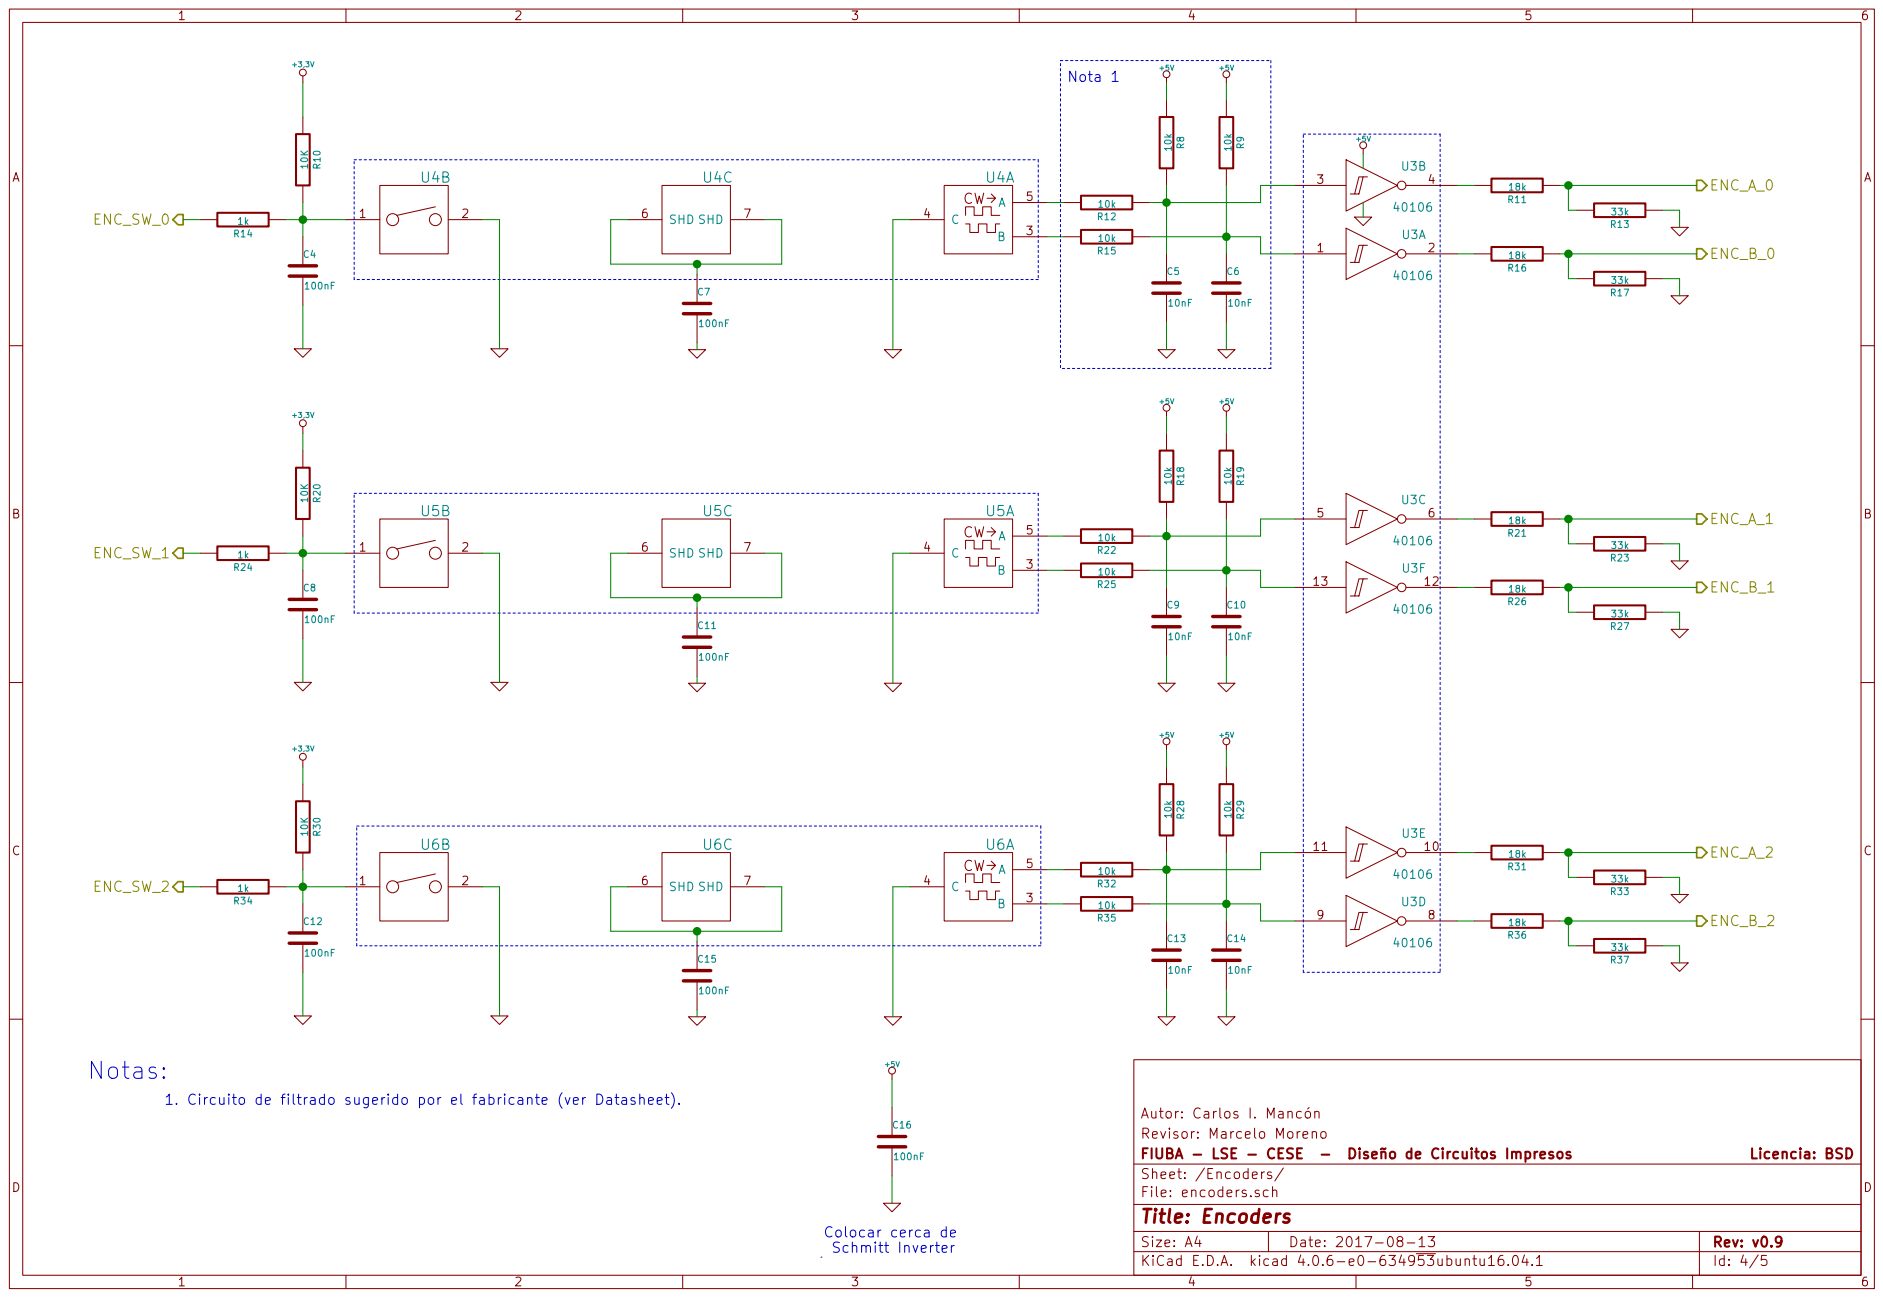
[picture p175: page 4]

1. Circuito de filtrado sugerido por el fabricante (ver Datasheet).

Revisor: Marcelo Moreno Autor: Carlos I. Mancón

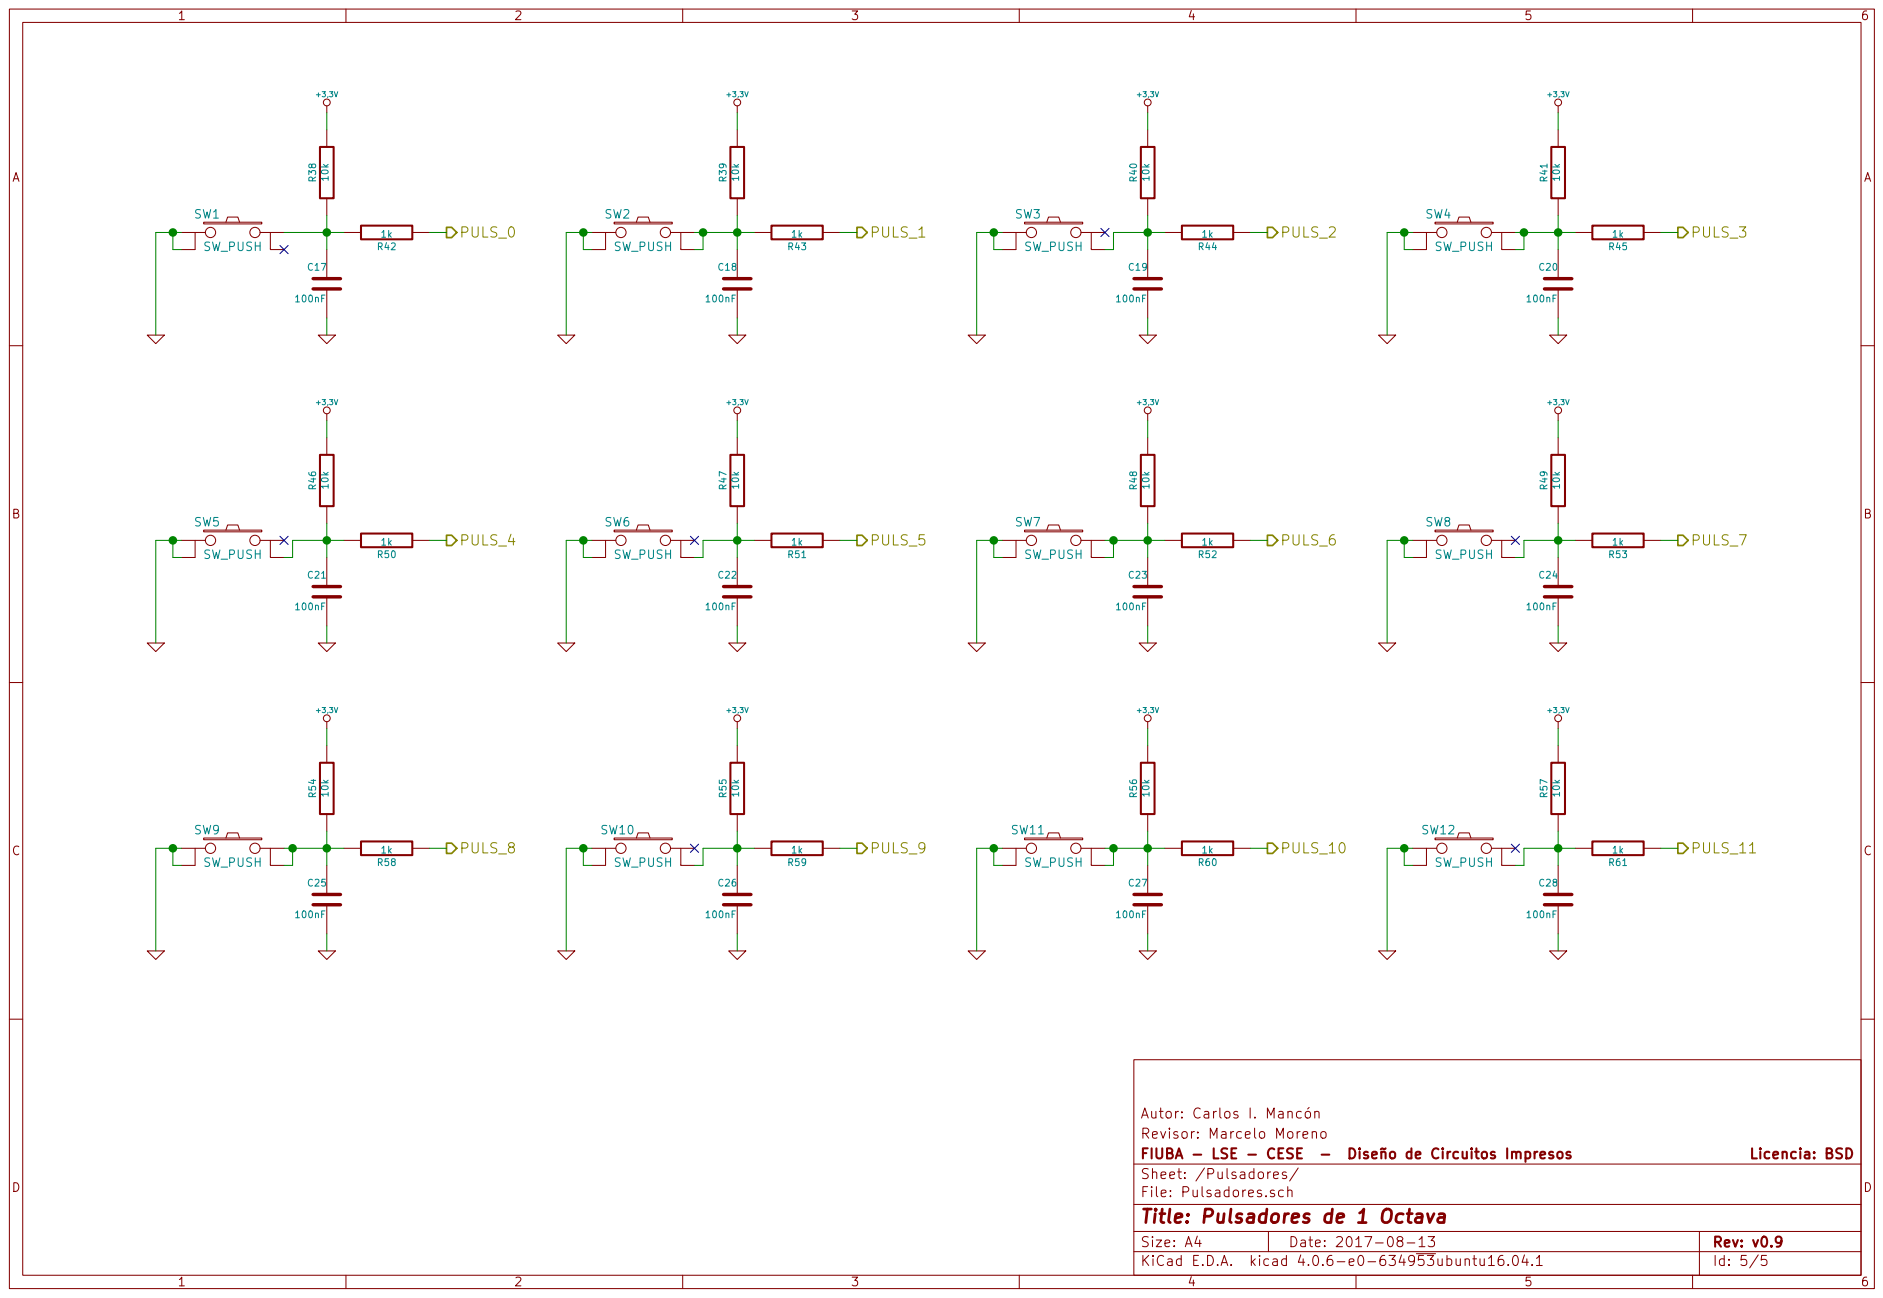
[picture p176: page 5]

Revisor: Marcelo Moreno Autor: Carlos I. Mancón

Id: 5/5 Title: Pulsadores de 1 Octava
