ciaa/Ponchos/ethernet_LAN8720A_v2/hdatos/ASV.PDF

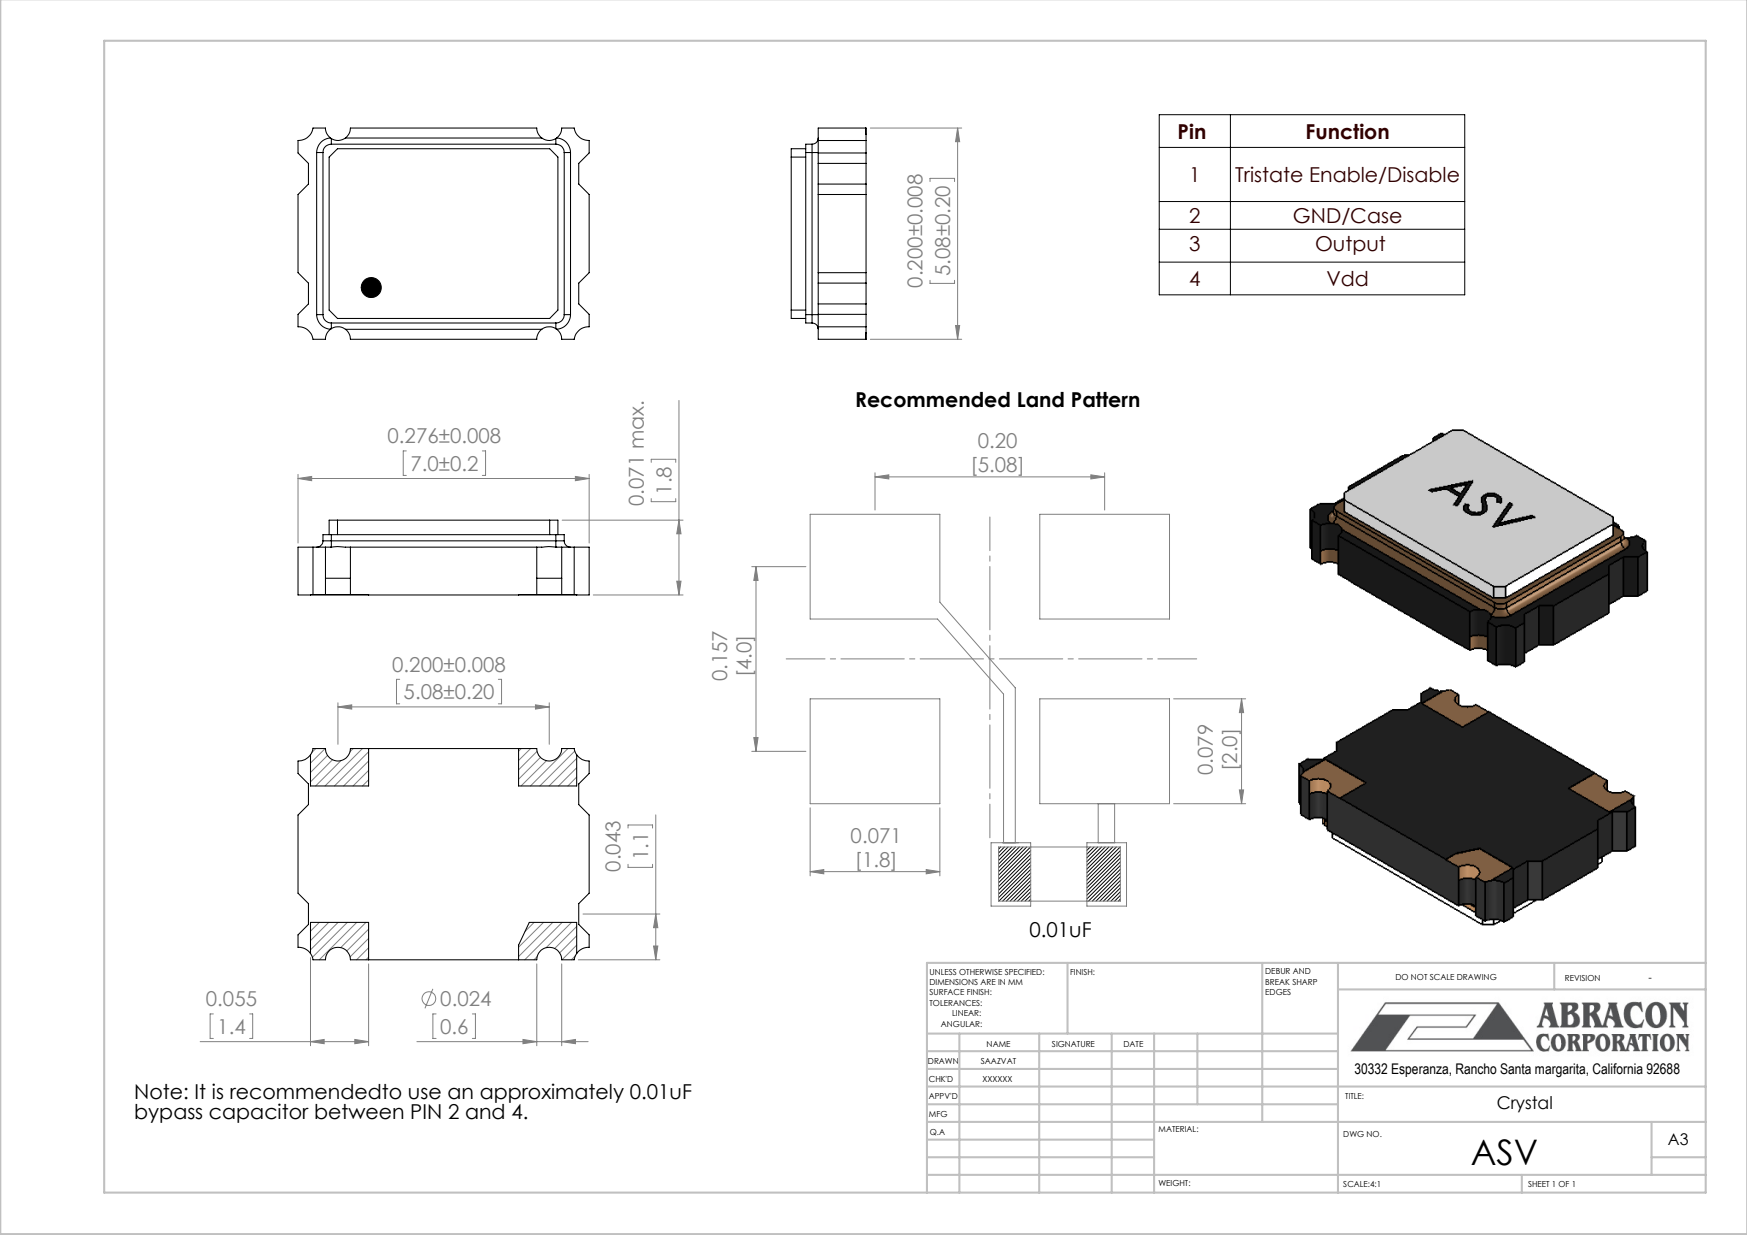
[picture p177: page 1]
SCALE:4:1; SHEET 1 OF 1; DO NOT SCALE DRAWING; REVISION; DEBUR AND BREAK SHARP; UNLESS OTHERWISE SPECIFIED:; FINISH:; DRAWN; 30332 Esperanza, Rancho Santa margarita, California 92688

Pin | Function
1 | Tristate Enable/Disable
2 | GND/Case
3 | Output
4 | Vdd

Recommended Land Pattern

DIMENSIONS ARE IN MM
SURFACE FINISH:
TOLERANCES:
LINEAR:
ANGULAR:

CHK'D | XXXXXX
APPV'D | | | | | TITLE: Crystal
MFG
Q.A | | MATERIAL: | DWG NO. ASV | A3

Note: It is recommendedto use an approximately 0.01uF
bypass capacitor between PIN 2 and 4.
