ciaa/Ponchos/Simon/gerber/pdf/simonShield-F.SilkS.pdf

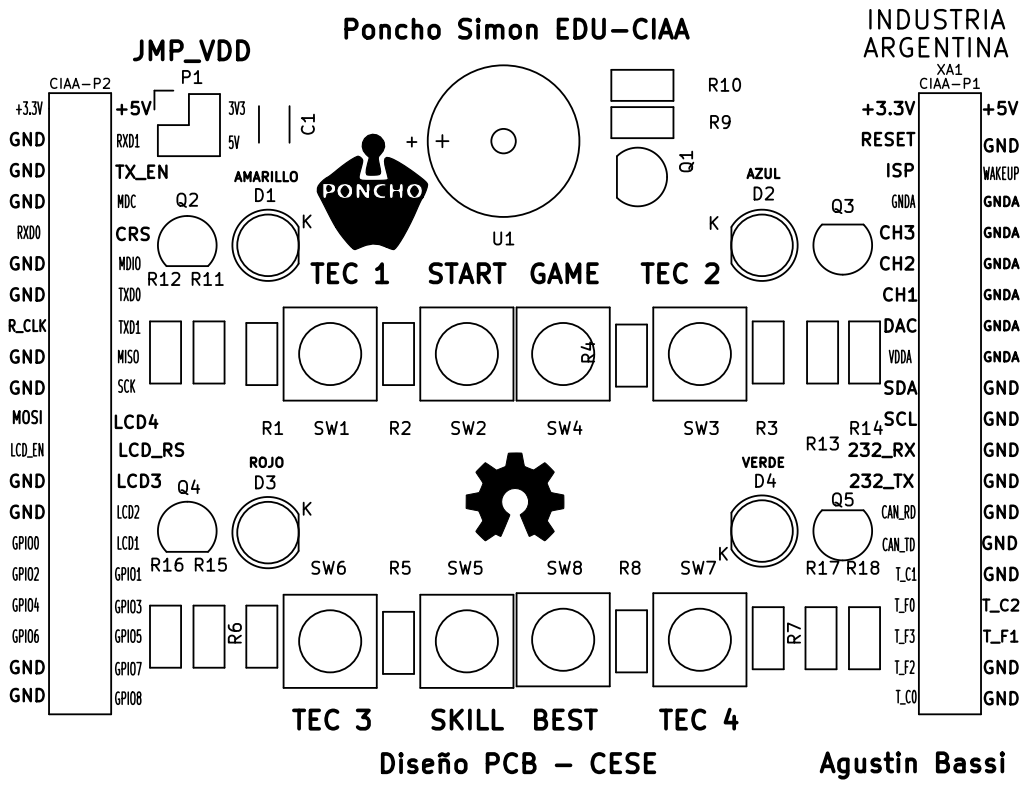
[picture p178: page 1]

RXD1 +5V GND GND GPIO6 GPIO4 GPIO2 GPIO0 GND GND
RXD0 GND GND
R_CLK GND GND GND

GNDA GNDA GNDA GNDA GNDA GNDA WAKEUP GND

DAC
VDDA
T_F1 T_C2 GND GND GND GND GND GND GND
