ciaa/Ponchos/Osciloscopio/doc/Circuitos de osciloscopios simples/miniscope_v2b_20110623.pdf

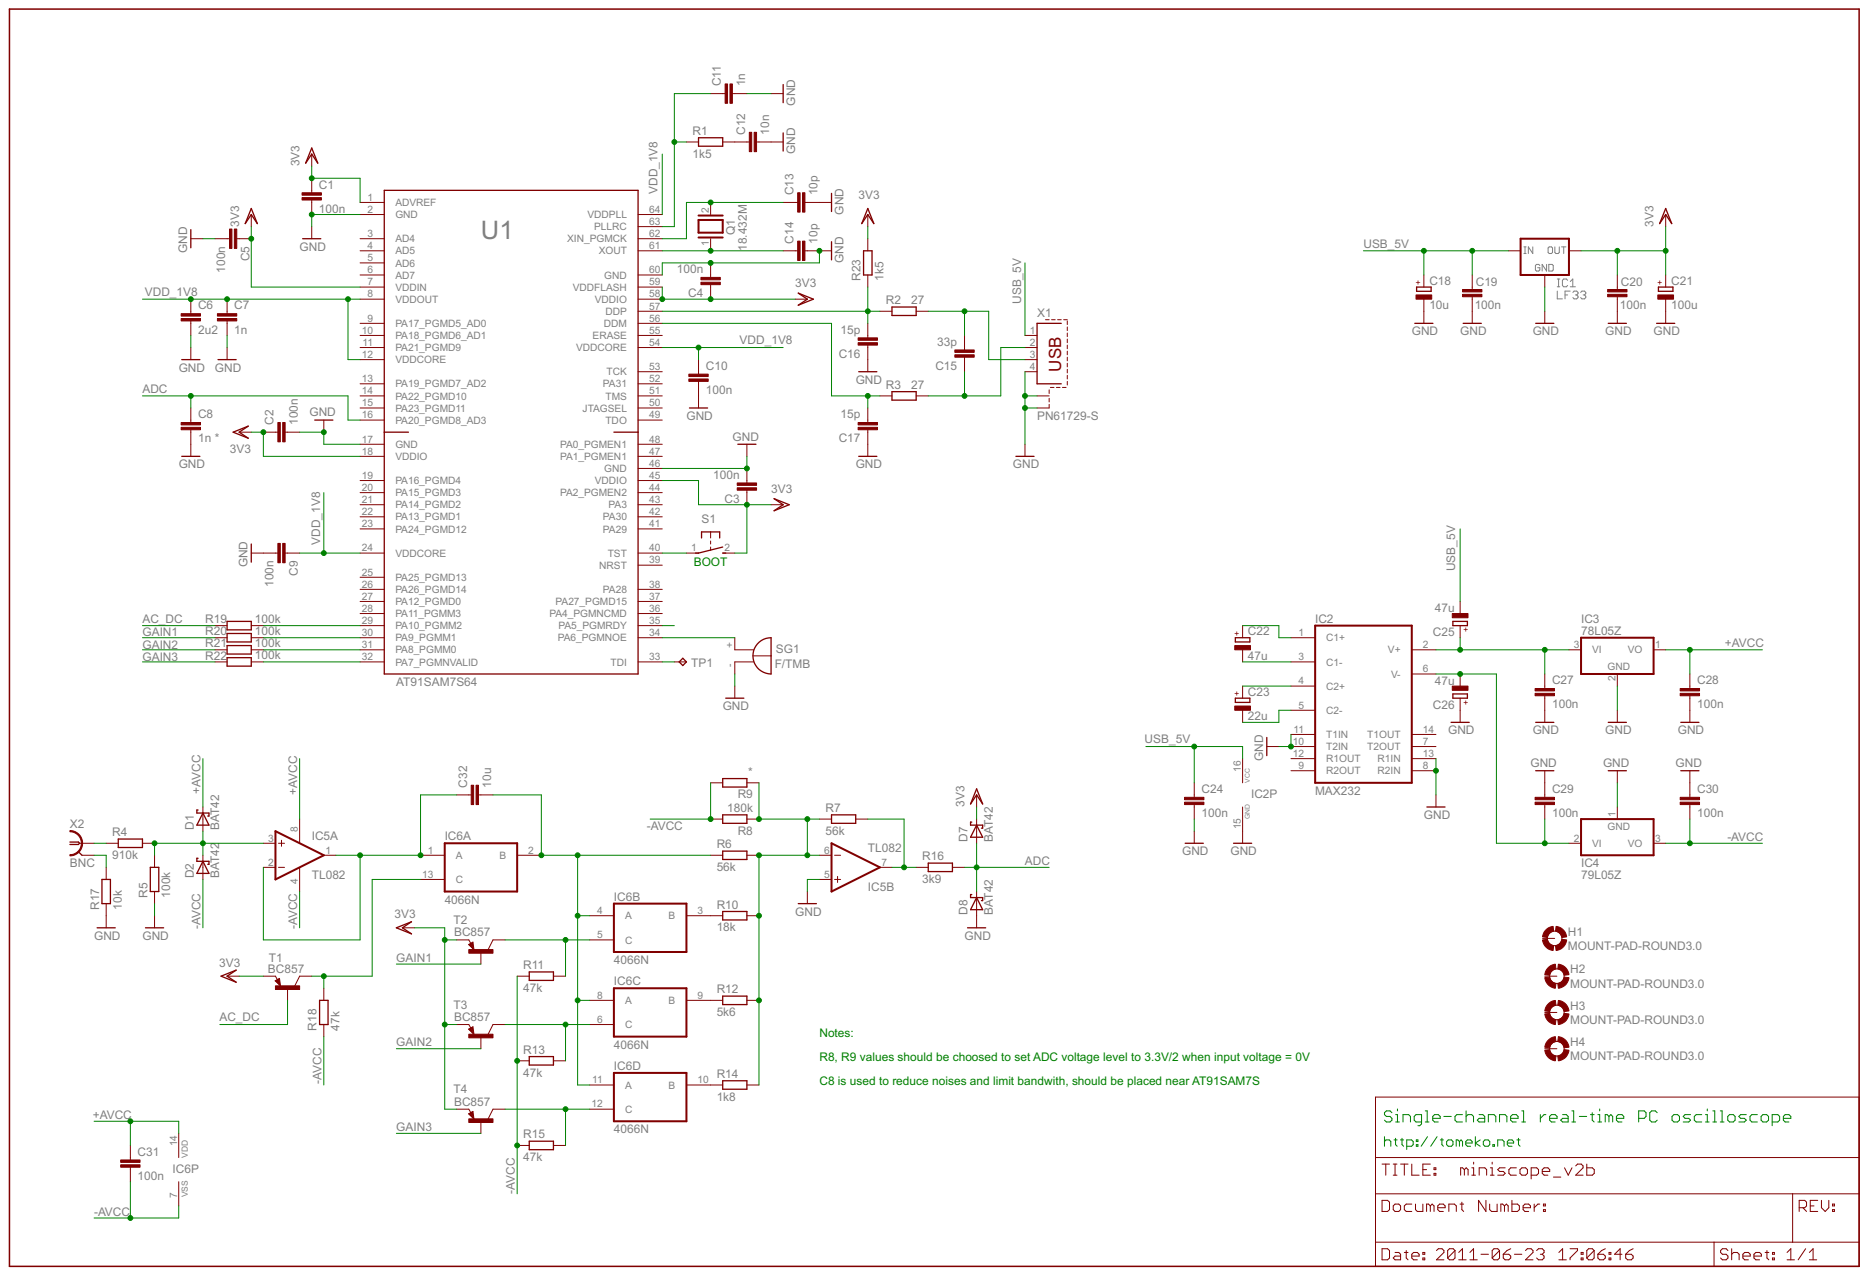
[picture p179: page 1]

Notes: R8, R9 values should be choosed to set ADC voltage level to 3.3V/2 when input voltage = 0V

C8 is used to reduce noises and limit bandwith, should be placed near AT91SAM7S
