ciaa/Ponchos/ECG/ECG_CIAA.pdf

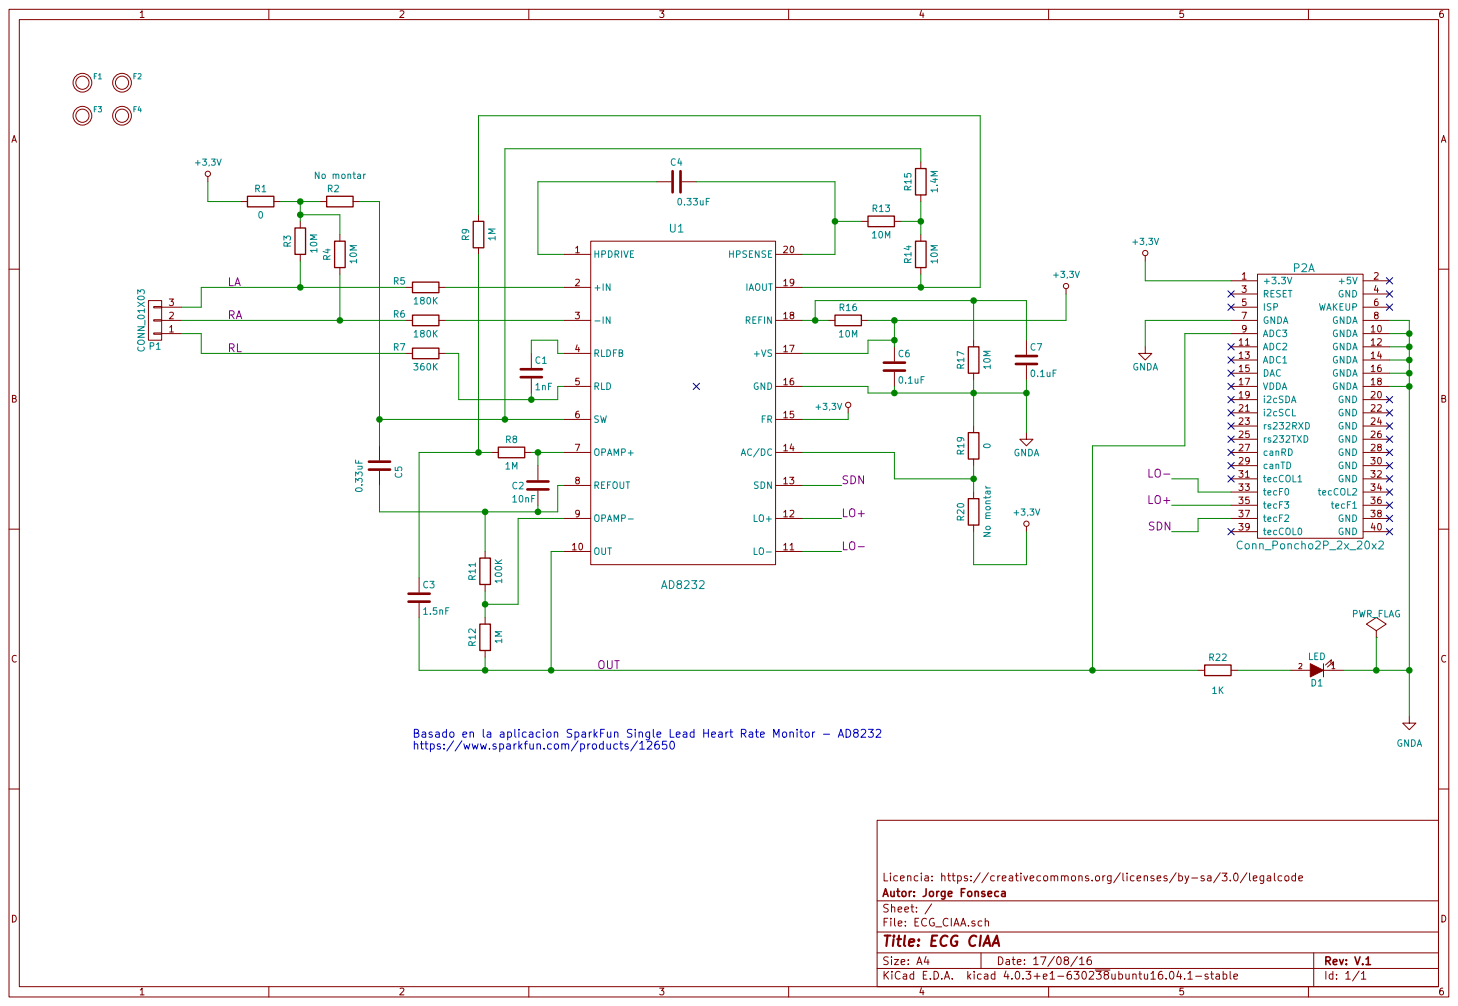
[picture p182: page 1]

https://www.sparkfun.com/products/12650

Licencia: https://creativecommons.org/licenses/by-sa/3.0/legalcode
File: ECG_CIAA.sch Sheet: / Autor: Jorge Fonseca

Id: 1/1 Title: ECG CIAA
