ciaa/Ponchos/NivelTanque/kicad/Esquema.pdf

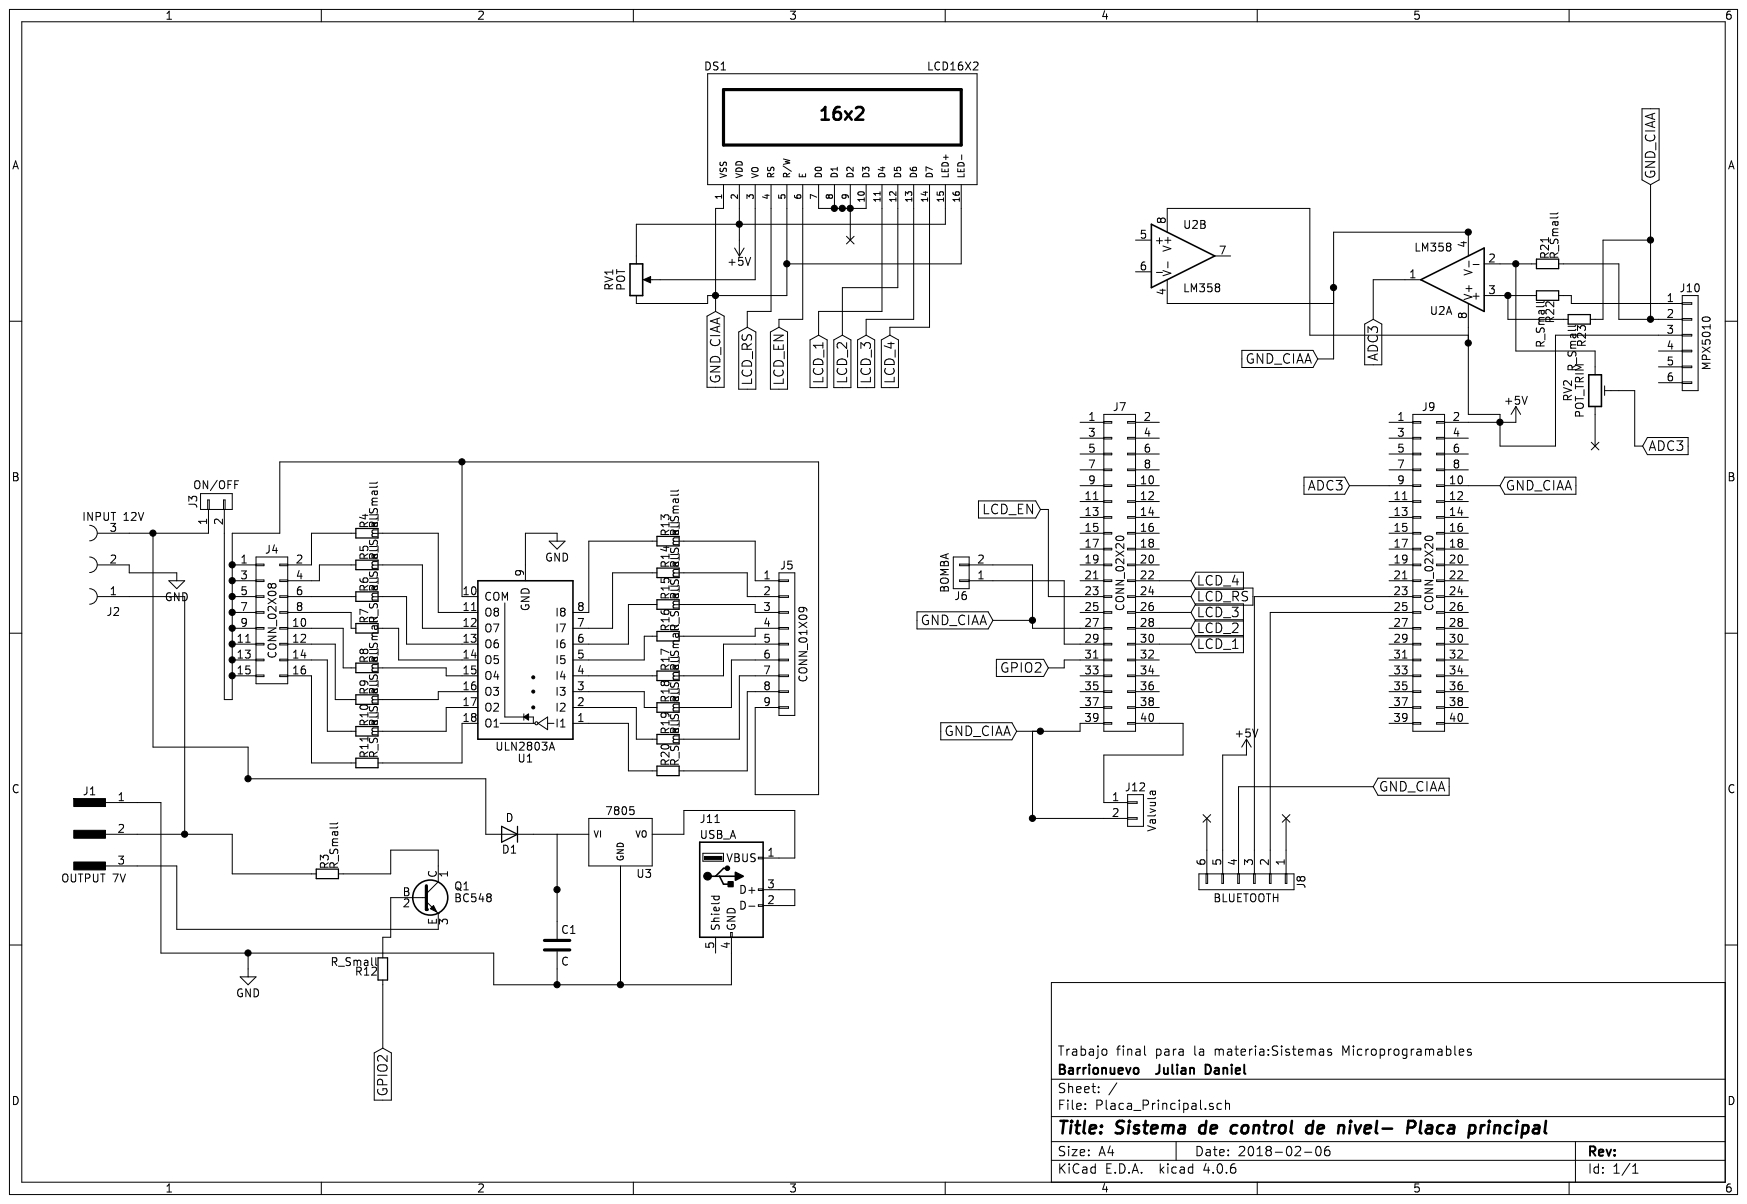
[picture p183: page 1]
