ciaa/Ponchos/NivelTanque/kicad/PDF1.pdf

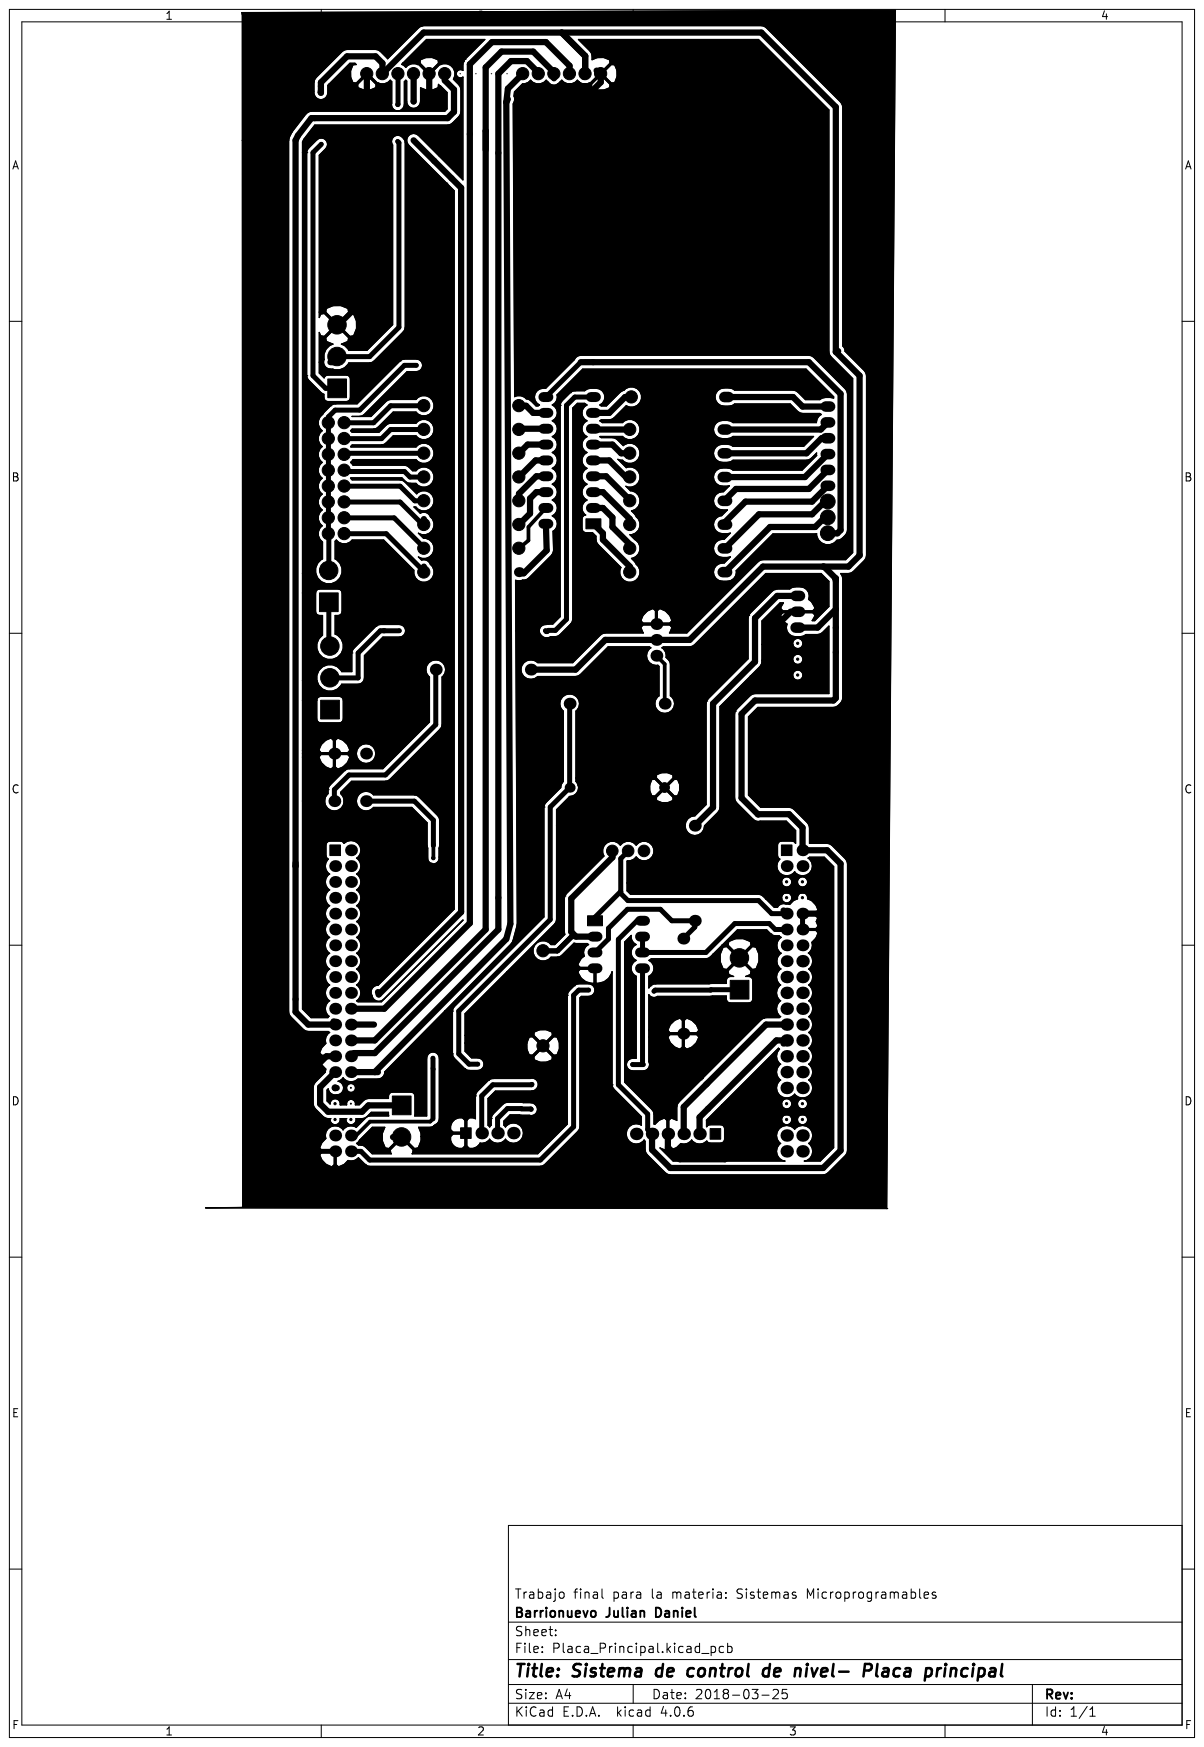
[picture p184: page 1]
