ciaa/Ponchos/NivelTanque/kicad/PDF2.pdf

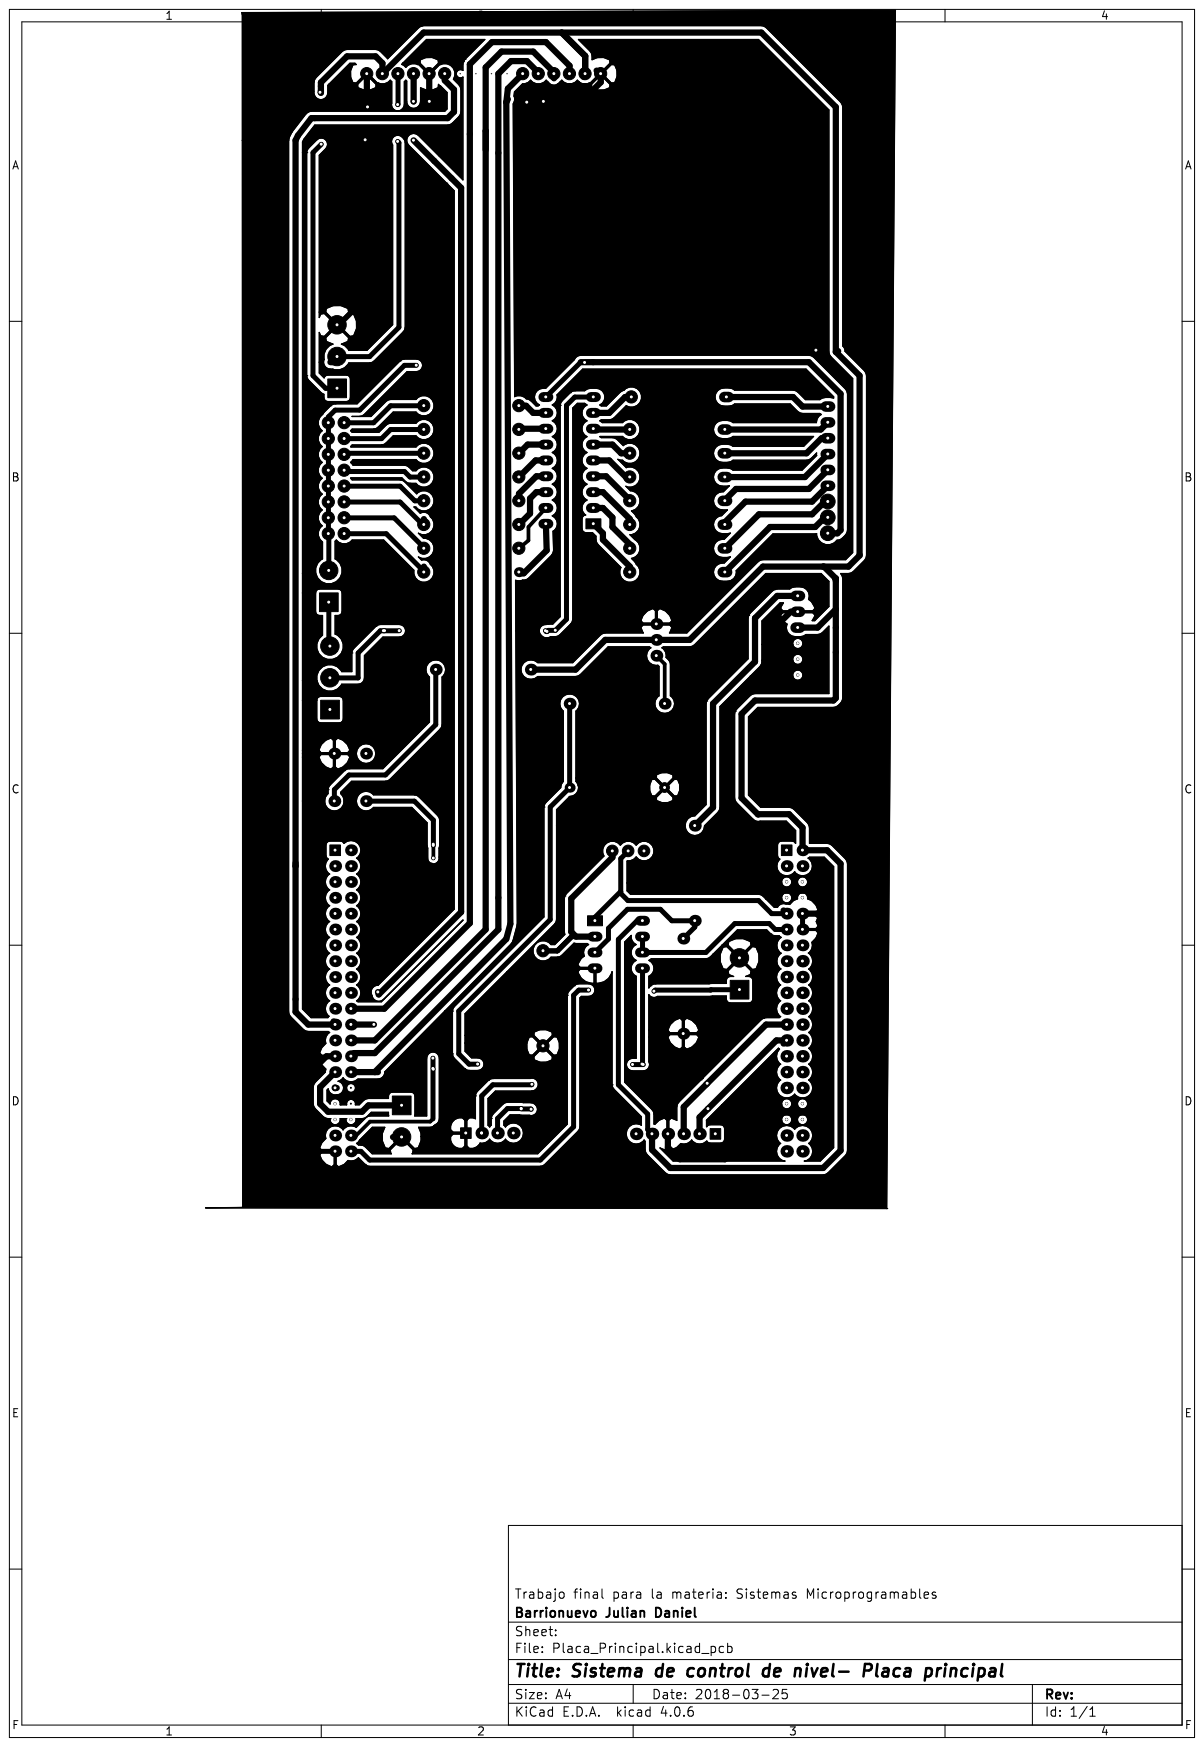
[picture p185: page 1]
