ciaa/Ponchos/Joystick/doc/esquematico.pdf

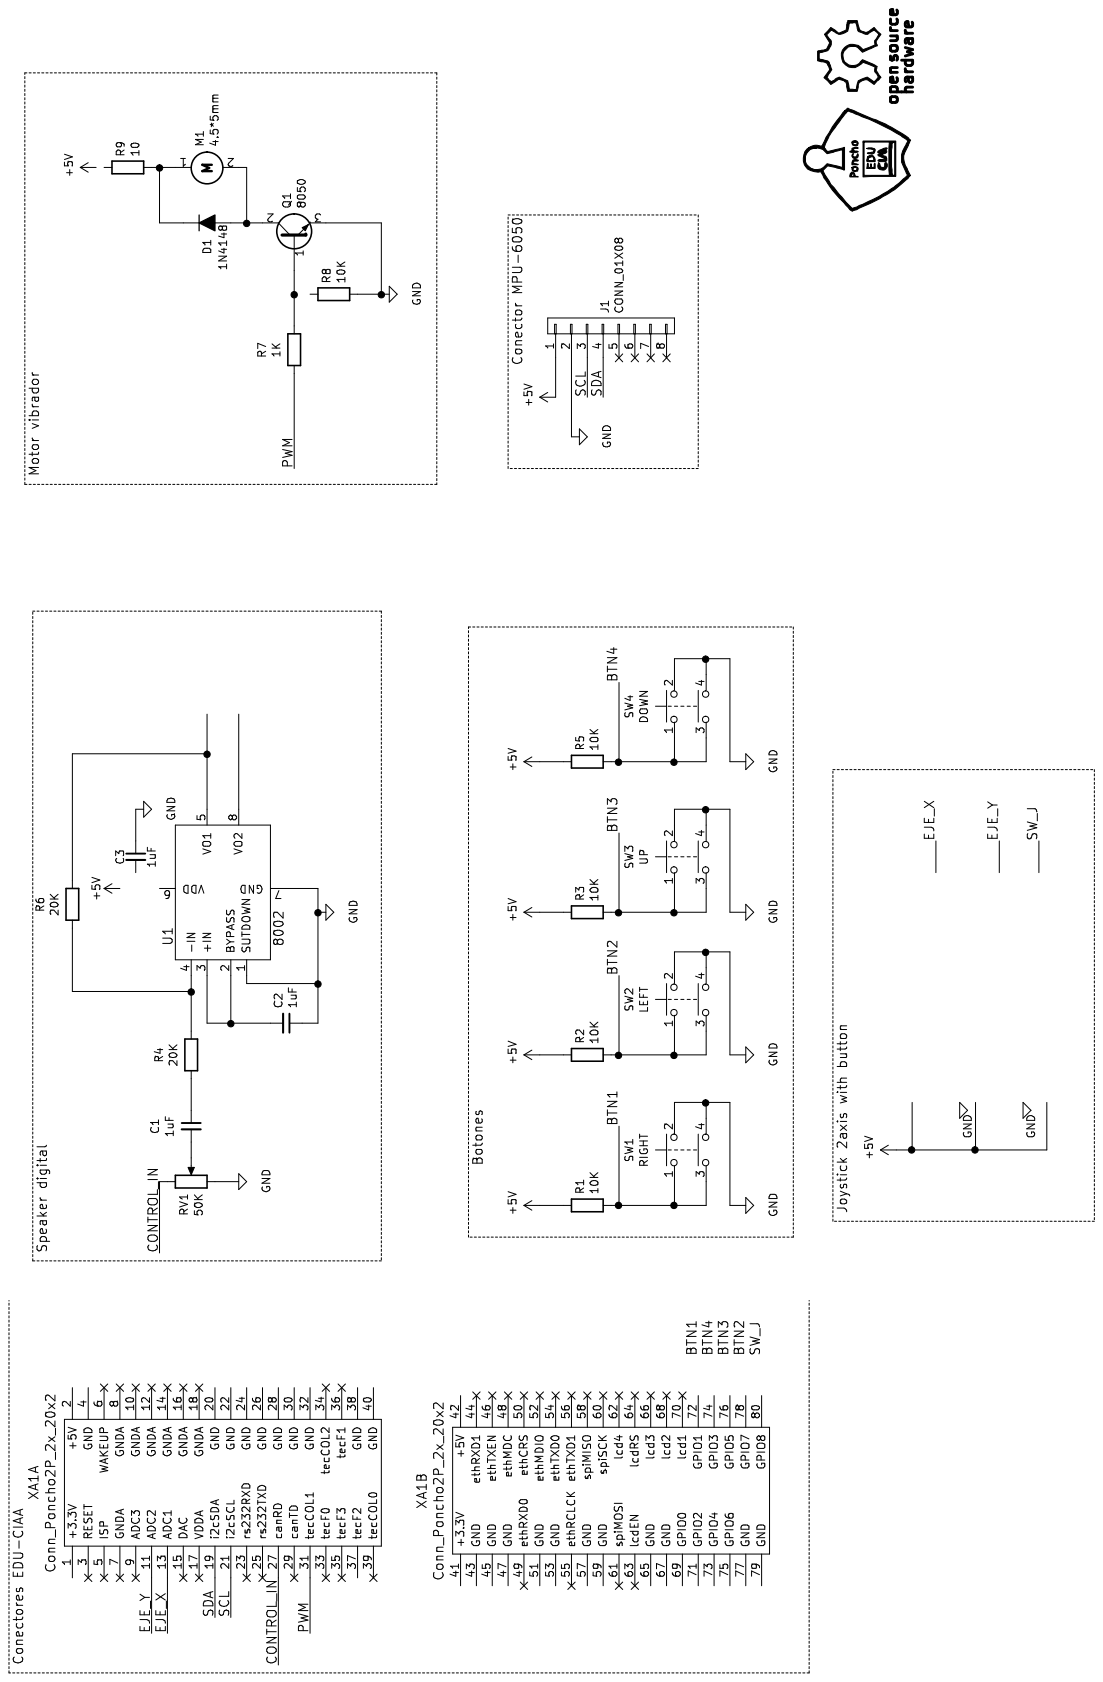
[picture p186: page 1]
