ciaa/Ponchos/Joystick/doc/impresion_pcb.pdf

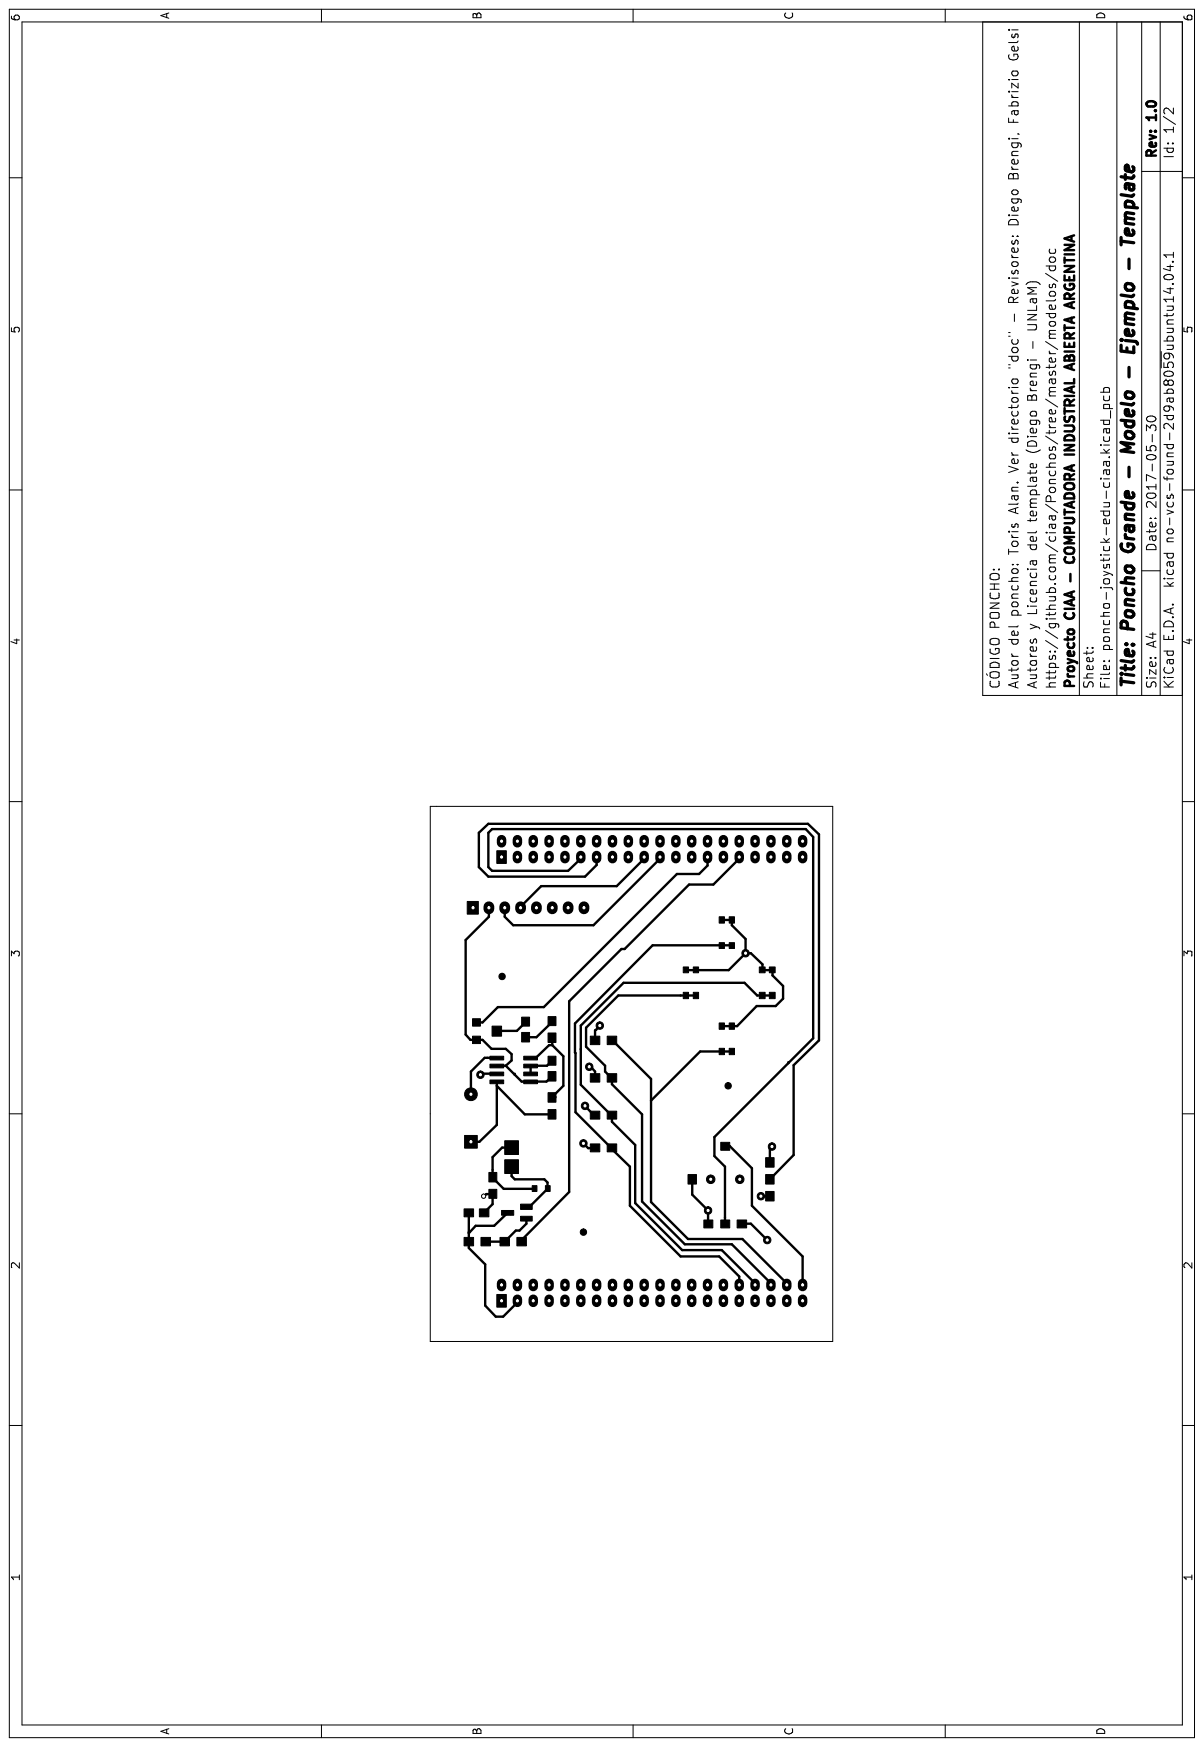
[picture p187: page 1]

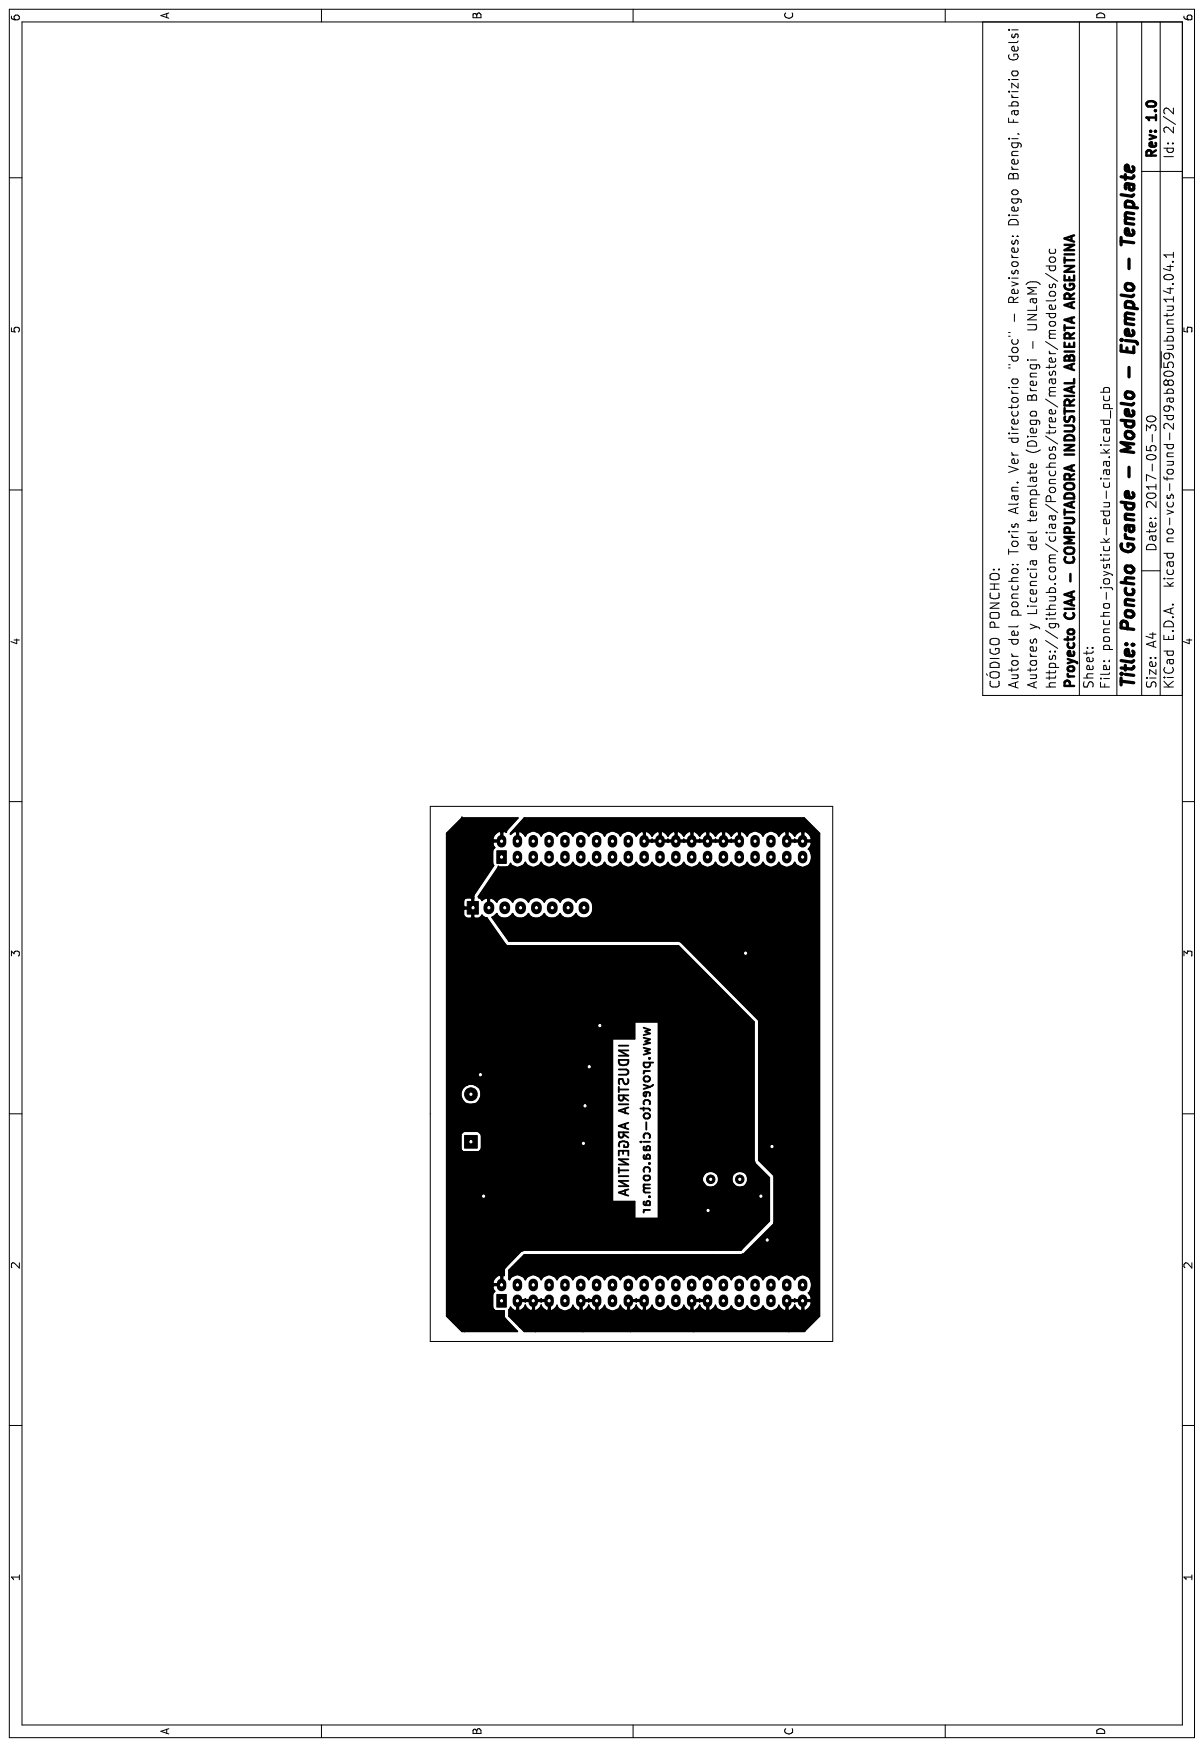
[picture p188: page 2]
