ciaa/Ponchos/MIDI/Doc/Dimensiones.pdf

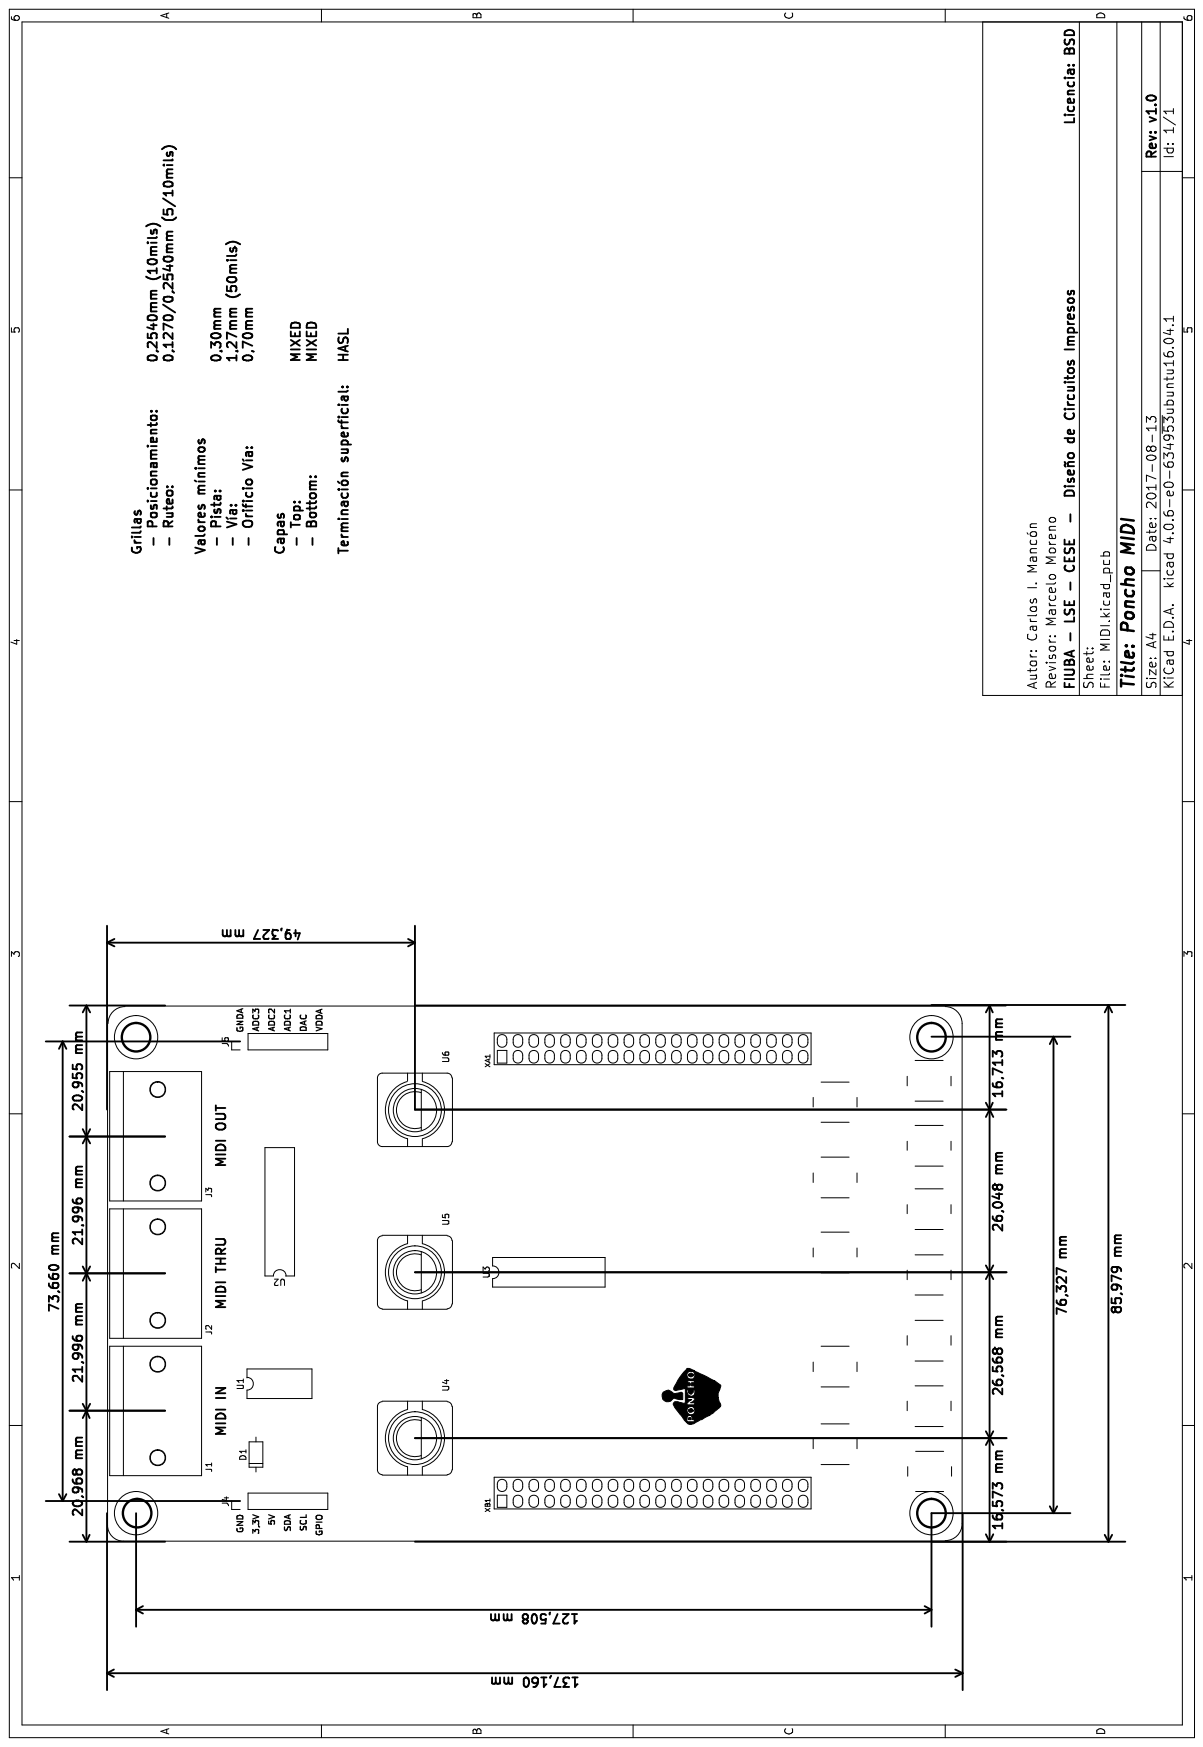
[picture p189: page 1]
