ciaa/Ponchos/Poncho PLC/doc/PonchoPLC -  SCH.pdf

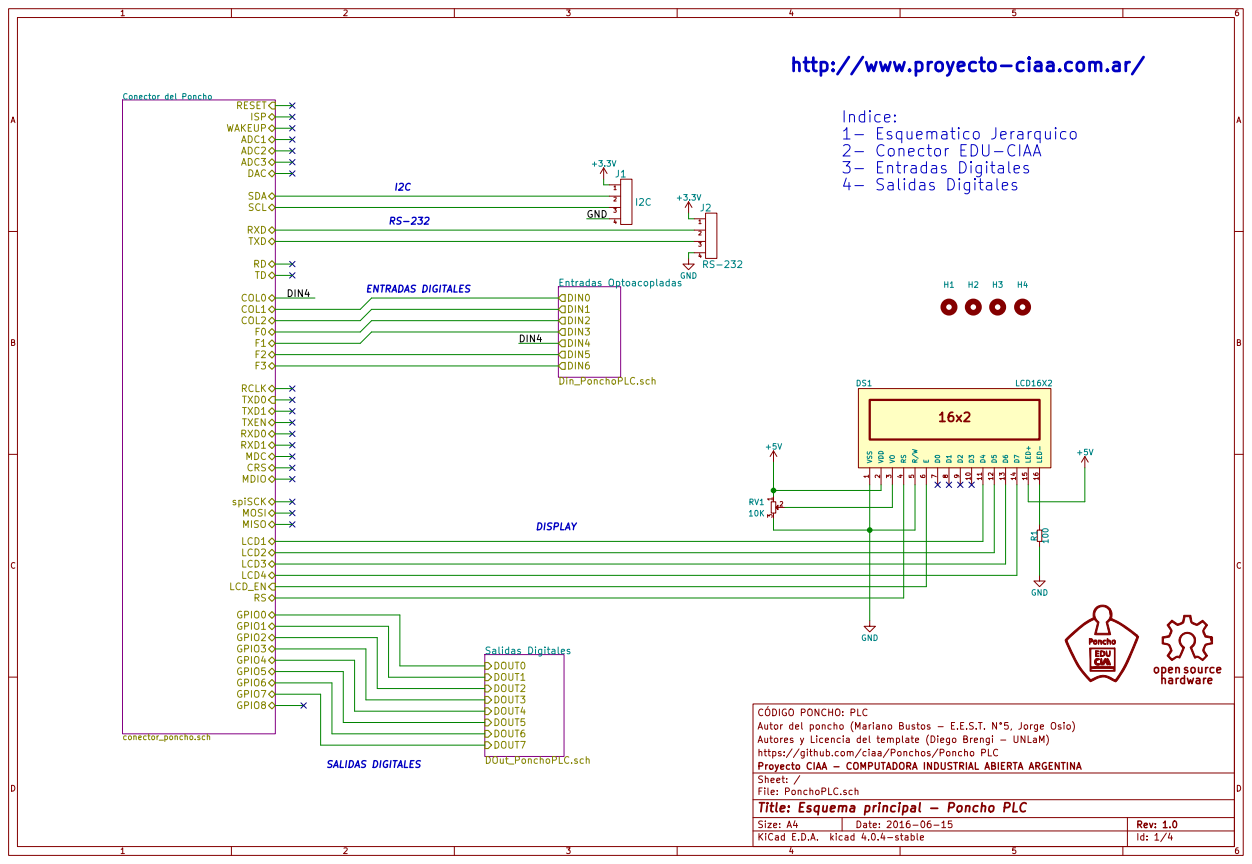
[picture p190: page 1]

http://www.proyecto-ciaa.com.ar/

CÓDIGO PONCHO: PLC
Autor del poncho (Mariano Bustos - E.E.S.T. N°5, Jorge Osio)
Autores y Licencia del template (Diego Brengi - UNLaM)
https://github.com/ciaa/Ponchos/Poncho PLC
File: PonchoPLC.sch Sheet: / Proyecto CIAA - COMPUTADORA INDUSTRIAL ABIERTA ARGENTINA

Id: 1/4 Title: Esquema principal - Poncho PLC

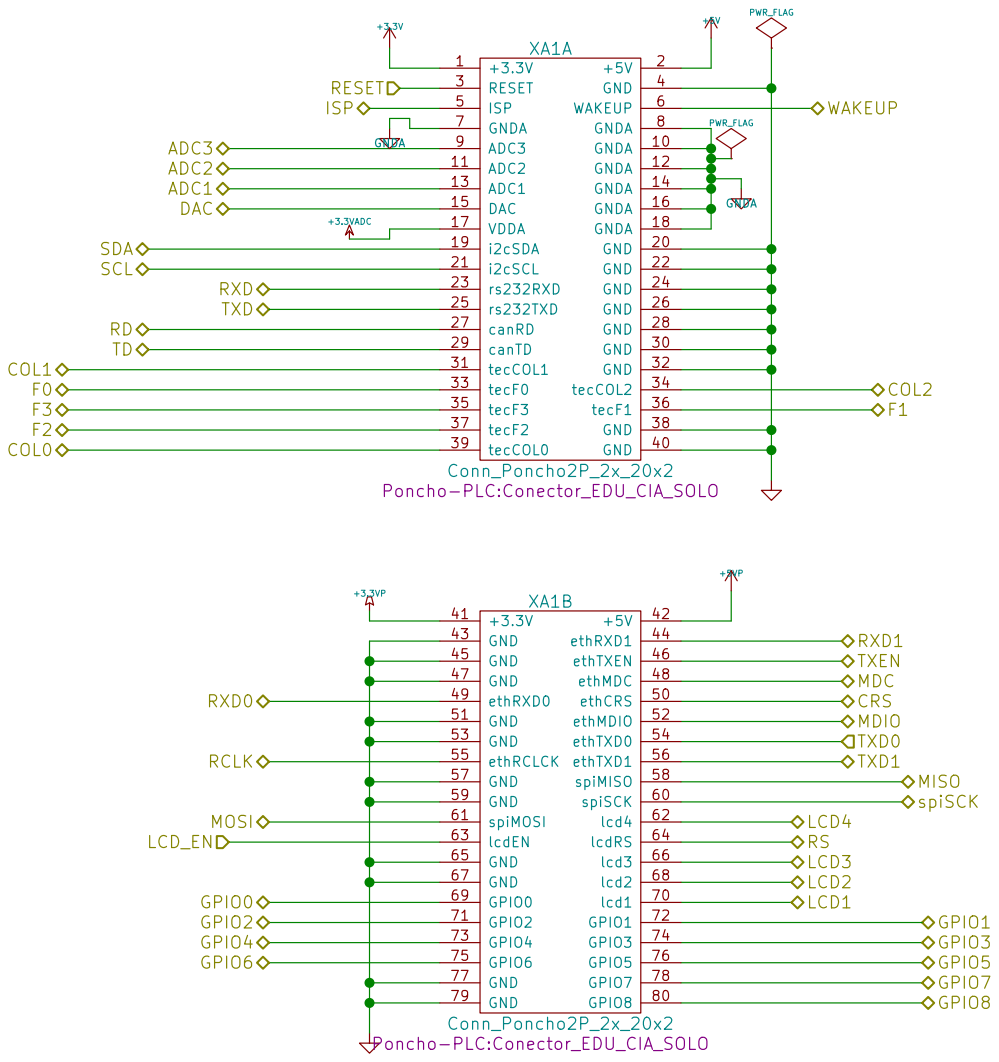
[picture p191: page 2]

CÓDIGO PONCHO: PLC
Autor del poncho (Mariano Bustos - E.E.S.T. N°5, Jorge Osio)
Autores y Licencia del template (Diego Brengi - UNLaM)
https://github.com/ciaa/Ponchos/Poncho PLC
File: conector_poncho.sch Sheet: /Conector del Poncho/ Proyecto CIAA - COMPUTADORA INDUSTRIAL ABIERTA ARGENTINA

Id: 2/4 Title: Poncho Grande - Modelo - Ejemplo - Template

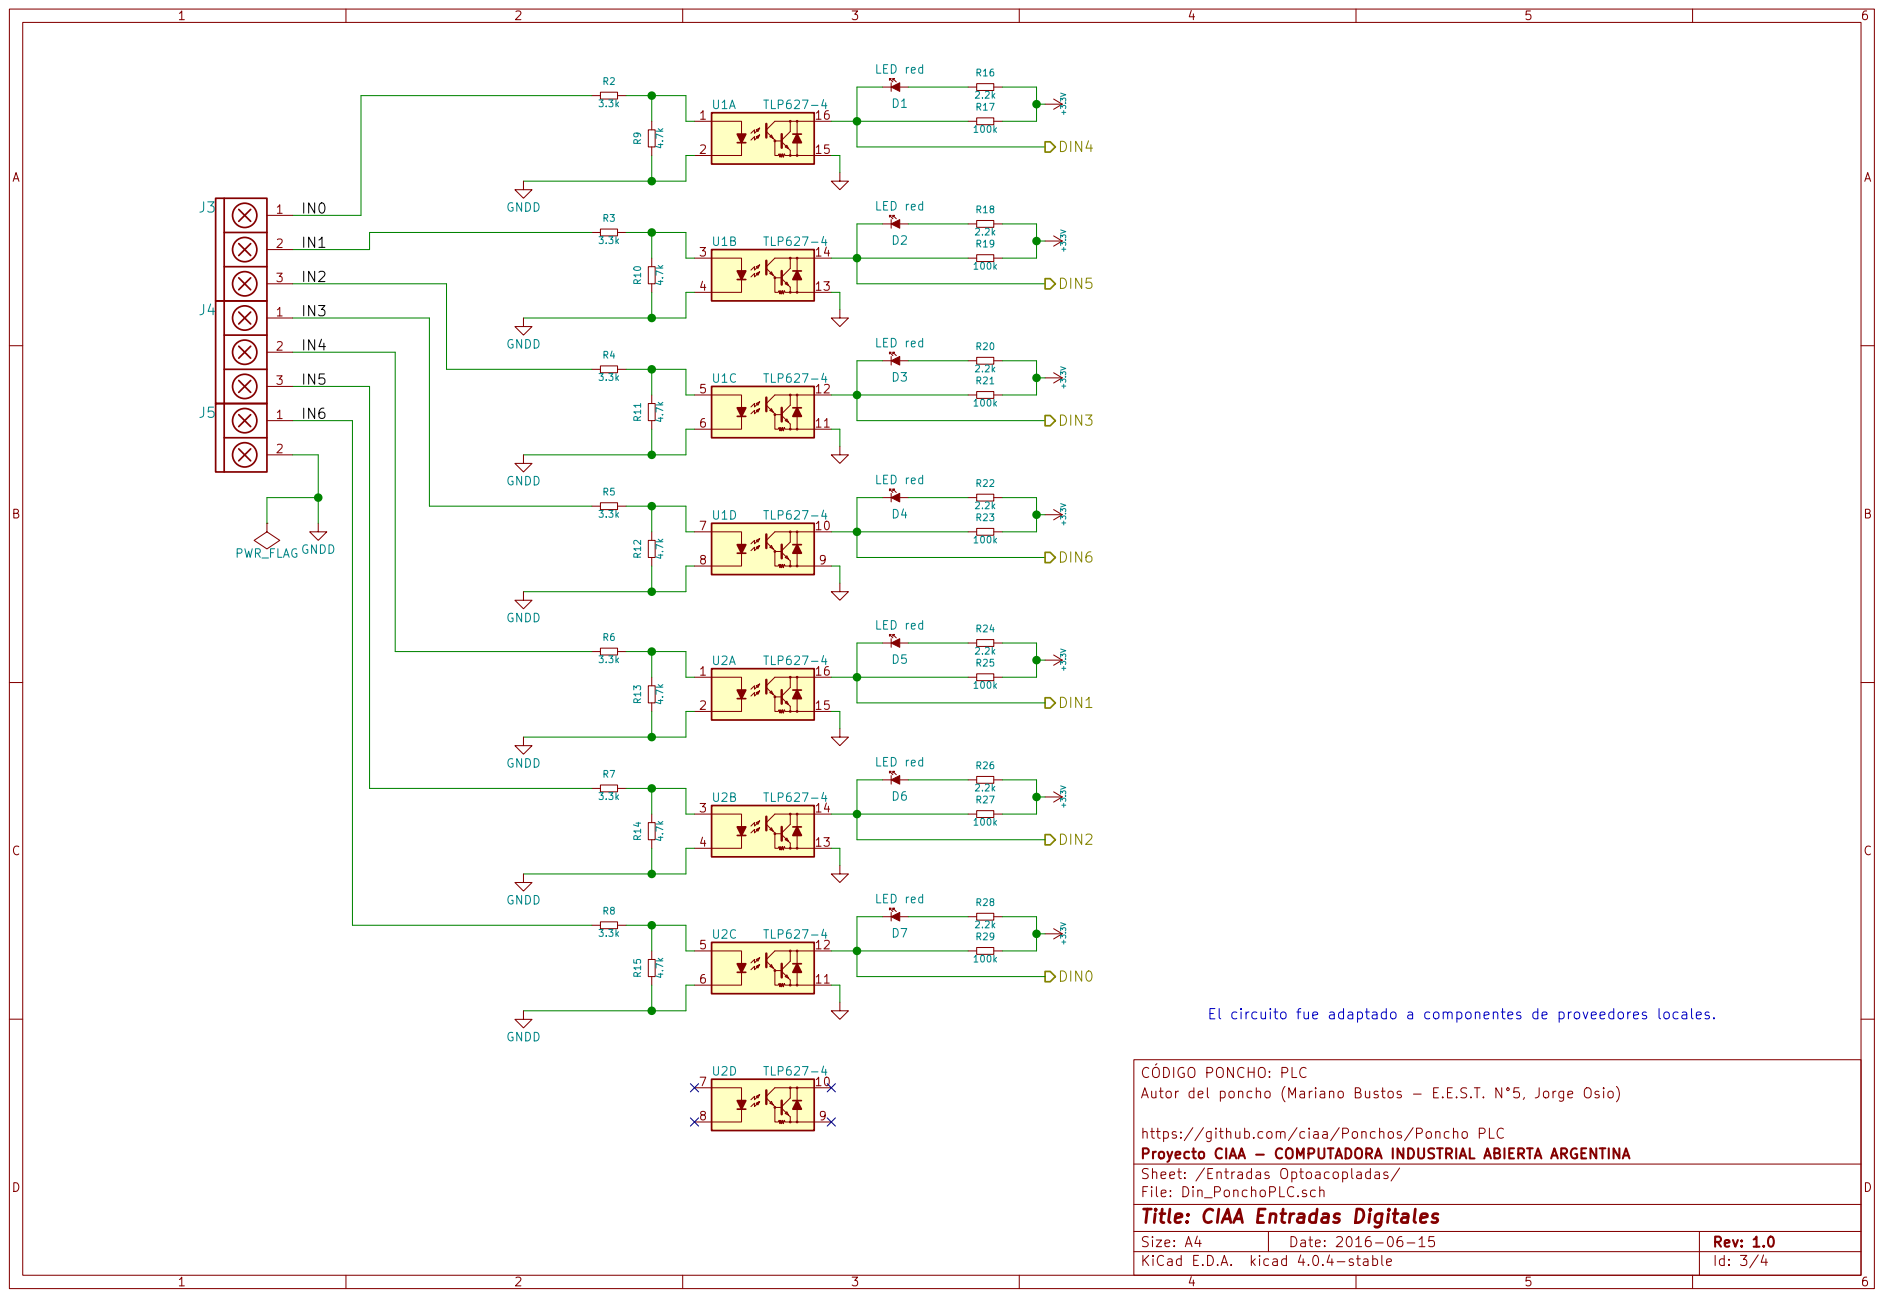
[picture p192: page 3]

CÓDIGO PONCHO: PLC
Autor del poncho (Mariano Bustos - E.E.S.T. N°5, Jorge Osio)

https://github.com/ciaa/Ponchos/Poncho PLC
Proyecto CIAA - COMPUTADORA INDUSTRIAL ABIERTA ARGENTINA
Sheet: /Entradas Optoacopladas/
File: Din_PonchoPLC.sch
Id: 3/4 Title: CIAA Entradas Digitales

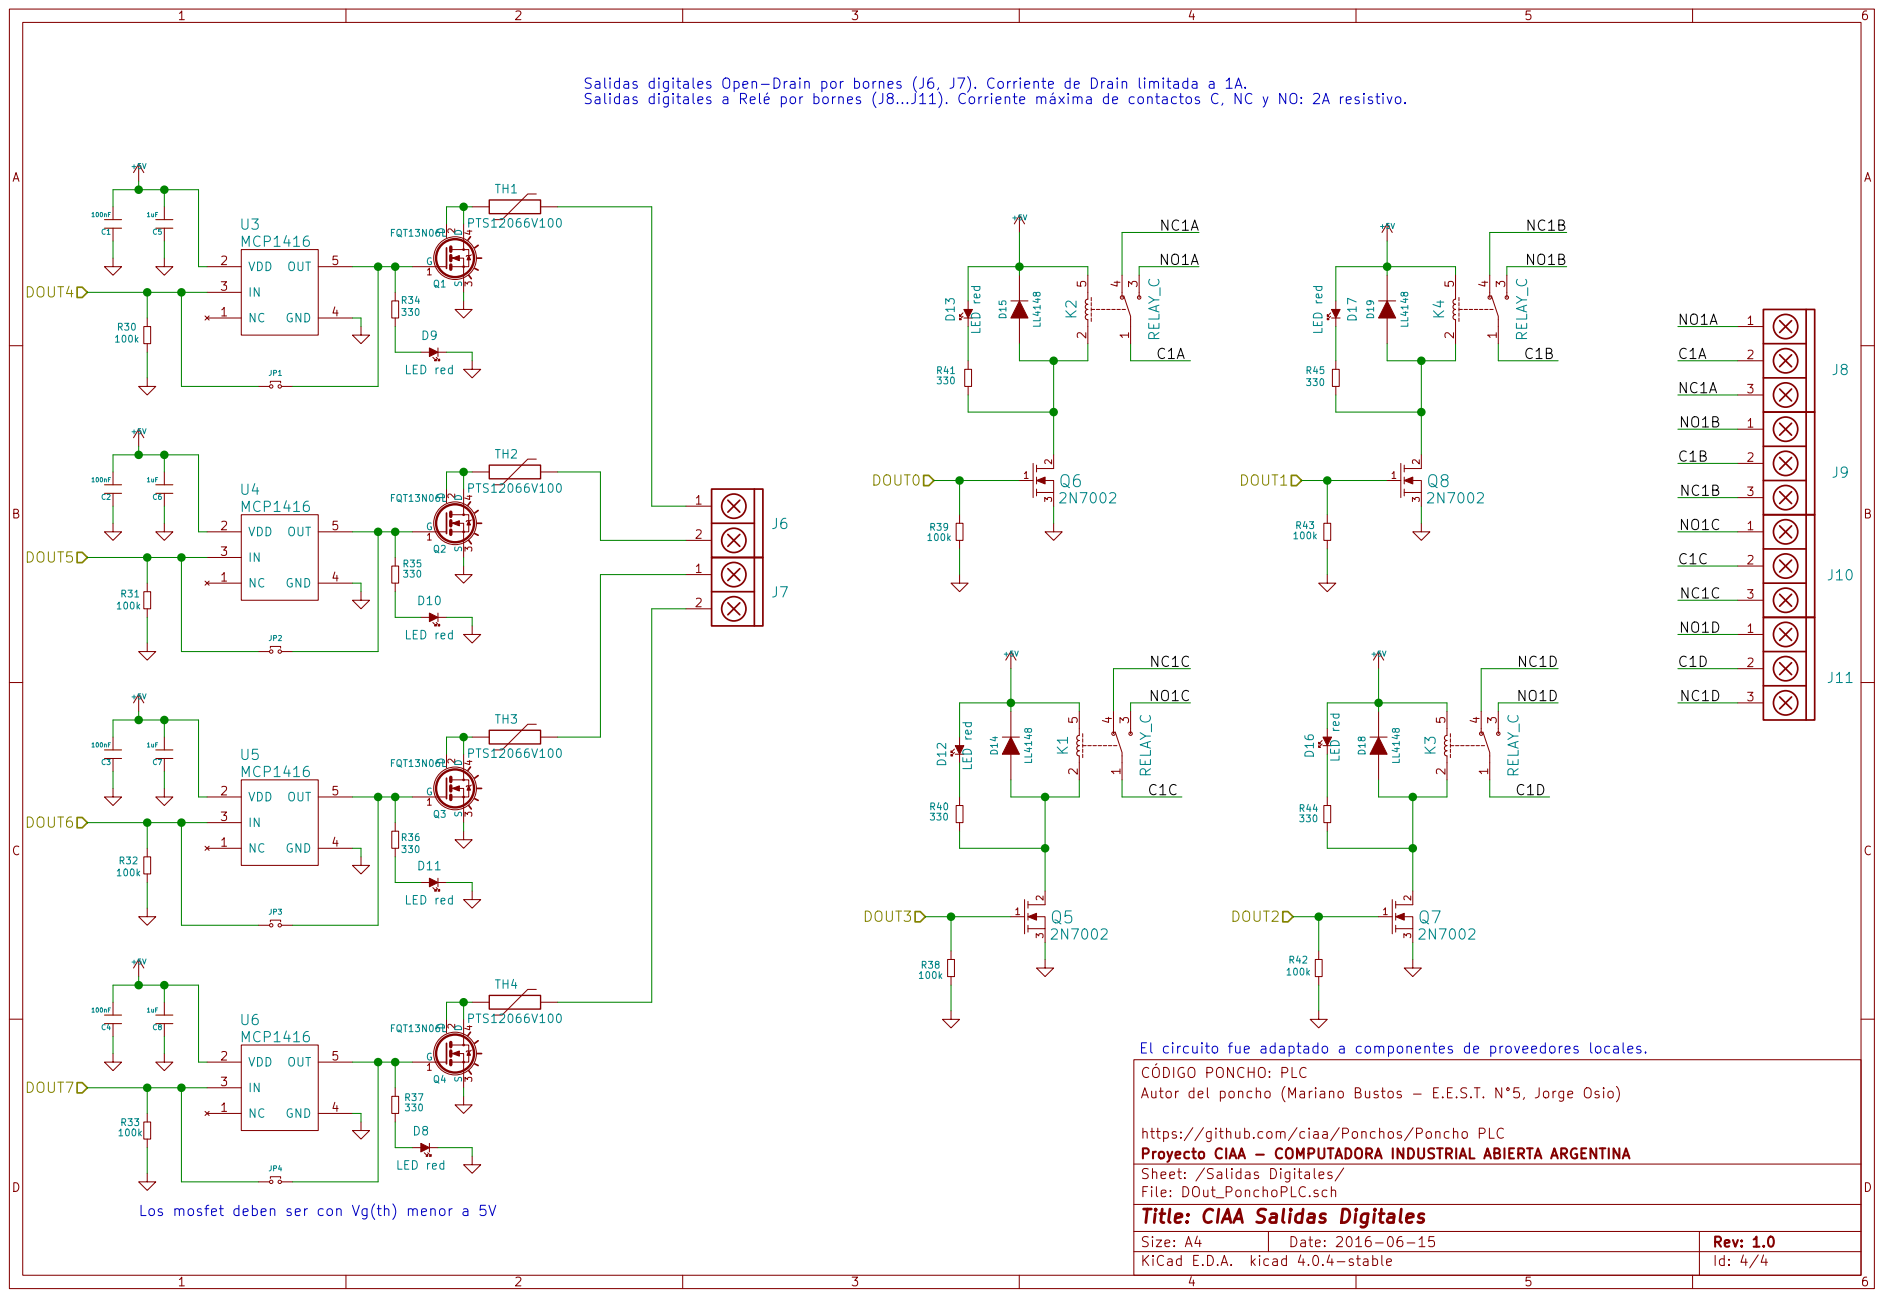
[picture p193: page 4]

Salidas digitales Open-Drain por bornes (J6, J7). Corriente de Drain limitada a 1A.

Salidas digitales a Relé por bornes (J8...J11). Corriente máxima de contactos C, NC y NO: 2A resistivo. R34

El circuito fue adaptado a componentes de proveedores locales.

Autor del poncho (Mariano Bustos - E.E.S.T. N°5, Jorge Osio)

https://github.com/ciaa/Ponchos/Poncho PLC
Proyecto CIAA - COMPUTADORA INDUSTRIAL ABIERTA ARGENTINA
Sheet: /Salidas Digitales/
File: DOut_PonchoPLC.sch
Id: 4/4 Title: CIAA Salidas Digitales

Los mosfet deben ser con Vg(th) menor a 5V
