ciaa/Ponchos/Educativo_UNSJ/pdf/Poncho.pdf

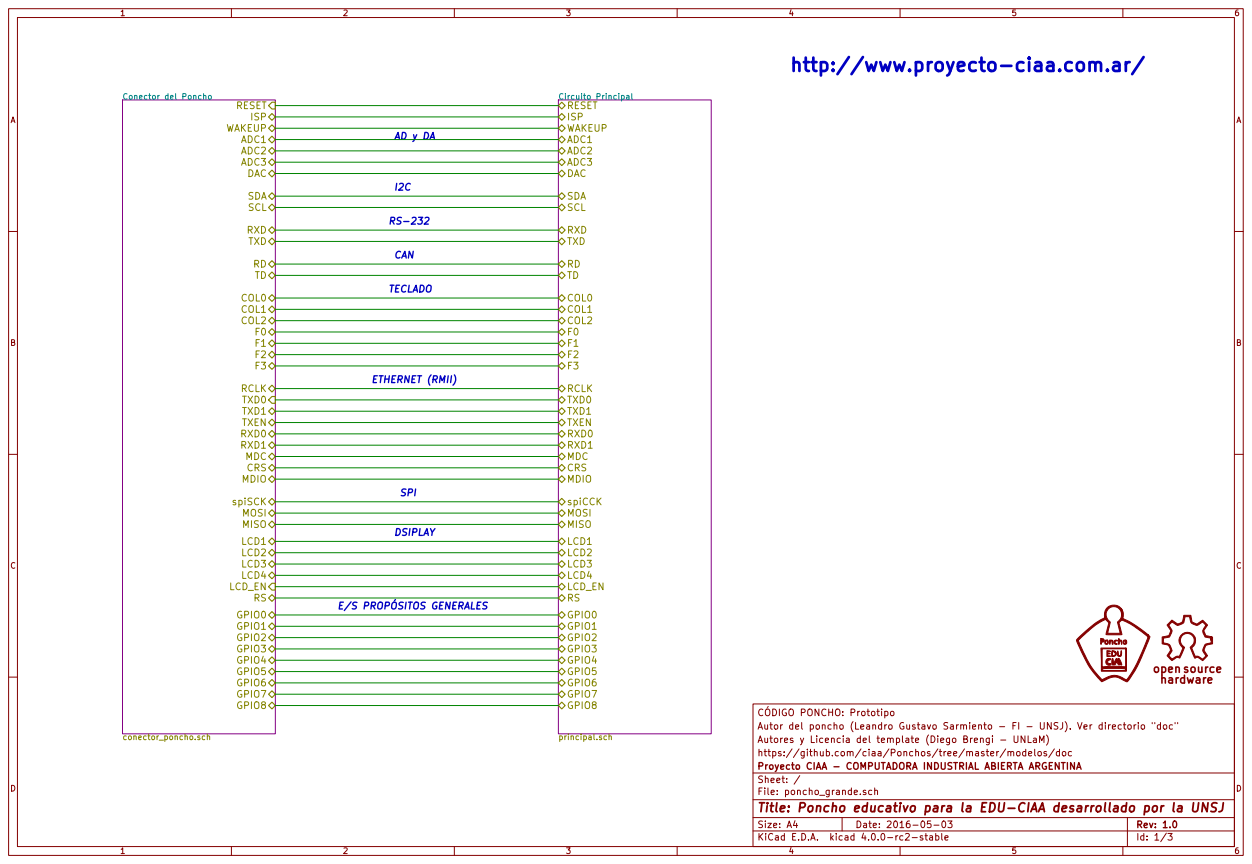
[picture p194: page 1]

http://www.proyecto-ciaa.com.ar/

CÓDIGO PONCHO: Prototipo
Autor del poncho (Leandro Gustavo Sarmiento - FI - UNSJ). Ver directorio "doc"
Autores y Licencia del template (Diego Brengi - UNLaM)
https://github.com/ciaa/Ponchos/tree/master/modelos/doc
File: poncho_grande.sch Sheet: / Proyecto CIAA - COMPUTADORA INDUSTRIAL ABIERTA ARGENTINA

Id: 1/3 Title: Poncho educativo para la EDU-CIAA desarrollado por la UNSJ

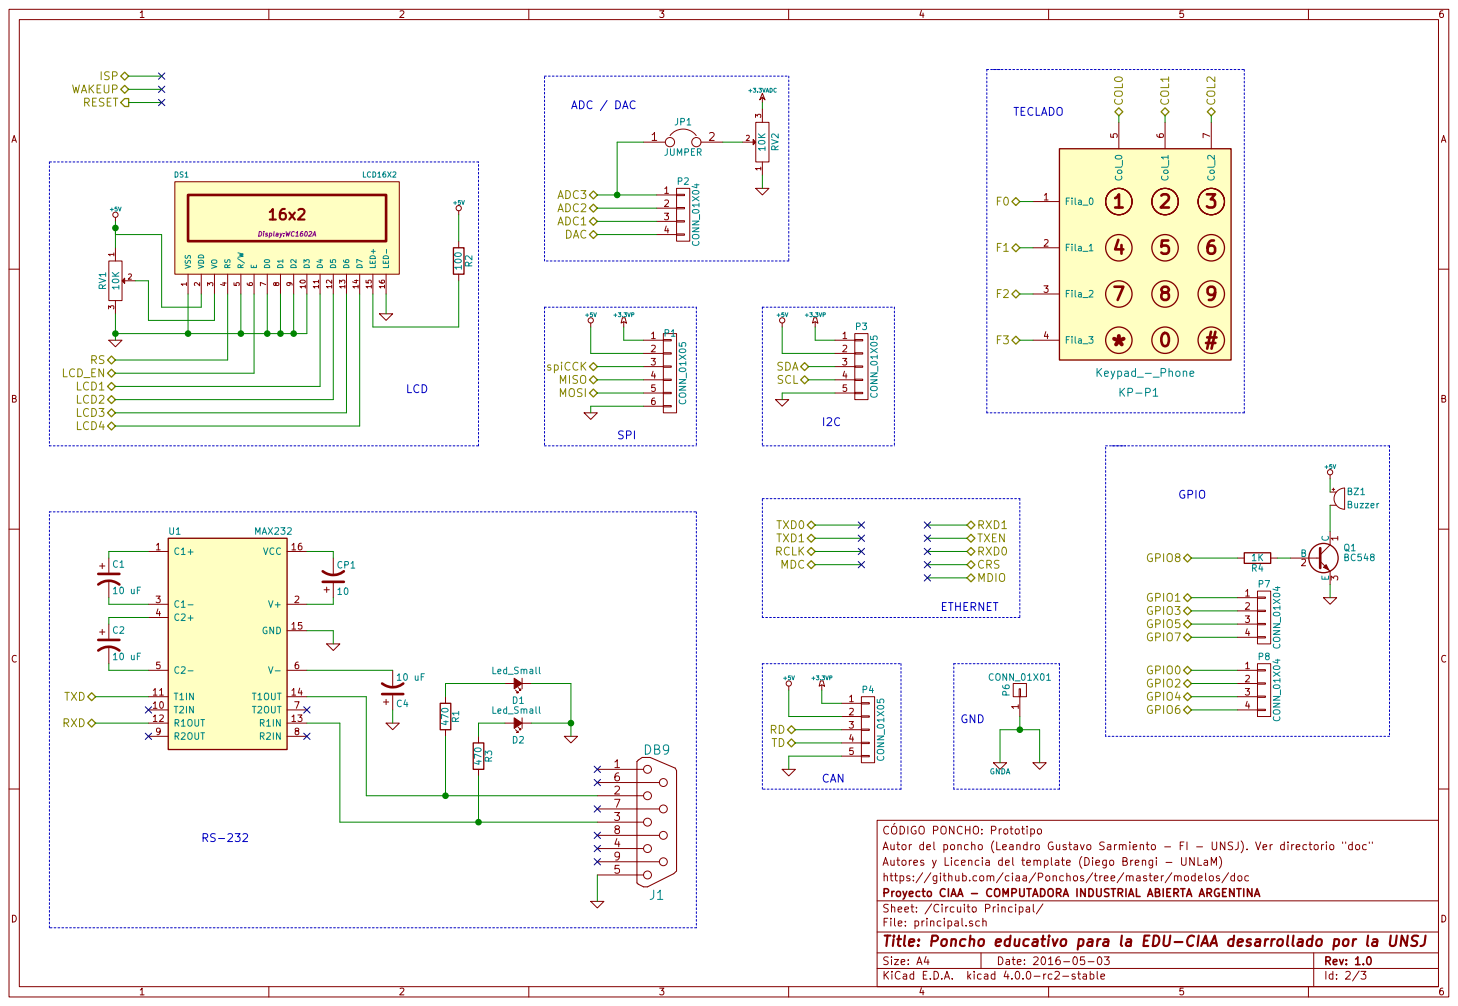
[picture p195: page 2]

CÓDIGO PONCHO: Prototipo
Autor del poncho (Leandro Gustavo Sarmiento - FI - UNSJ). Ver directorio "doc"
Autores y Licencia del template (Diego Brengi - UNLaM)
https://github.com/ciaa/Ponchos/tree/master/modelos/doc
Proyecto CIAA - COMPUTADORA INDUSTRIAL ABIERTA ARGENTINA
Sheet: /Circuito Principal/
File: principal.sch
Id: 2/3 Title: Poncho educativo para la EDU-CIAA desarrollado por la UNSJ

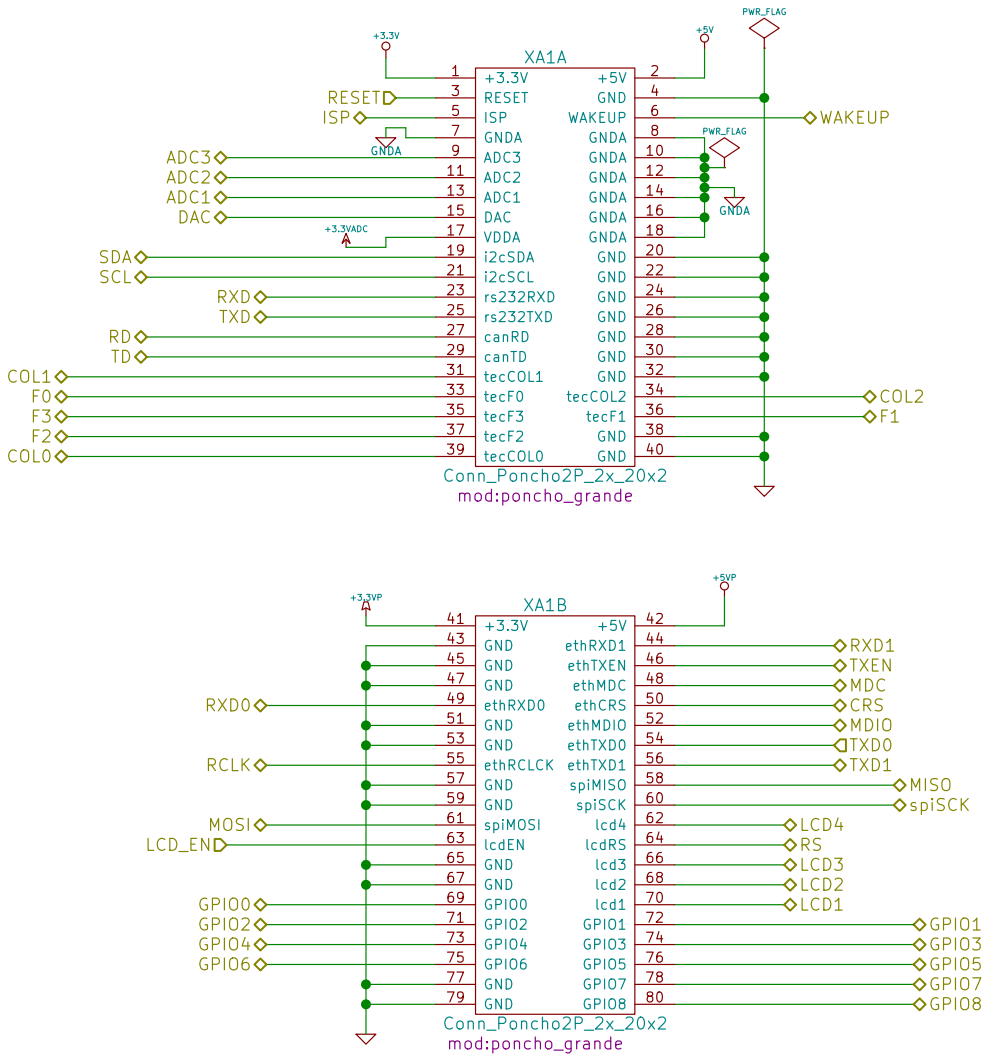
[picture p196: page 3]

CÓDIGO PONCHO: Prototipo
Autor del poncho (Leandro Gustavo Sarmiento - FI - UNSJ). Ver directorio "doc"
Autores y Licencia del template (Diego Brengi - UNLaM)
https://github.com/ciaa/Ponchos/tree/master/modelos/doc
File: conector_poncho.sch Sheet: /Conector del Poncho/ Proyecto CIAA - COMPUTADORA INDUSTRIAL ABIERTA ARGENTINA

Id: 3/3 Title: Poncho educativo para la EDU-CIAA desarrollado por la UNSJ
