ciaa/Ponchos/Mision_SAE/doc/BMP085 Breakout-v11.pdf

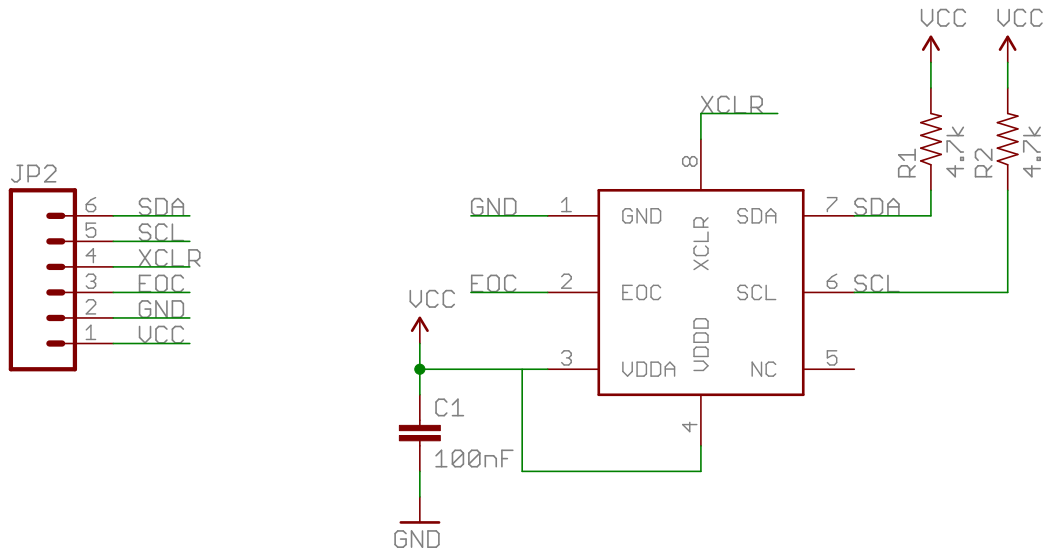
[picture p197: page 1]
