ciaa/Ponchos/Mision_SAE/doc/Triple_Axis_Accelerometer-Gyro_Breakout_-_MPU-6050_v12.pdf

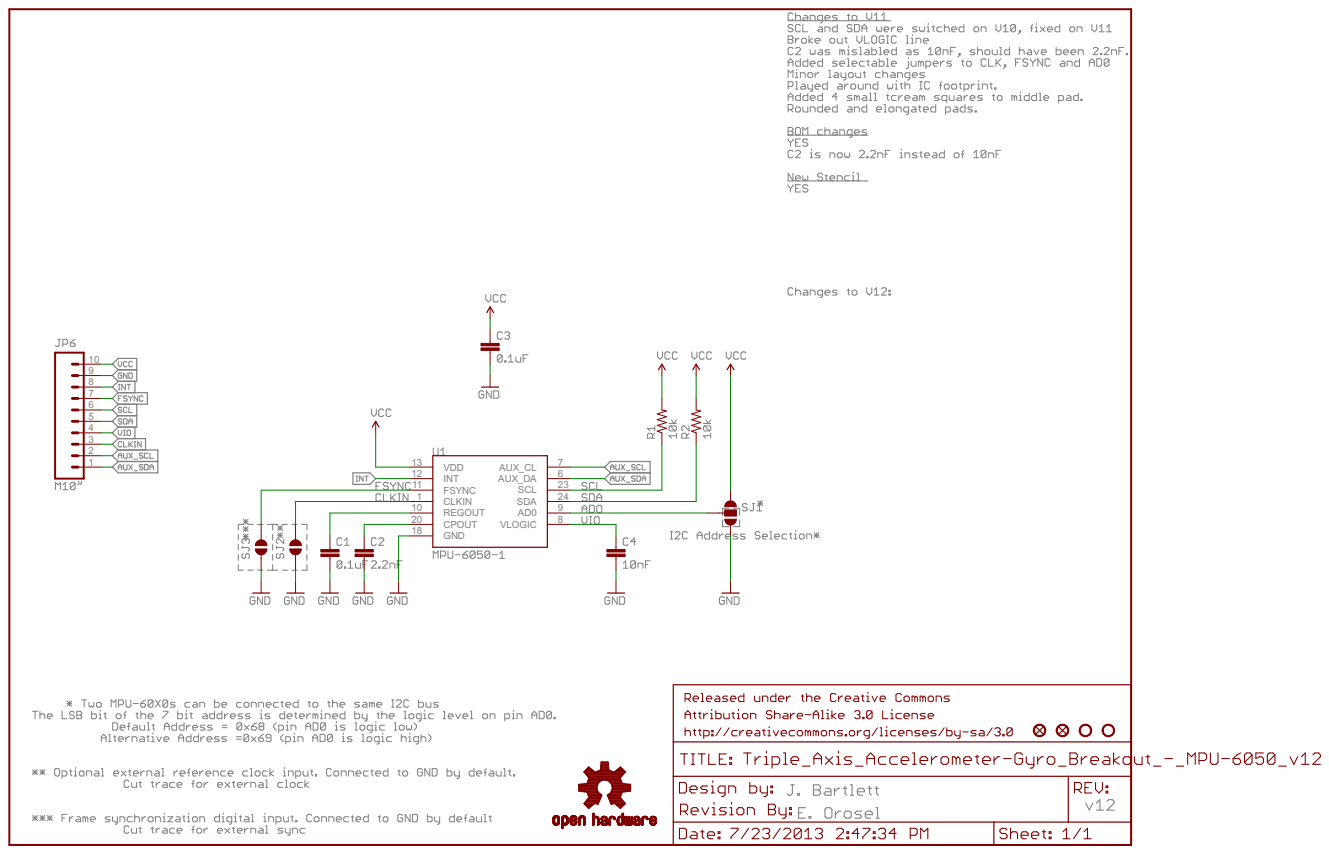
[picture p198: page 1]
