ciaa/Ponchos/Pico_WiFi/HOJAS_DE_DATOS_Y_NOTAS/PICOCIAA/squema_Adap.pdf

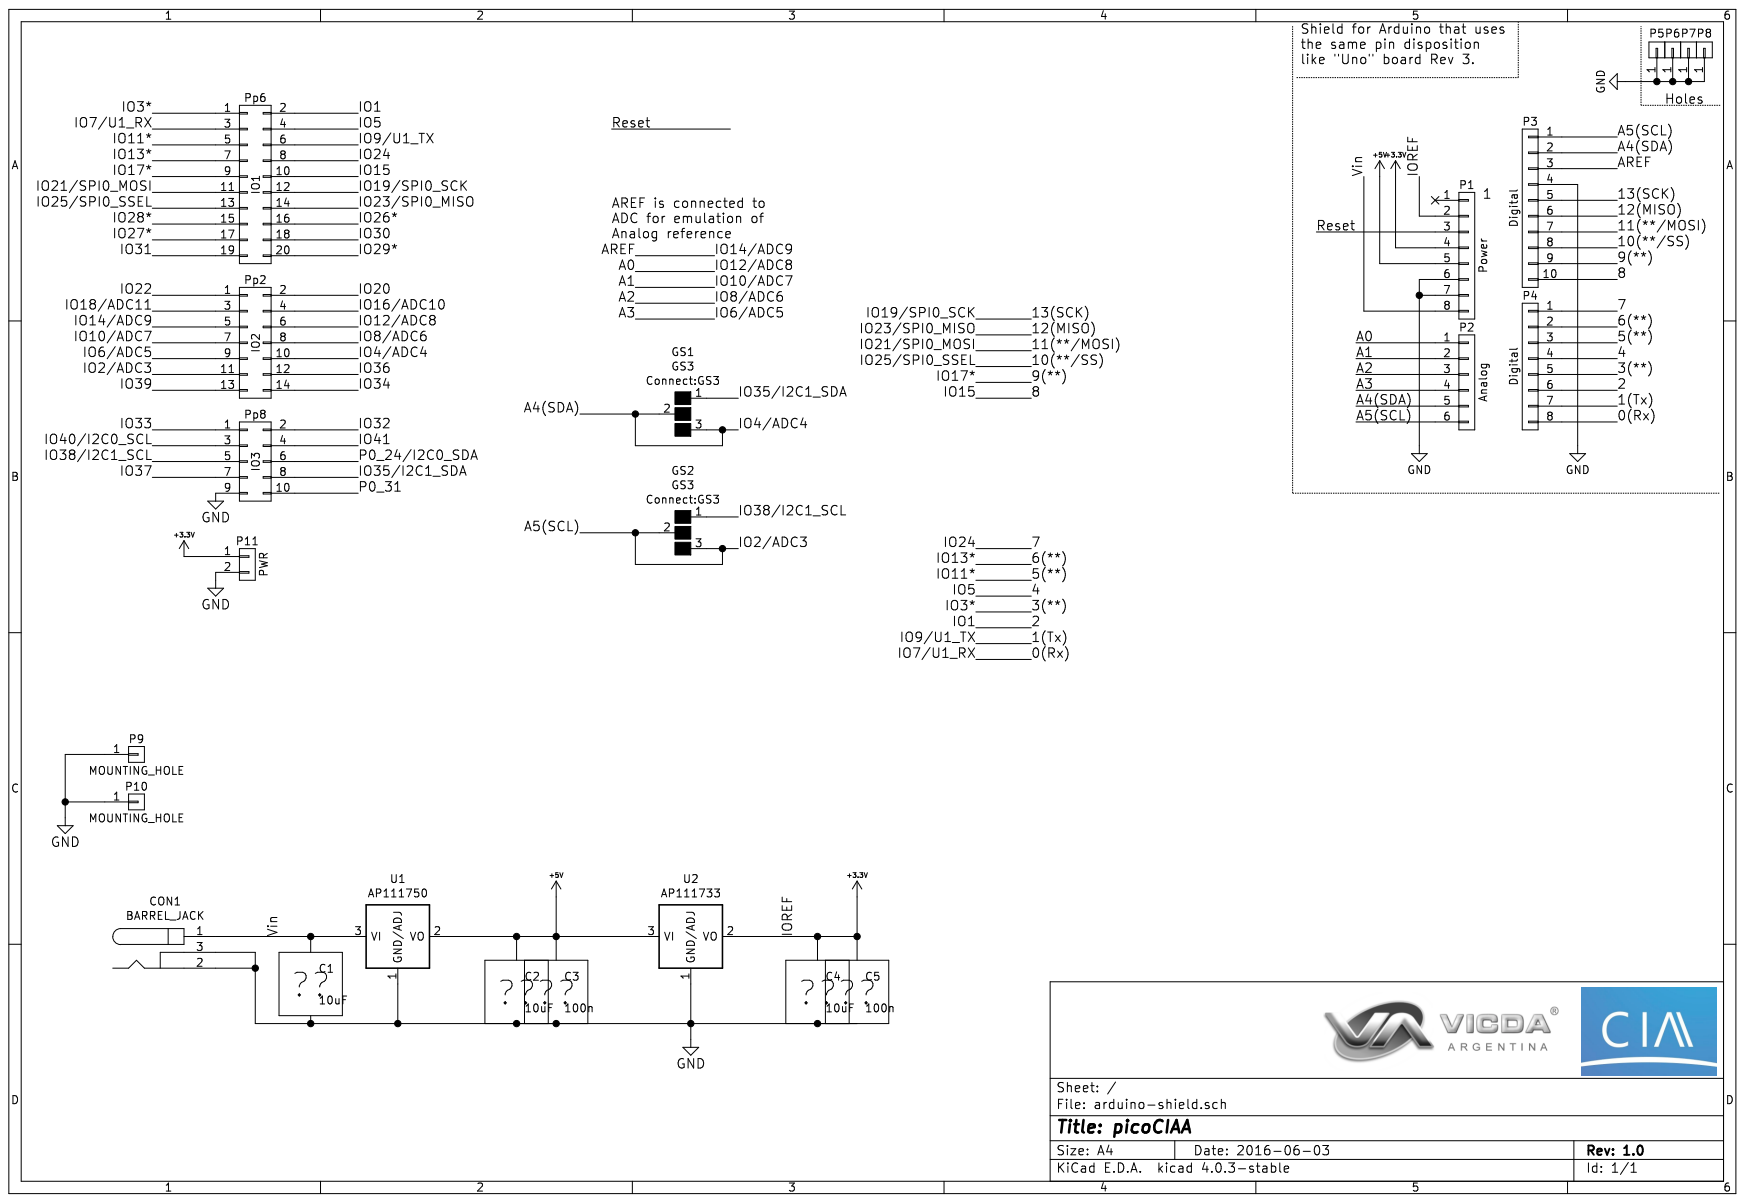
[picture p199: page 1]
