ciaa/Ponchos/ECG/Documetacion/Otros desarrollos similares/AD8232_Heart_Rate_Monitor_v10.pdf

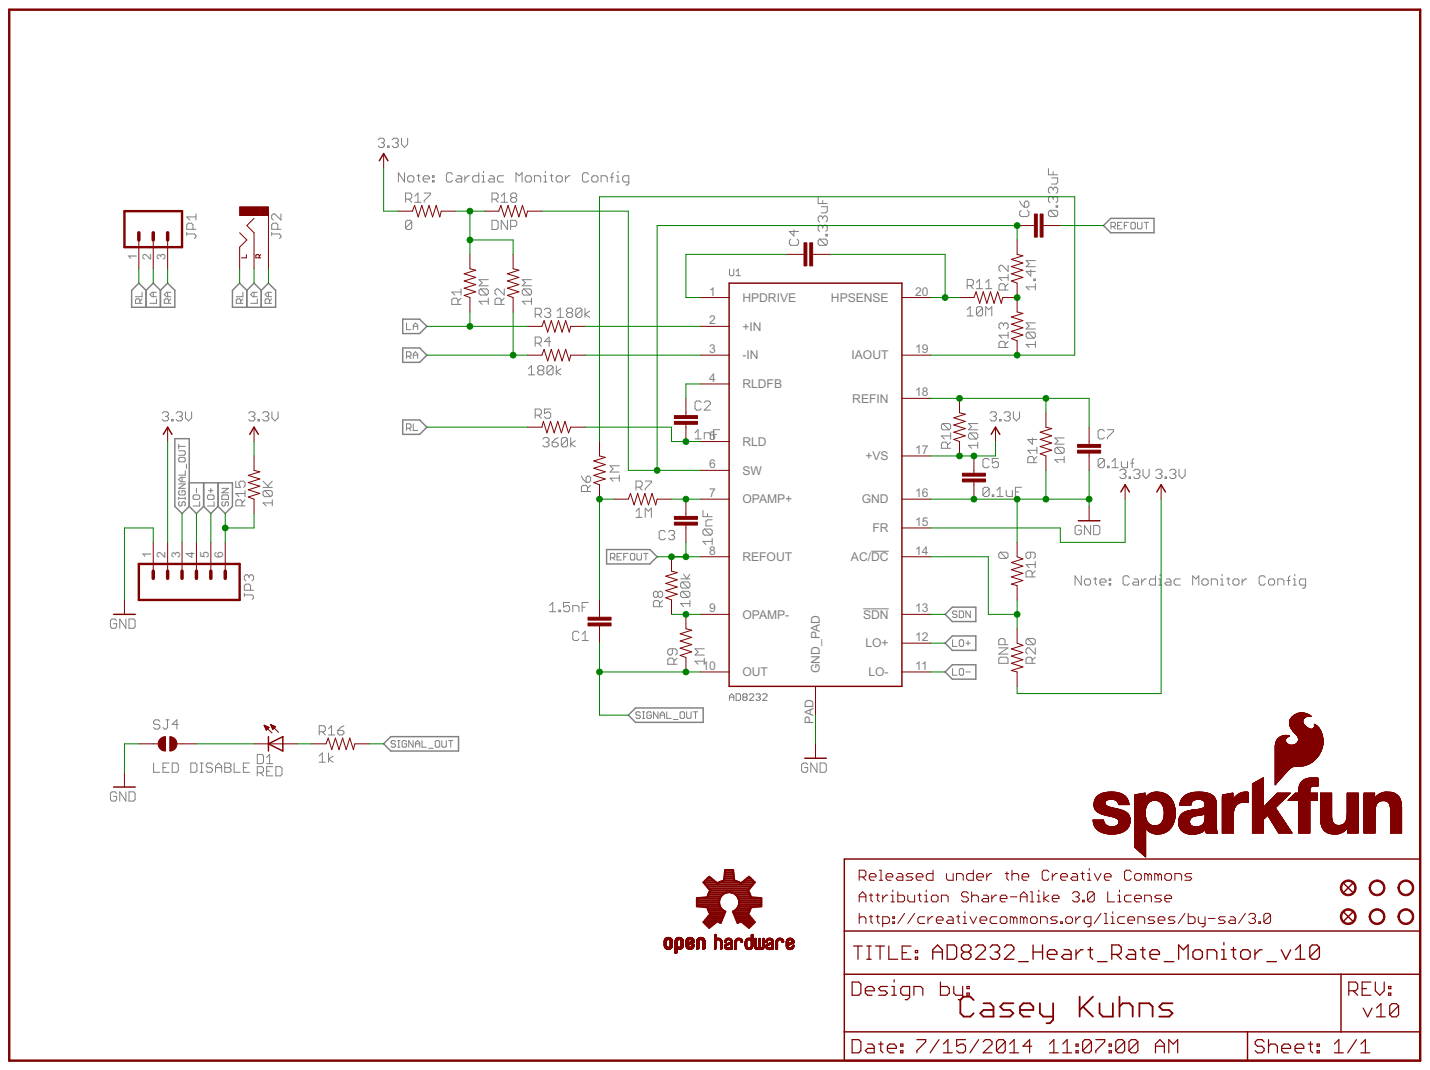
[picture p200: page 1]
