ciaa/Ponchos/Simon/gerber/pdf/simonShield-B.Cu.pdf

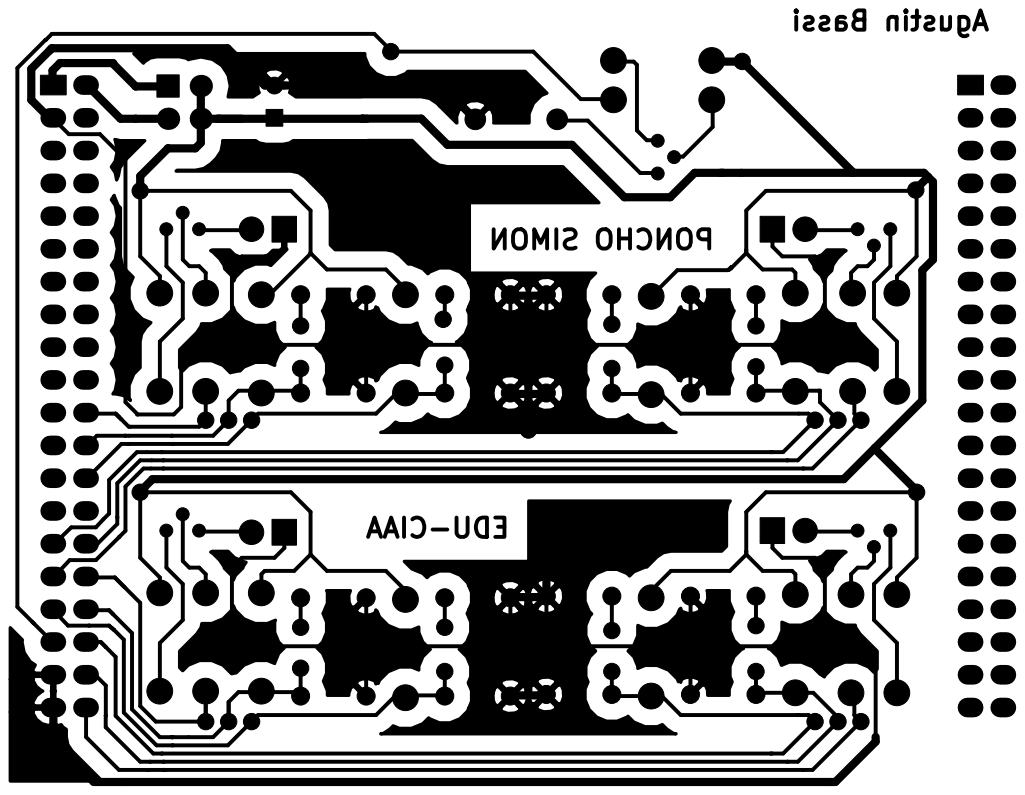
[picture p201: page 1]

Agustin Bassi EDU-CIAA
