ciaa/Ponchos/Simon/gerber/pdf/simonShield-F.Cu.pdf

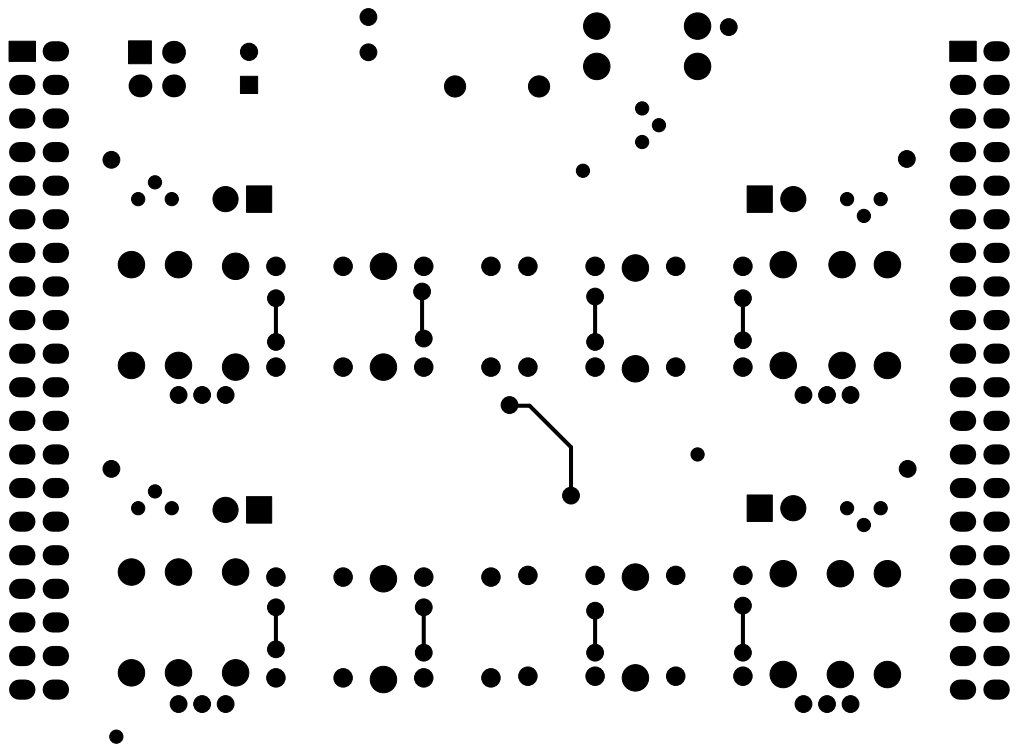
[picture p202: page 1]
