ciaa/Ponchos/Osciloscopio/doc/Circuitos de osciloscopios simples/small-scope.pdf

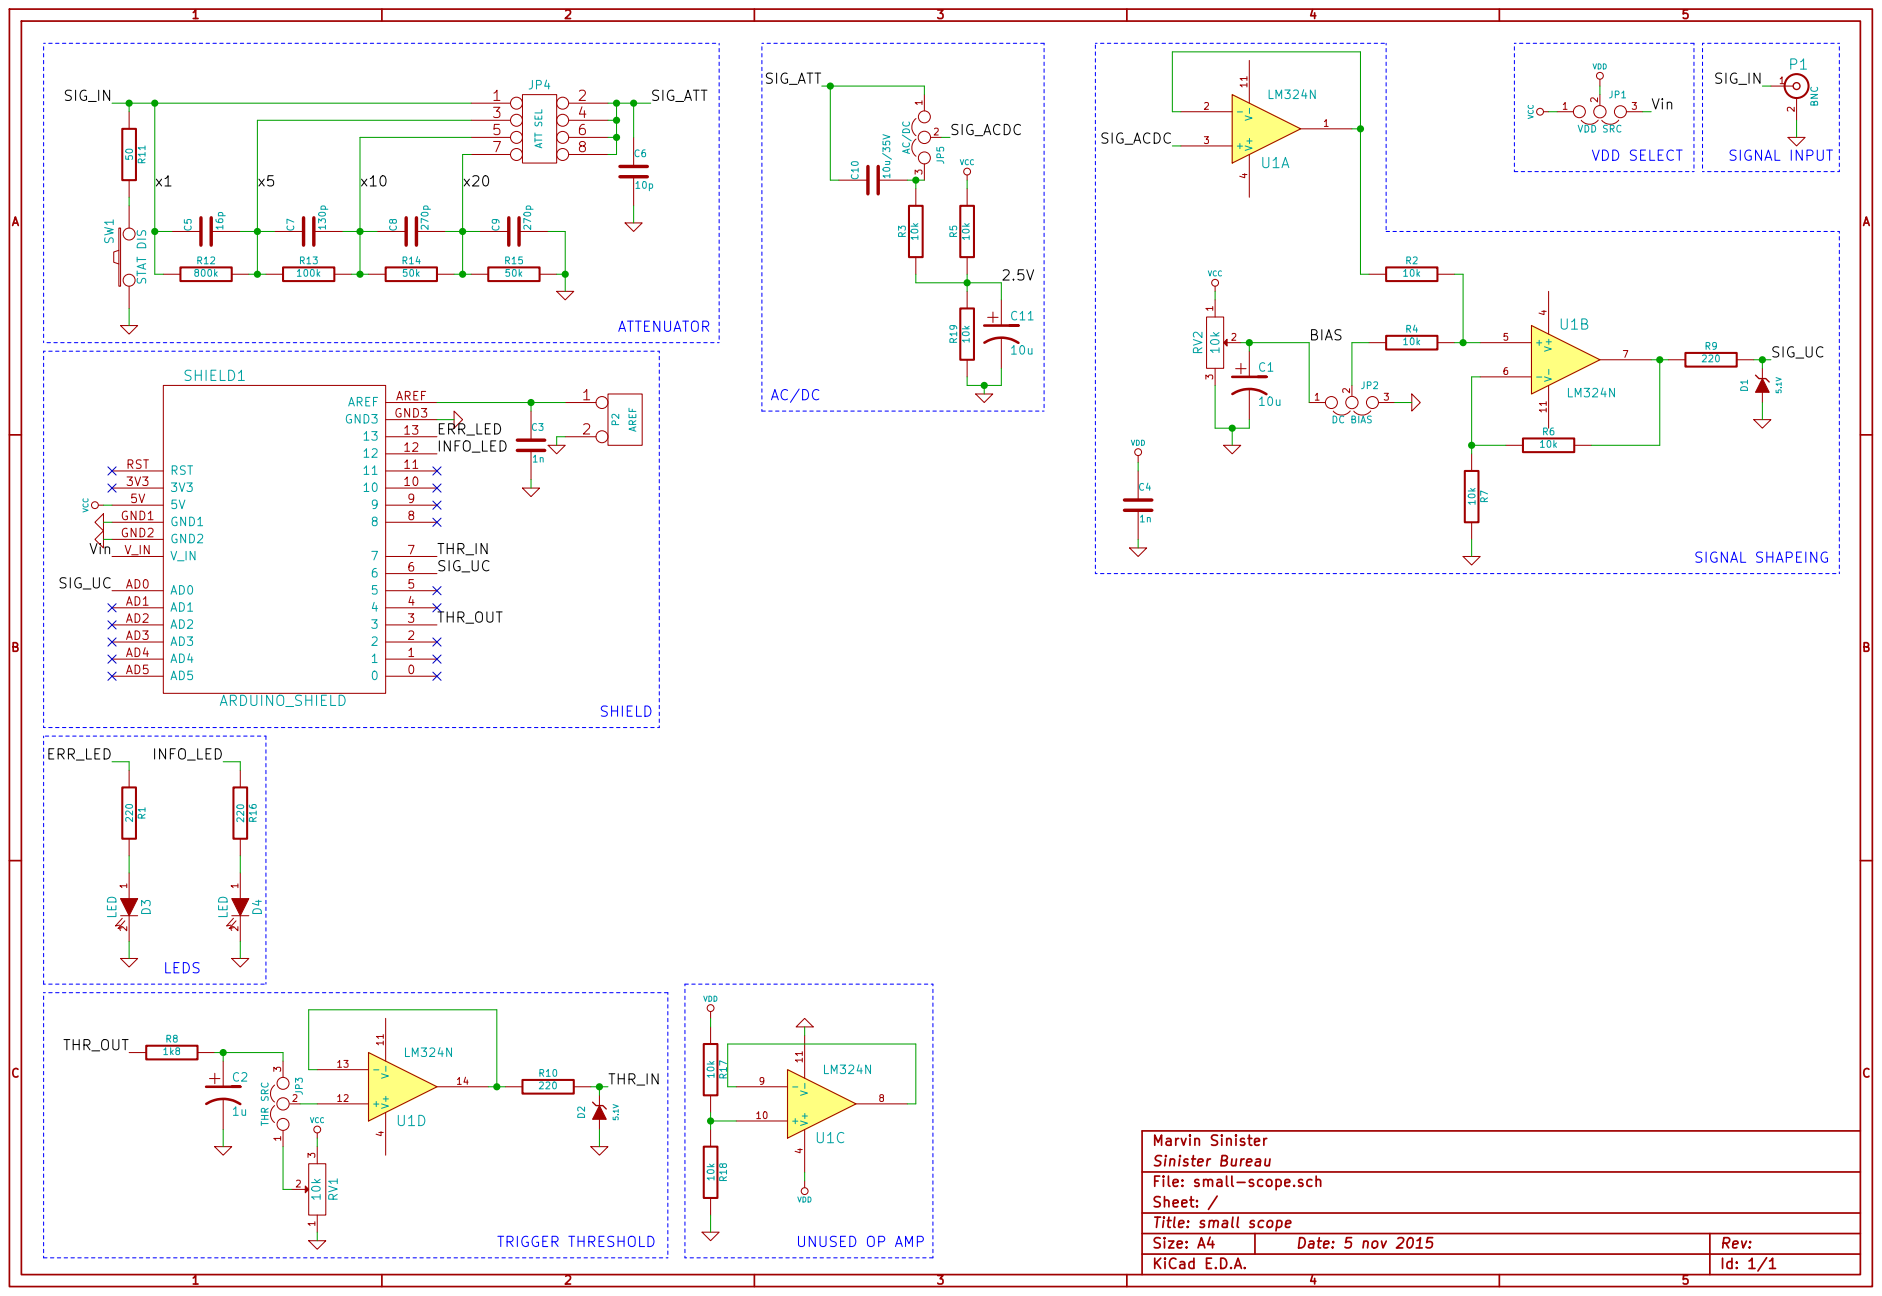
[picture p203: page 1]

Sinister Bureau
File: small-scope.sch
Sheet: /
Title: small scope
