ciaa/Ponchos/Sumo_Robot/PonchoSumoRobot.kicad_pcb

## KiCad design Sumo_Robot/PonchoSumoRobot.kicad_pcb (2017-01-11)

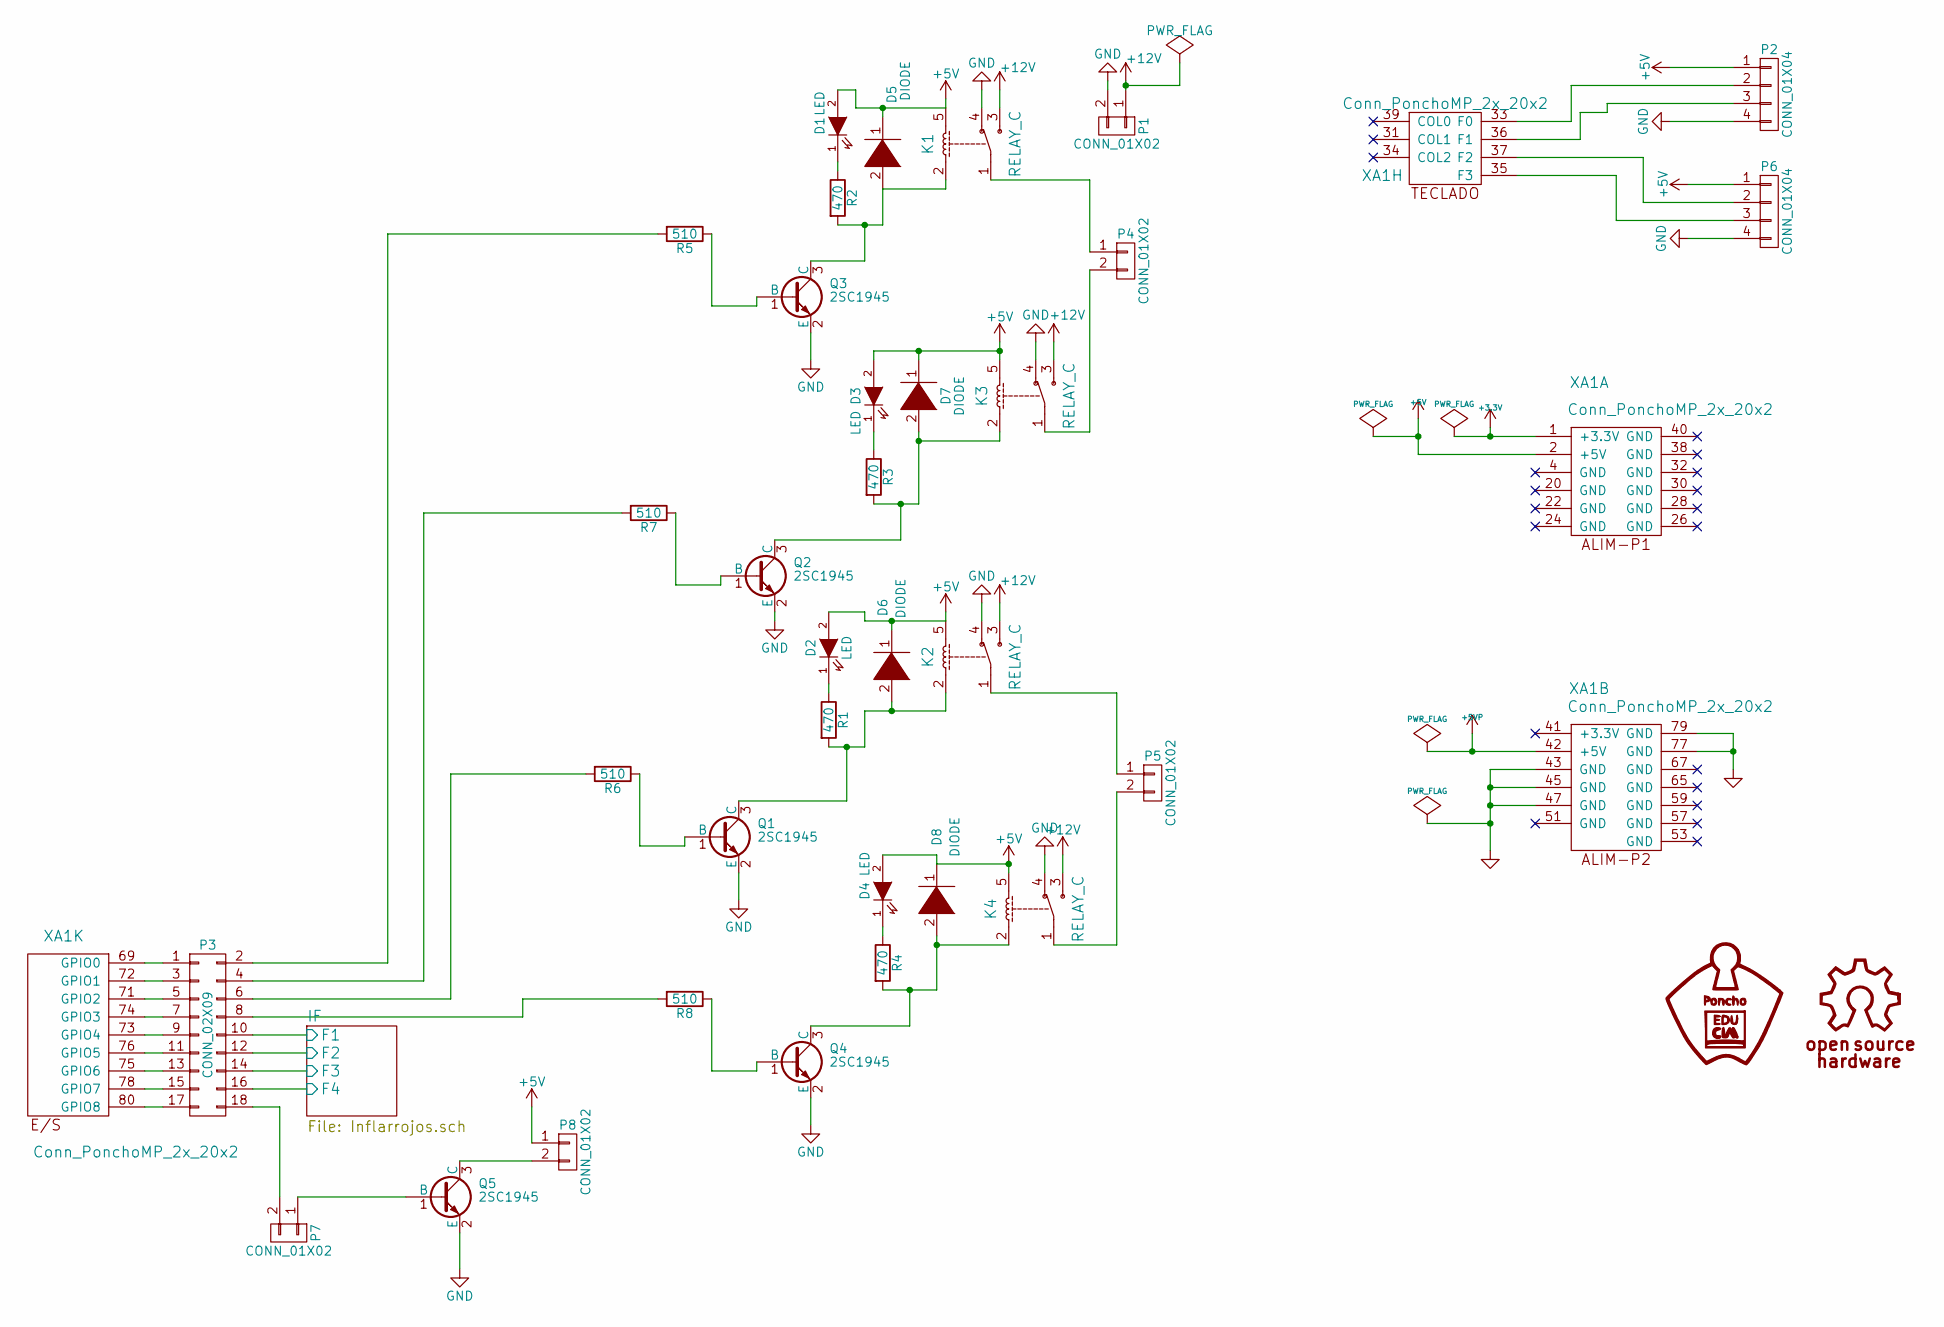
[picture p228: schematic PonchoSumoRobot.sch, Poncho Sumo Robot]

Parts:
D1, D2, D3, D4: LED; LED-3MM
D5, D6, D7, D8: DIODE; Diode_DO-41_SOD81_Horizontal_RM10
K1, K2, K3, K4: RELAY_C; Relay_SANYOU_SRD_Series_Form_C
P1, P4, P5: CONN_01X02; bornier2
P2, P6: CONN_01X04; Pin_Header_Straight_1x04
P3: CONN_02X09; Pin_Header_Straight_2x09
P7, P8: CONN_01X02; Pin_Header_Straight_1x02
Q1, Q2, Q3, Q4, Q5: 2SC1945; TO-220
R1, R2, R3, R4: 470; Resistor_Horizontal_RM7m
R5, R6, R7, R8: 510; Resistor_Horizontal_RM7m
XA1: Conn_PonchoMP_2x_20x2; Conn_Poncho_SinBorde

Connections:
+5V: D1.2 (A), D2.2 (A), D3.2 (A), D4.2 (A), D5.1 (K), D6.1 (K), D7.1 (K), D8.1 (K), K1.5, K2.5, K3.5, K4.5, P2.1, P6.1, P8.1, XA1.2 (+5V); also elsewhere on the board
+12V: K1.3, K2.3, K3.3, K4.3, P1.1
/IF/F1: P3.10; also elsewhere on the board
/IF/F2: P3.12; also elsewhere on the board
/IF/F3: P3.14; also elsewhere on the board
/IF/F4: P3.16; also elsewhere on the board
GND: K1.4, K2.4, K3.4, K4.4, P1.2, P2.4, P6.4, Q1.2 (E), Q2.2 (E), Q3.2 (E), Q4.2 (E), Q5.2 (E), XA1.43 (GND), XA1.45 (GND), XA1.47 (GND), XA1.77 (GND), XA1.79 (GND); also elsewhere on the board
unnamed: D1.1 (K), R2.1
unnamed: D2.1 (K), R1.1
unnamed: D3.1 (K), R3.1
unnamed: D4.1 (K), R4.1
unnamed: D5.2 (A), K1.2, Q3.3 (C), R2.2
unnamed: D6.2 (A), K2.2, Q1.3 (C), R1.2
unnamed: D7.2 (A), K3.2, Q2.3 (C), R3.2
unnamed: D8.2 (A), K4.2, Q4.3 (C), R4.2
unnamed: K1.1, P4.1
unnamed: K2.1, P5.1
unnamed: K3.1, P4.2
unnamed: K4.1, P5.2
unnamed: P2.2, XA1.33 (F0)
unnamed: P2.3, XA1.36 (F1)
unnamed: P3.1, XA1.69 (GPIO0)
unnamed: P3.2, R5.2
unnamed: P3.3, XA1.72 (GPIO1)
unnamed: P3.4, R7.2
unnamed: P3.5, XA1.71 (GPIO2)
unnamed: P3.6, R6.2
unnamed: P3.7, XA1.74 (GPIO3)
unnamed: P3.8, R8.2
unnamed: P3.9, XA1.73 (GPIO4)
unnamed: P3.11, XA1.76 (GPIO5)
unnamed: P3.13, XA1.75 (GPIO6)
unnamed: P3.15, XA1.78 (GPIO7)
unnamed: P3.17, XA1.80 (GPIO8)
unnamed: P3.18, P7.2
unnamed: P6.2, XA1.37 (F2)
unnamed: P6.3, XA1.35 (F3)
unnamed: P7.1, Q5.1 (B)
unnamed: P8.2, Q5.3 (C)
unnamed: Q1.1 (B), R6.1
unnamed: Q2.1 (B), R7.1
unnamed: Q3.1 (B), R5.1
unnamed: Q4.1 (B), R8.1

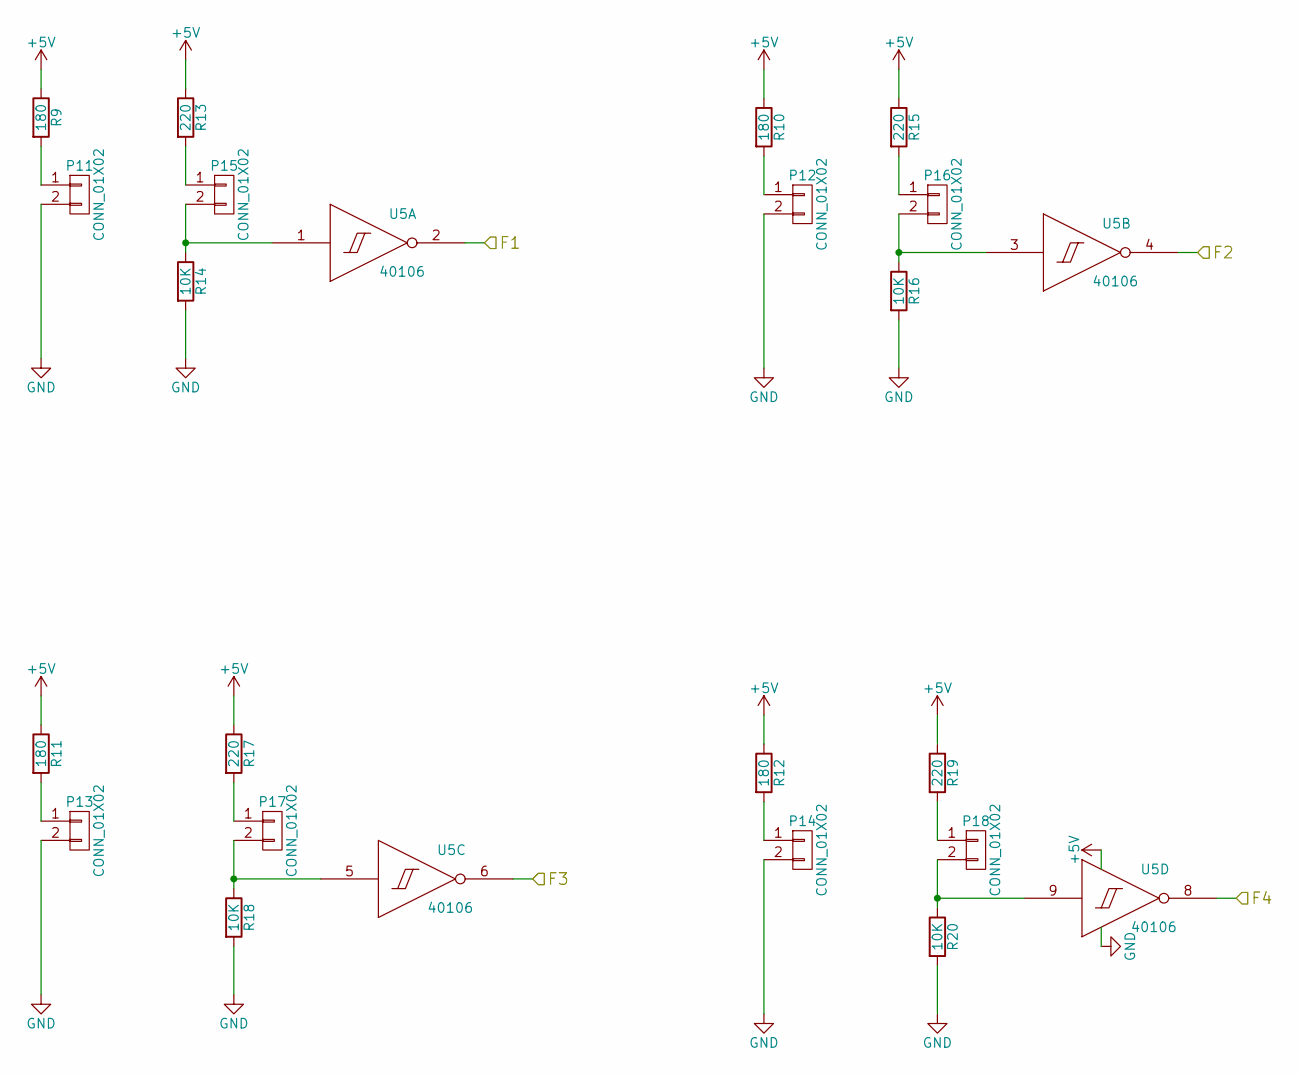
[picture p229: schematic Inflarrojos.sch, Poncho Sumo Robot - Sensores infrarrojos]

Parts:
P11, P12, P13, P14, P15, P16, P17, P18: CONN_01X02; Pin_Header_Straight_1x02
R9, R10, R11, R12: 180; Resistor_Horizontal_RM7m
R13, R15, R17, R19: 220; Resistor_Horizontal_RM7m
R14, R16, R18, R20: 10K; Resistor_Horizontal_RM7m
U5: 40106; 40xx-DIL14

Connections:
+5V: R9.1, R10.1, R11.1, R12.1, R13.1, R15.1, R17.1, R19.1, U5.14 (VDD); also elsewhere on the board
/IF/F1: U5.2 (Out); also elsewhere on the board
/IF/F2: U5.4 (Out); also elsewhere on the board
/IF/F3: U5.6 (Out); also elsewhere on the board
/IF/F4: U5.8 (Out); also elsewhere on the board
GND: P11.2, P12.2, P13.2, P14.2, R14.2, R16.2, R18.2, R20.2, U5.7 (VSS); also elsewhere on the board
unnamed: P11.1, R9.2
unnamed: P12.1, R10.2
unnamed: P13.1, R11.2
unnamed: P14.1, R12.2
unnamed: P15.1, R13.2
unnamed: P15.2, R14.1, U5.1 (In)
unnamed: P16.1, R15.2
unnamed: P16.2, R16.1, U5.3 (In)
unnamed: P17.1, R17.2
unnamed: P17.2, R18.1, U5.5 (In)
unnamed: P18.1, R19.2
unnamed: P18.2, R20.1, U5.9 (In)
