ciaa/Ponchos/Sumo_Robot/PonchoSumoRobot.kicad_pcb

## KiCad design Sumo_Robot/PonchoSumoRobot.kicad_pcb (continued)

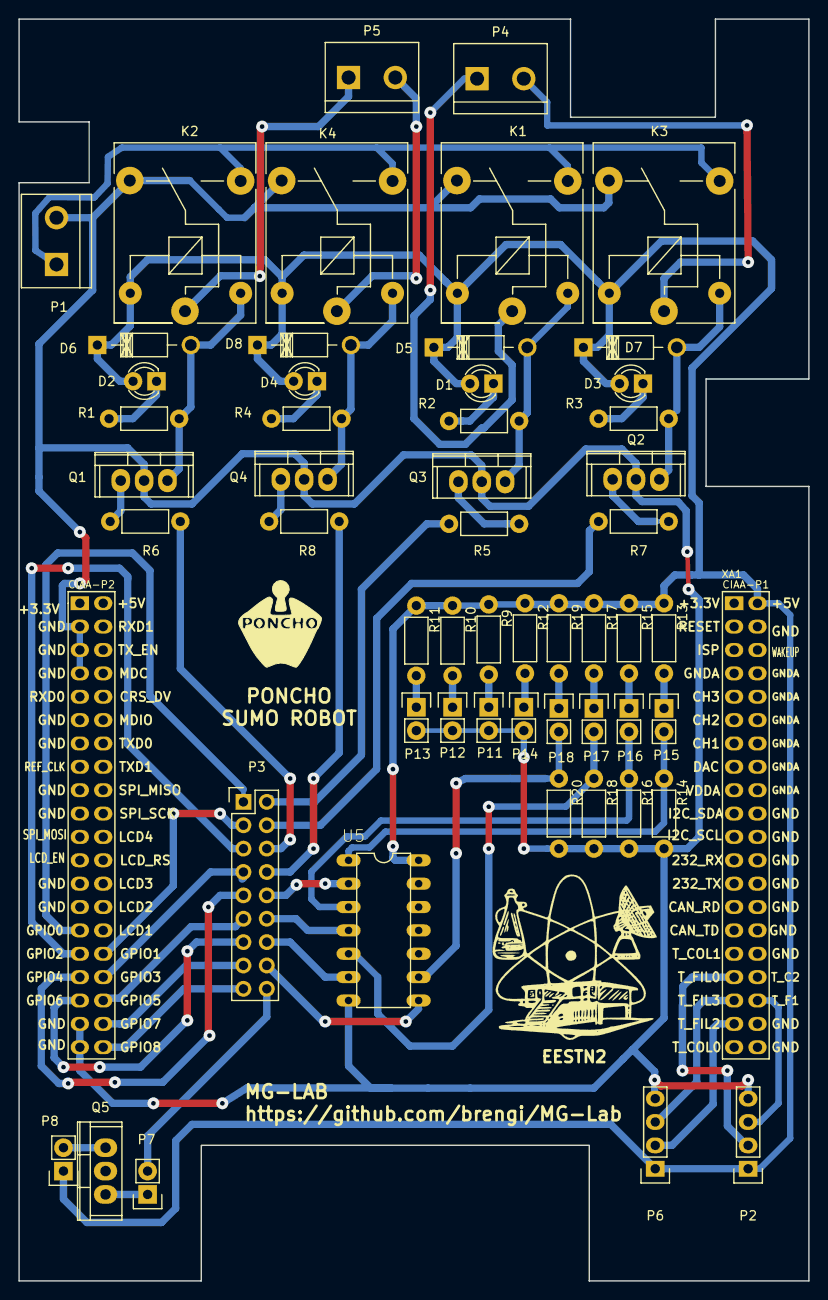
[picture p230: board PonchoSumoRobot.kicad_pcb from above]

Board: 2 copper layers, 85.9 x 137.2 mm, 56 parts (0 on the bottom side), 55 nets.

Other parts of the board:
EESTN2: EESTN2; LOGO1
