ciaa/Ponchos/Oximetro/TP.kicad_pcb

## KiCad design Oximetro/TP.kicad_pcb (2017-01-10)

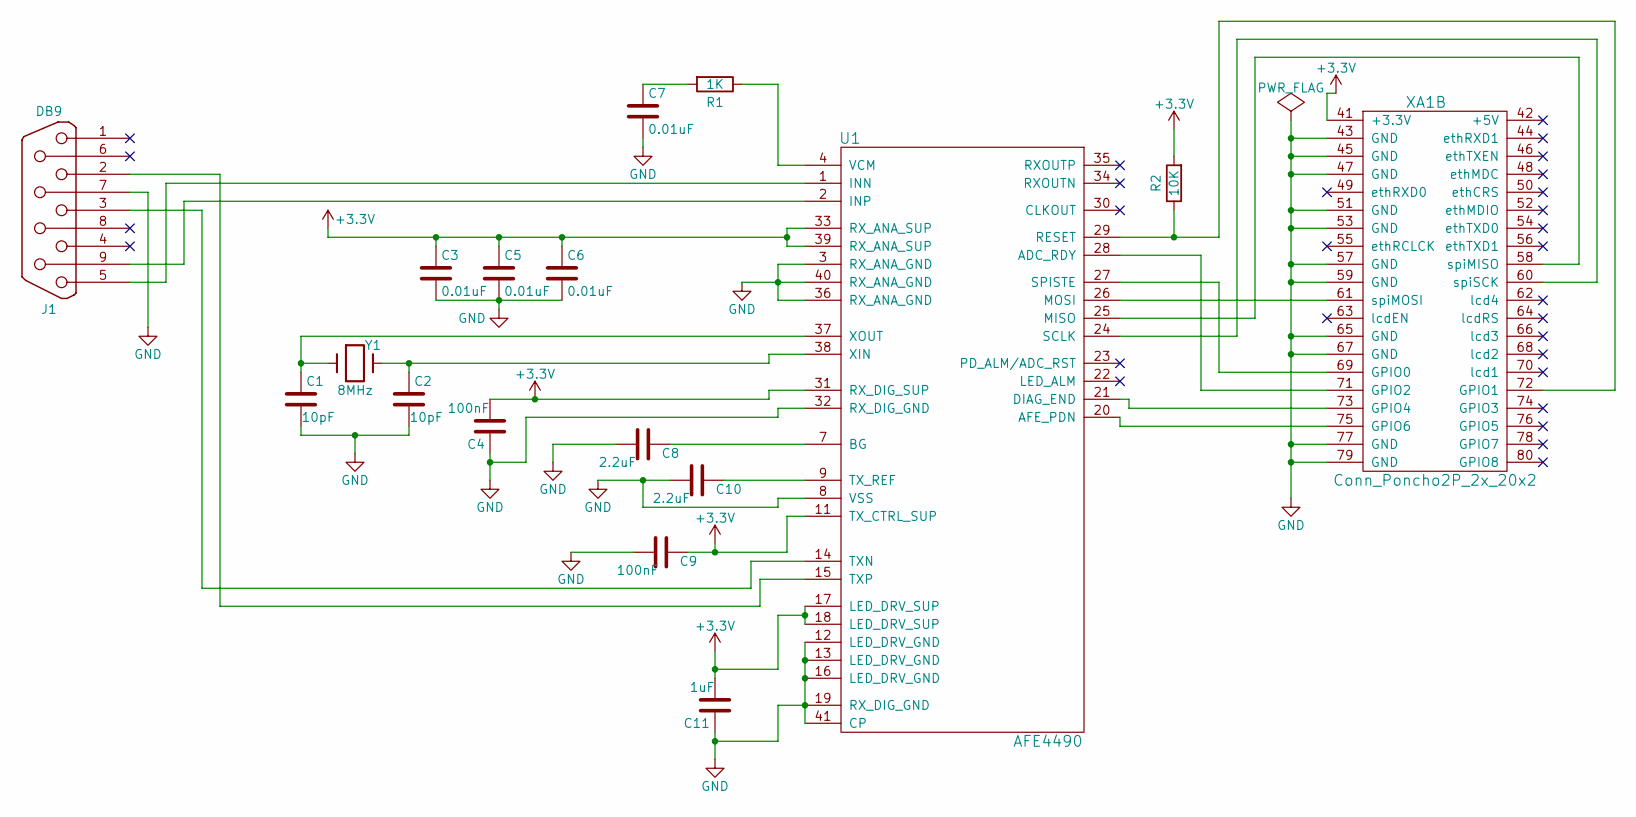
[picture p231: schematic TP.sch, Poncho Oximetro de Pulso para EDU-CIAA]

Parts:
C1, C2: 10pF; C_0805; digikey# 1276-1109-1-ND
C3, C5, C6, C7: 0.01uF; C_0805; digikey# 490-8297-1-ND
C4, C9: 100nF; C_0805; digikey# 478-3351-1-ND
C8, C10: 2.2uF; C_0805; digikey# 478-2580-1-ND
C11: 1uF; C_0805; digikey# 478-1405-1-ND
J1: DB9; DB9_F_TH; digikey# AE10921-ND
R1: 1K; R_0805; digikey# 311-1.0KARCT-ND
R2: 10K; R_0805; digikey# RMCF0805JT10K0CT-ND
U1: AFE4490; QFN40; digikey# 296-35685-1-ND
XA1: Conn_Poncho2P_2x_20x2; Conn_Poncho_Izquierdo; digikey# 952-1387-ND
Y1: 8MHz; Crystal_Round_Horizontal_3mm; digikey# CTX768-ND

Connections:
+3V3: C3.1, C4.2, C5.1, C6.1, C9.1, C11.2, R2.2, U1.11 (TX_CTRL_SUP), U1.17 (LED_DRV_SUP), U1.18 (LED_DRV_SUP), U1.31 (RX_DIG_SUP), U1.33 (RX_ANA_SUP), U1.39 (RX_ANA_SUP), XA1.41 (+3.3V)
GND: C1.2, C2.2, C3.2, C4.1, C5.2, C6.2, C7.2, C8.2, C9.2, C10.2, C11.1, J1.7, U1.3 (RX_ANA_GND), U1.8 (VSS), U1.12 (LED_DRV_GND), U1.13 (LED_DRV_GND), U1.16 (LED_DRV_GND), U1.19 (RX_DIG_GND), U1.32 (RX_DIG_GND), U1.36 (RX_ANA_GND), U1.40 (RX_ANA_GND), U1.41 (CP), XA1.43 (GND), XA1.45 (GND), XA1.47 (GND), XA1.51 (GND), XA1.53 (GND), XA1.57 (GND), XA1.59 (GND), XA1.65 (GND), XA1.67 (GND), XA1.77 (GND), XA1.79 (GND)
unnamed: C1.1, U1.37 (XOUT), Y1.1
unnamed: C2.1, U1.38 (XIN), Y1.2
unnamed: C7.1, R1.2
unnamed: C8.1, U1.7 (BG)
unnamed: C10.1, U1.9 (TX_REF)
unnamed: J1.2, U1.15 (TXP)
unnamed: J1.3, U1.14 (TXN)
unnamed: J1.5, U1.1 (INN)
unnamed: J1.9, U1.2 (INP)
unnamed: R1.1, U1.4 (VCM)
unnamed: R2.1, U1.29 (RESET), XA1.72 (GPIO1)
unnamed: U1.20 (AFE_PDN), XA1.75 (GPIO6)
unnamed: U1.21 (DIAG_END), XA1.73 (GPIO4)
unnamed: U1.24 (SCLK), XA1.60 (spiSCK)
unnamed: U1.25 (MISO), XA1.58 (spiMISO)
unnamed: U1.26 (MOSI), XA1.61 (spiMOSI)
unnamed: U1.27 (SPISTE), XA1.69 (GPIO0)
unnamed: U1.28 (ADC_RDY), XA1.71 (GPIO2)

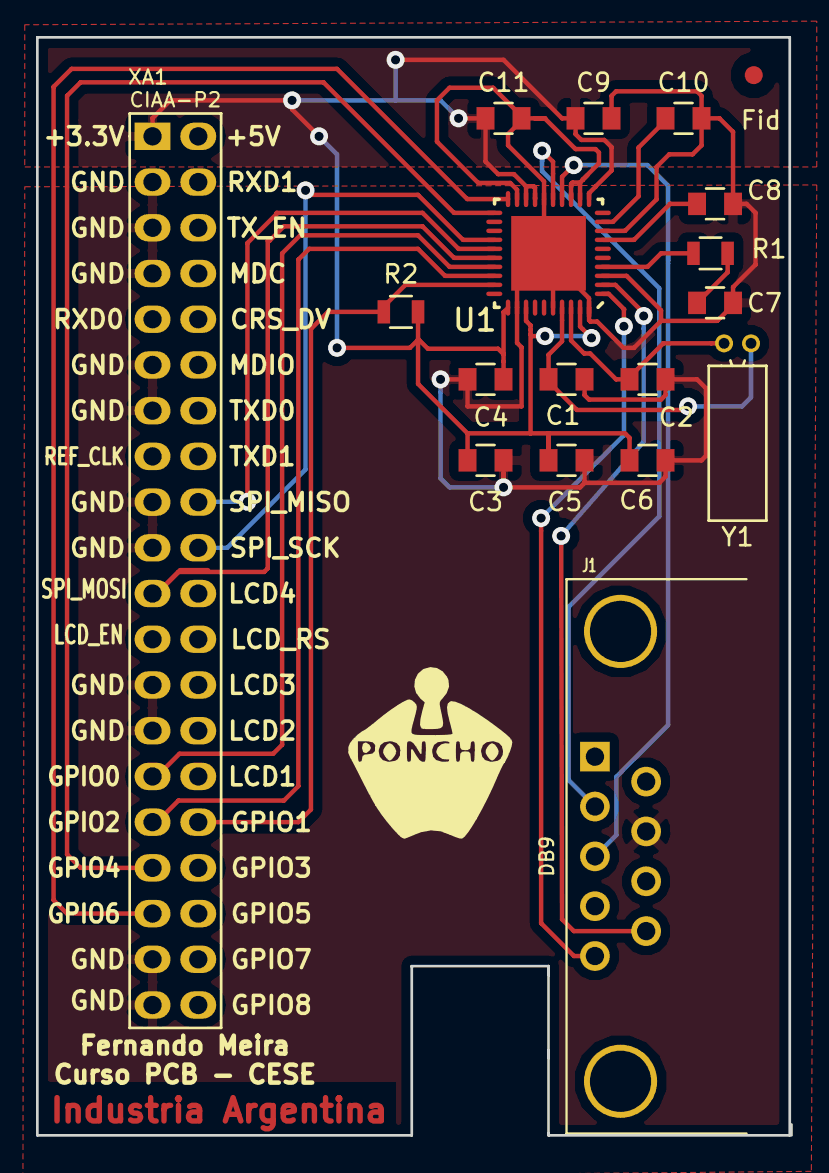
[picture p232: board TP.kicad_pcb from above]

Board: 2 copper layers, 41.8 x 61.0 mm, 19 parts (0 on the bottom side), 20 nets.

Other parts of the board:
Fid: Fiducial_1mm_Dia_2.54mm_Outer_CopperTop
Oximetro : LOGO; Logo_Poncho
