ciaa/Ponchos/PuenteHxI2C/driver_motores_EDU_CIAA.kicad_pcb

## KiCad design PuenteHxI2C/driver_motores_EDU_CIAA.kicad_pcb (2017-01-10)

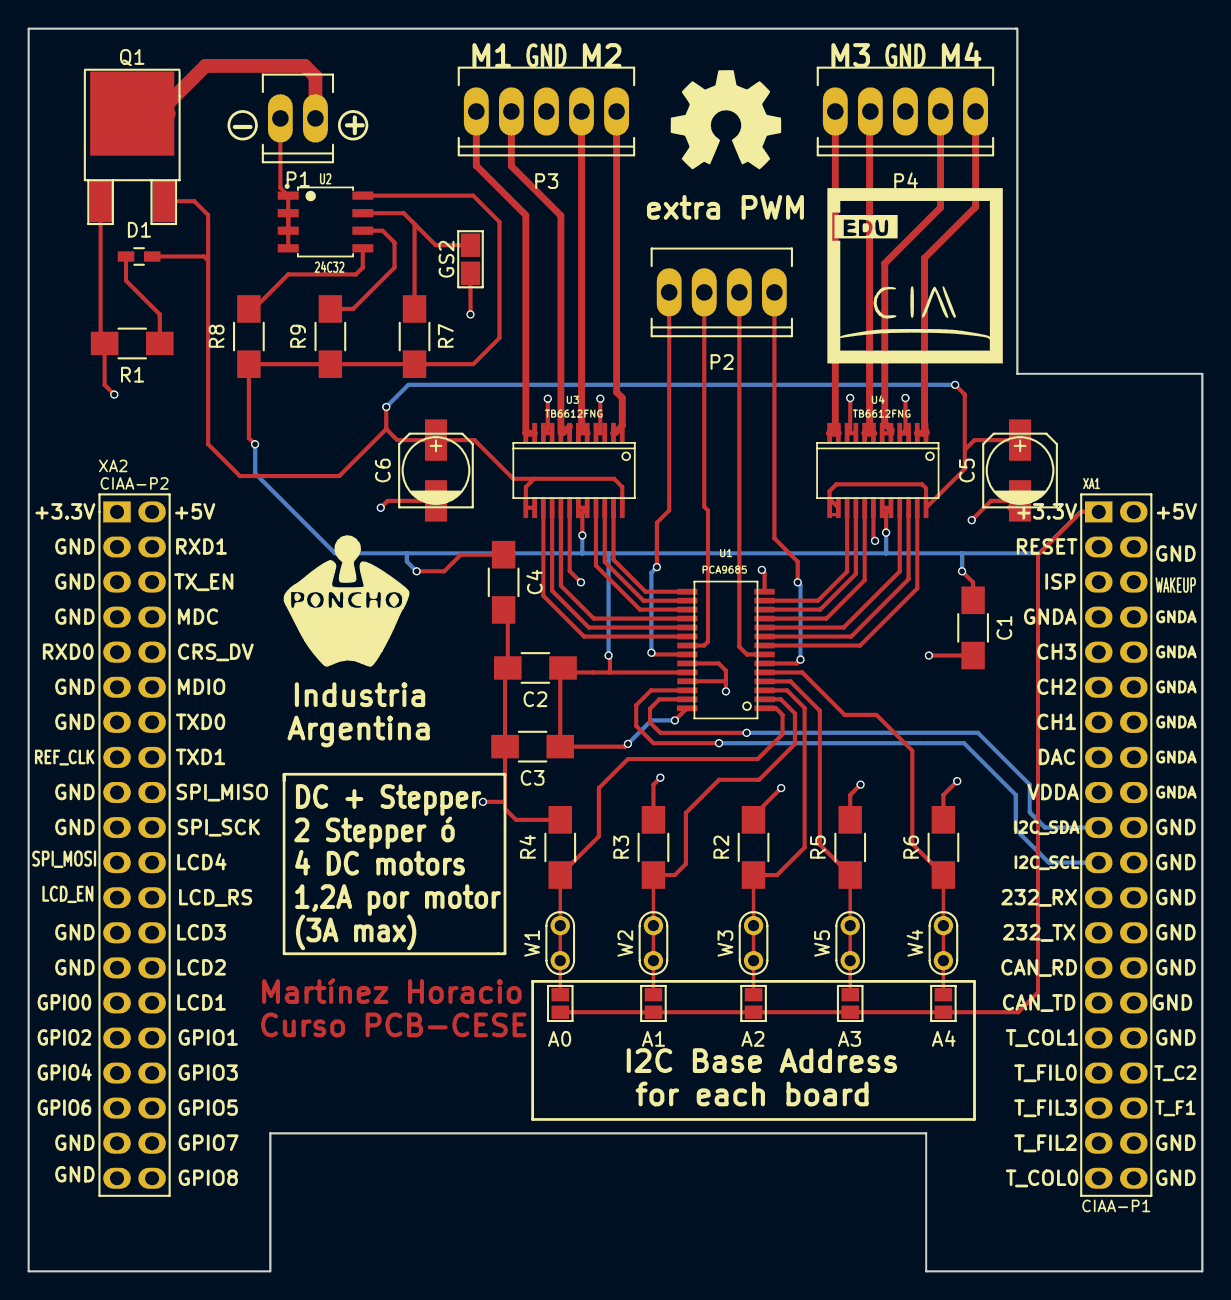
[picture p233: board driver_motores_EDU_CIAA.kicad_pcb from above]

Board: 2 copper layers, 85.0 x 90.0 mm, 39 parts (0 on the bottom side), 39 nets.

Parts:
A0, A1, A2, A3, A4: GS2
C1, C4: 10uf; R_1206_HandSoldering
C2, C3: 0,1uf; R_1206_HandSoldering
C5, C6: 47uF+/16v; c_elec_5x5.3
D1: Green; C_0603_HandSoldering
G101: Logo_OSHWA
GS2: GS4
P1: CONN_01X02; Socket_MOLEX-KK-RM2-54mm_Lock_2pin_straight
P2: CONN_01X04; Socket_MOLEX-KK-RM2-54mm_Lock_4pin_straight
P3, P4: CONN_01X05; Socket_MOLEX-KK-RM2-54mm_Lock_5pin_straight
Q1: AOD417; TO-252-2Lead
R1: 1K; R_1206_HandSoldering
R2, R3, R4, R5, R6: 10K; R_1206_HandSoldering
R7, R8, R9: 3,9K; R_1206_HandSoldering
U1: PCA9685; tssop-28
U2: 24C32; SOIC-8
U3, U4: TB6612FNG; ssop-24
W1, W2, W3, W4, W5: TEST_1P; Test_Point
XA1: Conn_Poncho2P_2x_20x2; Conn_Poncho_Derecha
XA2: Conn_Poncho_Izquierdo

Connections:
+3V3: A0.2, A1.2, A2.2, A3.2, A4.2, C1.1, C2.1, C3.1, C4.1, R7.2, R8.1, R9.1, U1.24, U1.28, U2.8, U3.19, U3.20, U4.19, U4.20, XA1.1
+12V: C5.1, C6.1, D1.2, Q1.3, U3.13, U3.14, U3.24, U4.13, U4.14, U4.24
/A0: A0.1, R4.1, U1.1, W1.1
/A1: A1.1, R3.1, U1.2, W2.1
/A2: A2.1, R2.1, U1.3, W3.1
/A3: A3.1, R5.1, U1.4, W5.1
/A4: A4.1, R6.1, U1.5, W4.1
/LED0: P2.1, U1.6
/LED1: P2.2, U1.7
/LED2: U1.8, U4.23
/LED3: U1.9, U4.22
/LED4: U1.10, U4.21
/LED5: U1.11, U4.17
/LED6: U1.12, U4.16
/LED7: U1.13, U4.15
/LED8: U1.15, U3.23
/LED9: U1.16, U3.22
/LED10: U1.17, U3.21
/LED11: U1.18, U3.17
/LED12: U1.19, U3.16
/LED13: U1.20, U3.15
/LED14: P2.3, U1.21
/LED15: P2.4, U1.22
/SCL: U1.26, XA1.21
/SDA: U1.27, XA1.19
GND: C1.2, C2.2, C3.2, C4.2, C5.2, C6.2, GS2.1, P1.2, P3.3, P4.3, Q1.1, R1.2, R2.2, R3.2, R4.2, R5.2, R6.2, U1.14, U1.23, U1.25, U2.1, U2.2, U2.3, U2.4, U3.3, U3.4, U3.9, U3.10, U3.18, U4.3, U4.4, U4.9, U4.10, U4.18, XA1.4, XA1.20, XA1.22, XA1.24, XA1.26, XA1.28, XA1.30, XA1.32, XA1.38, XA1.40
unnamed: D1.1, R1.1
unnamed: GS2.2, R7.1, U2.7
unnamed: P1.1, Q1.2
unnamed: P3.1, U3.1, U3.2
unnamed: P3.2, U3.5, U3.6
unnamed: P3.4, U3.7, U3.8
unnamed: P3.5, U3.11, U3.12
unnamed: P4.1, U4.1, U4.2
unnamed: P4.2, U4.5, U4.6
unnamed: P4.4, U4.7, U4.8
unnamed: P4.5, U4.11, U4.12
unnamed: R8.2, U2.5
unnamed: R9.2, U2.6
