ciaa/Ponchos/Mision_SAE/Mision_SAE.kicad_pcb

## KiCad design Mision_SAE/Mision_SAE.kicad_pcb (2017-01-10)

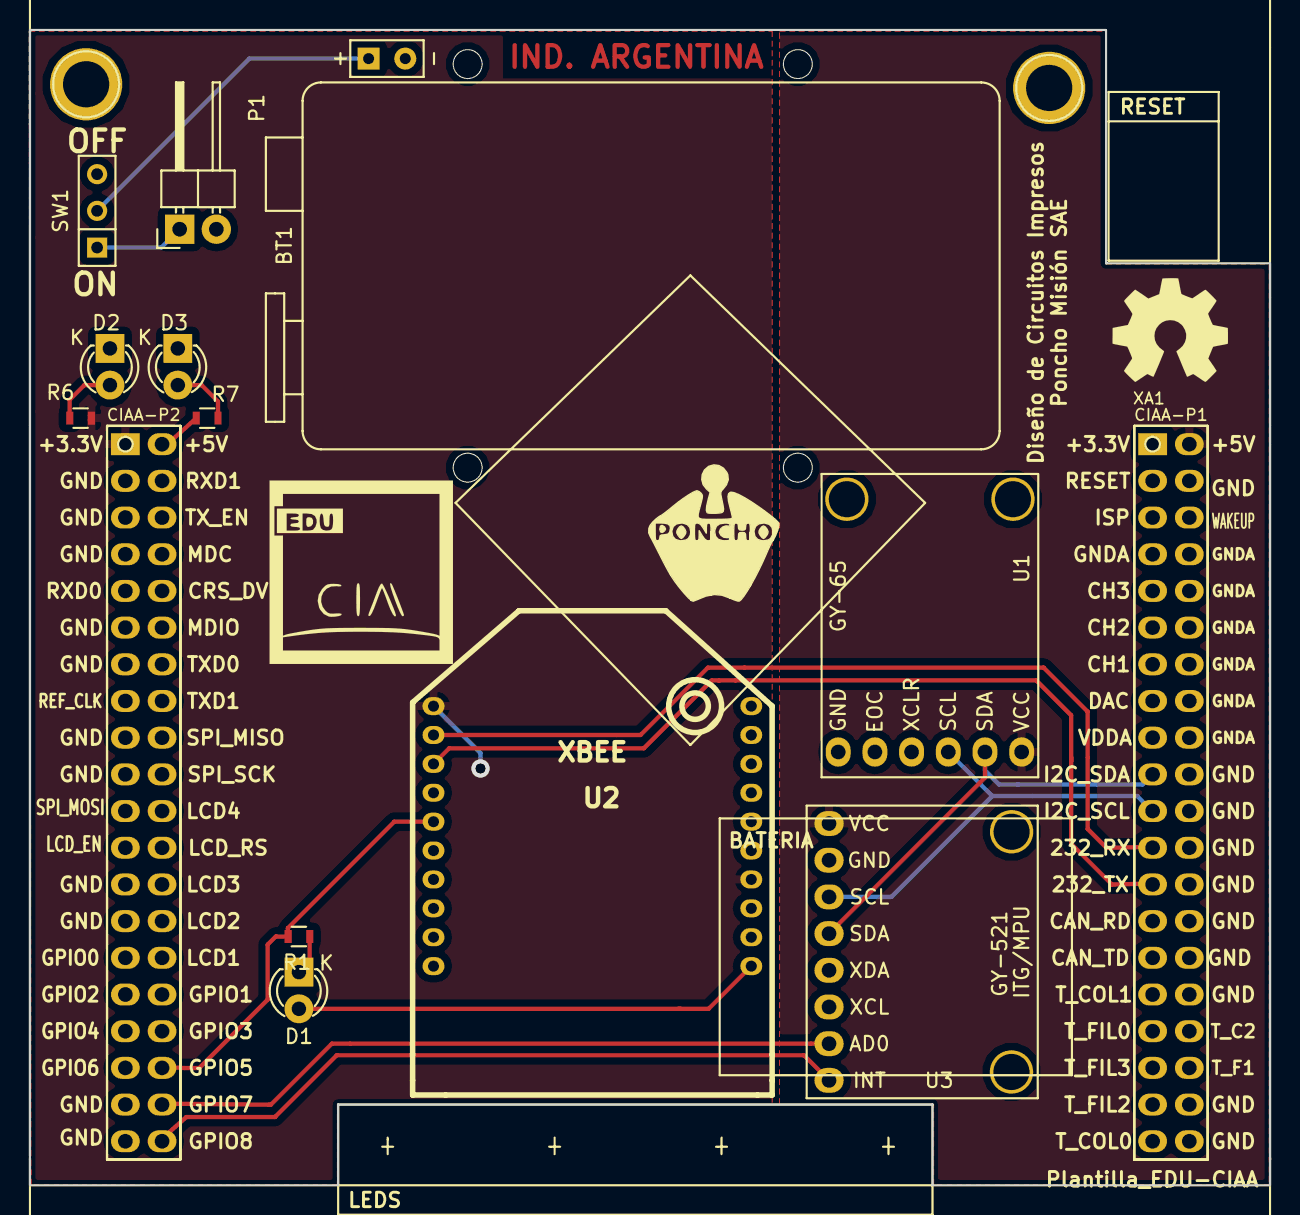
[picture p234: board Mision_SAE.kicad_pcb from above]

Board: 2 copper layers, 85.9 x 80.0 mm, 15 parts (0 on the bottom side), 16 nets.

Parts:
BT1: Battery; bat_con
D1, D2, D3: LED; LED-3MM
G101: Logo_OSHWA
MP?: Plantilla_EDU-CIAA
P1: CONN_01X02; Pin_Header_Angled_1x02
R1, R6, R7: R; R_0603
SW1: SPST; SW_Micro_SPST
U1: GY-65
U2: XBEE; XBee-pro
U3: GY-521
XA1: Conn_Poncho2P_2x_20x2; Conn_Poncho_SinBorde

Connections:
+3V3: R6.1, U2.1, U2.14, XA1.41
+5V: U1.1, U3.1, XA1.2
/Conector/GPIO5: R1.1, U2.5, XA1.76
/Conector/GPIO8: U3.8, XA1.80
/Conector/RX: U2.2, XA1.23
/Conector/SCL: U1.3, U3.3, XA1.21
/Conector/SDA: U1.2, U3.4, XA1.19
/Sensores/AD0_MPU: U3.7, XA1.78
/XBee/RX: U2.3, XA1.25
GND: BT1.2, D1.1, D2.1, D3.1, P1.2, R1.2, U1.6, U2.10, U3.2, XA1.4, XA1.20, XA1.22, XA1.24, XA1.26, XA1.28, XA1.30, XA1.32, XA1.38, XA1.40, XA1.43, XA1.45, XA1.47, XA1.51, XA1.53, XA1.57, XA1.59, XA1.65, XA1.67, XA1.77, XA1.79
unnamed: BT1.1, SW1.2
unnamed: D1.2, U2.11
unnamed: D2.2, R6.2
unnamed: D3.2, R7.1
unnamed: P1.1, SW1.1
unnamed: R7.2, XA1.42
