ciaa/Ponchos/IoT/ponchoeduciaaiot.kicad_pcb

## KiCad design IoT/ponchoeduciaaiot.kicad_pcb (2017-01-10)

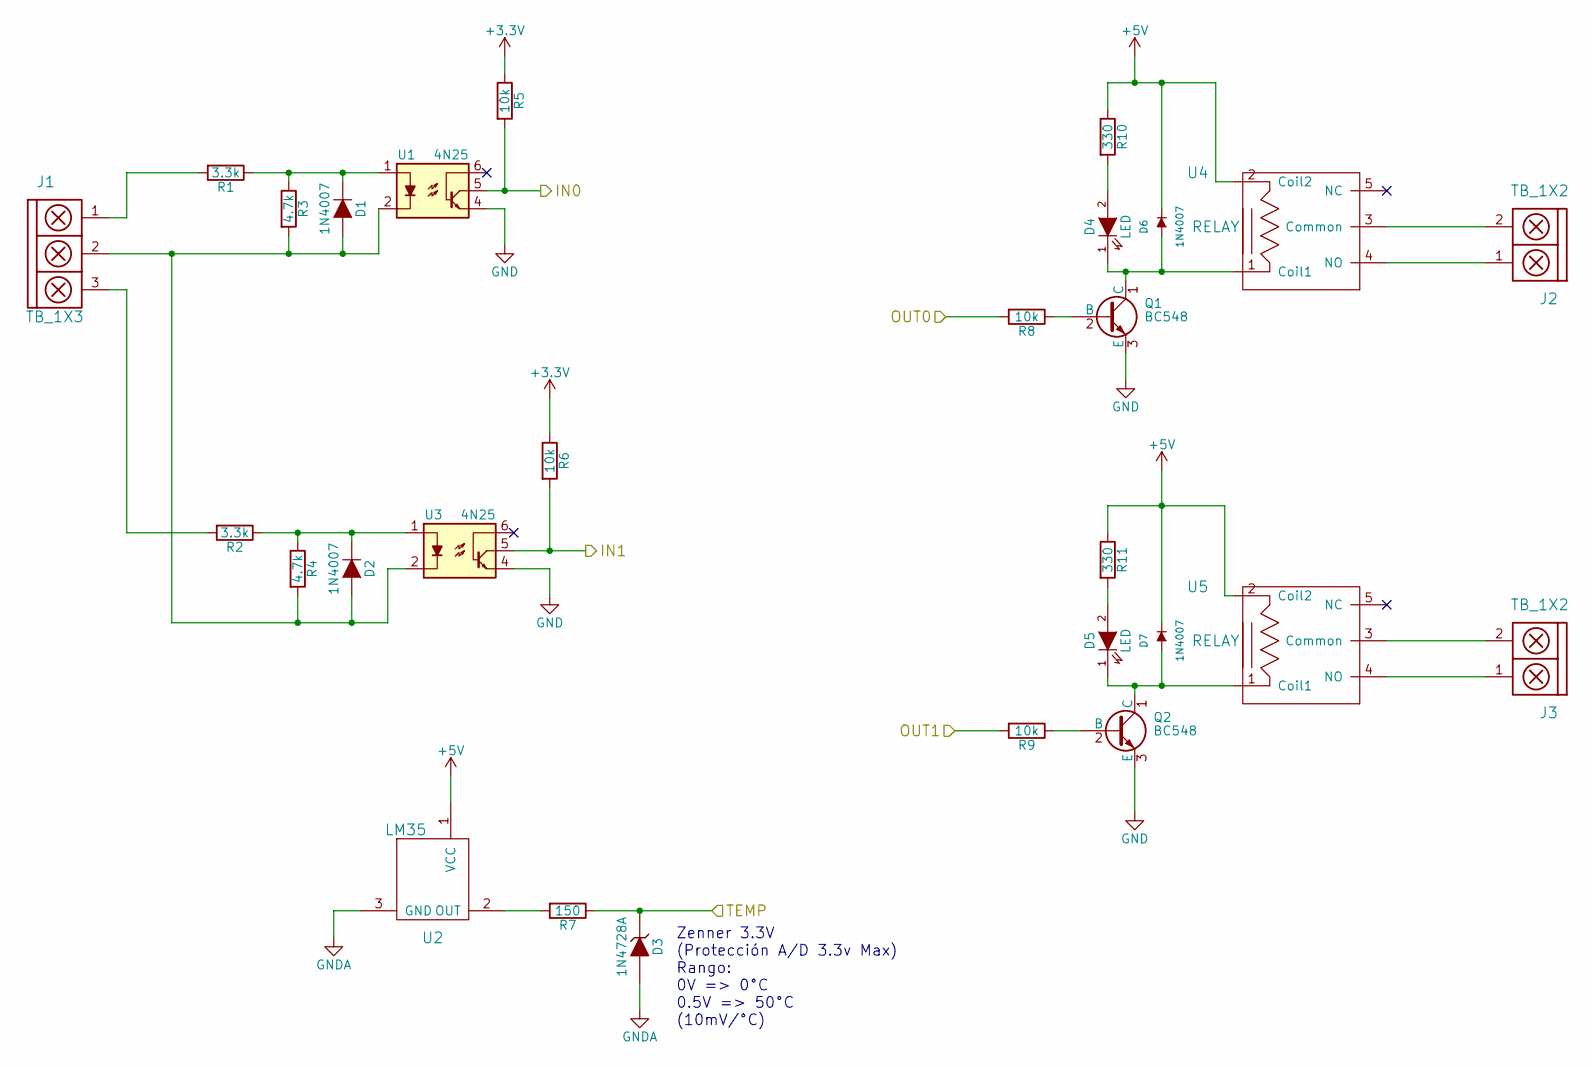
[picture p235: schematic gpios.sch, Poncho EDU-CIAA-NXP IoT. GPIOs]

Parts:
D1, D2, D6, D7: 1N4007; Diode_DO-35_SOD27_Horizontal_RM10; Digikey# 1N4007-TPMSTR-ND
D3: 1N4728A; Diode_DO-35_SOD27_Horizontal_RM10; Digikey# 1N4728AVSTR-ND
D4, D5: LED; LED-3MM; Digikey# MV5054A3EL-ND
J1: TB_1X3; bornier3; Digikey# ED2610-ND
J2, J3: TB_1X2; bornier2; Digikey# ED2609-ND
Q1, Q2: BC548; TO-92_Rugged; Digikey# BC548BTATB-ND
R1, R2: 3.3k; Resistor_Horizontal_RM7mm; Digikey# CF14JT3K30TR-ND
R3, R4: 4.7k; Resistor_Horizontal_RM7mm; Digikey# CF14JT4K70TR-ND
R5, R6, R8, R9: 10k; Resistor_Horizontal_RM7mm; Digikey# CF14JT10K0TR-ND
R7: 150; Resistor_Horizontal_RM7mm; Digikey# CF14JT150RTR-ND
R10, R11: 330; Resistor_Horizontal_RM7mm; Digikey# P330BATB-ND
U1, U3: 4N25; DIP-6_W7.62mm_LongPads; Digikey# 160-1300-5-ND
U2: LM35; TO-92_Rugged; Digikey# LM35DZ/NOPB-ND
U4, U5: RELAY; Relay5vSI; Digikey# PB2029-ND

Connections:
+3V3: R5.1, R6.1; also elsewhere on the board
+5V: D6.2 (K), D7.2 (K), R10.1, R11.1, U2.1 (VCC), U4.2 (Coil2), U5.2 (Coil2); also elsewhere on the board
/ConectoresPoncho/ANALOG_IN: D3.1 (K), R7.1; also elsewhere on the board
/gpios/IN0: R5.2, U1.5; also elsewhere on the board
/gpios/IN1: R6.2, U3.5; also elsewhere on the board
/gpios/OUT0: R8.2; also elsewhere on the board
/gpios/OUT1: R9.2; also elsewhere on the board
GND: Q1.3 (E), Q2.3 (E), U1.4, U3.4; also elsewhere on the board
GNDA: D3.2 (A), U2.3 (GND); also elsewhere on the board
unnamed: D1.1 (K), R1.1, R3.1, U1.1
unnamed: D1.2 (A), D2.2 (A), J1.2, R3.2, R4.2, U1.2, U3.2
unnamed: D2.1 (K), R2.1, R4.1, U3.1
unnamed: D4.1 (K), D6.1 (A), Q1.1 (C), U4.1 (Coil1)
unnamed: D4.2 (A), R10.2
unnamed: D5.1 (K), D7.1 (A), Q2.1 (C), U5.1 (Coil1)
unnamed: D5.2 (A), R11.2
unnamed: J1.1, R1.2
unnamed: J1.3, R2.2
unnamed: J2.1, U4.4 (NO)
unnamed: J2.2, U4.3 (Common)
unnamed: J3.1, U5.4 (NO)
unnamed: J3.2, U5.3 (Common)
unnamed: Q1.2 (B), R8.1
unnamed: Q2.2 (B), R9.1
unnamed: R7.2, U2.2 (OUT)

Notes on the sheet:
Zenner 3.3V (Protección A/D 3.3v Max) Rango: 0V => 0°C 0.5V => 50°C (10mV/°C)

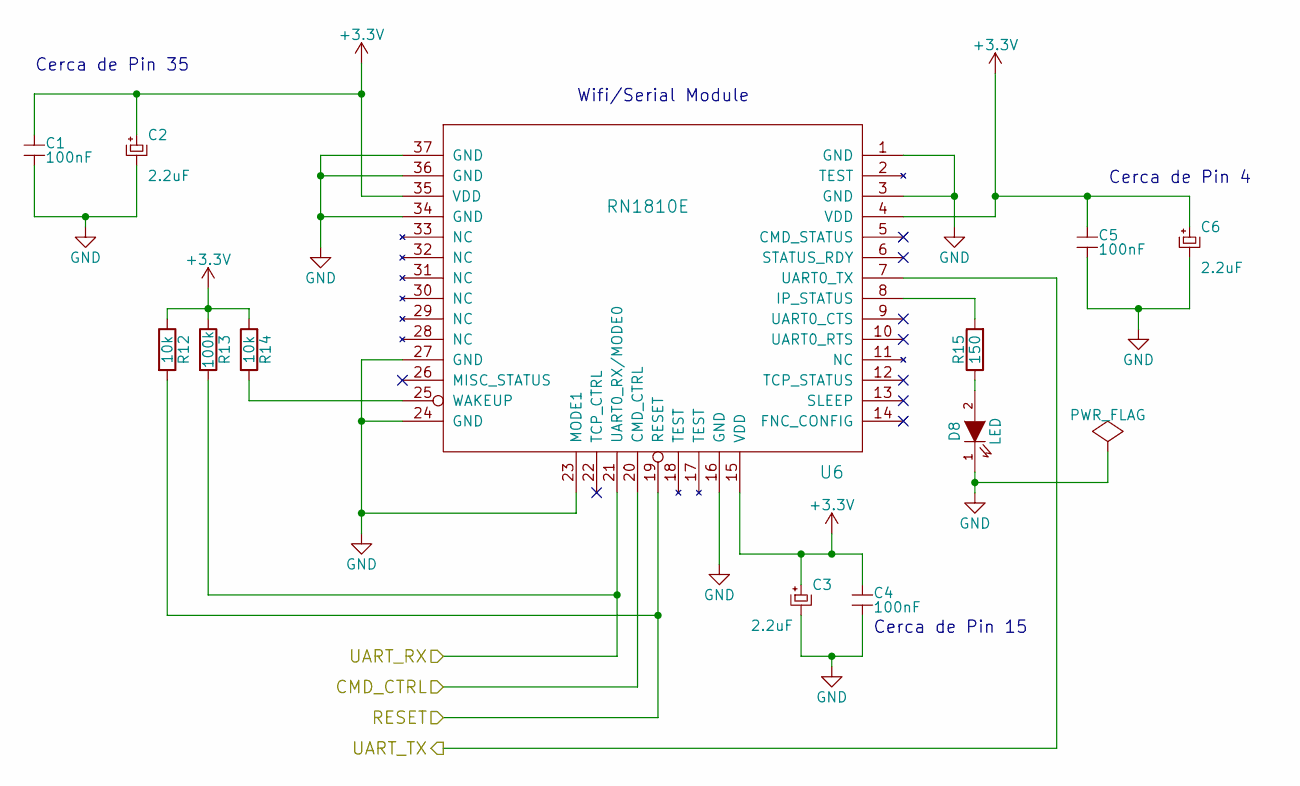
[picture p236: schematic comm.sch, Poncho EDU-CIAA-NXP IoT. Communication]

Parts:
C1, C4, C5: 100nF; C_Disc_D6_P5; Digikey# 399-9858-2-ND
C2, C3, C6: 2.2uF; C_Radial_D5_L11_P2; Digikey# 225CKR050M-ND
D8: LED; LED-3MM; Digikey# MV5054A3EL-ND
R12, R14: 10k; Resistor_Horizontal_RM7mm; Digikey# CF14JT10K0TR-ND
R13: 100k; Resistor_Horizontal_RM7mm; Digikey# CF14JT100KTR-ND
R15: 150; Resistor_Horizontal_RM7mm; Digikey# CF14JT150RTR-ND
U6: RN1810E; RN1810; Digikey# RN1810-I/RM100-ND

Connections:
+3V3: C1.1, C2.1, C3.1, C4.1, C5.1, C6.1, R12.1, R13.1, R14.1, U6.4 (VDD), U6.15 (VDD), U6.35 (VDD); also elsewhere on the board
/ConectoresPoncho/MODULE_RESET: R12.2, U6.19 (RESET); also elsewhere on the board
/ConectoresPoncho/RXD_EDUCIAA: U6.7 (UART0_TX); also elsewhere on the board
/ConectoresPoncho/TXD_EDUCIAA: R13.2, U6.21 (UART0_RX/MODE0); also elsewhere on the board
/comm/CMD_CTRL: U6.20 (CMD_CTRL); also elsewhere on the board
GND: C1.2, C2.2, C3.2, C4.2, C5.2, C6.2, D8.1 (K), U6.1 (GND), U6.3 (GND), U6.16 (GND), U6.23 (MODE1), U6.24 (GND), U6.27 (GND), U6.34 (GND), U6.36 (GND), U6.37 (GND); also elsewhere on the board
unnamed: D8.2 (A), R15.1
unnamed: R14.2, U6.25 (WAKEUP)
unnamed: R15.2, U6.8 (IP_STATUS)

Notes on the sheet:
Cerca de Pin 15
Cerca de Pin 4
Cerca de Pin 35
Wifi/Serial Module

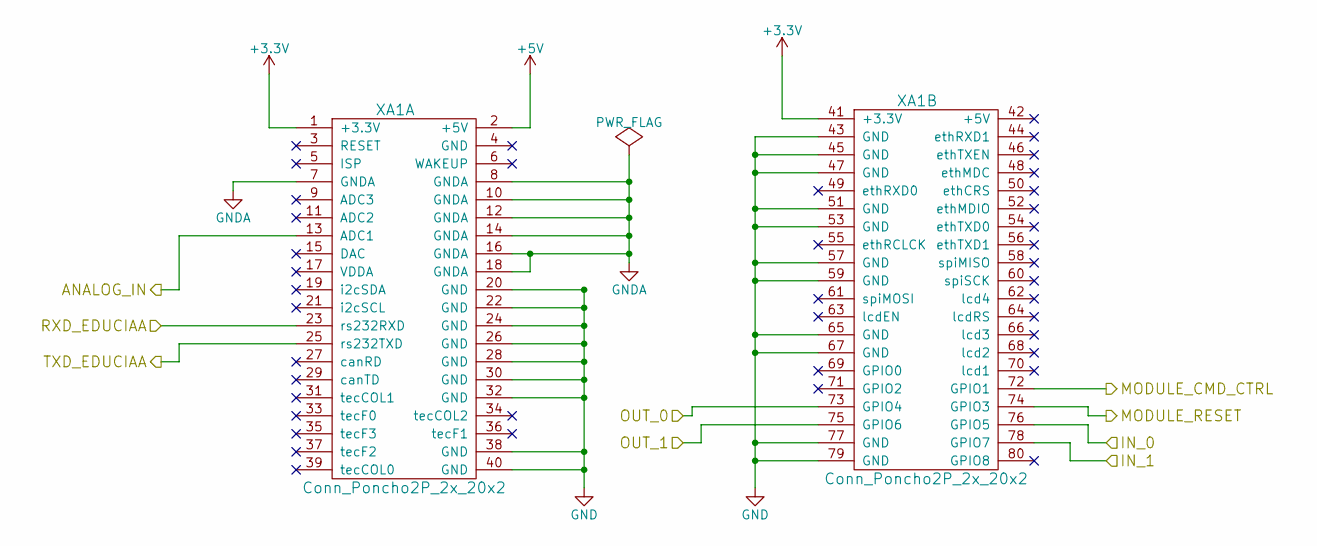
[picture p237: schematic ConectoresPoncho.sch, Poncho EDU-CIAA-NXP IoT. Poncho connectors]

Parts:
XA1: Conn_Poncho2P_2x_20x2; Conn_Poncho_Mediano

Connections:
+3V3: XA1.1 (+3.3V), XA1.41 (+3.3V); also elsewhere on the board
+5V: XA1.2 (+5V); also elsewhere on the board
/ConectoresPoncho/ANALOG_IN: XA1.13 (ADC1); also elsewhere on the board
/ConectoresPoncho/MODULE_RESET: XA1.74 (GPIO3); also elsewhere on the board
/ConectoresPoncho/RXD_EDUCIAA: XA1.23 (rs232RXD); also elsewhere on the board
/ConectoresPoncho/TXD_EDUCIAA: XA1.25 (rs232TXD); also elsewhere on the board
/comm/CMD_CTRL: XA1.72 (GPIO1); also elsewhere on the board
/gpios/IN0: XA1.76 (GPIO5); also elsewhere on the board
/gpios/IN1: XA1.78 (GPIO7); also elsewhere on the board
/gpios/OUT0: XA1.73 (GPIO4); also elsewhere on the board
/gpios/OUT1: XA1.75 (GPIO6); also elsewhere on the board
GND: XA1.20 (GND), XA1.22 (GND), XA1.24 (GND), XA1.26 (GND), XA1.28 (GND), XA1.30 (GND), XA1.32 (GND), XA1.38 (GND), XA1.40 (GND), XA1.43 (GND), XA1.45 (GND), XA1.47 (GND), XA1.51 (GND), XA1.53 (GND), XA1.57 (GND), XA1.59 (GND), XA1.65 (GND), XA1.67 (GND), XA1.77 (GND), XA1.79 (GND); also elsewhere on the board
GNDA: XA1.7 (GNDA), XA1.8 (GNDA), XA1.10 (GNDA), XA1.12 (GNDA), XA1.14 (GNDA), XA1.16 (GNDA), XA1.18 (GNDA); also elsewhere on the board

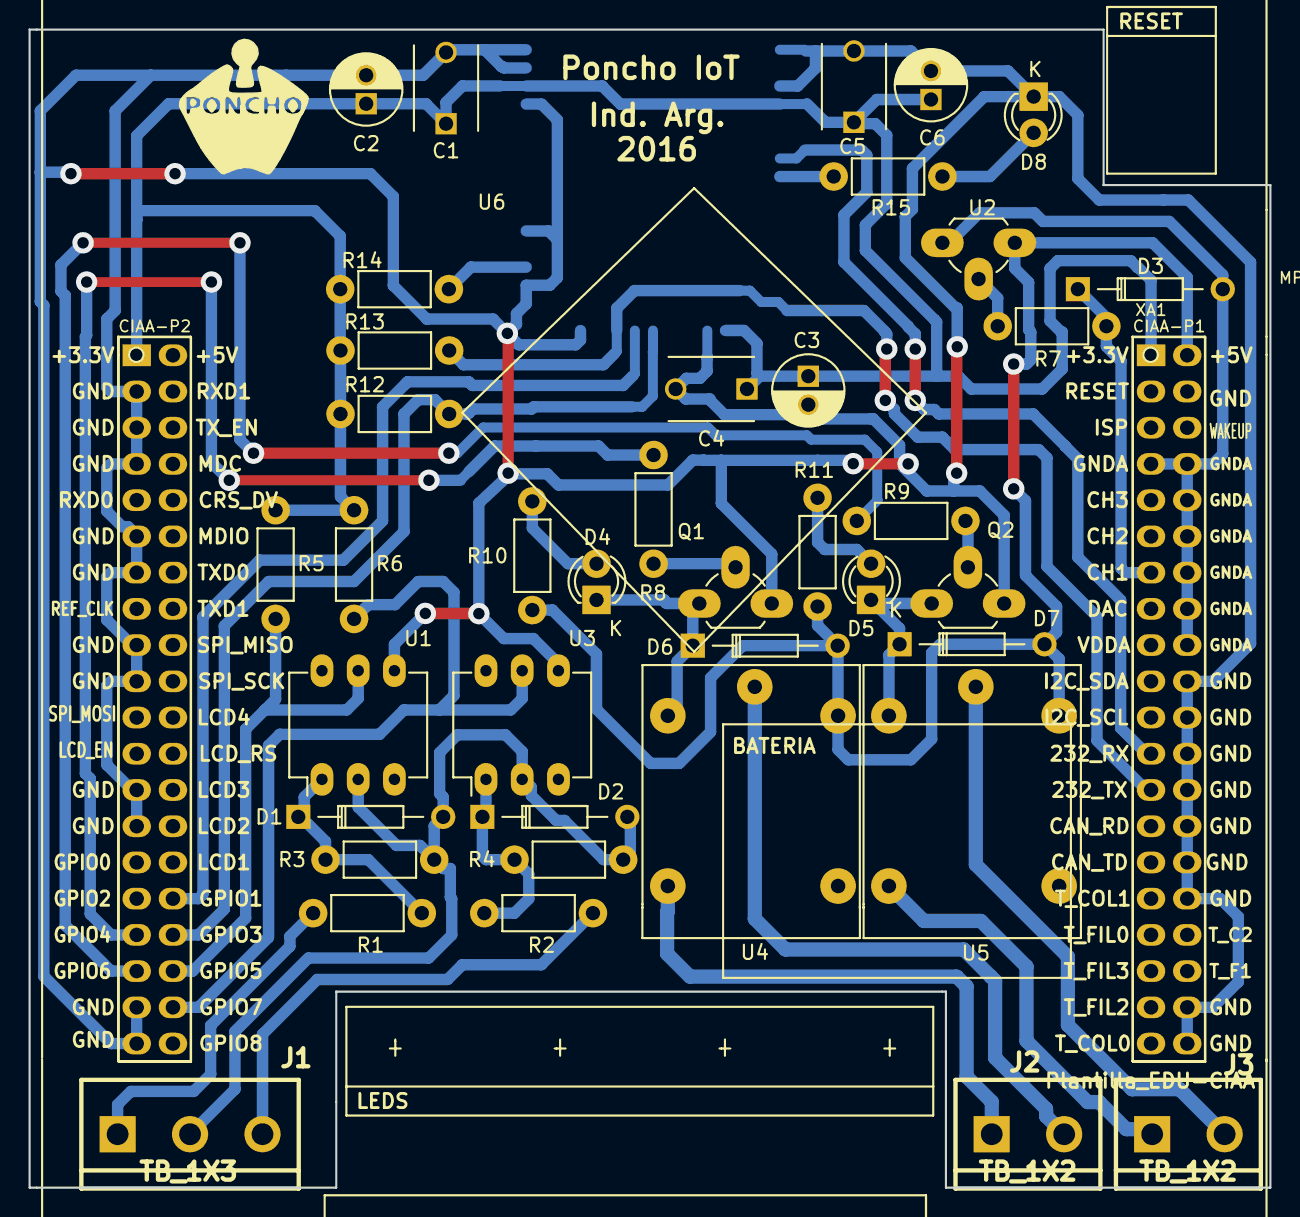
[picture p238: board ponchoeduciaaiot.kicad_pcb from above]

Board: 2 copper layers, 87.0 x 81.2 mm, 42 parts (0 on the bottom side), 32 nets.

Other parts of the board:
MP?: Plantilla_EDU-CIAA
