ciaa/Ponchos/Educativo1/EduPoncho.kicad_pcb

## KiCad design Educativo1/EduPoncho.kicad_pcb (2017-01-10)

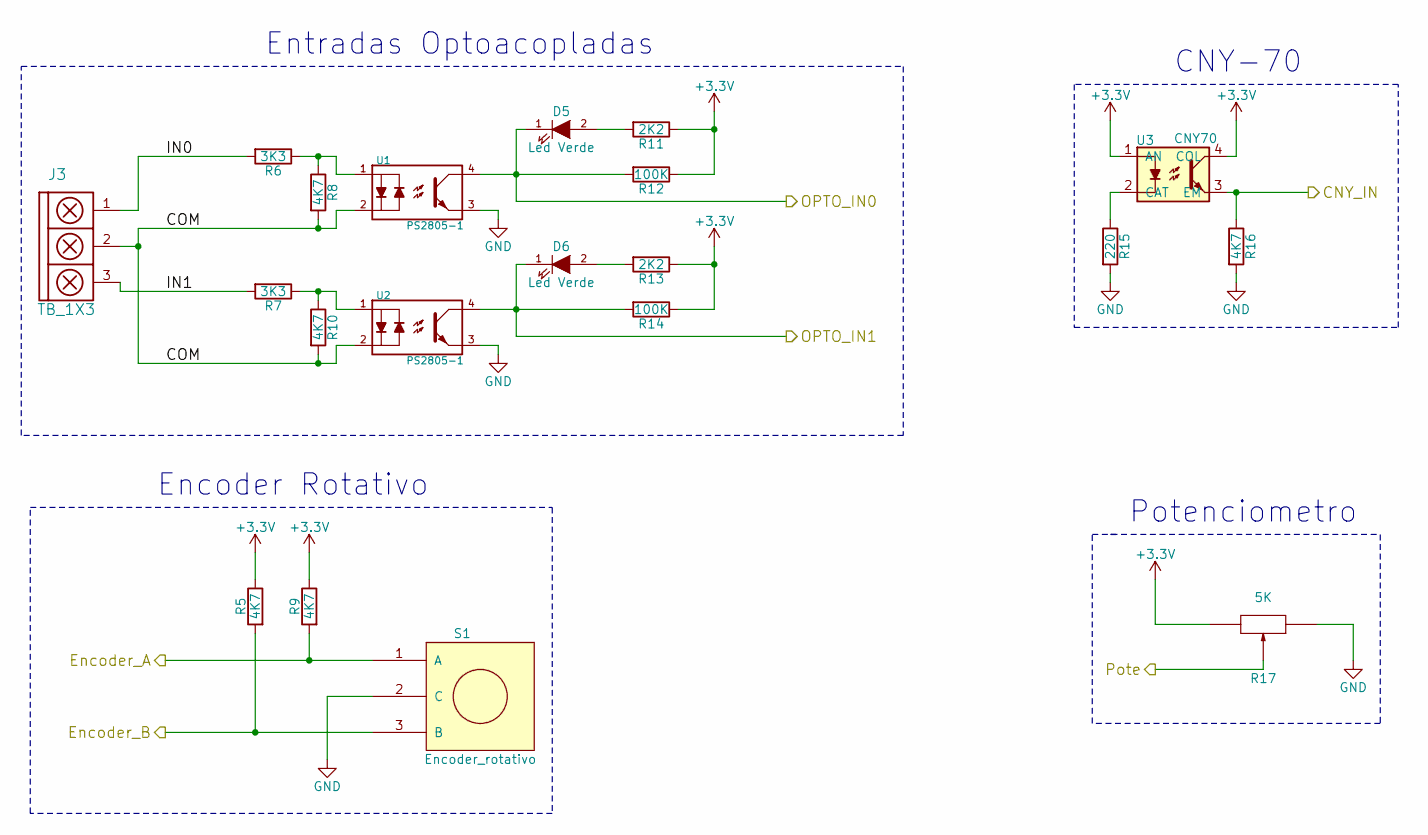
[picture p239: schematic Entradas.sch, Entradas- EduPoncho]

Parts:
D5, D6: Led Verde; LED_0603; Digikey# 160-1446-1-ND
J3: TB_1X3; TerminalBlock_Pheonix_MPT-2.54mm_3pol; Digikey# ED2610-ND
R5, R8, R9, R10, R16: 4K7; R_0805_HandSoldering; Digikey# RMCF0805JT4K70TR-ND
R6, R7: 3K3; R_0805_HandSoldering; Digikey# RMCF0805JT3K30TR-ND
R11, R13: 2K2; R_0805_HandSoldering; Digikey# RMCF0805JT2K20TR-ND
R12, R14: 100K; R_0805_HandSoldering; Digikey# RMCF0805JT100KTR-ND
R15: 220; R_0805_HandSoldering; Digikey# RMCF0805JT220RTR-ND
R17: 5K; Potentiometer_Alps-RK16-single_largePads; Digikey# PTD901-2015K-B502-ND
S1: Encoder_rotativo
U1, U2: PS2805-1; Optocoupler_SMD_HandSoldering_KPC357_LTV35x_PC357_SingleCha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; Digikey# PS2805-1ATR-ND
U3: CNY70; Digikey# 751-1025-ND

Connections:
+3V3: R5.1, R9.1, R11.1, R12.1, R13.1, R14.1, R17.3, U3.1 (AN), U3.4 (COL); also elsewhere on the board
/Conector Poncho/CNY_IN: R16.1, U3.3 (EM); also elsewhere on the board
/Conector Poncho/Encoder_A: R9.2, S1.1 (A); also elsewhere on the board
/Conector Poncho/Encoder_B: R5.2, S1.3 (B); also elsewhere on the board
/Conector Poncho/OPTO_IN0: D5.1 (K), R12.2, U1.4; also elsewhere on the board
/Conector Poncho/OPTO_IN1: D6.1 (K), R14.2, U2.4; also elsewhere on the board
/Conector Poncho/Pote: R17.2; also elsewhere on the board
/Entradas/COM: J3.2, R8.2, R10.2, U1.2, U2.2
/Entradas/IN0: J3.1, R6.2
/Entradas/IN1: J3.3, R7.2
GND: R15.2, R16.2, R17.1, S1.2 (C), U1.3, U2.3; also elsewhere on the board
unnamed: D5.2 (A), R11.2
unnamed: D6.2 (A), R13.2
unnamed: R6.1, R8.1, U1.1
unnamed: R7.1, R10.1, U2.1
unnamed: R15.1, U3.2 (CAT)

Notes on the sheet:
Potenciometro
Entradas Optoacopladas
Encoder Rotativo
CNY-70

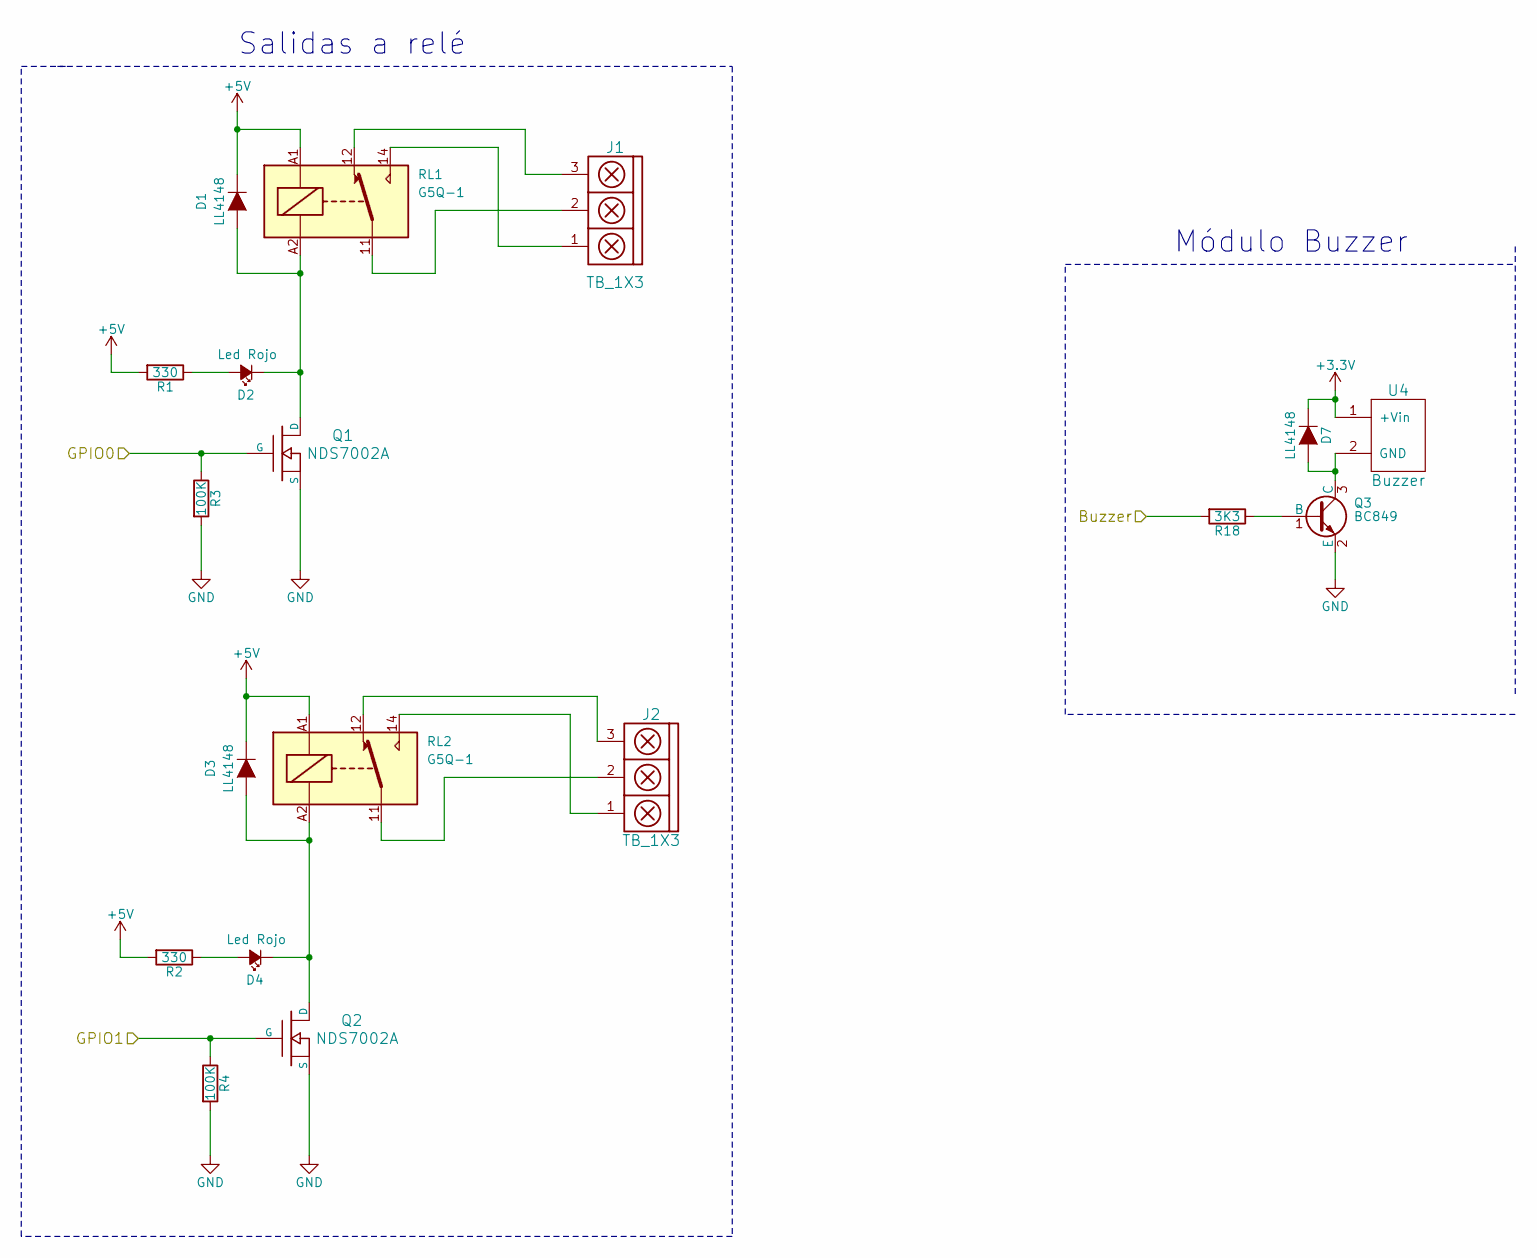
[picture p240: schematic Salidas.sch, Salidas-EduPoncho]

Parts:
D1, D3, D7: LL4148; MiniMELF_Handsoldering; Digikey# LL4148FSCT-ND
D2, D4: Led Rojo; LED_0603; Digikey# 1080-1400-1-ND
J1, J2: TB_1X3; TerminalBlock_Pheonix_PT-3.5mm_3pol; Digikey# ED2610-ND
Q1, Q2: NDS7002A; SOT-23_Handsoldering; Digikey# NDS7002ACT-ND
Q3: BC849; SOT-23_Handsoldering; Digikey# 568-6072-2-ND
R1, R2: 330; R_0805_HandSoldering; Digikey# RMCF0805JT330RTR-ND
R3, R4: 100K; R_0805_HandSoldering; Digikey# RMCF0805JT100KTR-ND
R18: 3K3; R_0805_HandSoldering; Digikey# RMCF0805JT3K30TR-ND
RL1, RL2: G5Q-1; Relay_SPDT_Omron-G5-Q1; Digikey# G5Q-1DC5-ND
U4: Buzzer; Buzzer_12x9.5RM7.6; Digikey# 490-4697-ND

Connections:
+3V3: D7.1 (K), U4.1 (+Vin); also elsewhere on the board
+5V: D1.1 (K), D3.1 (K), R1.2, R2.2, RL1.A1, RL2.A1; also elsewhere on the board
/Conector Poncho/Buzzer: R18.2; also elsewhere on the board
/Conector Poncho/GPIO0: Q1.1 (G), R3.1; also elsewhere on the board
/Conector Poncho/GPIO1: Q2.1 (G), R4.1; also elsewhere on the board
GND: Q1.2 (S), Q2.2 (S), Q3.2 (E), R3.2, R4.2; also elsewhere on the board
unnamed: D1.2 (A), D2.1 (K), Q1.3 (D), RL1.A2
unnamed: D2.2 (A), R1.1
unnamed: D3.2 (A), D4.1 (K), Q2.3 (D), RL2.A2
unnamed: D4.2 (A), R2.1
unnamed: D7.2 (A), Q3.3 (C), U4.2 (GND)
unnamed: J1.1, RL1.14
unnamed: J1.2, RL1.11
unnamed: J1.3, RL1.12
unnamed: J2.1, RL2.14
unnamed: J2.2, RL2.11
unnamed: J2.3, RL2.12
unnamed: Q3.1 (B), R18.1

Notes on the sheet:
Módulo Buzzer
Salidas a relé
