ciaa/Ponchos/Educativo1/EduPoncho.kicad_pcb

## KiCad design Educativo1/EduPoncho.kicad_pcb (continued)

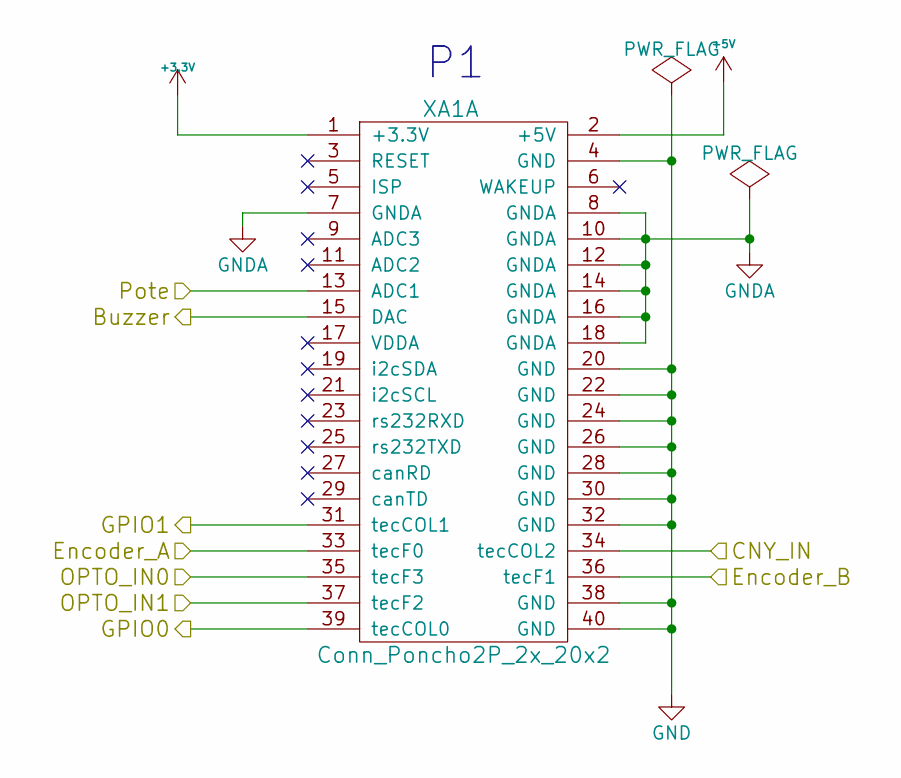
[picture p241: schematic ConectorPoncho.sch, Conector Poncho Edu-Ciaa]

Parts:
XA1: Conn_Poncho2P_2x_20x2; Conn_Poncho_Derecha_SinBorde; Digikey# 952-1387-ND

Connections:
+3V3: XA1.1 (+3.3V); also elsewhere on the board
+5V: XA1.2 (+5V); also elsewhere on the board
/Conector Poncho/Buzzer: XA1.15 (DAC); also elsewhere on the board
/Conector Poncho/CNY_IN: XA1.34 (tecCOL2); also elsewhere on the board
/Conector Poncho/Encoder_A: XA1.33 (tecF0); also elsewhere on the board
/Conector Poncho/Encoder_B: XA1.36 (tecF1); also elsewhere on the board
/Conector Poncho/GPIO0: XA1.39 (tecCOL0); also elsewhere on the board
/Conector Poncho/GPIO1: XA1.31 (tecCOL1); also elsewhere on the board
/Conector Poncho/OPTO_IN0: XA1.35 (tecF3); also elsewhere on the board
/Conector Poncho/OPTO_IN1: XA1.37 (tecF2); also elsewhere on the board
/Conector Poncho/Pote: XA1.13 (ADC1); also elsewhere on the board
GND: XA1.4 (GND), XA1.20 (GND), XA1.22 (GND), XA1.24 (GND), XA1.26 (GND), XA1.28 (GND), XA1.30 (GND), XA1.32 (GND), XA1.38 (GND), XA1.40 (GND); also elsewhere on the board
GNDA: XA1.7 (GNDA), XA1.8 (GNDA), XA1.10 (GNDA), XA1.12 (GNDA), XA1.14 (GNDA), XA1.16 (GNDA), XA1.18 (GNDA)

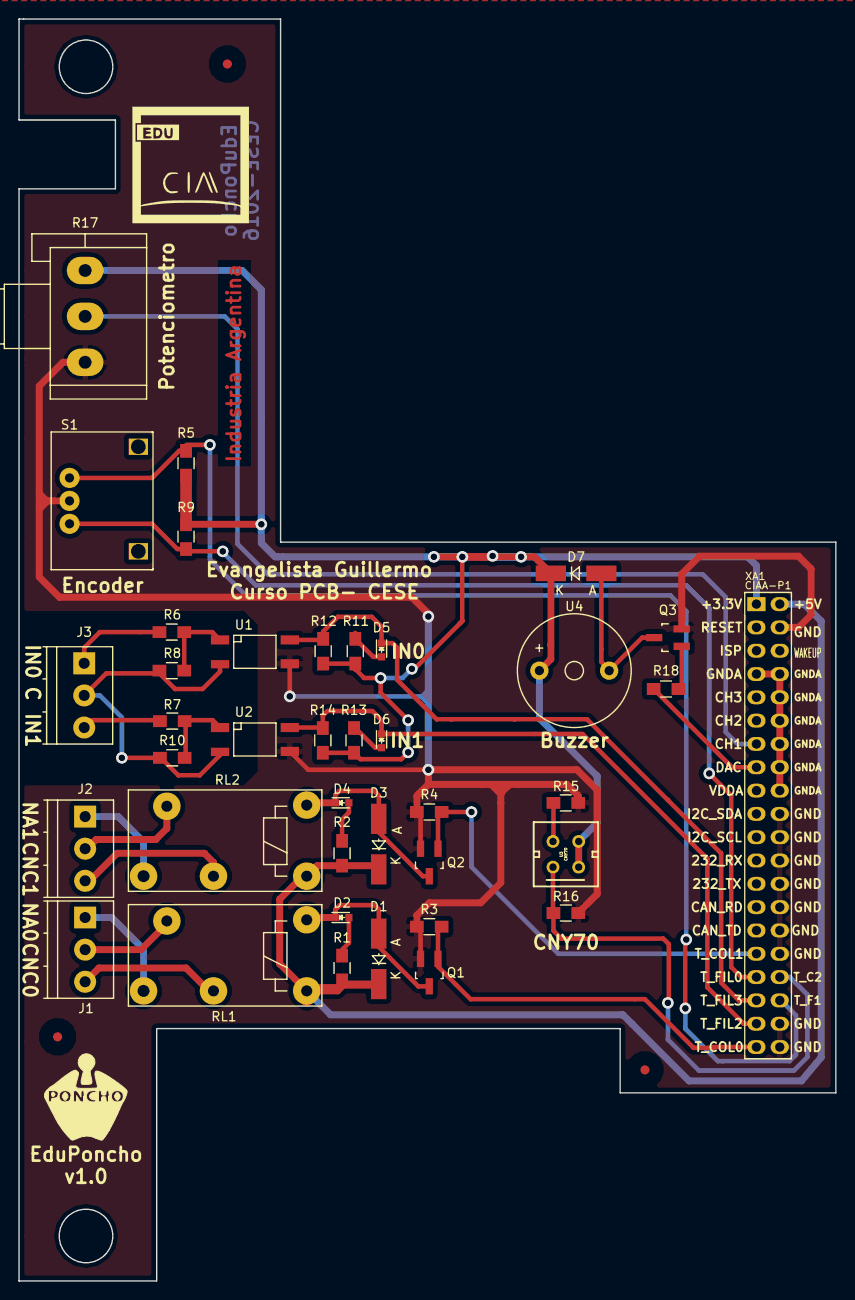
[picture p242: board EduPoncho.kicad_pcb from above]

Board: 2 copper layers, 89.0 x 137.5 mm, 42 parts (0 on the bottom side), 33 nets.

Other parts of the board:
F?: Fiducial_1mm
F?#2, F?#3: Fiducial_1mm
