ciaa/Ponchos/L298/Motor_Board.kicad_pcb

## KiCad design L298/Motor_Board.kicad_pcb (2016-10-24)

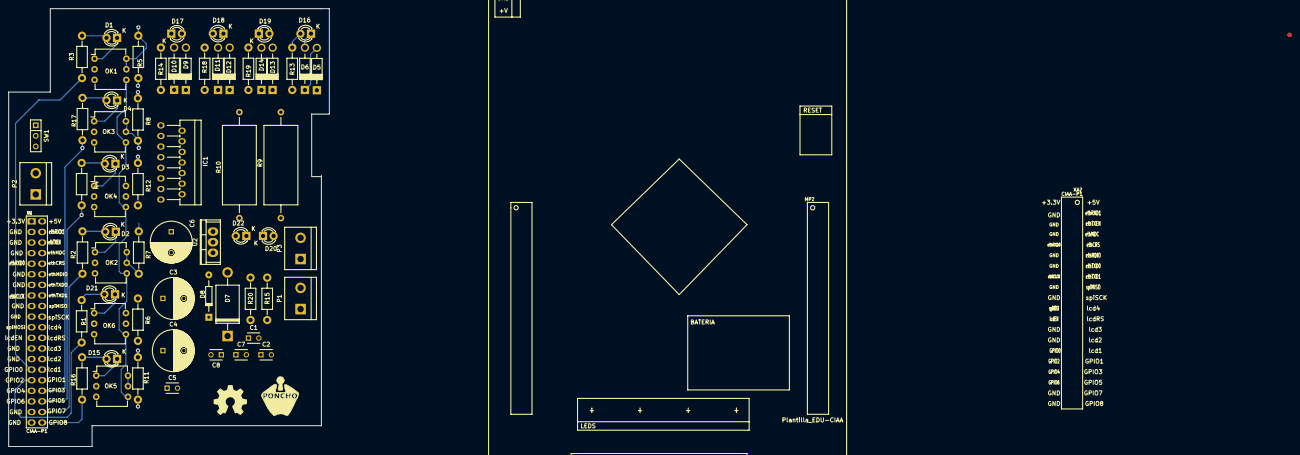
[picture p243: board Motor_Board.kicad_pcb from above]

Board: 2 copper layers, 76.9 x 105.0 mm, 69 parts (0 on the bottom side), 34 nets.

Parts:
C1, C2, C5, C7, C8: 0.1uF; C_Disc_D3_P2.5
C3, C4: 470uF; C_Radial_D10_L25_P5
C6: 220uF; C_Radial_D10_L16_P5
D1, D2, D3, D4, D15, D16, D17, D18, D19, D20, D21, D22: Led_Small; LED-3MM
D5, D6, D9, D10, D11, D12, D13, D14: 1N4007; Diode_DO-41_SOD81_Horizontal_RM10
D7: 1N5822; Diode_DO-201AD_Horizontal_RM15
D8: 1N4734A; Diode_DO-35_SOD27_Horizontal_RM10
F1, F2, F3: FIDUCIAL; Fiducial_1mm
G101: Logo_OSHWA
IC1: L298; Multiwatt_15_Vertical
MP?: Plantilla_EDU-CIAA
OK1, OK2, OK3, OK4, OK5, OK6: 4N35; DIP-6_W7.62mm
P1: Motor A; bornier2
P2: VDD Motor; bornier2
P3: Motor B; bornier2
R1, R2, R3, R4, R15, R16, R17: 330; Resistor_Horizontal_RM10mm
R5, R6, R7, R8, R11, R12, R13, R14, R18, R19, R20: 1K; Resistor_Horizontal_RM10mm
R9, R10: 0.5; Resistor_Ceramic_Horizontal_L19mm-W8mm-H8mm-p25mm
SW1: Switch_SPDT_x2; SW_Micro_SPST
U2: 7805; TO-220
XA1: Conn_Poncho2P_2x_20x2; Conn_Poncho_Izquierda
XA?: Plantilla_Poncho_Izquierda; Plantilla_Poncho_Plantilla_Poncho_Izquierda

Connections:
/ENA: IC1.6, OK6.5, OK6.6, R6.2
/ENB: IC1.11, OK5.5, OK5.6, R11.2
/IN1: IC1.5, OK1.5, OK1.6, R5.1
/IN2: IC1.7, OK2.5, OK2.6, R7.2
/IN3: IC1.10, OK3.5, OK3.6, R8.2
/IN4: IC1.12, OK4.5, OK4.6, R12.2
/OUT1: IC1.2, P1.1, R13.1
/OUT2: IC1.3, P1.2, R14.1
/OUT3: IC1.13, P3.1, R18.1
/OUT4: IC1.14, P3.2, R19.1
GNDA: C1.2, C2.2, C3.2, C4.2, C5.2, C6.2, C7.2, C8.2, D16.1, D17.1, D18.1, D19.1, D20.1, D20.2, D22.1, IC1.8, OK1.4, OK2.4, OK3.4, OK4.4, OK5.4, OK6.4, P2.1, R9.2, R10.2, R15.1
unnamed: D1.1, OK1.1
unnamed: D1.2, R3.1
unnamed: D2.1, OK2.1
unnamed: D2.2, R2.1
unnamed: D3.1, OK4.1
unnamed: D3.2, R4.1
unnamed: D4.1, OK3.1
unnamed: D4.2, R17.1
unnamed: D15.1, OK5.1
unnamed: D15.2, R16.1
unnamed: D16.2, R13.2
unnamed: D17.2, R14.2
unnamed: D18.2, R18.2
unnamed: D19.2, R19.2
unnamed: D21.1, OK6.1
unnamed: D21.2, R1.1
unnamed: D22.2, R20.1
unnamed: IC1.1, R9.1
unnamed: IC1.15, R10.1
unnamed: OK1.2, OK2.2, OK3.2, OK4.2, OK5.2, OK6.2
unnamed: P2.2, SW1.2
VCC: C2.1, C3.1, C4.1, C5.1, C8.1, IC1.4, R20.2
VDD: C1.1, C6.1, C7.1, IC1.9, R5.2, R6.1, R7.1, R8.1, R11.1, R12.1, R15.2
