ciaa/Ponchos/ethernet_LAN8720A_v2/ethernet_LAN8720A_v2.kicad_pcb

## KiCad design ethernet_LAN8720A_v2/ethernet_LAN8720A_v2.kicad_pcb (2016-10-17)

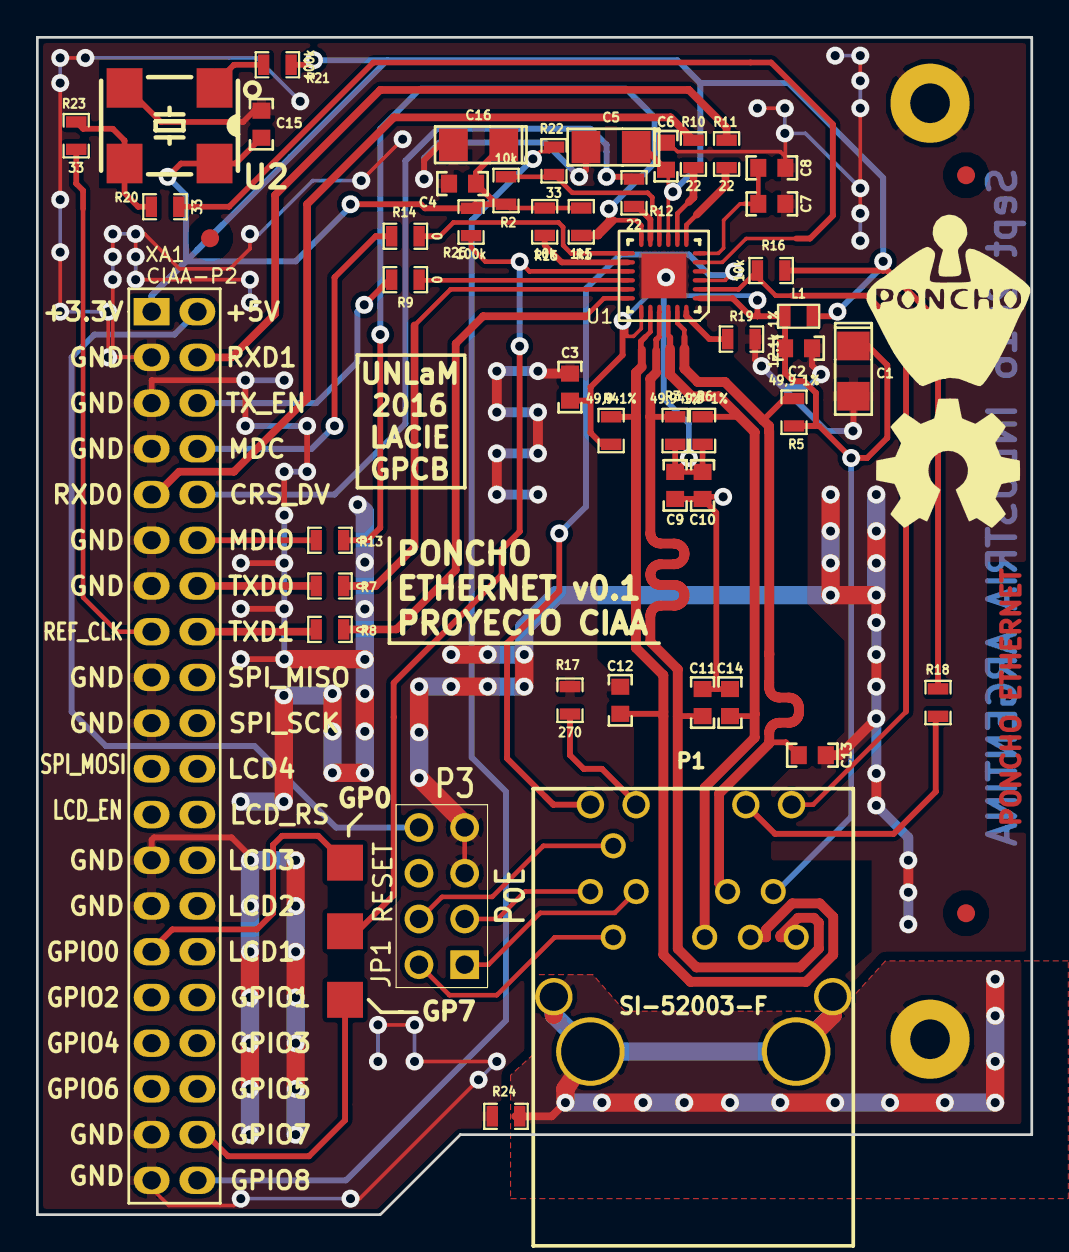
[picture p244: board ethernet_LAN8720A_v2.kicad_pcb from above]

Board: 2 copper layers, 55.2 x 65.4 mm, 54 parts (0 on the bottom side), 45 nets.

Parts:
C1, C5, C16: 10uF; c_1206_tantalio_2
C2, C3, C6: 10nF; c_0603v2
C4, C9, C10, C15: 100nF; c_0603v2
C7: 470pF; c_0603v2
C8: 1uF; c_0603v2
C11, C12, C13, C14: 18pF; c_0603v2
FID1, FID2, FID3: FIDUCIAL; Fiducial_1mm_Dia_2.54mm_Outer_CopperTop
G101: Logo_OSHWA
JP1: JUMPER3; NetTie-II_SMD
L1: FBEAD 22; SM0603
MH1, MH2: MOUNTING-HOLE; MountingHole_2.2mm_M2_Pad
P1: SI-52003-F; RJ45_SI-52003-F_PoE_ETH
P3: PoE; PIN_ARRAY_4X2
R1: 1k5; SM0603_Resistor
R2, R15, R16: 10k; SM0603_Resistor
R3, R4, R5, R6: 49,9 1%; SM0603_Resistor
R7, R8, R9, R13, R14, R24: 0; SM0603_Resistor
R10, R11, R12: 22; SM0603_Resistor
R17, R18: 270; SM0603_Resistor
R19: 12.1k 1%; SM0603_Resistor
R20, R22, R23: 33; SM0603_Resistor
R21, R25: 100k; SM0603_Resistor
U1: LAN8720A-CP; QFN24
U2: 50MHZ; Oscillator_7.0x5.0mm
XA1: Conn_Poncho2P_2x_20x2; Conn_Poncho_Izquierdo

Connections:
+3.3V: C4.1, C5.1, C6.1, C15.1, C16.1, L1.1, R1.1, R2.1, R15.1, R16.1, R18.2, R21.2, R25.1, U1.9, U2.4, XA1.41
+5V: P3.8, XA1.42
/Circuito Principal/CHASIS: MH1.1, P1.6, P1.7, P1.16, P1.17, R24.1
/Circuito Principal/CRS: R12.1, XA1.50
/Circuito Principal/GPIO0: JP1.3, XA1.69
/Circuito Principal/GPIO7: JP1.1, XA1.78
/Circuito Principal/GPIO8: R22.1, XA1.80
/Circuito Principal/LED_100M: P1.15, R16.2, U1.2
/Circuito Principal/LED_LINK: P1.12, U1.3
/Circuito Principal/MDC: R14.1, XA1.48
/Circuito Principal/MDIO: R13.1, XA1.52
/Circuito Principal/PHY_nRESET: JP1.2, R25.2, U1.15
/Circuito Principal/RCLK: R23.2, XA1.55
/Circuito Principal/RXD0: R10.1, XA1.49
/Circuito Principal/RXD1: R11.1, XA1.44
/Circuito Principal/Rx_N: C14.1, P1.5, R6.2, U1.22
/Circuito Principal/Rx_P: C13.1, P1.4, R5.2, U1.23
/Circuito Principal/TXD0: R7.1, XA1.54
/Circuito Principal/TXD1: R8.1, XA1.56
/Circuito Principal/TXEN: R9.1, XA1.46
/Circuito Principal/Tx_N: C12.1, P1.3, R4.2, U1.20
/Circuito Principal/Tx_P: C11.1, P1.1, R3.2, U1.21
GND: C1.2, C2.2, C3.2, C4.2, C5.2, C6.2, C7.2, C8.2, C9.2, C10.2, C11.2, C12.2, C13.2, C14.2, C15.2, C16.2, MH2.1, P3.5, P3.7, R17.1, R19.2, R24.2, U1.GND, U2.2, XA1.43, XA1.45, XA1.47, XA1.51, XA1.53, XA1.57, XA1.59, XA1.65, XA1.67, XA1.77, XA1.79
unnamed: C1.1, C2.1, C3.1, C9.1, C10.1, L1.2, P1.2, R3.1, R4.1, R5.1, R6.1, U1.1, U1.19
unnamed: C7.1, C8.1, U1.6
unnamed: P1.8, P3.1
unnamed: P1.9, P3.2
unnamed: P1.10, P3.3
unnamed: P1.11, P3.4
unnamed: P1.13, R17.2
unnamed: P1.14, R18.1
unnamed: R1.2, R13.2, U1.12
unnamed: R2.2, R22.2, U1.10
unnamed: R7.2, U1.17
unnamed: R8.2, U1.18
unnamed: R9.2, U1.16
unnamed: R10.2, U1.8
unnamed: R11.2, U1.7
unnamed: R12.2, U1.11
unnamed: R14.2, U1.13
unnamed: R15.2, U1.14
unnamed: R19.1, U1.24
unnamed: R20.1, R23.1, U2.3
unnamed: R20.2, U1.5
unnamed: R21.1, U2.1
