ciaa/Ponchos/Osciloscopio/Oscilloscopio.kicad_pcb

## KiCad design Osciloscopio/Oscilloscopio.kicad_pcb (2016-10-17)

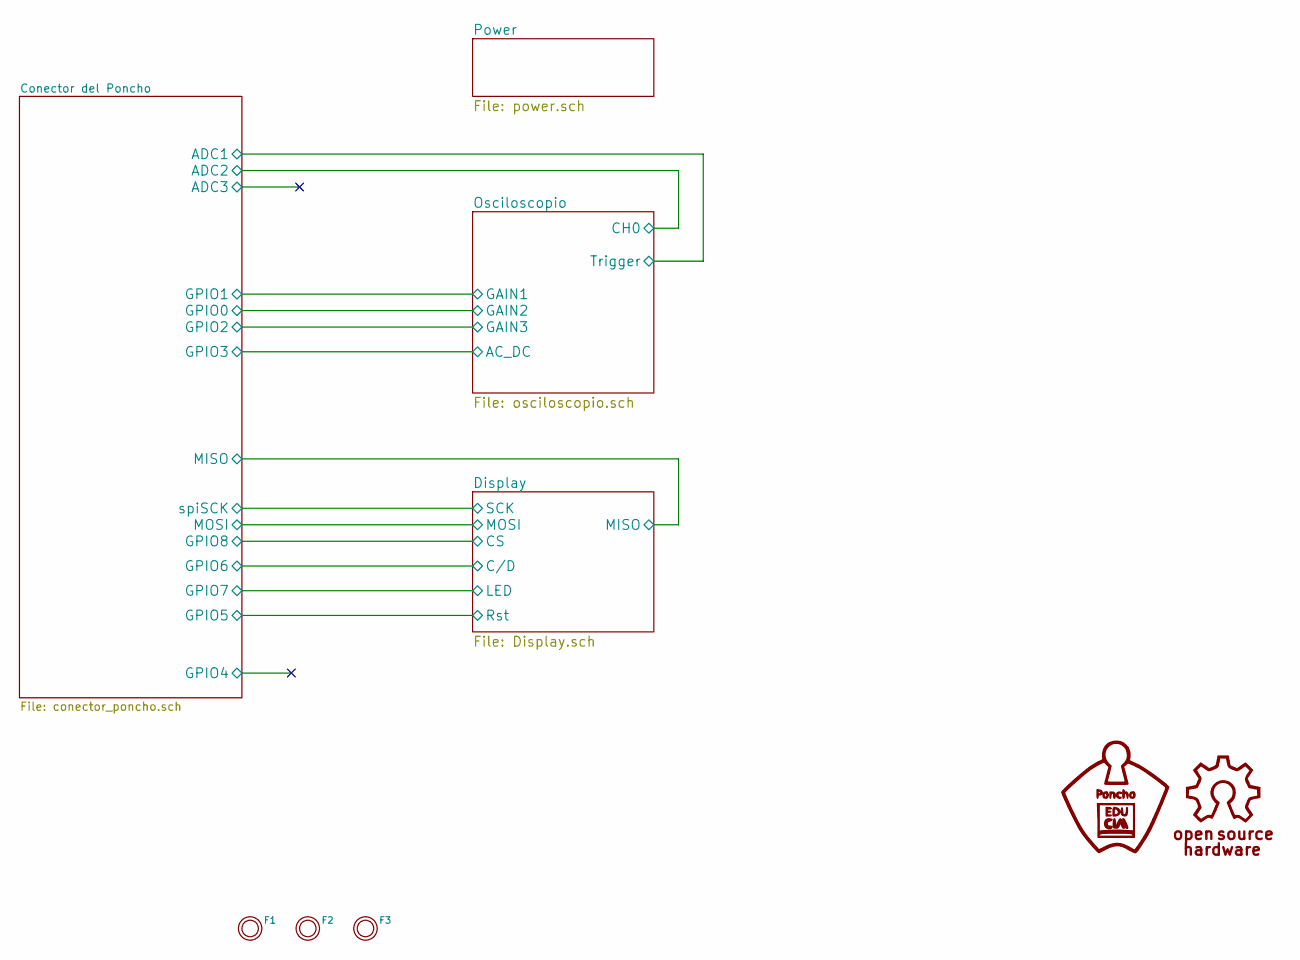
[picture p245: schematic Oscilloscopio.sch, Poncho Osciloscopio]

Parts:
F1, F2, F3: FIDUCIAL; Fiducial_1mm

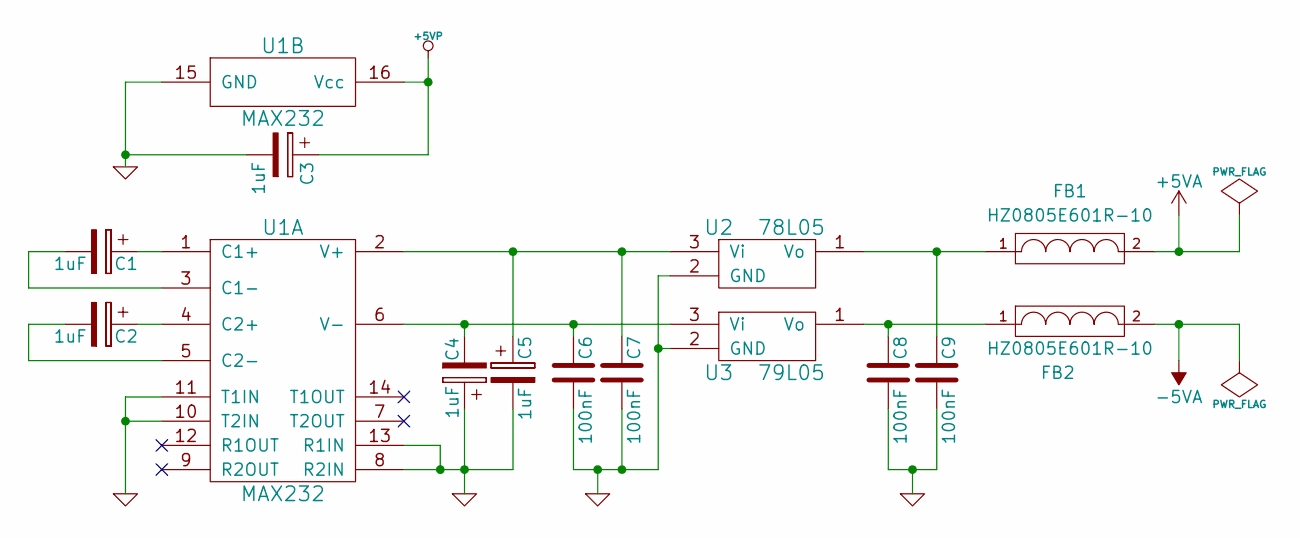
[picture p246: schematic power.sch, Poncho Osciloscopio]

Parts:
C1, C2, C3, C4, C5: 1uF; C_Radial_D5_L11_P2; Digikey# 732-8851-1-ND
C6, C7, C8, C9: 100nF; C_0805_HandSoldering; Digikey# 1276-6468-1-ND
FB1, FB2: HZ0805E601R-10; R_0805_HandSoldering; Digikey# 240-2399-1-ND
U1: MAX232; DIP-16_W7.62mm_LongPads; Digikey# 296-1402-5-ND
U2: 78L05; TO-92_Inline_Wide; Digikey# 296-1365-1-ND
U3: 79L05; TO-92_Inline_Wide; Digikey# 296-31456-1-ND

Connections:
+5VA: FB1.2; also elsewhere on the board
+5VP: C3.1, U1.16 (Vcc); also elsewhere on the board
-5VA: FB2.2; also elsewhere on the board
GND: C3.2, C4.1, C5.2, C6.2, C7.2, C8.2, C9.2, U1.8 (R2IN), U1.10 (T2IN), U1.11 (T1IN), U1.13 (R1IN), U1.15 (GND), U2.2 (GND), U3.2 (GND); also elsewhere on the board
unnamed: C1.1, U1.1 (C1+)
unnamed: C1.2, U1.3 (C1-)
unnamed: C2.1, U1.4 (C2+)
unnamed: C2.2, U1.5 (C2-)
unnamed: C4.2, C6.1, U1.6 (V-), U3.3 (Vi)
unnamed: C5.1, C7.1, U1.2 (V+), U2.3 (Vi)
unnamed: C8.1, FB2.1, U3.1 (Vo)
unnamed: C9.1, FB1.1, U2.1 (Vo)

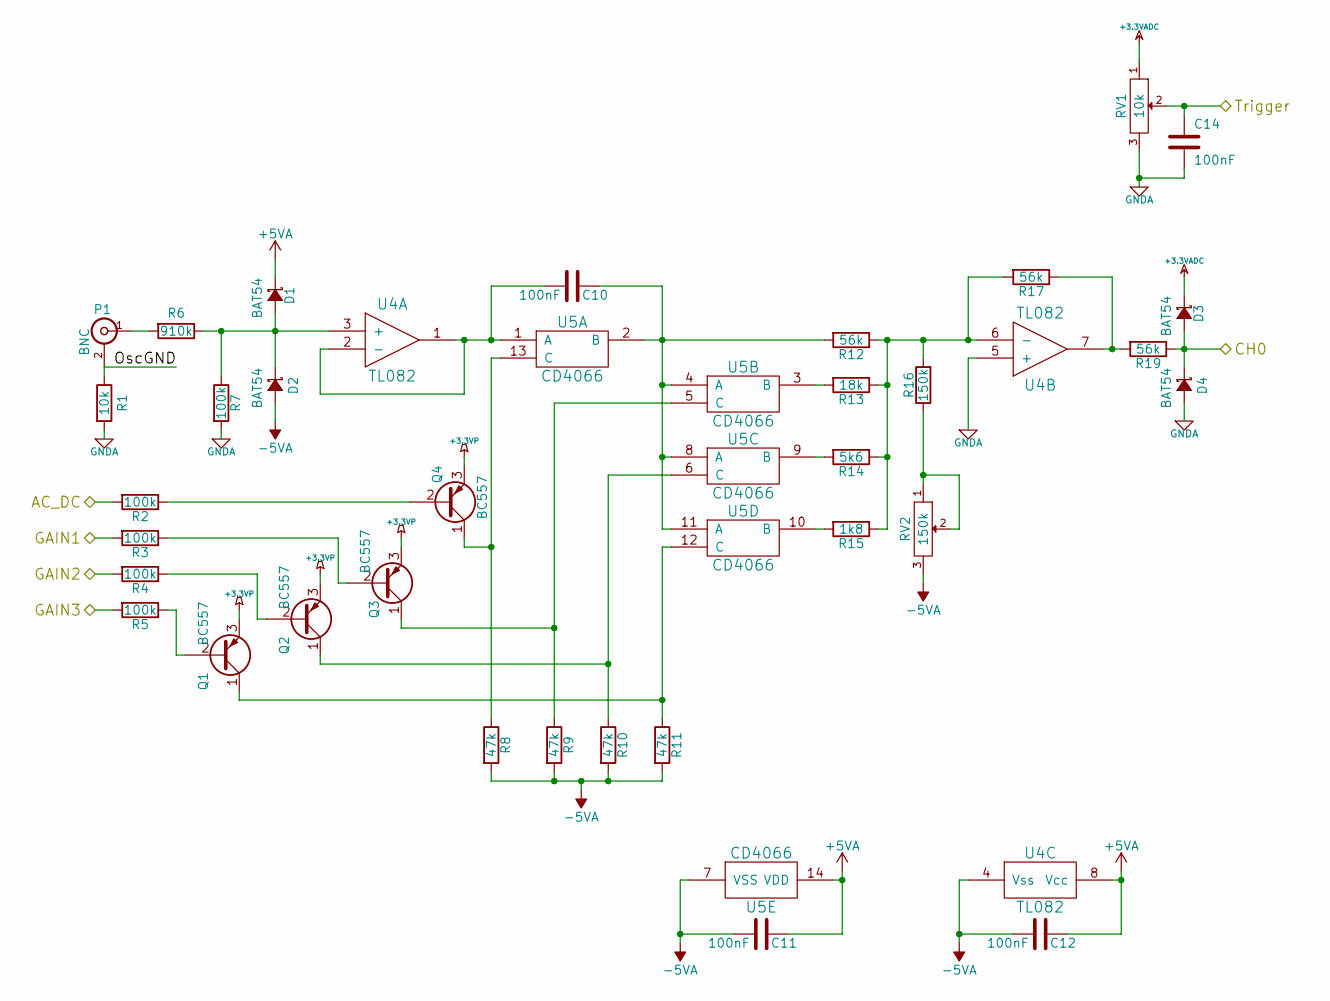
[picture p247: schematic osciloscopio.sch, Poncho Osciloscopio]

Parts:
C10, C11, C12, C14: 100nF; C_0805_HandSoldering; Digikey# 1276-6468-1-ND
D1, D2, D3, D4: BAT54; SOT-323; Digikey# 568-11592-1-ND
P1: BNC; BNC_Socket_TYCO-AMP_LargePads; Digikey# A32244-ND
Q1, Q2, Q3, Q4: BC557; TO-92_Inline_Wide; Digikey# BC557BTACT-ND
R1: 10k; R_0805_HandSoldering; Digikey# RMCF0805JG10K0CT-ND
R2, R3, R4, R5, R7: 100k; R_0805_HandSoldering; Digikey# RMCF0805JT100KCT-ND
R6: 910k; R_0805_HandSoldering; Digikey# RMCF0805JT910KCT-ND
R8, R9, R10, R11: 47k; R_0805_HandSoldering; Digikey# RMCF0805JT47K0CT-ND
R12, R17, R19: 56k; R_0805_HandSoldering; Digikey# RMCF0805JT56K0CT-ND
R13: 18k; R_0805_HandSoldering; Digikey# RMCF0805JT18K0CT-ND
R14: 5k6; R_0805_HandSoldering; Digikey# RMCF0805JT5K60CT-ND
R15: 1k8; R_0805_HandSoldering; Digikey# RMCF0805JT1K80CT-ND
R16: 150k; R_0805_HandSoldering; Digikey# RMCF0805JT150KCT-ND
RV1: 10k; Potentiometer_Alps-RK16-single; Mouser# 688-RK1631110TBK
RV2: 150k; Potentiometer_Bourns_3296W_3-8Zoll_Inline_ScrewUp; Digikey# 490-2889-ND
U4: TL082; DIP-8_W7.62mm_LongPads; Digikey# 296-1781-5-ND
U5: CD4066; DIP-14_W7.62mm_LongPads; Digikey# 296-2061-5-ND

Connections:
+3.3VADC: D3.1 (K), RV1.1; also elsewhere on the board
+3.3VP: Q1.3 (E), Q2.3 (E), Q3.3 (E), Q4.3 (E); also elsewhere on the board
+5VA: C11.1, C12.1, D1.1 (K), U4.8 (Vcc), U5.14 (VDD); also elsewhere on the board
-5VA: C11.2, C12.2, D2.2 (A), R8.2, R9.2, R10.2, R11.2, RV2.3, U4.4 (Vss), U5.7 (VSS); also elsewhere on the board
/Conector del Poncho/ADC1: C14.1, RV1.2; also elsewhere on the board
/Conector del Poncho/ADC2: D3.2 (A), D4.1 (K), R19.1; also elsewhere on the board
/Osciloscopio/AC_DC: R2.2; also elsewhere on the board
/Osciloscopio/GAIN1: R3.2; also elsewhere on the board
/Osciloscopio/GAIN2: R4.2; also elsewhere on the board
/Osciloscopio/GAIN3: R5.2; also elsewhere on the board
/Osciloscopio/OscGND: P1.2 (Ext), R1.1
GNDA: C14.2, D4.2 (A), R1.2, R7.2, RV1.3, U4.5 (+); also elsewhere on the board
unnamed: C10.1, R12.2, U5.2 (B), U5.4 (A), U5.8 (A), U5.11 (A)
unnamed: C10.2, U4.1, U4.2 (-), U5.1 (A)
unnamed: D1.2 (A), D2.1 (K), R6.1, R7.1, U4.3 (+)
unnamed: P1.1 (In), R6.2
unnamed: Q1.1 (C), R11.1, U5.12 (C)
unnamed: Q1.2 (B), R5.1
unnamed: Q2.1 (C), R10.1, U5.6 (C)
unnamed: Q2.2 (B), R4.1
unnamed: Q3.1 (C), R9.1, U5.5 (C)
unnamed: Q3.2 (B), R3.1
unnamed: Q4.1 (C), R8.1, U5.13 (C)
unnamed: Q4.2 (B), R2.1
unnamed: R12.1, R13.1, R14.1, R15.1, R16.2, R17.2, U4.6 (-)
unnamed: R13.2, U5.3 (B)
unnamed: R14.2, U5.9 (B)
unnamed: R15.2, U5.10 (B)
unnamed: R16.1, RV2.1, RV2.2
unnamed: R17.1, R19.2, U4.7

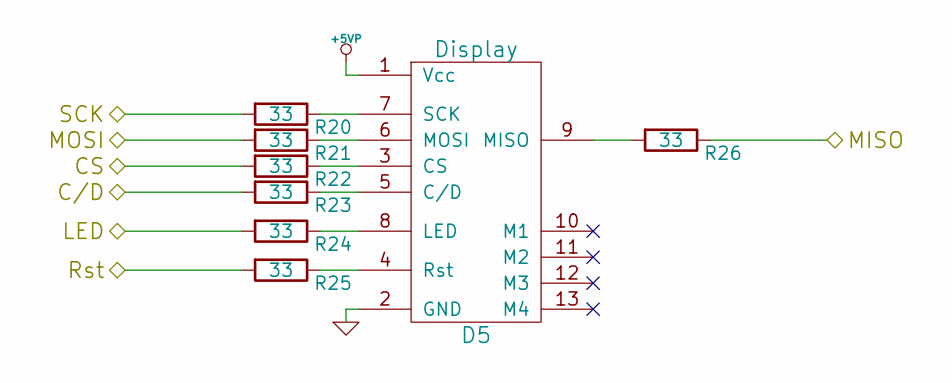
[picture p248: schematic Display.sch, Poncho Osciloscopio]

Parts:
D5: Display; Digikey# S7042-ND
R20, R21, R22, R23, R24, R25, R26: 33; R_0805_HandSoldering; Digikey# RMCF0805JT33R0CT-ND

Connections:
+5VP: D5.1 (Vcc); also elsewhere on the board
/Conector del Poncho/GPIO5: R25.2; also elsewhere on the board
/Conector del Poncho/GPIO7: R24.2; also elsewhere on the board
/Conector del Poncho/MISO: R26.1; also elsewhere on the board
/Conector del Poncho/MOSI: R21.2; also elsewhere on the board
/Display/C/D: R23.2; also elsewhere on the board
/Display/CS: R22.2; also elsewhere on the board
/Display/SCK: R20.2; also elsewhere on the board
GND: D5.2 (GND); also elsewhere on the board
unnamed: D5.3 (CS), R22.1
unnamed: D5.4 (Rst), R25.1
unnamed: D5.5 (C/D), R23.1
unnamed: D5.6 (MOSI), R21.1
unnamed: D5.7 (SCK), R20.1
unnamed: D5.8 (LED), R24.1
unnamed: D5.9 (MISO), R26.2

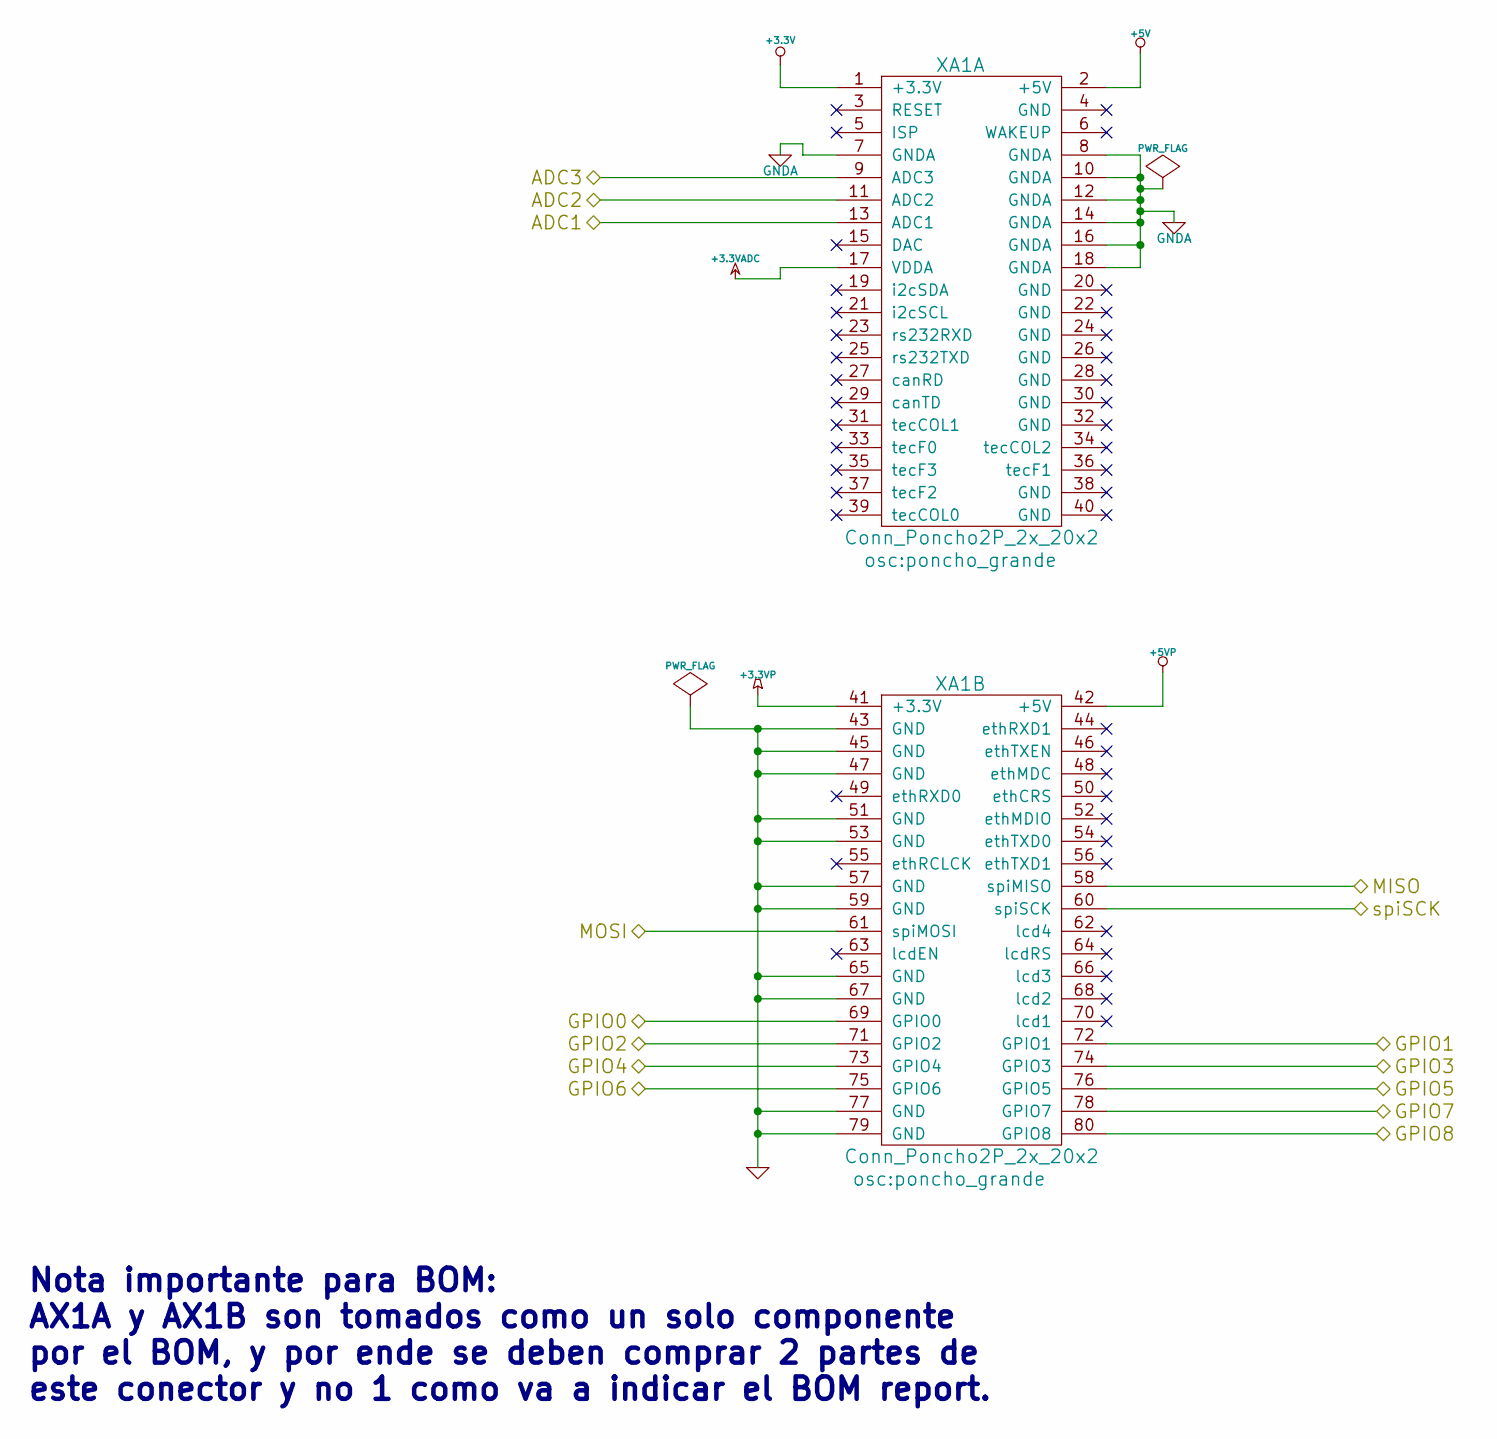
[picture p249: schematic conector_poncho.sch, Poncho Osciloscopio]

Parts:
XA1: Conn_Poncho2P_2x_20x2; poncho_grande; Digikey# S6104-ND

Connections:
+3.3V: XA1.1 (+3.3V)
+3.3VADC: XA1.17 (VDDA); also elsewhere on the board
+3.3VP: XA1.41 (+3.3V); also elsewhere on the board
+5V: XA1.2 (+5V)
+5VP: XA1.42 (+5V); also elsewhere on the board
/Conector del Poncho/ADC1: XA1.13 (ADC1); also elsewhere on the board
/Conector del Poncho/ADC2: XA1.11 (ADC2); also elsewhere on the board
/Conector del Poncho/ADC3: XA1.9 (ADC3)
/Conector del Poncho/GPIO4: XA1.73 (GPIO4)
/Conector del Poncho/GPIO5: XA1.76 (GPIO5); also elsewhere on the board
/Conector del Poncho/GPIO7: XA1.78 (GPIO7); also elsewhere on the board
/Conector del Poncho/MISO: XA1.58 (spiMISO); also elsewhere on the board
/Conector del Poncho/MOSI: XA1.61 (spiMOSI); also elsewhere on the board
/Display/C/D: XA1.75 (GPIO6); also elsewhere on the board
/Display/CS: XA1.80 (GPIO8); also elsewhere on the board
/Display/SCK: XA1.60 (spiSCK); also elsewhere on the board
/Osciloscopio/AC_DC: XA1.74 (GPIO3); also elsewhere on the board
/Osciloscopio/GAIN1: XA1.72 (GPIO1); also elsewhere on the board
/Osciloscopio/GAIN2: XA1.69 (GPIO0); also elsewhere on the board
/Osciloscopio/GAIN3: XA1.71 (GPIO2); also elsewhere on the board
GND: XA1.43 (GND), XA1.45 (GND), XA1.47 (GND), XA1.51 (GND), XA1.53 (GND), XA1.57 (GND), XA1.59 (GND), XA1.65 (GND), XA1.67 (GND), XA1.77 (GND), XA1.79 (GND); also elsewhere on the board
GNDA: XA1.7 (GNDA), XA1.8 (GNDA), XA1.10 (GNDA), XA1.12 (GNDA), XA1.14 (GNDA), XA1.16 (GNDA), XA1.18 (GNDA); also elsewhere on the board

Notes on the sheet:
Nota importante para BOM: AX1A y AX1B son tomados como un solo componente por el BOM, y por ende se deben comprar 2 partes de este conector y no 1 como va a indicar el BOM report.

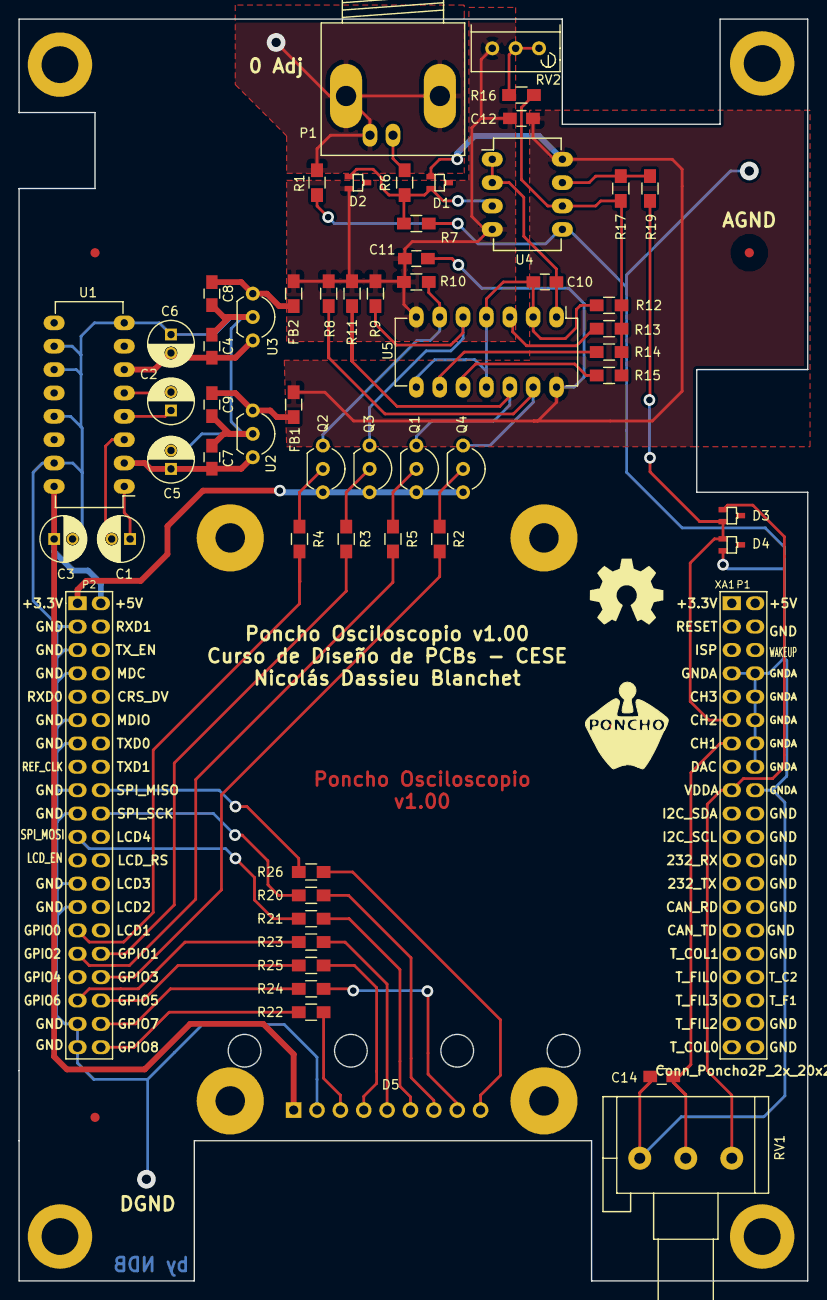
[picture p250: board Oscilloscopio.kicad_pcb from above]

Board: 2 copper layers, 85.7 x 137.2 mm, 62 parts (0 on the bottom side), 54 nets.

Other parts of the board:
G101: Logo_OSHWA
