ciaa/Ponchos/ECG/ECG_CIAA.kicad_pcb

## KiCad design ECG/ECG_CIAA.kicad_pcb (2016-08-24)

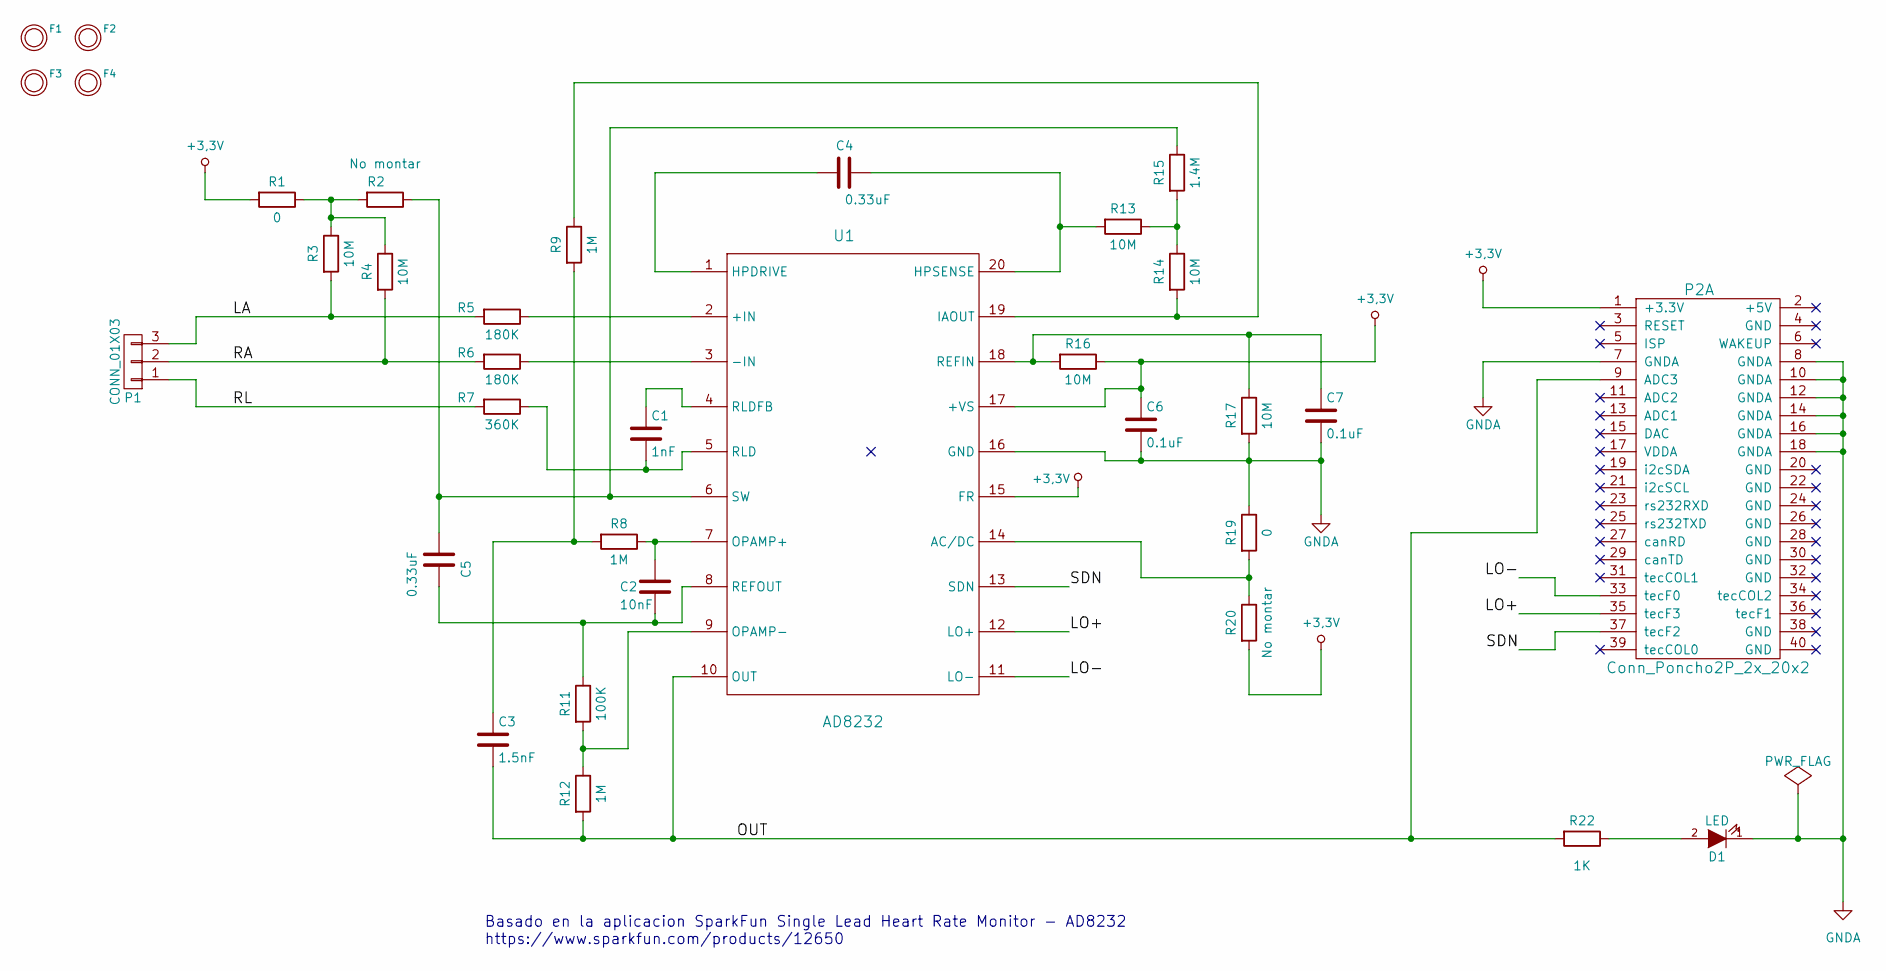
[picture p251: schematic ECG_CIAA.sch, ECG CIAA]

Parts:
C1: 1nF; C_0805; Digikey# 732-7813-2-ND
C2: 10nF; C_0805; Digikey# 732-8021-2-ND
C3: 1.5nF; C_0805; Digikey# 732-8018-2-ND
C4, C5: 0.33uF; C_0805; Digikey# 732-7651-2-ND
C6, C7: 0.1uF; C_0805; Digikey# 399-7999-2-ND
D1: LED; LED_0805; Digikey# 475-1410-2-ND
F1, F2, F3, F4: FIDUCIAL; Fiducial_1mm
P1: CONN_01X03; bornier3; Digikey# ED2601-ND
P2: Conn_Poncho2P_2x_20x2; Conn_Poncho_Derecha; Digikey# 609-2589-ND
R1, R19: 0; R_0805; Digikey# 311-0.0ARTR-ND
R2, R20: No montar; R_0805
R3, R4, R13, R14, R16, R17: 10M; R_0805; Digikey# RMCF0805JT10M0TR-ND
R5, R6: 180K; R_0805; Digikey# 311-180KARTR-ND
R7: 360K; R_0805; Digikey# 311-360KCRTR-ND
R8, R12: 1M; R_0805; Digikey# 311-1.00MCRTR-ND
R9: 1M; R_0805; Digikey# RHM1.0MBUTR-ND
R11: 100K; R_0805
R15: 1.4M; R_0805; Digikey# P1.4BTTR-ND
R22: 1K; R_0805; Digikey# 311-1.0KARTR-ND
U1: AD8232

Connections:
+3.3V: C6.1, P2.1 (+3.3V), R1.2, R16.1, R20.2, U1.15 (FR), U1.17 (+VS)
/LA: P1.3, R3.2, R5.2
/LO+: P2.35 (tecF3), U1.12 (LO+)
/LO-: P2.33 (tecF0), U1.11 (LO-)
/OUT: C3.2, P2.9 (ADC3), R12.2, R22.2, U1.10 (OUT)
/RA: P1.2, R4.2, R6.2
/RL: P1.1, R7.2
/SDN: P2.37 (tecF2), U1.13 (SDN)
GNDA: C6.2, C7.2, D1.1 (K), P2.7 (GNDA), P2.8 (GNDA), P2.10 (GNDA), P2.12 (GNDA), P2.14 (GNDA), P2.16 (GNDA), P2.18 (GNDA), R17.2, R19.1, U1.16 (GND)
unnamed: C1.1, U1.4 (RLDFB)
unnamed: C1.2, R7.1, U1.5 (RLD)
unnamed: C2.1, R8.1, U1.7 (OPAMP+)
unnamed: C2.2, C5.1, R11.1, U1.8 (REFOUT)
unnamed: C3.1, R8.2, R9.2
unnamed: C4.1, R13.2, U1.20 (HPSENSE)
unnamed: C4.2, U1.1 (HPDRIVE)
unnamed: C5.2, R2.1, R15.1, U1.6 (SW)
unnamed: C7.1, R16.2, R17.1, U1.18 (REFIN)
unnamed: D1.2 (A), R22.1
unnamed: R1.1, R2.2, R3.1, R4.1
unnamed: R5.1, U1.2 (+IN)
unnamed: R6.1, U1.3 (-IN)
unnamed: R11.2, R12.1, U1.9 (OPAMP-)
unnamed: R13.1, R14.1, R15.2
unnamed: R9.1, R14.2, U1.19 (IAOUT)
unnamed: R19.2, R20.1, U1.14 (AC/DC)

Notes on the sheet:
Basado en la aplicacion SparkFun Single Lead Heart Rate Monitor - AD8232 https://www.sparkfun.com/products/12650

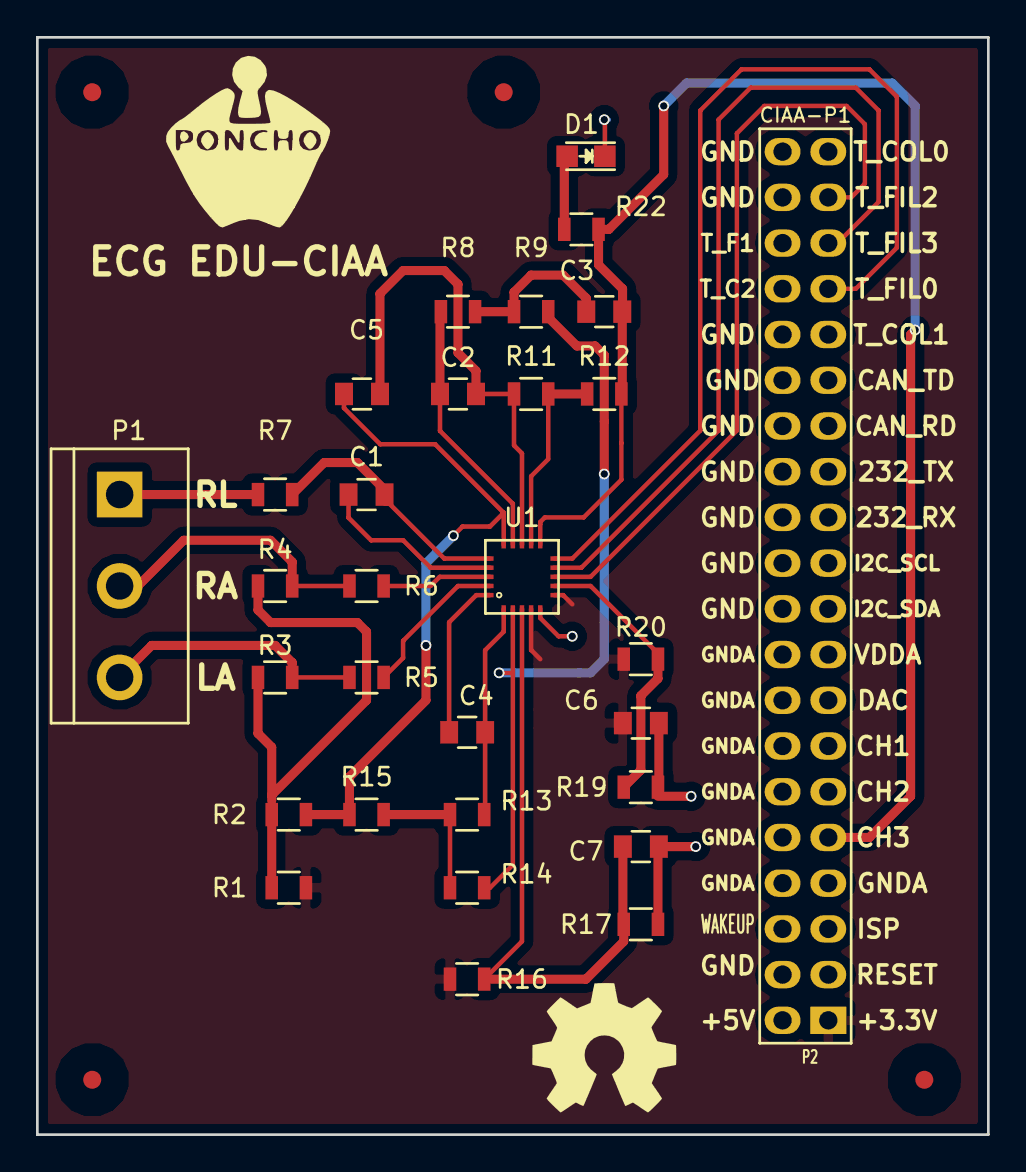
[picture p252: board ECG_CIAA.kicad_pcb from above]

Board: 2 copper layers, 52.8 x 61.0 mm, 35 parts (0 on the bottom side), 26 nets.

Other parts of the board:
G101: Logo_OSHWA
