ciaa/Ponchos/modelos/Basico/basico.kicad_pcb

## KiCad design modelos/Basico/basico.kicad_pcb (2016-08-11)

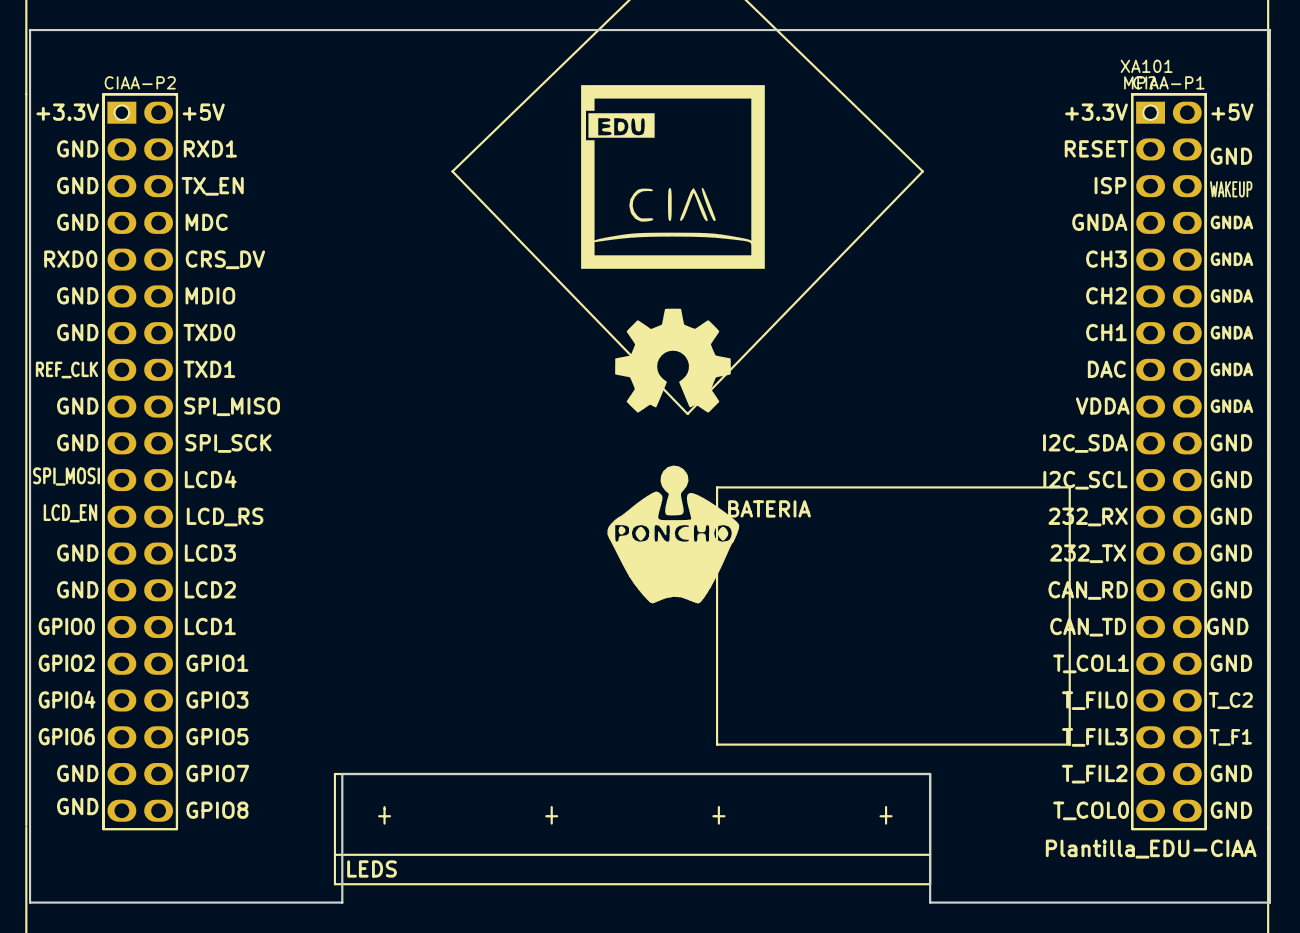
[picture p253: board basico.kicad_pcb from above]

Board: 2 copper layers, 85.7 x 60.3 mm, 3 parts (0 on the bottom side), 4 nets, no tracks yet.

Parts:
G101: Logo_OSHWA
MP?: Plantilla_EDU-CIAA
XA101: Conn_Poncho2P_2x_20x2; Conn_Poncho_SinBorde

Connections:
+3.3VP: XA101.1, XA101.41
+5V: XA101.2, XA101.42
GND: XA101.4, XA101.20, XA101.22, XA101.24, XA101.26, XA101.28, XA101.30, XA101.32, XA101.38, XA101.40, XA101.43, XA101.45, XA101.47, XA101.51, XA101.53, XA101.57, XA101.59, XA101.65, XA101.67, XA101.77, XA101.79
GNDA: XA101.7, XA101.8, XA101.10, XA101.12, XA101.14, XA101.16, XA101.18
