ciaa/Ponchos/Detector_de_caidas/trabajo_final.kicad_pcb

## KiCad design Detector_de_caidas/trabajo_final.kicad_pcb (2016-08-03)

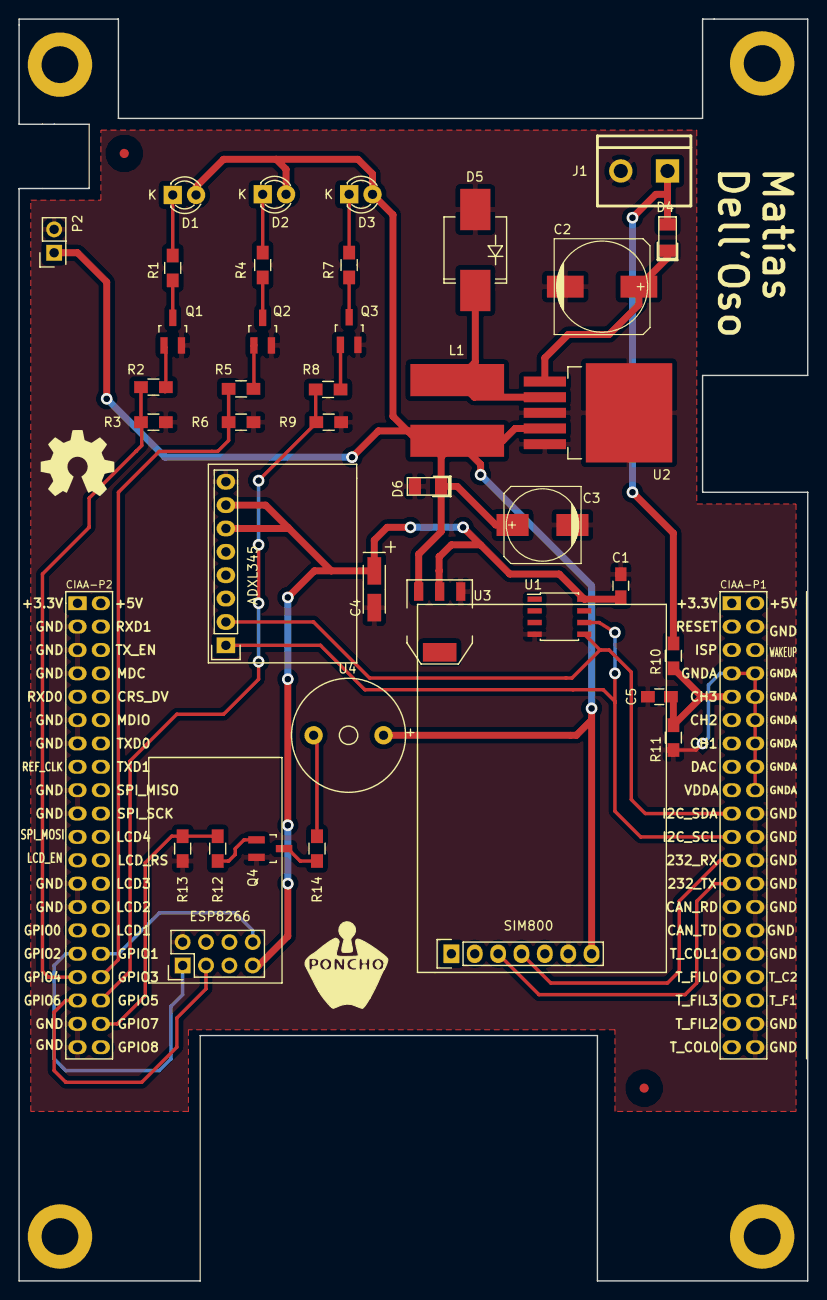
[picture p254: board trabajo_final.kicad_pcb from above]

Board: 2 copper layers, 85.7 x 137.2 mm, 43 parts (0 on the bottom side), 30 nets.

Parts:
ADXL345: CONN_01X08; adxl345
C1, C5: 100nF; C_0805_HandSoldering
C2: 470uF; c2
C3: 330uF; c3
C4: 10uF; TantalC_SizeA_EIA-3216_HandSoldering
D1, D2, D3: LED; LED-3MM
D4: PMEG3020EH; SOD123F
D5: B540C-13-F; SMC_Handsoldering
D6: SMAZ5V6; SOD123F
ESP8266: CONN_02X04; esp8266
F1, F2: FIDUCIAL; Fiducial_1mm
G101: Logo_OSHWA
J1: TB_1X2; bornier2
L1: 47uH; SRN1060
P2: CONN_02X01; Pin_Header_Straight_2x01
Q1, Q2, Q3, Q4: 2N7002; SOT-23_Handsoldering
R1, R4, R7, R14: 680; R_0805_HandSoldering
R2, R5, R8, R12: 10K; R_0805_HandSoldering
R3, R6, R9, R13: 330K; R_0805_HandSoldering
R10: 470K; R_0805_HandSoldering
R11: 270K; R_0805_HandSoldering
SIM800: CONN_01X07; sim800l
U1: 24LC64; SOIC-8_3.9x4.9mm_Pitch1.27mm
U2: LM2596; TO-263-5Lead
U3: NCP1117ST33T3G; SOT-223
U4: Buzzer; Buzzer_12x9.5RM7.6
XA1: Conn_Poncho2P_2x_20x2; Conn_Poncho_Completo

Connections:
/Circuito Principal/ADC3: C5.2, R10.2, R11.1, XA1.9
/Circuito Principal/GPIO3: R5.2, R6.2, XA1.74
/Circuito Principal/GPIO4: R2.2, R3.2, XA1.73
/Circuito Principal/GPIO5: R8.2, R9.2, XA1.76
/Circuito Principal/GPIO6: ESP8266.3, XA1.75
/Circuito Principal/GPIO7: R12.1, R13.1, XA1.78
/Circuito Principal/RS232_RXD: SIM800.4, XA1.23
/Circuito Principal/RS232_TXD: SIM800.3, XA1.25
/Circuito Principal/SCL: ADXL345.1, U1.6, XA1.21
/Circuito Principal/SDA: ADXL345.2, U1.5, XA1.19
/Conector del Poncho/GPIO1: ESP8266.8, XA1.72
/Conector del Poncho/GPIO2: ESP8266.1, XA1.71
GND: ADXL345.8, C1.1, C2.2, C3.2, C4.2, C5.1, D5.1, D6.1, ESP8266.2, J1.2, P2.2, Q1.2, Q2.2, Q3.2, Q4.2, R3.1, R6.1, R9.1, R11.2, R13.2, SIM800.6, U1.4, U2.3, U2.5, U3.1, XA1.4, XA1.7, XA1.8, XA1.10, XA1.12, XA1.14, XA1.16, XA1.18, XA1.20, XA1.22, XA1.24, XA1.26, XA1.28, XA1.30, XA1.32, XA1.38, XA1.40, XA1.43, XA1.45, XA1.47, XA1.51, XA1.53, XA1.57, XA1.59, XA1.65, XA1.67, XA1.77, XA1.79
unnamed: C2.1, D4.2, U2.1
unnamed: D1.1, R1.2
unnamed: D2.1, R4.2
unnamed: D3.1, R7.2
unnamed: D4.1, J1.1, R10.1
unnamed: D5.2, L1.1, U2.2
unnamed: Q1.1, R2.1
unnamed: Q1.3, R1.1
unnamed: Q2.1, R5.1
unnamed: Q2.3, R4.1
unnamed: Q3.1, R8.1
unnamed: Q3.3, R7.1
unnamed: Q4.1, R12.2
unnamed: Q4.3, R14.2
unnamed: R14.1, U4.2
VCC: C3.1, D1.2, D2.2, D3.2, D6.2, L1.2, P2.1, SIM800.7, U2.4, U3.3, U4.1
VDD: ADXL345.6, ADXL345.7, C1.2, C4.1, ESP8266.7, U1.8, U3.2
