ciaa/Ponchos/Audio_amp_mic/Poncho EDU CIAA Amp Audio.kicad_pcb

## KiCad design Audio_amp_mic/Poncho EDU CIAA Amp Audio.kicad_pcb (2016-08-03)

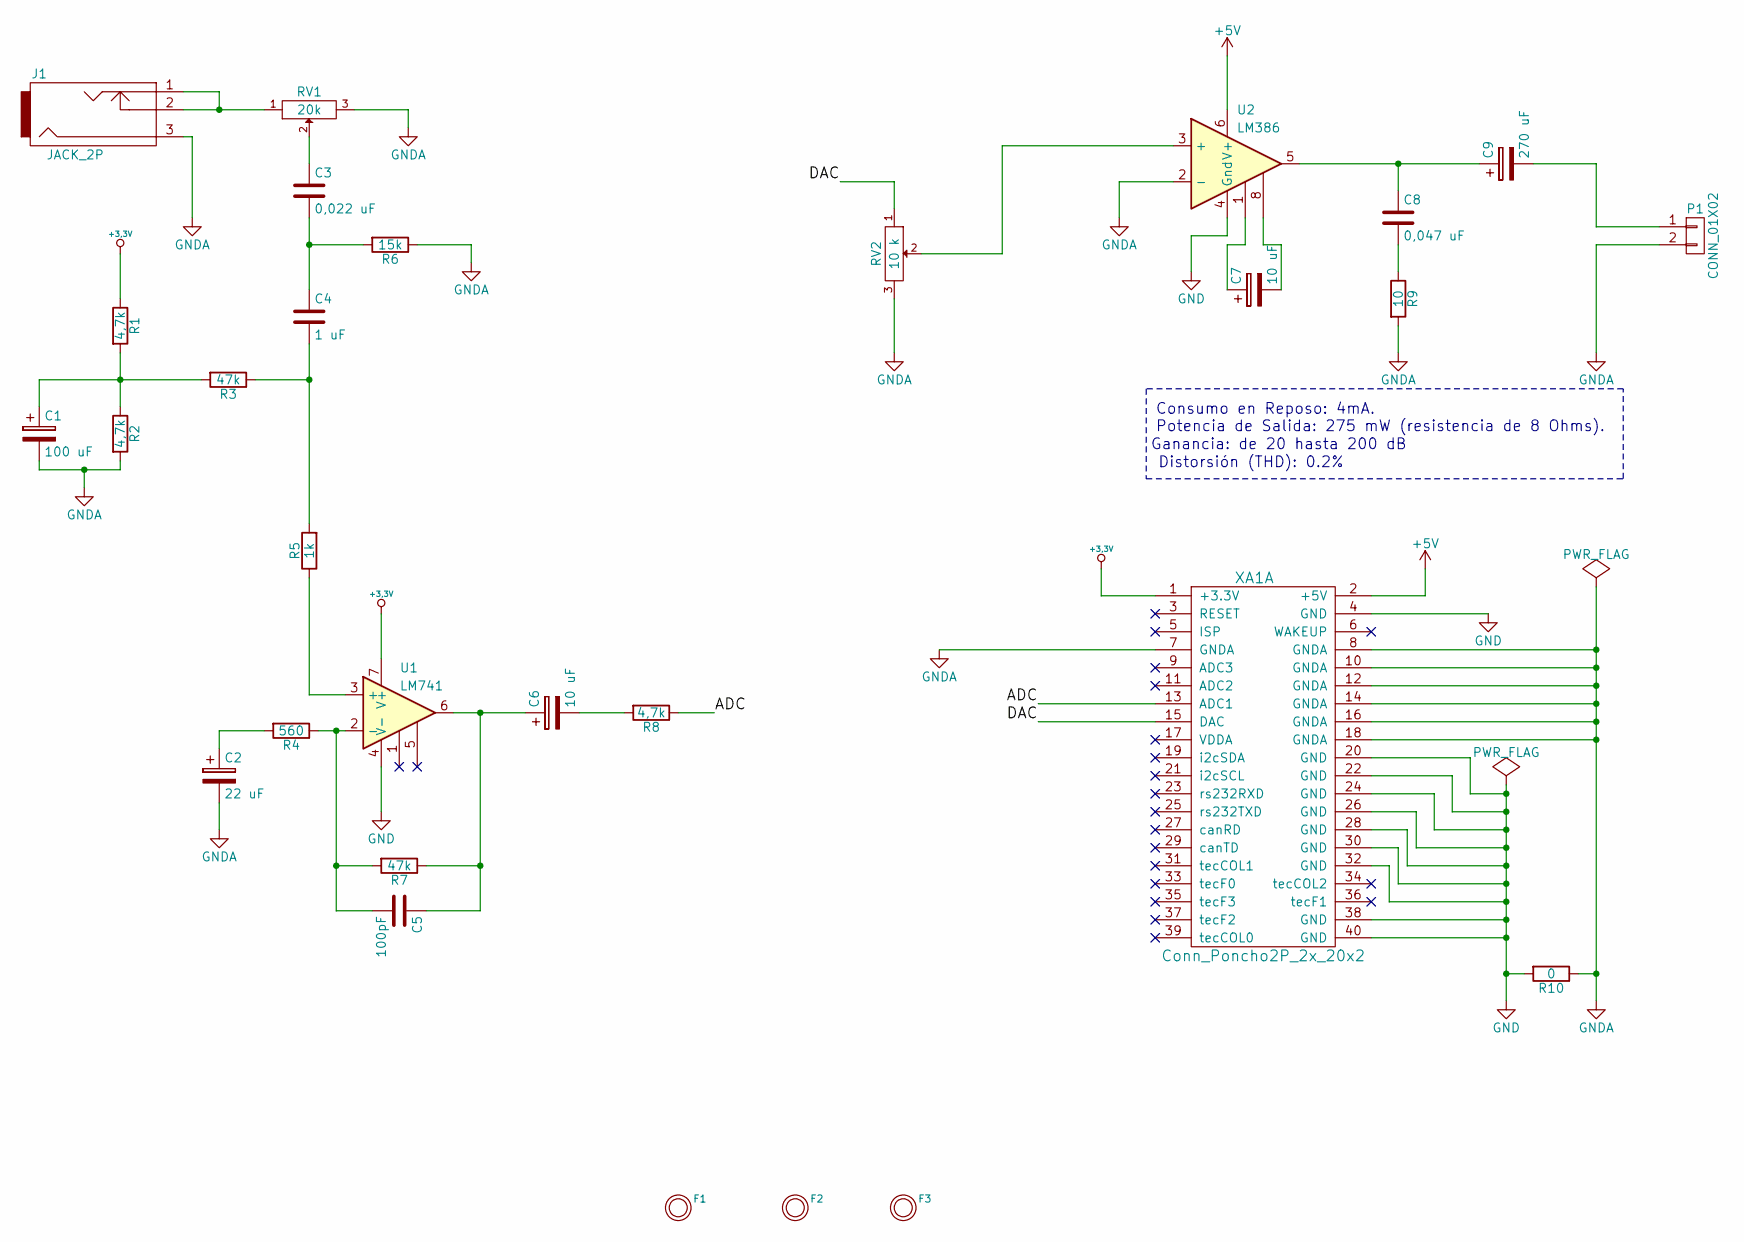
[picture p255: schematic Poncho EDU CIAA Amp Audio.sch]

Parts:
C1: 100 uF; Kemet_ESH106M050AC3AA; Mouser# Value; Digikey# 399-6650-3-ND
C2: 22 uF; Kemet_ESH106M050AC3AA; Mouser# Value; Digikey# 399-6604-ND
C3: 0,022 uF; C_1206_HandSoldering; Mouser# Value; Digikey# 311-1176-2-ND
C4: 1 uF; C_1206_HandSoldering; Mouser# Value; Digikey# 311-1356-2-ND
C5: 100pF; C_1206_HandSoldering; Mouser# Value; Digikey# 399-8127-2-ND
C6, C7: 10 uF; Kemet_ESH106M050AC3AA; Mouser# Value; Digikey# 399-6543-ND
C8: 0,047 uF; C_1206_HandSoldering; Mouser# Value; Digikey# 311-1178-2-ND
C9: 270 uF; C_Kemet_ESY277M063AL3AA; Mouser# Value; Digikey# 399-6124-ND
F1, F2, F3: FIDUCIAL; Fiducial_1mm; Mouser# Value
J1: JACK_2P; Conector_mini_Plug; Mouser# Value; Digikey# CP-3536NG-ND
P1: CONN_01X02; bornier2; Mouser# Value; Digikey# ED2609-ND
R1, R2, R8: 4,7k; R_1206_HandSoldering; Mouser# Value; Digikey# 311-4.70KFRTR-ND
R3, R7: 47k; R_1206_HandSoldering; Mouser# Value; Digikey# 311-47.0KFRTR-ND
R4: 560; R_1206_HandSoldering; Mouser# Value; Digikey# YAG3891CT-ND
R5: 1k; R_1206_HandSoldering; Mouser# Value; Digikey# 311-1.00KFRTR-ND
R6: 15k; R_1206_HandSoldering; Mouser# Value; Digikey# 311-15.0KFRTR-ND
R9: 10; R_1206_HandSoldering; Mouser# Value; Digikey# 311-10.0FRTR-ND
R10: 0; R_1206_HandSoldering; Mouser# Value; Digikey# 311-0.0ERTR-ND
RV1: 20k; POT_20K_0.25W_Bourns_3310C; Mouser# Value; Digikey# 3310C-001-203L-ND
RV2: 10 k; POT_20K_0.25W_Bourns_3310C; Mouser# Value; Digikey# 3310C-001-103L-ND
U1: LM741; LM741_Texas_Instruments; Mouser# Value; Digikey# LM741CNNS/NOPB-ND
U2: LM386; LM741_Texas_Instruments; Mouser# Value; Digikey# 296-44414-5-ND
XA1: Conn_Poncho2P_2x_20x2; Conn_Poncho_Derecha; Mouser# Value; Digikey# 952-1387-ND

Connections:
+3.3V: R1.1, U1.7 (V+), XA1.1 (+3.3V)
+5V: U2.6 (V+), XA1.2 (+5V)
/ADC: R8.1, XA1.13 (ADC1)
/DAC: RV2.1, XA1.15 (DAC)
GND: R10.2, U1.4 (V-), U2.4 (Gnd), XA1.4 (GND), XA1.20 (GND), XA1.22 (GND), XA1.24 (GND), XA1.26 (GND), XA1.28 (GND), XA1.30 (GND), XA1.32 (GND), XA1.38 (GND), XA1.40 (GND)
GNDA: C1.2, C2.2, J1.3, P1.2, R2.2, R6.1, R9.2, R10.1, RV1.3, RV2.3, U2.2 (-), XA1.7 (GNDA), XA1.8 (GNDA), XA1.10 (GNDA), XA1.12 (GNDA), XA1.14 (GNDA), XA1.16 (GNDA), XA1.18 (GNDA)
unnamed: C1.1, R1.2, R2.1, R3.2
unnamed: C2.1, R4.2
unnamed: C3.1, RV1.2
unnamed: C3.2, C4.1, R6.2
unnamed: C4.2, R3.1, R5.2
unnamed: C5.1, C6.1, R7.1, U1.6
unnamed: C5.2, R4.1, R7.2, U1.2 (-)
unnamed: C6.2, R8.2
unnamed: C7.1, U2.1
unnamed: C7.2, U2.8
unnamed: C8.1, C9.1, U2.5
unnamed: C8.2, R9.1
unnamed: C9.2, P1.1
unnamed: J1.1, J1.2, RV1.1
unnamed: R5.1, U1.3 (+)
unnamed: RV2.2, U2.3 (+)

Notes on the sheet:
Consumo en Reposo: 4mA. Potencia de Salida: 275 mW (resistencia de 8 Ohms).
Ganancia: de 20 hasta 200 dB
Distorsión (THD): 0.2%

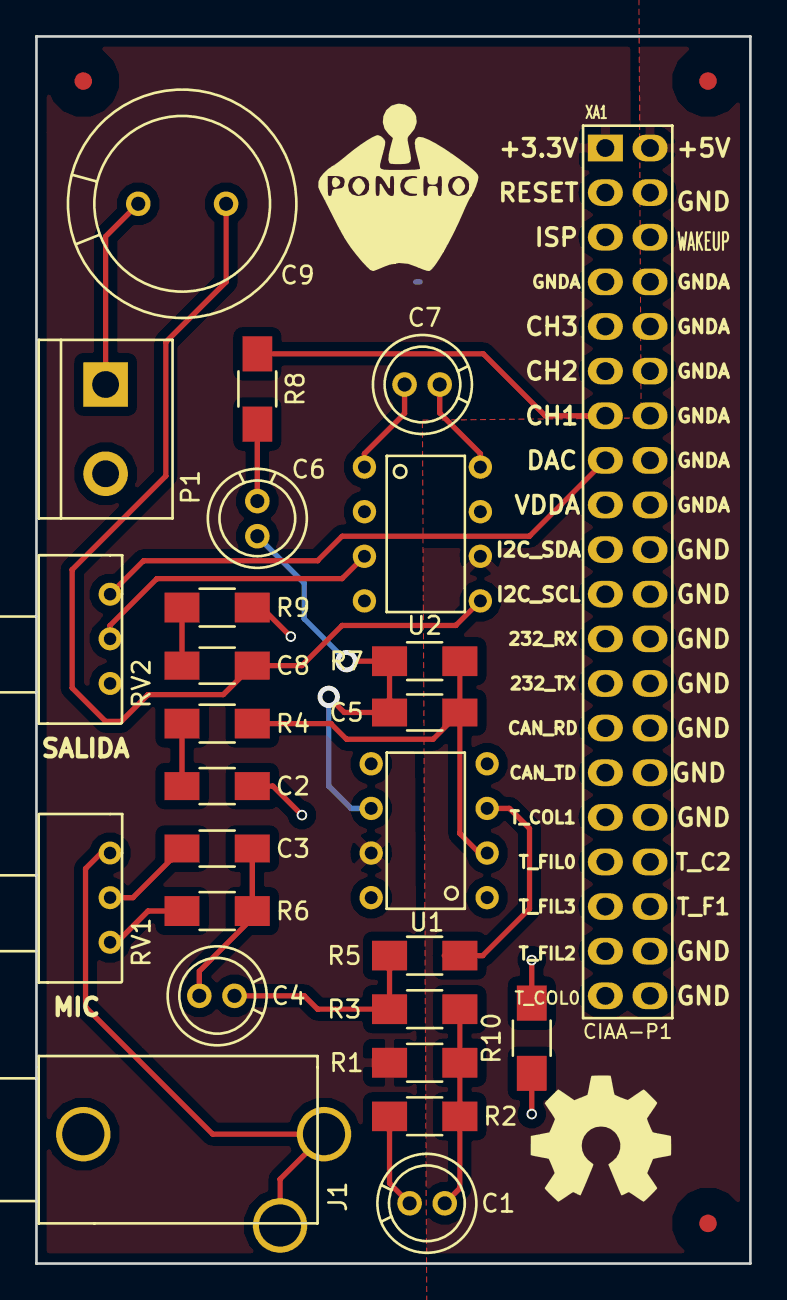
[picture p256: board Poncho EDU CIAA Amp Audio.kicad_pcb from above]

Board: 2 copper layers, 40.6 x 69.8 mm, 30 parts (0 on the bottom side), 22 nets.

Other parts of the board:
G101: Logo_OSHWA
