ciaa/Ponchos/Celda_de_carga/poncho_celda.kicad_pcb

## KiCad design Celda_de_carga/poncho_celda.kicad_pcb (2016-08-03)

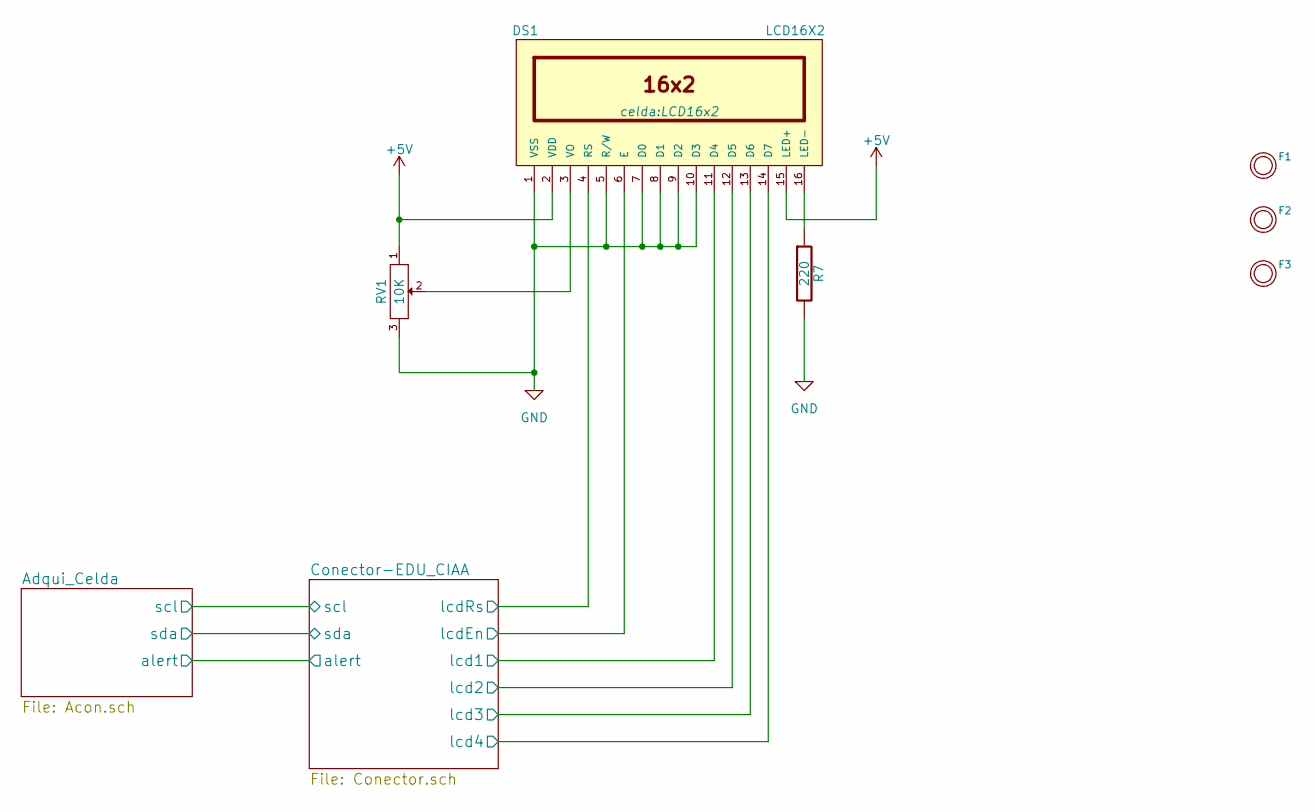
[picture p257: schematic poncho_celda.sch, Diagrama esquematico de poncho Celda.]

Parts:
DS1: LCD16X2; LCD16x2
F1, F2, F3: FIDUCIAL; Fiducial_1mm
R7: 220; R_1206_HandSoldering
RV1: 10K; POT_SMD

Connections:
+5V: DS1.2 (VDD), DS1.15 (LED+), RV1.1; also elsewhere on the board
/Conector-EDU_CIAA/lcd1: DS1.11 (D4); also elsewhere on the board
/Conector-EDU_CIAA/lcd2: DS1.12 (D5); also elsewhere on the board
/Conector-EDU_CIAA/lcd3: DS1.13 (D6); also elsewhere on the board
/Conector-EDU_CIAA/lcd4: DS1.14 (D7); also elsewhere on the board
/Conector-EDU_CIAA/lcdEn: DS1.6 (E); also elsewhere on the board
/Conector-EDU_CIAA/lcdRs: DS1.4 (RS); also elsewhere on the board
GND: DS1.1 (VSS), DS1.5 (R/W), DS1.7 (D0), DS1.8 (D1), DS1.9 (D2), DS1.10 (D3), R7.2, RV1.3; also elsewhere on the board
unnamed: DS1.3 (VO), RV1.2
unnamed: DS1.16 (LED-), R7.1

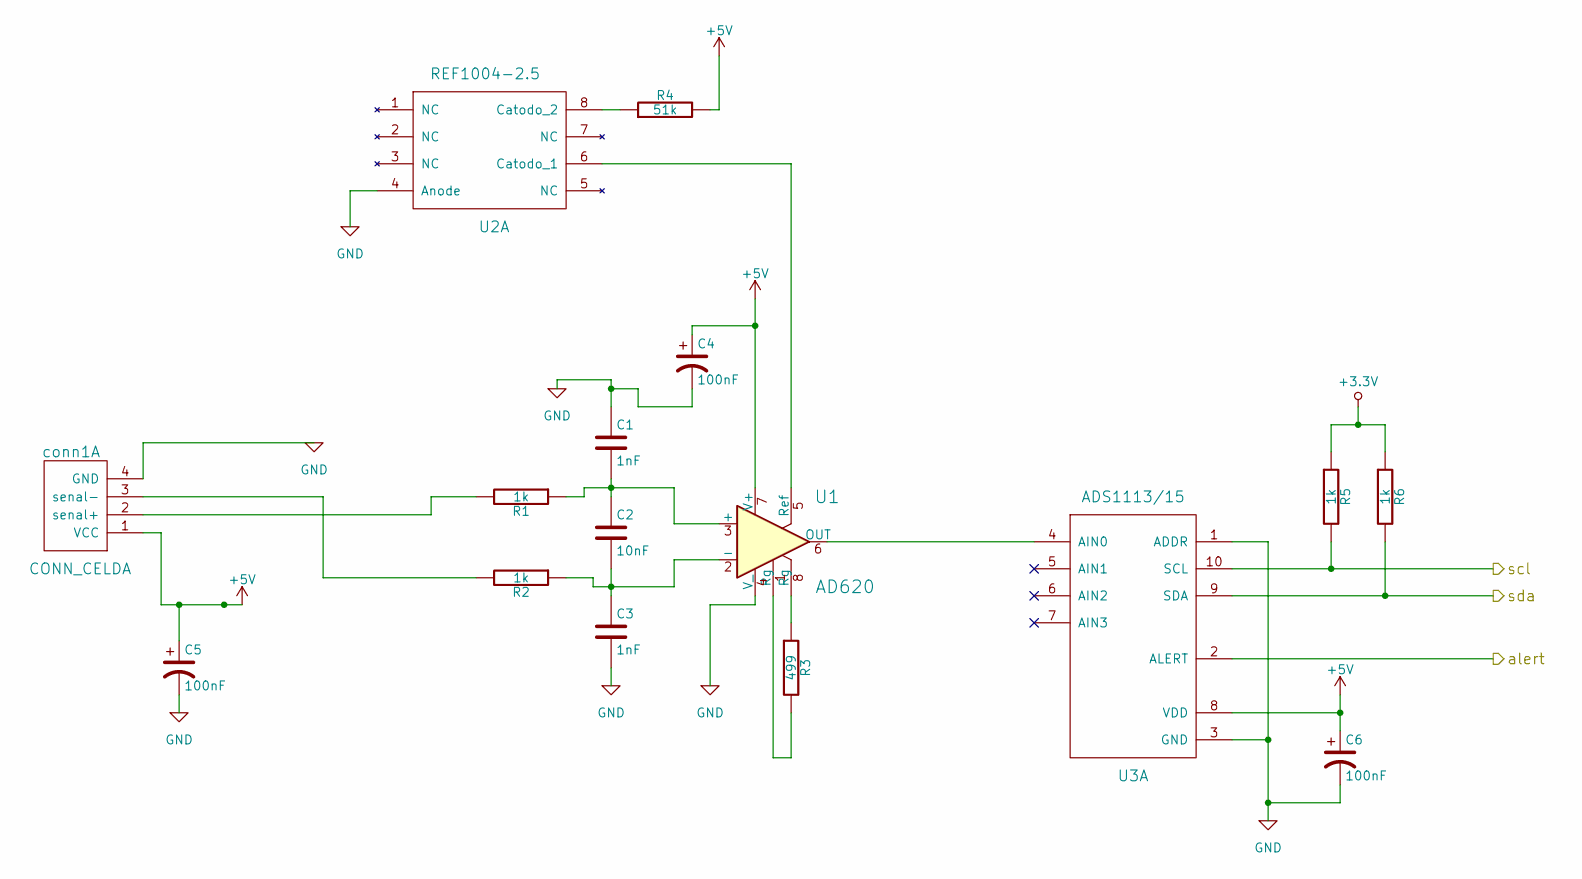
[picture p258: schematic Acon.sch, Diagrama de acondicionamiento de señal.]

Parts:
C1, C3: 1nF; C_0603_HandSoldering
C2: 10nF; C_0603_HandSoldering
C4, C5, C6: 100nF; C_0805_HandSoldering
R1, R2, R5, R6: 1k; R_1206_HandSoldering
R3: 499; R_1206_HandSoldering
R4: 51k; R_1206_HandSoldering
U1: AD620; SOIC-8
U2: REF1004-2.5; SOIC-8
U3: ADS1113/15; TSSOP-10_3x3mm_Pitch0.5mm
conn1: CONN_CELDA; bornier4

Connections:
+3.3V: R5.1, R6.1; also elsewhere on the board
+5V: C4.1, C5.1, C6.1, R4.2, U1.7 (V+), U3.8 (VDD), conn1.1 (VCC); also elsewhere on the board
/Adqui_Celda/alert: U3.2 (ALERT); also elsewhere on the board
/Adqui_Celda/scl: R5.2, U3.10 (SCL); also elsewhere on the board
/Adqui_Celda/sda: R6.2, U3.9 (SDA); also elsewhere on the board
GND: C1.1, C3.2, C4.2, C5.2, C6.2, U1.4 (V_), U2.4 (Anode), U3.1 (ADDR), U3.3 (GND), conn1.4 (GND); also elsewhere on the board
unnamed: C1.2, C2.1, R1.1, U1.3 (+)
unnamed: C2.2, C3.1, R2.1, U1.2 (-)
unnamed: R1.2, conn1.2 (senal+)
unnamed: R2.2, conn1.3 (senal-)
unnamed: R3.1, U1.8 (Rg)
unnamed: R3.2, U1.1 (Rg)
unnamed: R4.1, U2.8 (Catodo_2)
unnamed: U1.5 (Ref), U2.6 (Catodo_1)
unnamed: U1.6 (OUT), U3.4 (AIN0)

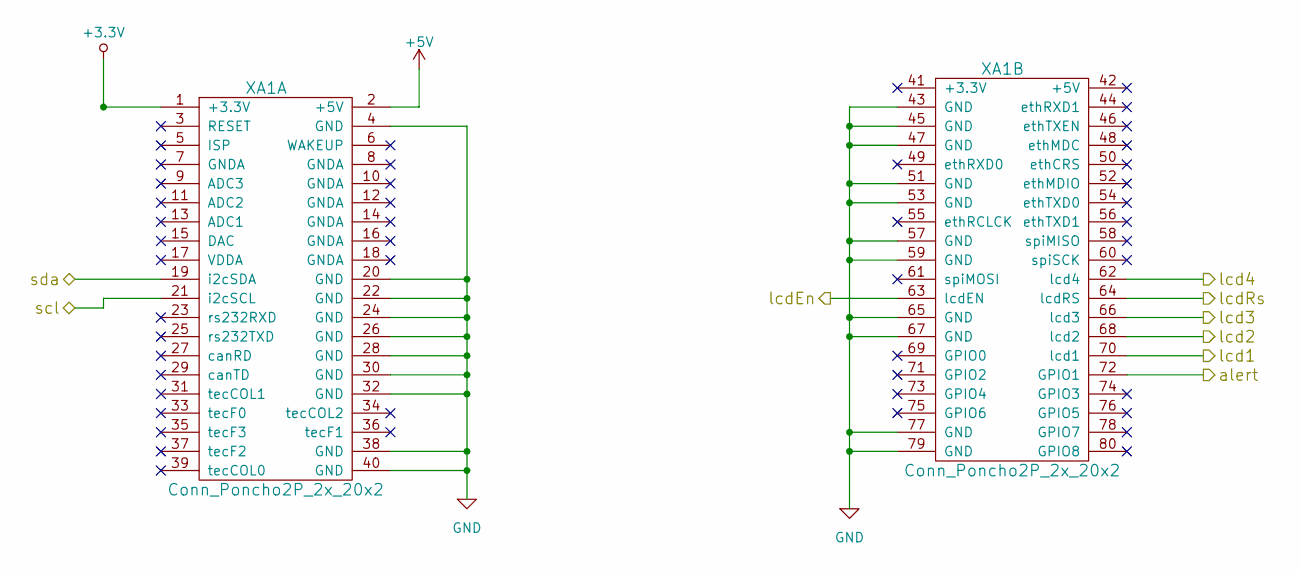
[picture p259: schematic Conector.sch, Diagrama de conectores, para acoplar con la EDU-CIAA.]

Parts:
XA1: Conn_Poncho2P_2x_20x2; Conn_Poncho_SinBorde

Connections:
+3.3V: XA1.1 (+3.3V); also elsewhere on the board
+5V: XA1.2 (+5V); also elsewhere on the board
/Adqui_Celda/alert: XA1.72 (GPIO1); also elsewhere on the board
/Adqui_Celda/scl: XA1.21 (i2cSCL); also elsewhere on the board
/Adqui_Celda/sda: XA1.19 (i2cSDA); also elsewhere on the board
/Conector-EDU_CIAA/lcd1: XA1.70 (lcd1); also elsewhere on the board
/Conector-EDU_CIAA/lcd2: XA1.68 (lcd2); also elsewhere on the board
/Conector-EDU_CIAA/lcd3: XA1.66 (lcd3); also elsewhere on the board
/Conector-EDU_CIAA/lcd4: XA1.62 (lcd4); also elsewhere on the board
/Conector-EDU_CIAA/lcdEn: XA1.63 (lcdEN); also elsewhere on the board
/Conector-EDU_CIAA/lcdRs: XA1.64 (lcdRS); also elsewhere on the board
GND: XA1.4 (GND), XA1.20 (GND), XA1.22 (GND), XA1.24 (GND), XA1.26 (GND), XA1.28 (GND), XA1.30 (GND), XA1.32 (GND), XA1.38 (GND), XA1.40 (GND), XA1.43 (GND), XA1.45 (GND), XA1.47 (GND), XA1.51 (GND), XA1.53 (GND), XA1.57 (GND), XA1.59 (GND), XA1.65 (GND), XA1.67 (GND), XA1.77 (GND), XA1.79 (GND); also elsewhere on the board

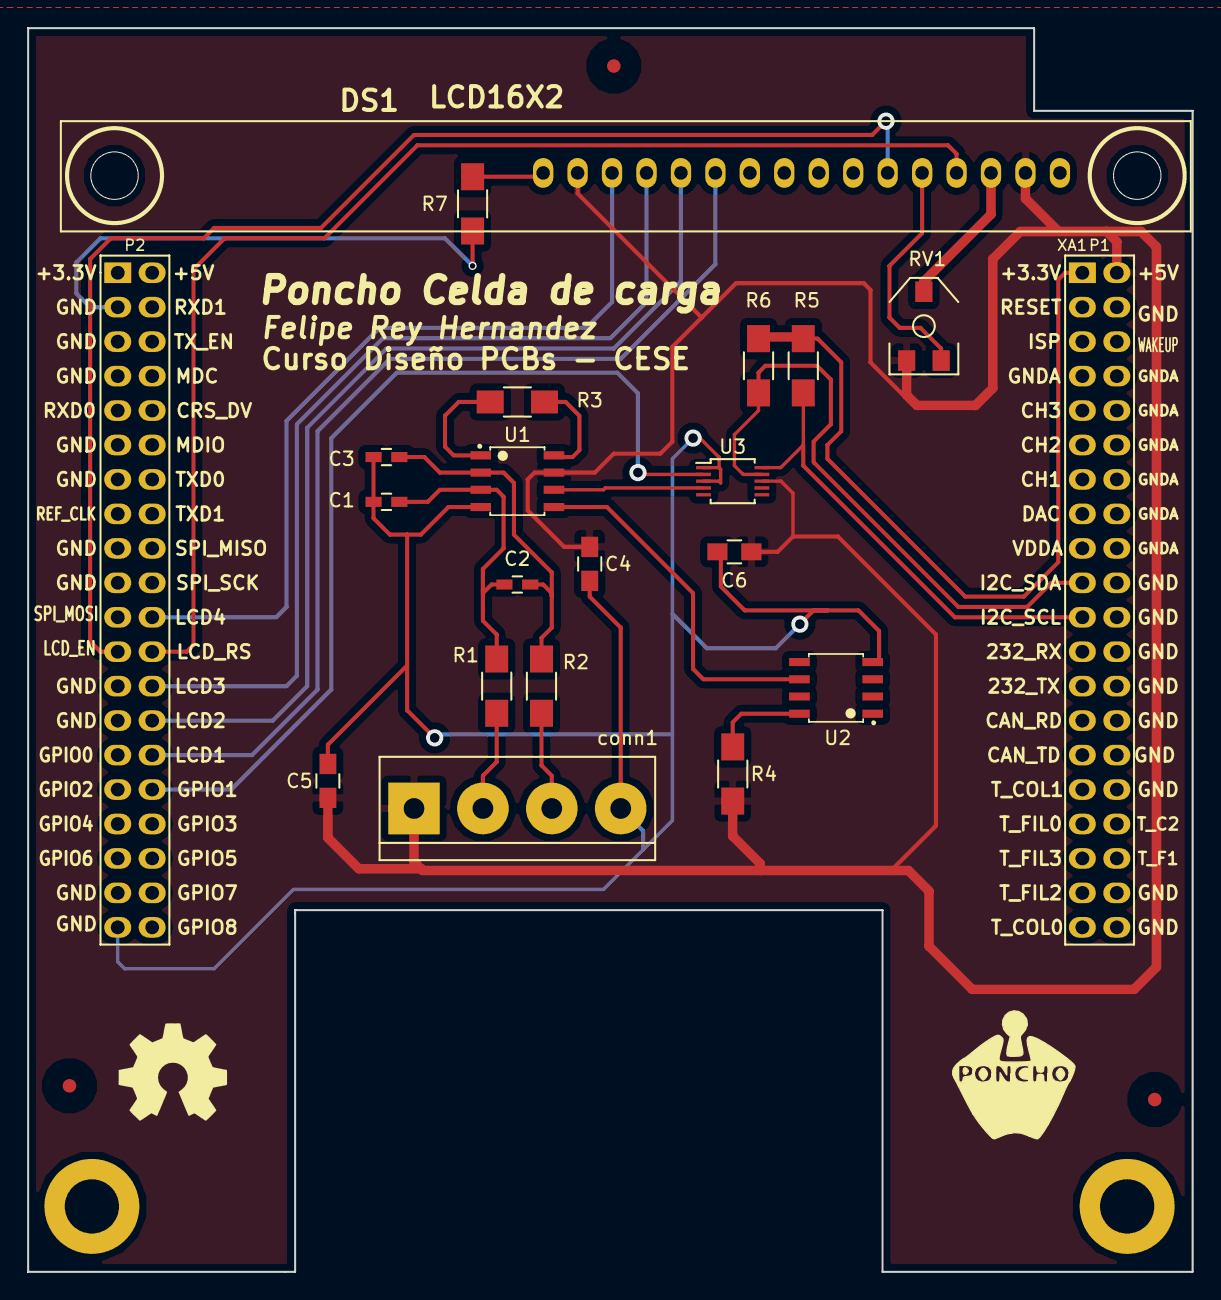
[picture p260: board poncho_celda.kicad_pcb from above]

Board: 2 copper layers, 85.9 x 91.7 mm, 24 parts (0 on the bottom side), 23 nets.

Other parts of the board:
G101: Logo_OSHWA
