ciaa/Ponchos/Simon/tools/kicost-0.1.25/build/lib.linux-i686-2.7/tests/StickIt-QuadDAC.kicad_pcb

## KiCad design Simon/tools/kicost-0.1.25/build/lib.linux-i686-2.7/tests/StickIt-QuadDAC.kicad_pcb (2016-08-03)

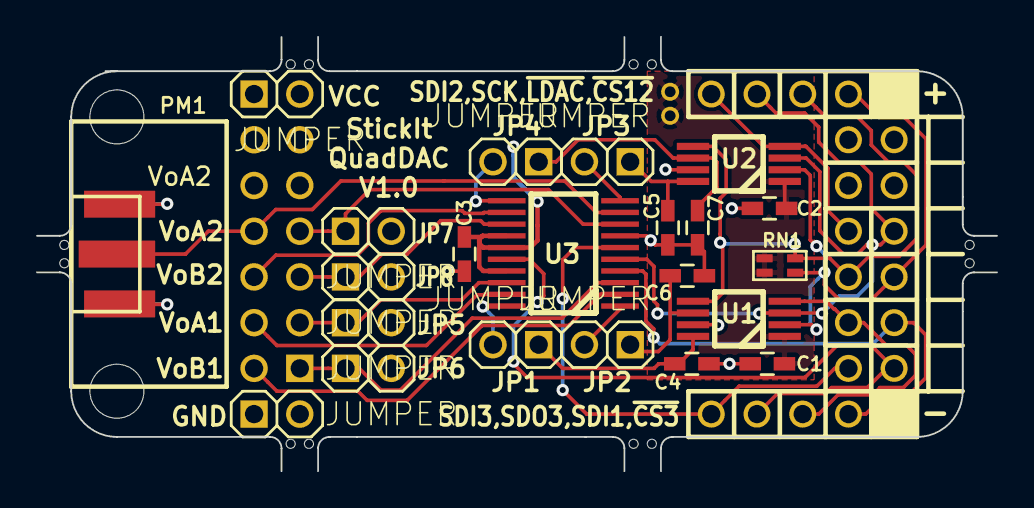
[picture p261: board StickIt-QuadDAC.kicad_pcb from above]

Board: 2 copper layers, 53.3 x 24.1 mm, 31 parts (1 on the bottom side), 26 nets.

Parts:
A: B; oshw_logo_3mm
C1, C2, C3, C4, C5, C6, C7: C; C_0603_HandSoldering
JP1, JP2, JP3, JP4, JP5, JP6, JP7, JP8, JP9, JP10: JUMPER; HDR_1x2
PM1: PMOD_SCKT-12
RN1: 4K7; CTS_742C043
Ref**: Val**; Array_Tab_2hole
Ref**#2, Ref**#3, Ref**#4, Ref**#5, Ref**#6: Val**; Array_Tab_2hole
STK1: STICKIT2_HDR
U1, U2: MCP48X2; xess-MICROCHIP-8_MSOP
U3: MCP43X1; xess-MICROCHIP-20_TSSOP
VoA2: COAX_CONN; SMA_EDGE_AMP_132322

Connections:
/VoutA1: PM1.8, U3.19
/VoutA2: PM1.10, U3.9, VoA2.CNTR
/VoutB1: PM1.7, U3.2
/VoutB2: PM1.9, U3.12
GND: C1.2, C2.2, C3.2, C4.2, C5.2, C6.2, C7.2, JP5.2, JP6.2, JP7.2, JP8.2, JP9.1, JP9.2, PM1.5, PM1.11, STK1.GND, U1.7, U2.7, U3.7, VoA2.SHLD
unnamed: C4.1, JP1.1, U1.8
unnamed: C5.1, JP3.1, U2.8
unnamed: C6.1, JP2.1, U1.6
unnamed: C7.1, JP4.1, U2.6
unnamed: JP1.2, U3.20
unnamed: JP2.2, U3.1
unnamed: JP3.2, U3.10
unnamed: JP4.2, U3.11
unnamed: JP5.1, PM1.2, U3.18
unnamed: JP6.1, PM1.1, U3.3
unnamed: JP7.1, PM1.4, U3.8
unnamed: JP8.1, PM1.3, U3.13
SCK: STK1.D7, U1.3, U2.3, U3.5
SDI1: STK1.D2, U1.4
SDI2: STK1.D6, U2.4
SDI3: STK1.D0, U3.6
SDO3: STK1.D1, U3.16
VCC: C1.1, C2.1, C3.1, JP10.1, JP10.2, PM1.6, PM1.12, RN1.1, RN1.2, STK1.VCC, U1.1, U2.1, U3.14, U3.15, U3.17
~CS3: STK1.D3, U3.4
~CS12: RN1.3, STK1.D5, U1.2, U2.2
~LDAC: RN1.4, STK1.D4, U1.5, U2.5
