ciaa/Ponchos/Simon/simonShield.kicad_pcb

## KiCad design Simon/simonShield.kicad_pcb (2016-08-03)

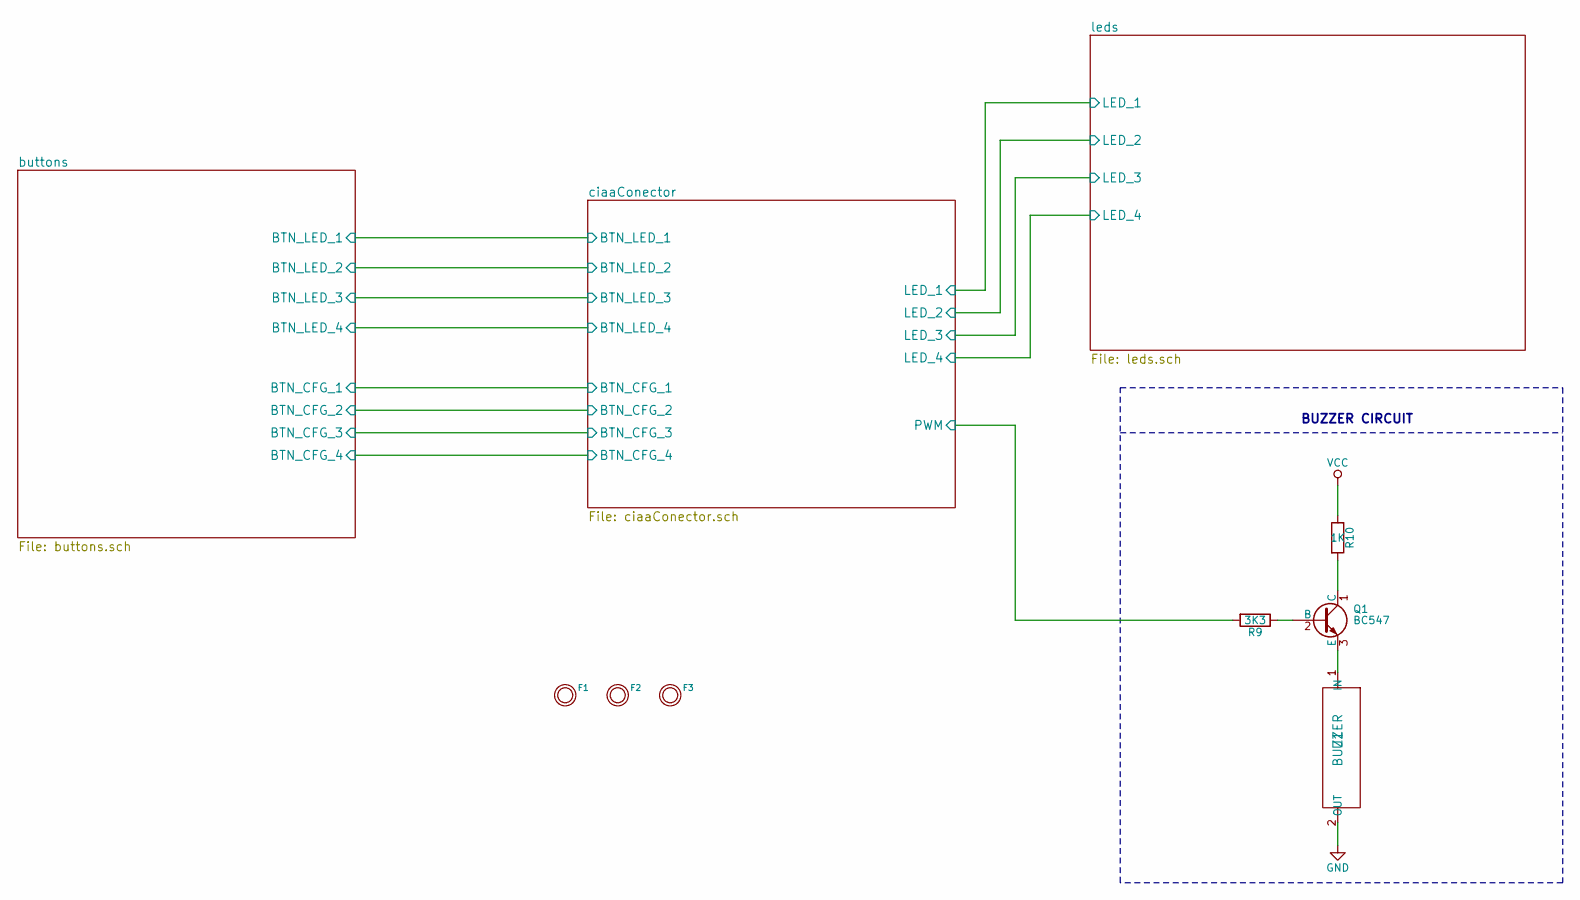
[picture p262: schematic simonShield.sch, Poncho Simon EDU-CIAA]

Parts:
F1, F2, F3: FIDUCIAL; Fiducial_1mm
Q1: BC547; TO-92_Molded_Narrow; Digikey# BC33725TACT-ND
R9: 3K3; Resistor_Horizontal_RM7mm; Digikey# 680EBK-ND
R10: 1K; Resistor_Horizontal_RM7mm; Digikey# 680EBK-ND
U1: BUZZER; MagneticBuzzer_ProSignal_ABT-410-RC; Digikey# 445-2525-1-ND

Connections:
/ciaaConector/PWM: R9.2; also elsewhere on the board
GND: U1.2 (OUT); also elsewhere on the board
unnamed: Q1.1 (C), R10.2
unnamed: Q1.2 (B), R9.1
unnamed: Q1.3 (E), U1.1 (IN)
VCC: R10.1; also elsewhere on the board

Notes on the sheet:
BUZZER CIRCUIT

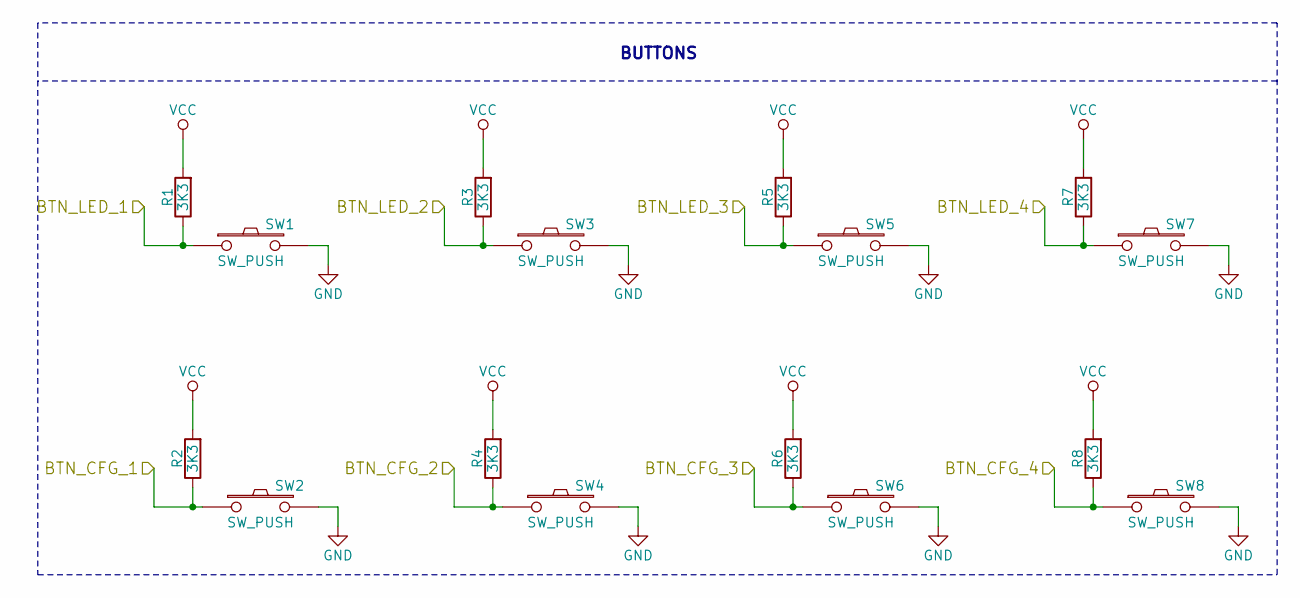
[picture p263: schematic buttons.sch, Poncho Simon EDU-CIAA]

Parts:
R1, R2, R3, R4, R5, R6, R7, R8: 3K3; Resistor_Horizontal_RM7mm; Digikey# 680EBK-ND
SW1, SW2, SW3, SW4, SW5, SW6, SW7, SW8: SW_PUSH; SW_PUSH_SMALL; Digikey# 450-1804-ND

Connections:
/buttons/BTN_CFG_1: R2.1, SW2.1; also elsewhere on the board
/buttons/BTN_CFG_2: R4.1, SW4.1; also elsewhere on the board
/buttons/BTN_CFG_3: R6.1, SW6.1; also elsewhere on the board
/buttons/BTN_CFG_4: R8.1, SW8.1; also elsewhere on the board
/buttons/BTN_LED_1: R1.1, SW1.1; also elsewhere on the board
/buttons/BTN_LED_2: R3.1, SW3.1; also elsewhere on the board
/buttons/BTN_LED_3: R5.1, SW5.1; also elsewhere on the board
/buttons/BTN_LED_4: R7.1, SW7.1; also elsewhere on the board
GND: SW1.2, SW2.2, SW3.2, SW4.2, SW5.2, SW6.2, SW7.2, SW8.2; also elsewhere on the board
VCC: R1.2, R2.2, R3.2, R4.2, R5.2, R6.2, R7.2, R8.2; also elsewhere on the board

Notes on the sheet:
BUTTONS

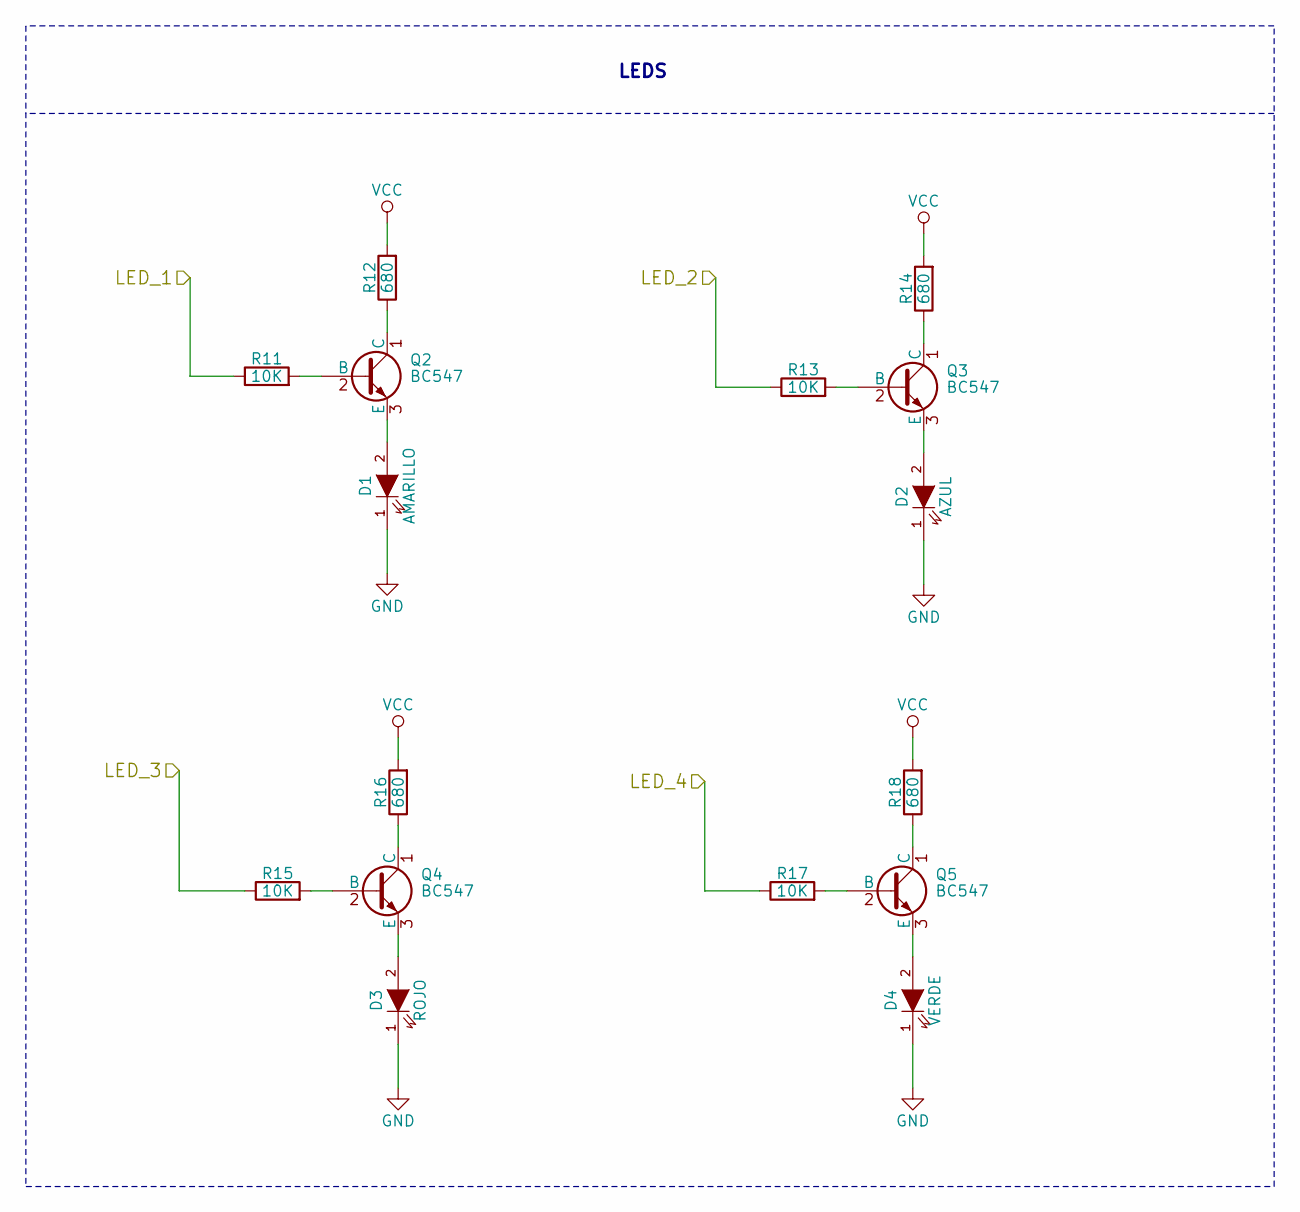
[picture p264: schematic leds.sch, Poncho Simon EDU-CIAA]

Parts:
D1: AMARILLO; LED-5MM; Digikey# 1497-1031-ND
D2: AZUL; LED-5MM; Digikey# 1497-1031-ND
D3: ROJO; LED-5MM; Digikey# 1497-1031-ND
D4: VERDE; LED-5MM; Digikey# 1497-1031-ND
Q2, Q3, Q4, Q5: BC547; TO-92_Molded_Narrow; Digikey# BC33725TACT-ND
R11, R13, R15, R17: 10K; Resistor_Horizontal_RM7mm; Digikey# 680EBK-ND
R12, R14, R16, R18: 680; Resistor_Horizontal_RM7mm; Digikey# 680EBK-ND

Connections:
/ciaaConector/LED_1: R11.1; also elsewhere on the board
/ciaaConector/LED_2: R13.1; also elsewhere on the board
/ciaaConector/LED_3: R15.1; also elsewhere on the board
/ciaaConector/LED_4: R17.1; also elsewhere on the board
GND: D1.1 (K), D2.1 (K), D3.1 (K), D4.1 (K); also elsewhere on the board
unnamed: D1.2 (A), Q2.3 (E)
unnamed: D2.2 (A), Q3.3 (E)
unnamed: D3.2 (A), Q4.3 (E)
unnamed: D4.2 (A), Q5.3 (E)
unnamed: Q2.1 (C), R12.1
unnamed: Q2.2 (B), R11.2
unnamed: Q3.1 (C), R14.1
unnamed: Q3.2 (B), R13.2
unnamed: Q4.1 (C), R16.1
unnamed: Q4.2 (B), R15.2
unnamed: Q5.1 (C), R18.1
unnamed: Q5.2 (B), R17.2
VCC: R12.2, R14.2, R16.2, R18.2; also elsewhere on the board

Notes on the sheet:
LEDS
