ciaa/Ponchos/Simon/simonShield.kicad_pcb

## KiCad design Simon/simonShield.kicad_pcb (continued)

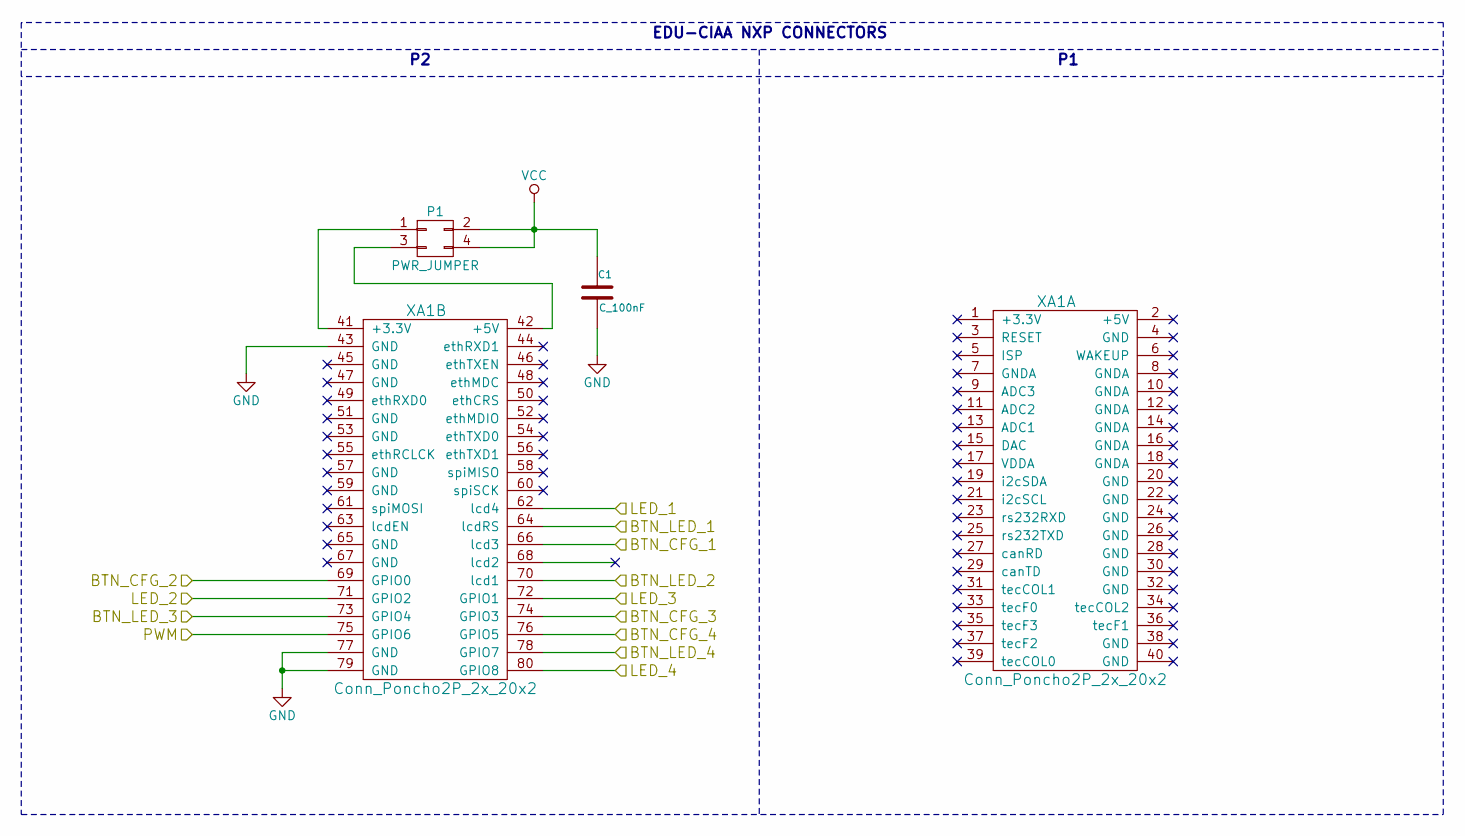
[picture p265: schematic ciaaConector.sch, Poncho Simon EDU-CIAA]

Parts:
C1: C_100nF; C_Disc_D3_P2.5; Digikey# BC1160TR­ND
P1: PWR_JUMPER; Pin_Header_Straight_2x02; Digikey# 952-2121-ND
XA1: Conn_Poncho2P_2x_20x2; Conn_Poncho_SinBorde; Digikey# 952-2121-ND

Connections:
/buttons/BTN_CFG_1: XA1.66 (lcd3); also elsewhere on the board
/buttons/BTN_CFG_2: XA1.69 (GPIO0); also elsewhere on the board
/buttons/BTN_CFG_3: XA1.74 (GPIO3); also elsewhere on the board
/buttons/BTN_CFG_4: XA1.76 (GPIO5); also elsewhere on the board
/buttons/BTN_LED_1: XA1.64 (lcdRS); also elsewhere on the board
/buttons/BTN_LED_2: XA1.70 (lcd1); also elsewhere on the board
/buttons/BTN_LED_3: XA1.73 (GPIO4); also elsewhere on the board
/buttons/BTN_LED_4: XA1.78 (GPIO7); also elsewhere on the board
/ciaaConector/LED_1: XA1.62 (lcd4); also elsewhere on the board
/ciaaConector/LED_2: XA1.71 (GPIO2); also elsewhere on the board
/ciaaConector/LED_3: XA1.72 (GPIO1); also elsewhere on the board
/ciaaConector/LED_4: XA1.80 (GPIO8); also elsewhere on the board
/ciaaConector/PWM: XA1.75 (GPIO6); also elsewhere on the board
GND: C1.2, XA1.43 (GND), XA1.77 (GND), XA1.79 (GND); also elsewhere on the board
unnamed: P1.1, XA1.41 (+3.3V)
unnamed: P1.3, XA1.42 (+5V)
VCC: C1.1, P1.2, P1.4; also elsewhere on the board

Notes on the sheet:
EDU-CIAA NXP CONNECTORS

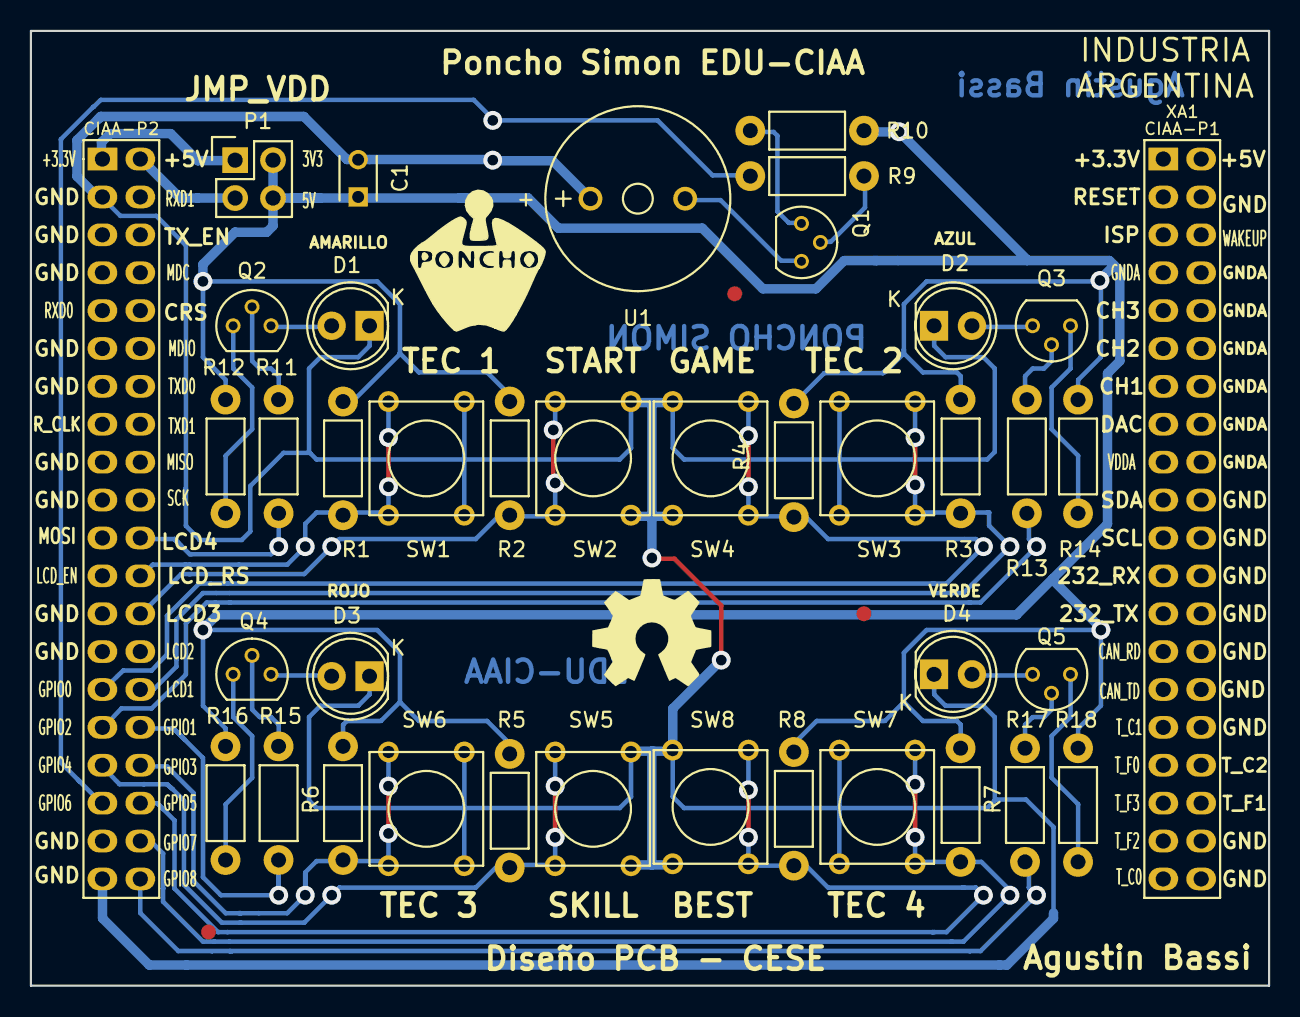
[picture p266: board simonShield.kicad_pcb from above]

Board: 2 copper layers, 83.0 x 64.0 mm, 43 parts (0 on the bottom side), 32 nets.

Other parts of the board:
G101: Logo_OSHWA
