ciaa/Ponchos/modelos/Poncho_Izquierdo/Poncho_Izquierdo.kicad_pcb

## KiCad design modelos/Poncho_Izquierdo/Poncho_Izquierdo.kicad_pcb (2015-10-07)

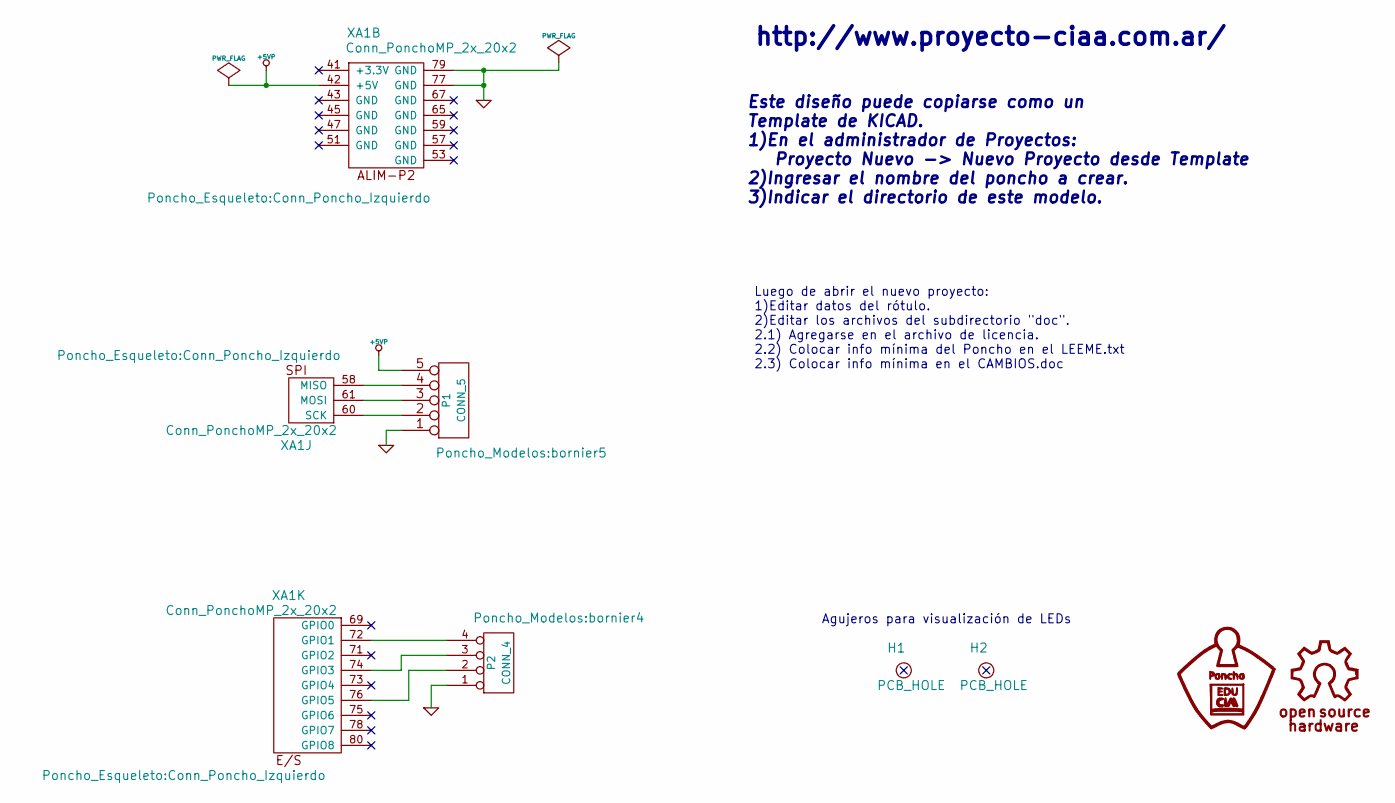
[picture p267: schematic Poncho_Izquierdo.sch, Poncho Izquierdo - Modelo - Ejemplo - Template]

Parts:
H1, H2: PCB_HOLE; Led_Hole
P1: CONN_5; bornier5
P2: CONN_4; bornier4
XA1: Conn_PonchoMP_2x_20x2; Conn_Poncho_Izquierdo

Connections:
+5VP: P1.5, XA1.42 (+5V)
GND: P1.1, P2.1, XA1.77 (GND), XA1.79 (GND)
unnamed: P1.2, XA1.60 (SCK)
unnamed: P1.3, XA1.61 (MOSI)
unnamed: P1.4, XA1.58 (MISO)
unnamed: P2.2, XA1.76 (GPIO5)
unnamed: P2.3, XA1.74 (GPIO3)
unnamed: P2.4, XA1.72 (GPIO1)

Notes on the sheet:
Este diseño puede copiarse como un Template de KICAD. 1)En el administrador de Proyectos: Proyecto Nuevo -> Nuevo Proyecto desde Template 2)Ingresar el nombre del poncho a crear. 3)Indicar el directorio de este modelo.
http://www.proyecto-ciaa.com.ar/
Luego de abrir el nuevo proyecto: 1)Editar datos del rótulo. 2)Editar los archivos del subdirectorio "doc". 2.1) Agregarse en el archivo de licencia. 2.2) Colocar info mínima del Poncho en el LEEME.txt 2.3) Colocar info mínima en el CAMBIOS.doc
Agujeros para visualización de LEDs

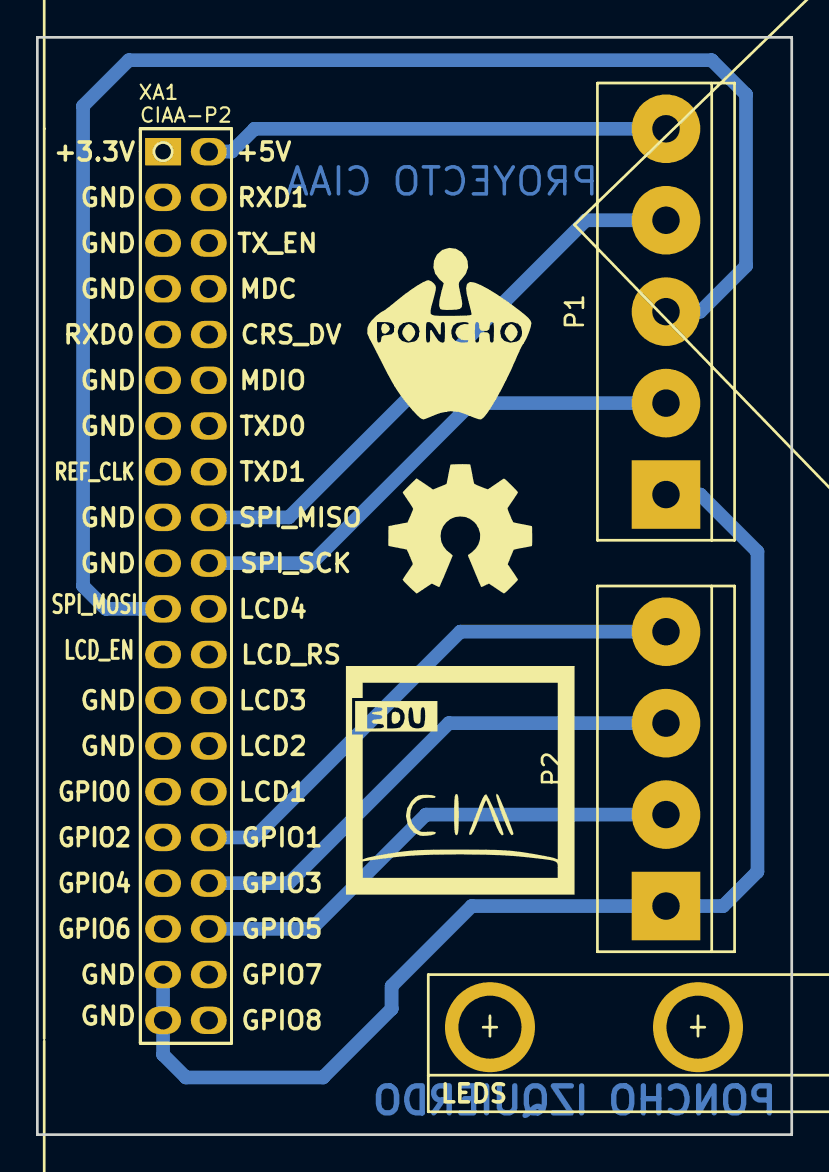
[picture p268: board Poncho_Izquierdo.kicad_pcb from above]

Board: 2 copper layers, 41.9 x 61.0 mm, 7 parts (0 on the bottom side), 8 nets.

Other parts of the board:
G101: Logo_OSHWA
MP1: Plantilla_EDU-CIAA
