ciaa/Ponchos/modelos/Poncho_Mediano/Poncho_Mediano.kicad_pcb

## KiCad design modelos/Poncho_Mediano/Poncho_Mediano.kicad_pcb (2015-10-07)

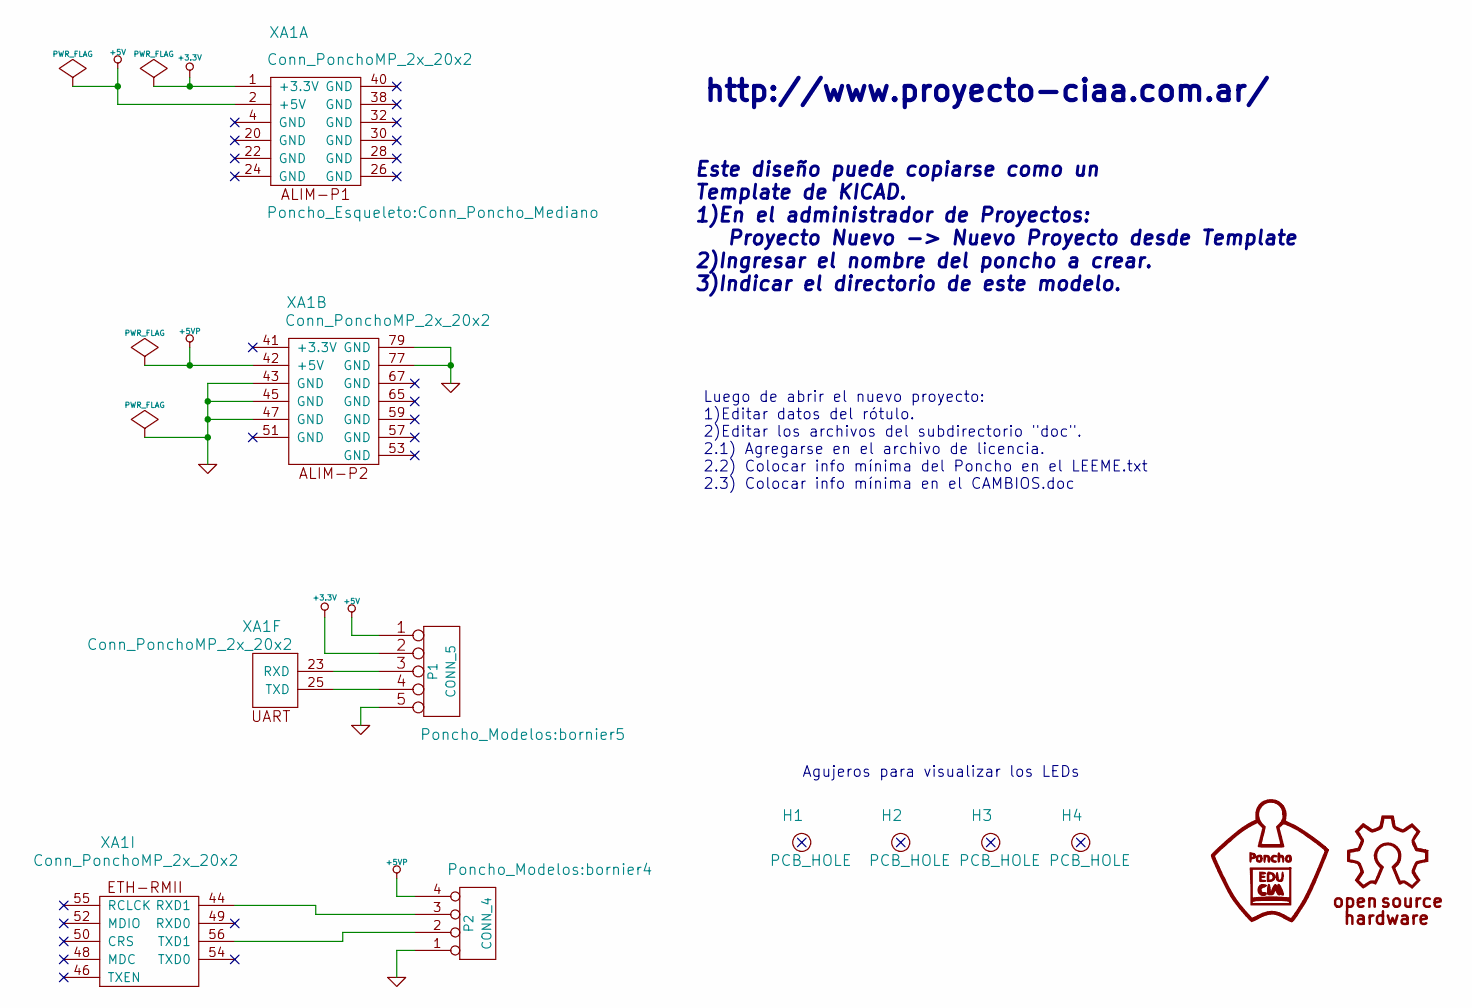
[picture p269: schematic Poncho_Mediano.sch, Poncho Mediano - Modelo - Ejemplo - Template]

Parts:
H1, H2, H3, H4: PCB_HOLE; Led_Hole
P1: CONN_5; bornier5
P2: CONN_4; bornier4
XA1: Conn_PonchoMP_2x_20x2; Conn_Poncho_Mediano

Connections:
+3.3V: P1.2, XA1.1 (+3.3V)
+5V: P1.1, XA1.2 (+5V)
+5VP: P2.4, XA1.42 (+5V)
GND: P1.5, P2.1, XA1.43 (GND), XA1.45 (GND), XA1.47 (GND), XA1.77 (GND), XA1.79 (GND)
unnamed: P1.3, XA1.23 (RXD)
unnamed: P1.4, XA1.25 (TXD)
unnamed: P2.2, XA1.56 (TXD1)
unnamed: P2.3, XA1.44 (RXD1)

Notes on the sheet:
Este diseño puede copiarse como un Template de KICAD. 1)En el administrador de Proyectos: Proyecto Nuevo -> Nuevo Proyecto desde Template 2)Ingresar el nombre del poncho a crear. 3)Indicar el directorio de este modelo.
http://www.proyecto-ciaa.com.ar/
Luego de abrir el nuevo proyecto: 1)Editar datos del rótulo. 2)Editar los archivos del subdirectorio "doc". 2.1) Agregarse en el archivo de licencia. 2.2) Colocar info mínima del Poncho en el LEEME.txt 2.3) Colocar info mínima en el CAMBIOS.doc
Agujeros para visualizar los LEDs

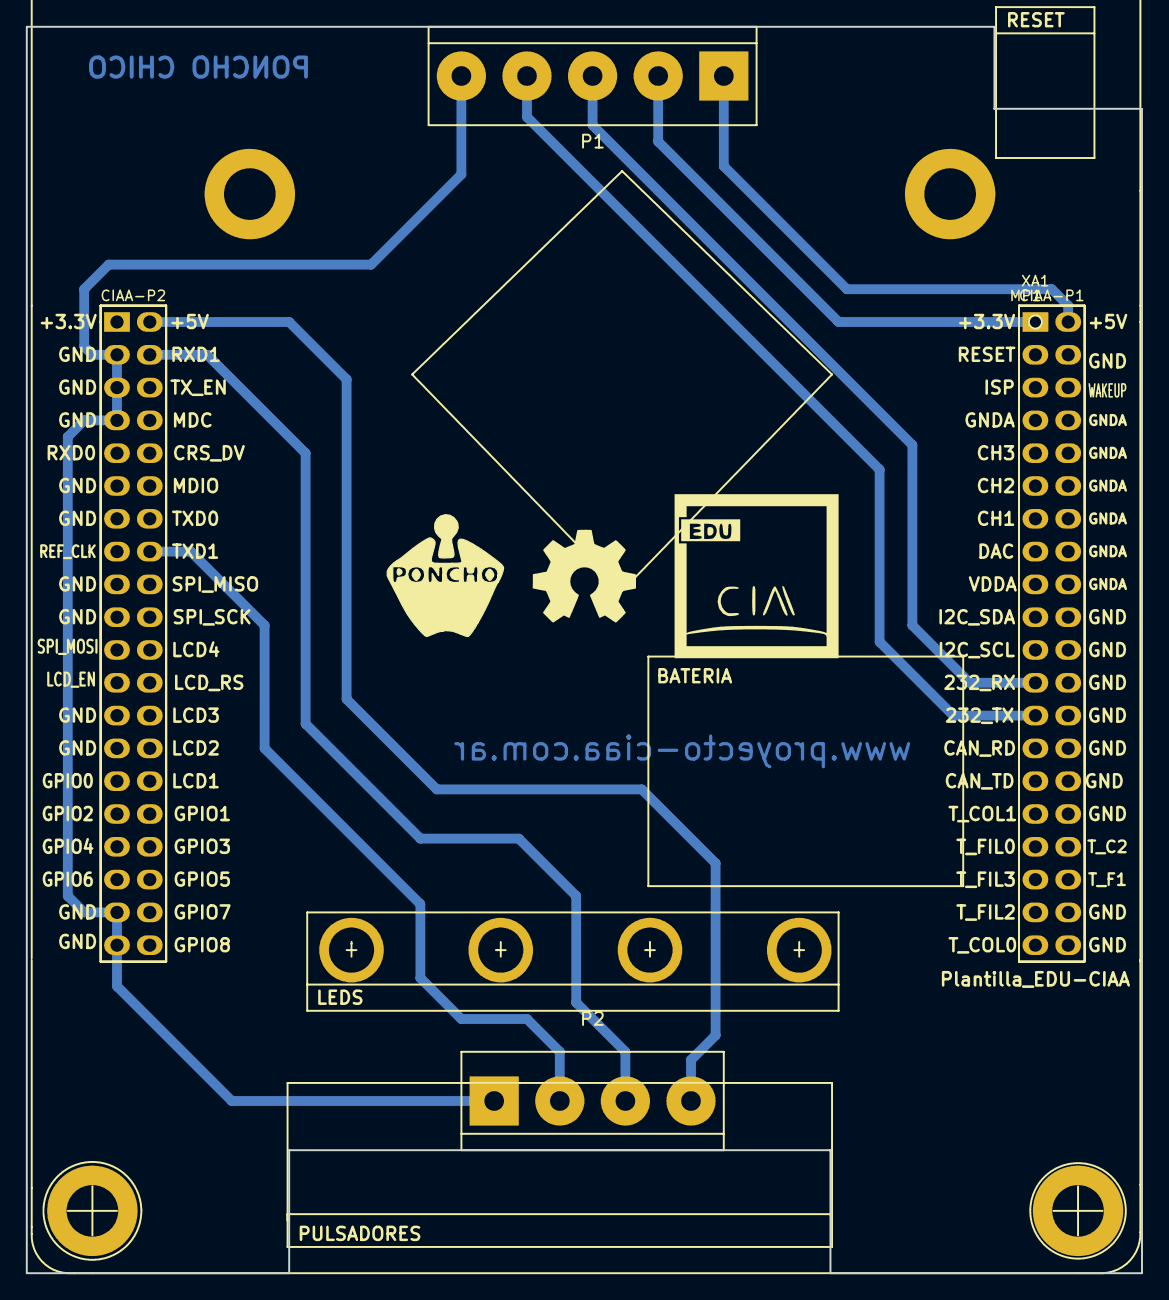
[picture p270: board Poncho_Mediano.kicad_pcb from above]

Board: 2 copper layers, 86.4 x 96.5 mm, 9 parts (0 on the bottom side), 8 nets.

Other parts of the board:
G101: Logo_OSHWA
MP1: Plantilla_EDU-CIAA
