ciaa/Ponchos/modelos/Poncho_Grande/poncho_grande.kicad_pcb

## KiCad design modelos/Poncho_Grande/poncho_grande.kicad_pcb (2015-10-07, an earlier design)

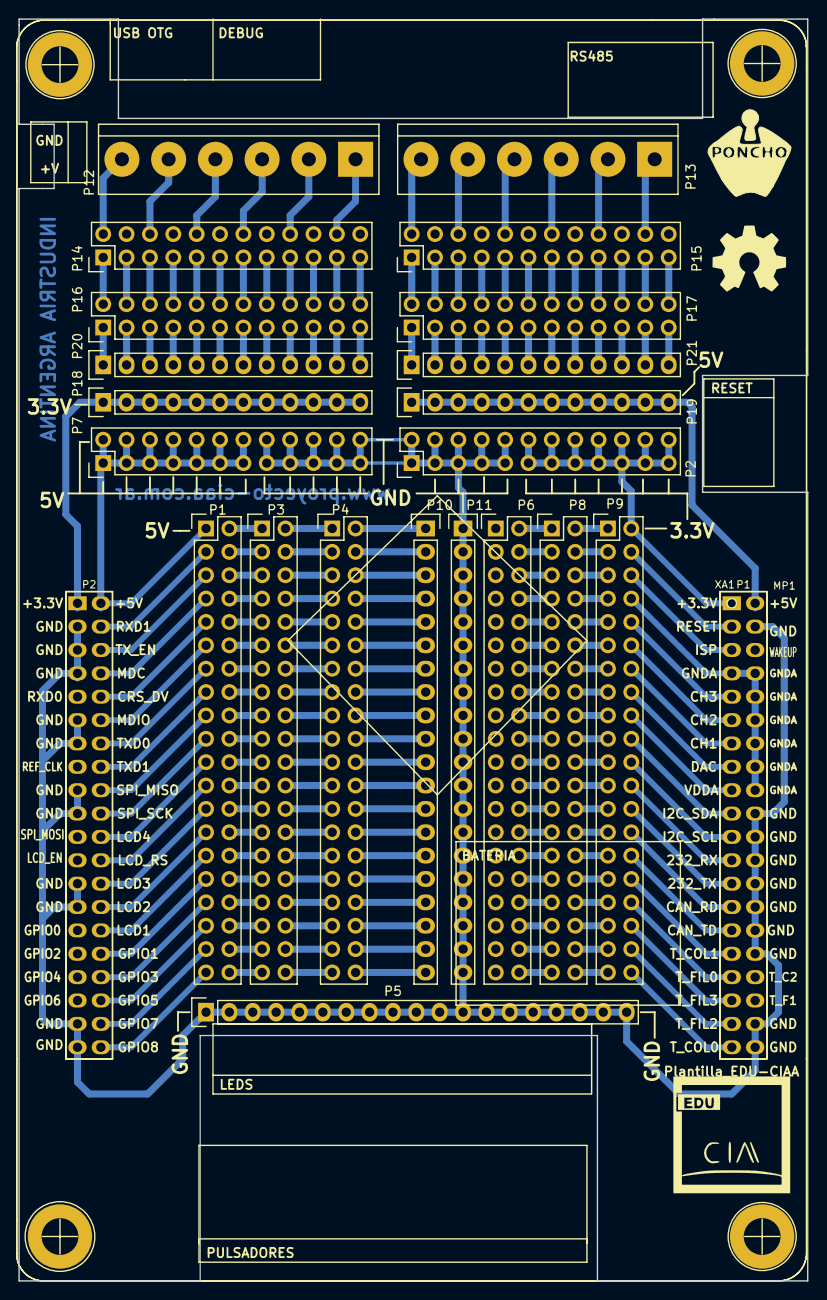
[picture p271: board modelos/Poncho_Grande/poncho_grande.kicad_pcb from above]

Board: 2 copper layers, 85.7 x 137.2 mm, 24 parts (0 on the bottom side), 203 nets.

Parts:
G101: Logo_OSHWA
MP1: Plantilla_EDU-CIAA
P1, P3, P4, P6, P8, P9: CONN_02X20; Pin_Header_Straight_2x20
P2, P7: CONN_01X20; Pin_Header_Straight_2x12
P5: CONN_01X19; Pin_Header_Straight_1x19
P10, P11: CONN_01X20; Pin_Header_Straight_1x20
P12, P13: CONN_01X06; bornier6
P14, P15, P16, P17: CONN_02X12; Pin_Header_Straight_2x12
P18, P19, P20, P21: CONN_01X12; Pin_Header_Straight_1x12
XA1: poncho_grande

Connections:
+3.3V: P2.11, P2.12, P2.13, P2.14, P2.15, P2.16, P2.17, P2.18, P2.19, P2.20, P2.21, P2.22, P2.23, P2.24, P9.2, XA1.1
+3.3VADC: P9.18, XA1.17
+3.3VP: P18.1, P18.2, P18.3, P18.4, P18.5, P18.6, P18.7, P18.8, P18.9, P18.10, P18.11, P18.12, XA1.41
+5V: P19.1, P19.2, P19.3, P19.4, P19.5, P19.6, P19.7, P19.8, P19.9, P19.10, P19.11, P19.12, XA1.2
+5VP: P1.1, P7.1, P7.2, P7.3, P7.4, P7.5, P7.6, P7.7, P7.8, P7.9, P7.10, P7.11, P7.12, P7.13, P7.14, XA1.42
/Circuito Principal/ADC1: P9.14, XA1.13
/Circuito Principal/ADC2: P9.12, XA1.11
/Circuito Principal/ADC3: P9.10, XA1.9
/Circuito Principal/COL0: P9.40, XA1.39
/Circuito Principal/COL1: P9.32, XA1.31
/Circuito Principal/CRS: P1.9, XA1.50
/Circuito Principal/DAC: P9.16, XA1.15
/Circuito Principal/F0: P9.34, XA1.33
/Circuito Principal/F2: P9.38, XA1.37
/Circuito Principal/F3: P9.36, XA1.35
/Circuito Principal/GPIO1: P1.31, XA1.72
/Circuito Principal/GPIO3: P1.33, XA1.74
/Circuito Principal/GPIO5: P1.35, XA1.76
/Circuito Principal/GPIO7: P1.37, XA1.78
/Circuito Principal/GPIO8: P1.39, XA1.80
/Circuito Principal/ISP: P9.6, XA1.5
/Circuito Principal/LCD1: P1.29, XA1.70
/Circuito Principal/LCD2: P1.27, XA1.68
/Circuito Principal/LCD3: P1.25, XA1.66
/Circuito Principal/LCD4: P1.21, XA1.62
/Circuito Principal/MDC: P1.7, XA1.48
/Circuito Principal/MDIO: P1.11, XA1.52
/Circuito Principal/MISO: P1.17, XA1.58
/Circuito Principal/RD: P9.28, XA1.27
/Circuito Principal/RESET: P9.4, XA1.3
/Circuito Principal/RS: P1.23, XA1.64
/Circuito Principal/RXD: P9.24, XA1.23
/Circuito Principal/RXD1: P1.3, XA1.44
/Circuito Principal/SCL: P9.22, XA1.21
/Circuito Principal/SDA: P9.20, XA1.19
/Circuito Principal/TD: P9.30, XA1.29
/Circuito Principal/TXD: P9.26, XA1.25
/Circuito Principal/TXD0: P1.13, XA1.54
/Circuito Principal/TXD1: P1.15, XA1.56
/Circuito Principal/TXEN: P1.5, XA1.46
/Circuito Principal/spiCCK: P1.19, XA1.60
GND: P2.1, P2.2, P2.3, P2.4, P2.5, P2.6, P2.7, P2.8, P2.9, P2.10, P5.1, P5.2, P5.3, P5.4, P5.5, P5.6, P5.7, P5.8, P5.9, P5.10, P5.11, P5.12, P5.13, P5.14, P5.15, P5.16, P5.17, P5.18, P5.19, P7.15, P7.16, P7.17, P7.18, P7.19, P7.20, P7.21, P7.22, P7.23, P7.24, P11.1, P11.2, P11.3, P11.4, P11.5, P11.6, P11.7, P11.8, P11.9, P11.10, P11.11, P11.12, P11.13, P11.14, P11.15, P11.16, P11.17, P11.18, P11.19, P11.20, XA1.4, XA1.20, XA1.22, XA1.24, XA1.26, XA1.28, XA1.30, XA1.32, XA1.38, XA1.40, XA1.43, XA1.45, XA1.47, XA1.51, XA1.53, XA1.57, XA1.59, XA1.65, XA1.67, XA1.77, XA1.79
GNDA: P9.8, XA1.7, XA1.8, XA1.10, XA1.12, XA1.14, XA1.16, XA1.18
unnamed: P1.2, P3.1
unnamed: P1.4, P3.3
unnamed: P1.6, P3.5
unnamed: P1.8, P3.7
unnamed: P1.10, P3.9
unnamed: P1.12, P3.11
unnamed: P1.14, P3.13
unnamed: P1.16, P3.15
unnamed: P1.18, P3.17
unnamed: P1.20, P3.19
unnamed: P1.22, P3.21
unnamed: P1.24, P3.23
unnamed: P1.26, P3.25
unnamed: P1.28, P3.27
unnamed: P1.30, P3.29
unnamed: P1.32, P3.31
unnamed: P1.34, P3.33
unnamed: P1.36, P3.35
unnamed: P1.38, P3.37
unnamed: P1.40, P3.39
unnamed: P3.2, P4.1
unnamed: P3.4, P4.3
unnamed: P3.6, P4.5
unnamed: P3.8, P4.7
unnamed: P3.10, P4.9
unnamed: P3.12, P4.11
unnamed: P3.14, P4.13
unnamed: P3.16, P4.15
unnamed: P3.18, P4.17
unnamed: P3.20, P4.19
unnamed: P3.22, P4.21
unnamed: P3.24, P4.23
unnamed: P3.26, P4.25
unnamed: P3.28, P4.27
unnamed: P3.30, P4.29
unnamed: P3.32, P4.31
unnamed: P3.34, P4.33
unnamed: P3.36, P4.35
unnamed: P3.38, P4.37
unnamed: P3.40, P4.39
unnamed: P6.2, P8.1
unnamed: P6.4, P8.3
unnamed: P6.6, P8.5
unnamed: P6.8, P8.7
unnamed: P6.10, P8.9
unnamed: P6.12, P8.11
unnamed: P6.14, P8.13
unnamed: P6.16, P8.15
unnamed: P6.18, P8.17
unnamed: P6.20, P8.19
unnamed: P6.22, P8.21
unnamed: P6.24, P8.23
unnamed: P6.26, P8.25
unnamed: P6.28, P8.27
unnamed: P6.30, P8.29
unnamed: P6.32, P8.31
unnamed: P6.34, P8.33
unnamed: P6.36, P8.35
unnamed: P6.38, P8.37
unnamed: P6.40, P8.39
unnamed: P8.2, P9.1
unnamed: P8.4, P9.3
unnamed: P8.6, P9.5
unnamed: P8.8, P9.7
unnamed: P8.10, P9.9
unnamed: P8.12, P9.11
unnamed: P8.14, P9.13
unnamed: P8.16, P9.15
unnamed: P8.18, P9.17
unnamed: P8.20, P9.19
unnamed: P8.22, P9.21
unnamed: P8.24, P9.23
unnamed: P8.26, P9.25
unnamed: P8.28, P9.27
unnamed: P8.30, P9.29
unnamed: P8.32, P9.31
unnamed: P8.34, P9.33
unnamed: P8.36, P9.35
unnamed: P8.38, P9.37
unnamed: P8.40, P9.39
unnamed: P4.2, P10.1
unnamed: P4.4, P10.2
unnamed: P4.6, P10.3
unnamed: P4.8, P10.4
unnamed: P4.10, P10.5
unnamed: P4.12, P10.6
unnamed: P4.14, P10.7
unnamed: P4.16, P10.8
unnamed: P4.18, P10.9
unnamed: P4.20, P10.10
unnamed: P4.22, P10.11
unnamed: P4.24, P10.12
unnamed: P4.26, P10.13
unnamed: P4.28, P10.14
unnamed: P4.30, P10.15
unnamed: P4.32, P10.16
unnamed: P4.34, P10.17
unnamed: P4.36, P10.18
unnamed: P4.38, P10.19
unnamed: P4.40, P10.20
unnamed: P12.1, P14.22
unnamed: P12.2, P14.18
unnamed: P12.3, P14.14
unnamed: P12.4, P14.10
unnamed: P12.5, P14.6
unnamed: P12.6, P14.2
unnamed: P13.1, P15.22
unnamed: P13.2, P15.18
unnamed: P13.3, P15.14
unnamed: P13.4, P15.10
unnamed: P13.5, P15.6
unnamed: P13.6, P15.2
unnamed: P14.1, P16.2
unnamed: P14.3, P16.4
unnamed: P14.5, P16.6
unnamed: P14.7, P16.8
unnamed: P14.9, P16.10
unnamed: P14.11, P16.12
unnamed: P14.13, P16.14
unnamed: P14.15, P16.16
unnamed: P14.17, P16.18
unnamed: P14.19, P16.20
unnamed: P14.21, P16.22
unnamed: P14.23, P16.24
unnamed: P15.1, P17.2
unnamed: P15.3, P17.4
unnamed: P15.5, P17.6
unnamed: P15.7, P17.8
unnamed: P15.9, P17.10
unnamed: P15.11, P17.12
unnamed: P15.13, P17.14
unnamed: P15.15, P17.16
unnamed: P15.17, P17.18
unnamed: P15.19, P17.20
unnamed: P15.21, P17.22
unnamed: P15.23, P17.24
unnamed: P16.1, P20.1
unnamed: P16.3, P20.2
unnamed: P16.5, P20.3
unnamed: P16.7, P20.4
unnamed: P16.9, P20.5
unnamed: P16.11, P20.6
unnamed: P16.13, P20.7
unnamed: P16.15, P20.8
unnamed: P16.17, P20.9
unnamed: P16.19, P20.10
unnamed: P16.21, P20.11
unnamed: P16.23, P20.12
unnamed: P17.1, P21.1
unnamed: P17.3, P21.2
unnamed: P17.5, P21.3
unnamed: P17.7, P21.4
unnamed: P17.9, P21.5
unnamed: P17.11, P21.6
unnamed: P17.13, P21.7
unnamed: P17.15, P21.8
unnamed: P17.17, P21.9
unnamed: P17.19, P21.10
unnamed: P17.21, P21.11
unnamed: P17.23, P21.12
