ciaa/Ponchos/modelos/Poncho_Derecho/Poncho_Derecho.kicad_pcb

## KiCad design modelos/Poncho_Derecho/Poncho_Derecho.kicad_pcb (2015-10-06)

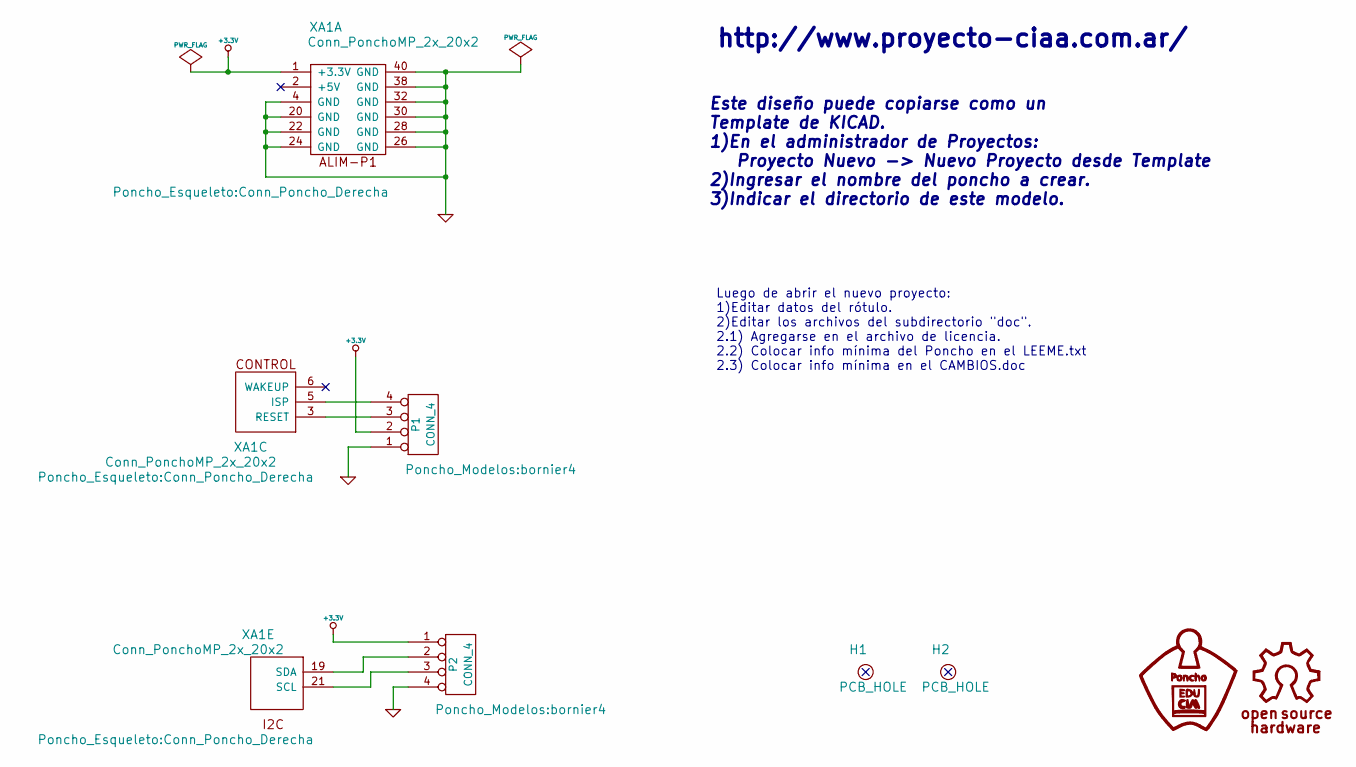
[picture p272: schematic Poncho_Derecho.sch, Poncho Derecho- Modelo - Ejemplo - Template]

Parts:
H1, H2: PCB_HOLE; Led_Hole
P1, P2: CONN_4; bornier4
XA1: Conn_PonchoMP_2x_20x2; Conn_Poncho_Derecha

Connections:
+3.3V: P1.2, P2.1, XA1.1 (+3.3V)
GND: P1.1, P2.4, XA1.4 (GND), XA1.20 (GND), XA1.22 (GND), XA1.24 (GND), XA1.26 (GND), XA1.28 (GND), XA1.30 (GND), XA1.32 (GND), XA1.38 (GND), XA1.40 (GND)
unnamed: P1.3, XA1.3 (RESET)
unnamed: P1.4, XA1.5 (ISP)
unnamed: P2.2, XA1.19 (SDA)
unnamed: P2.3, XA1.21 (SCL)

Notes on the sheet:
Este diseño puede copiarse como un Template de KICAD. 1)En el administrador de Proyectos: Proyecto Nuevo -> Nuevo Proyecto desde Template 2)Ingresar el nombre del poncho a crear. 3)Indicar el directorio de este modelo.
http://www.proyecto-ciaa.com.ar/
Luego de abrir el nuevo proyecto: 1)Editar datos del rótulo. 2)Editar los archivos del subdirectorio "doc". 2.1) Agregarse en el archivo de licencia. 2.2) Colocar info mínima del Poncho en el LEEME.txt 2.3) Colocar info mínima en el CAMBIOS.doc

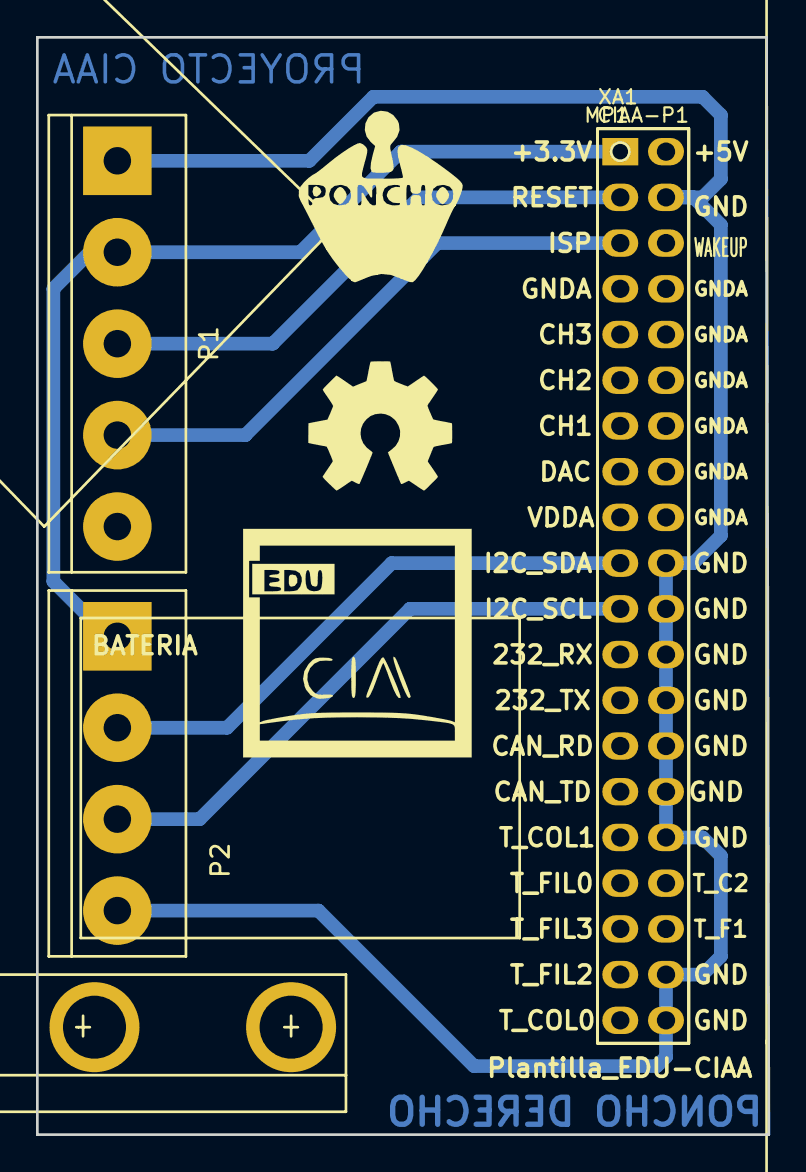
[picture p273: board Poncho_Derecho.kicad_pcb from above]

Board: 2 copper layers, 40.6 x 61.0 mm, 7 parts (0 on the bottom side), 6 nets.

Other parts of the board:
G101: Logo_OSHWA
MP1: Plantilla_EDU-CIAA
